lolz0r/Williams-WPC-Power-Driver-Board-A-12697-3/variants/jlcpcb/docs/PCBWAY_REPLY_DRAFT.md

# Draft reply — not sent

Use this for the revision and BOM actually supplied to PCBWay; JLC-2 is a separate electronics-sourcing revision.

> Understood. Once the PCB and all components arrive, please trial-fit the heatsinks, rectifiers, mounting screws and nearby components before completing assembly. Please check screw passage and engagement, component-to-heatsink clearance, and clearance beneath the board. If anything does not fit freely, please send photos and measurements and hold the affected assembly for review before modifying parts or substituting hardware. We can provide the STEP model and assembly drawings to support the check; final fit still needs to be verified on the actual parts.
