lolz0r/Williams-WPC-Power-Driver-Board-A-12697-3/variants/jlcpcb/docs/RELEASE_STATUS.md

# JLC-2 status

Use the [JLC-2 README](../README.md), [verification report](VERIFICATION.md) and [machine-readable readiness](../output/release-candidate/READINESS.json).

The JLC-2 CAD and manufacturing consistency checks pass, and the flasher-clamp correction is implemented. **Hold an assembled prototype order:** the expanded analog review has unresolved regulator voltage/backfeed findings and lamp-matrix convergence. The [latest addendum](CONTINUED_ANALOG_REVIEW.md) establishes convergence of the selected coil replay, with a separate energy-balance check, and records the unbuilt input-isolation candidate. The [previous report](PRESPIN_VERIFICATION.md) retains earlier results and failures. This is an engineering review candidate; software verification is not an unconditional pass.

Physical cabinet/harness clearance, loaded thermal/fault tests, procurement and fabricator/assembly DFM remain open. Fabrication-file consistency does not establish electrical readiness.

Documents under `baseline/` describe the parent revision and are not current release evidence.
