lolz0r/Williams-WPC-Power-Driver-Board-A-12697-3/.scratch/thermal/crop_br3.png

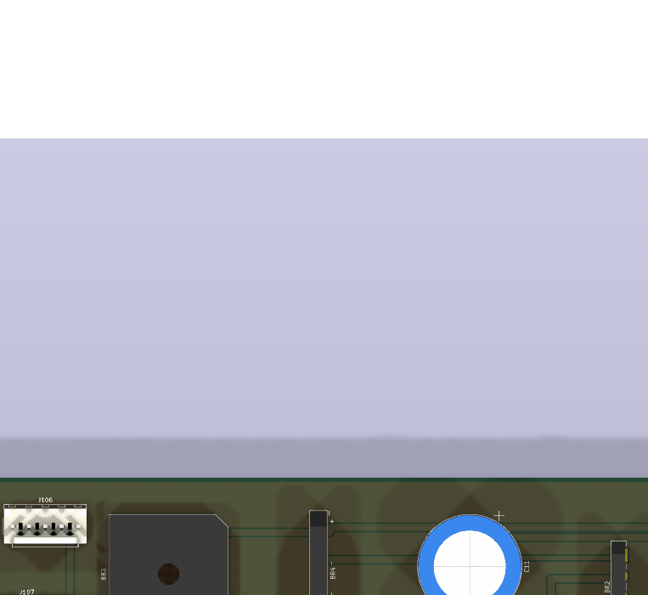
.scratch/thermal/crop_br3.png
