lolz0r/Williams-WPC-Power-Driver-Board-A-12697-3/.scratch/thermal/crop_q18.png

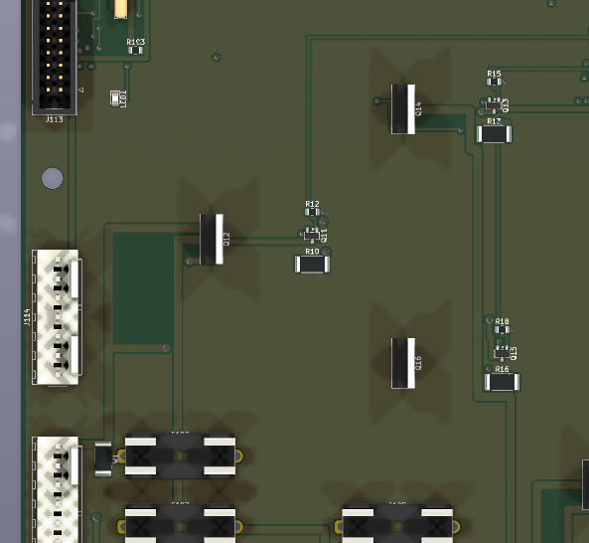
.scratch/thermal/crop_q18.png
