lolz0r/Williams-WPC-Power-Driver-Board-A-12697-3/.scratch/thermal/d_5840.png

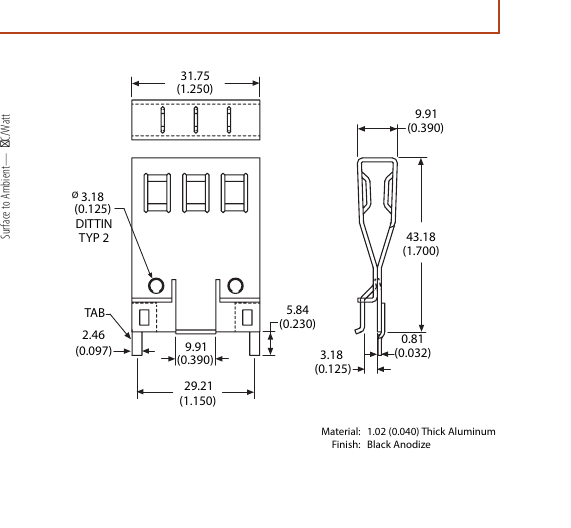
.scratch/thermal/d_5840.png
