lolz0r/Williams-WPC-Power-Driver-Board-A-12697-3/.scratch/thermal/hi_p29-029.png

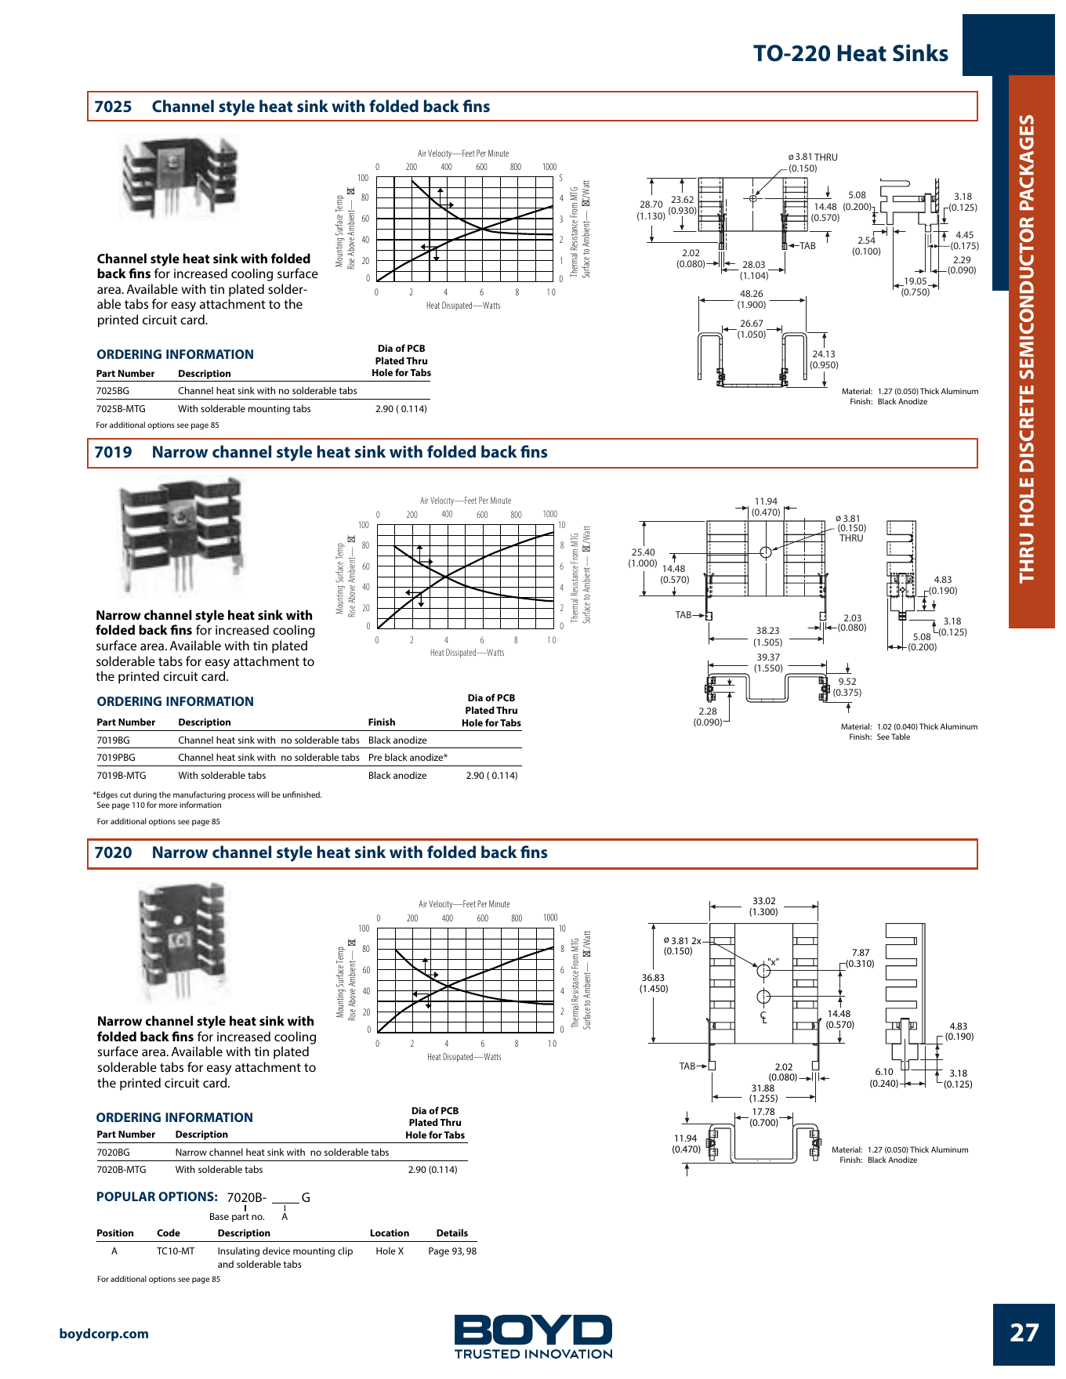
.scratch/thermal/hi_p29-029.png
