lolz0r/Williams-WPC-Power-Driver-Board-A-12697-3/.scratch/thermal/m100s_rth-04.png

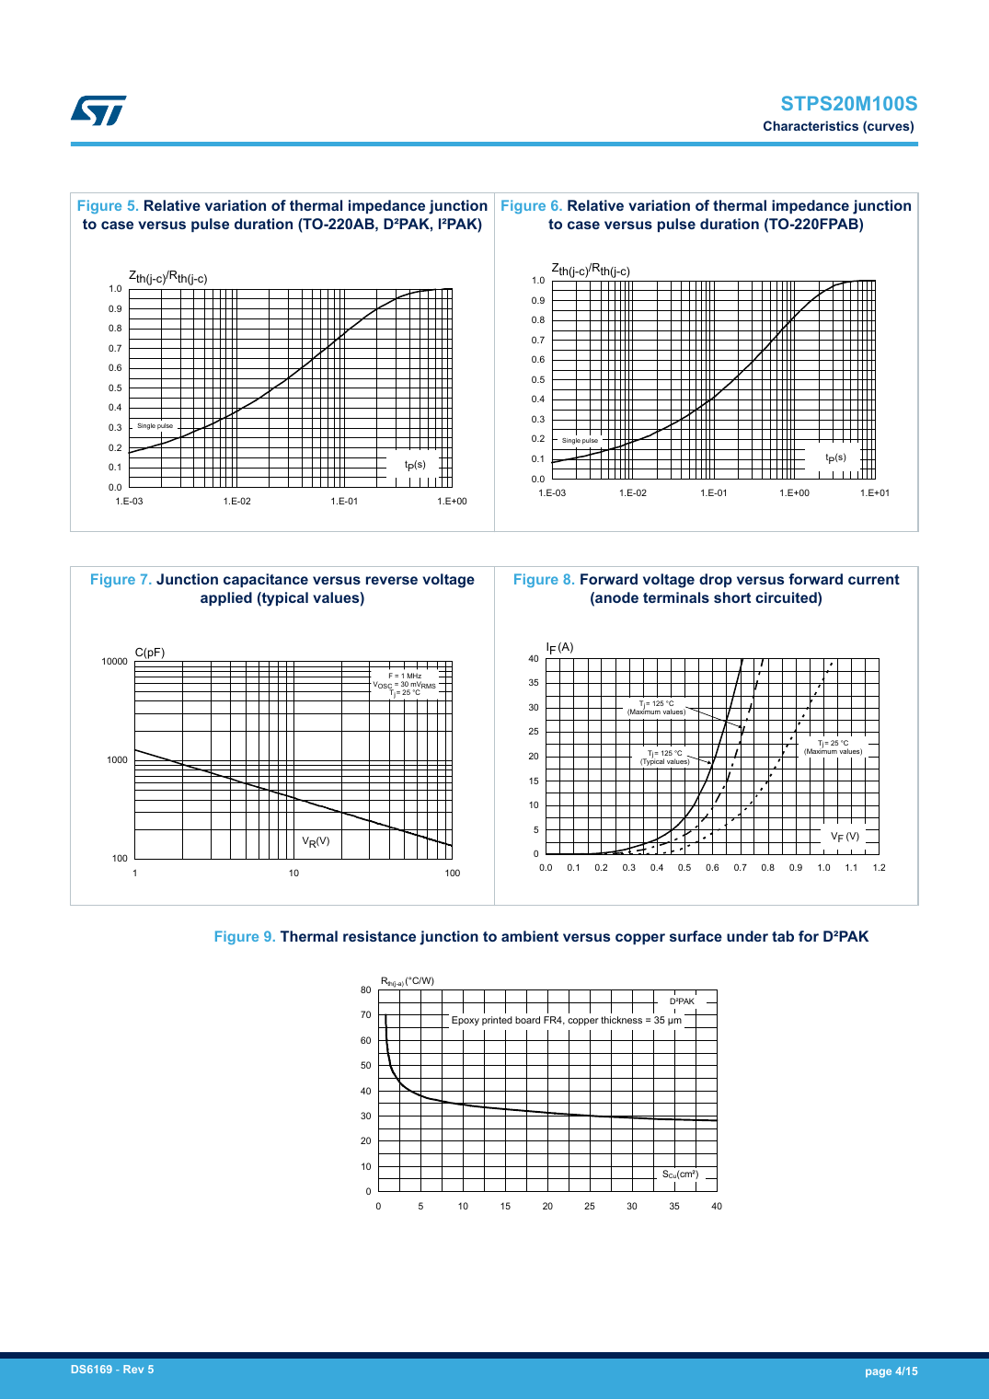
.scratch/thermal/m100s_rth-04.png
