lolz0r/Williams-WPC-Power-Driver-Board-A-12697-3/.scratch/thermal/pg_6222BG-079.png

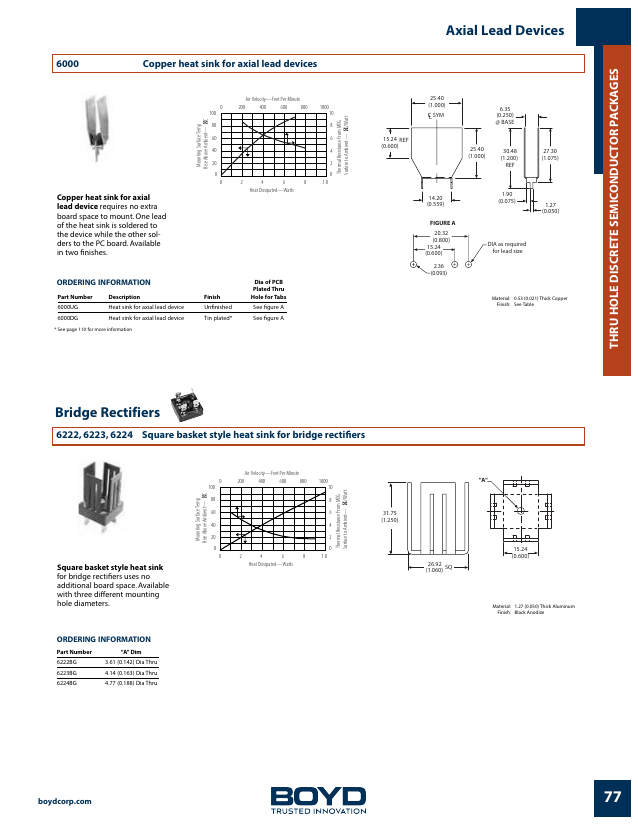
.scratch/thermal/pg_6222BG-079.png
