lolz0r/Williams-WPC-Power-Driver-Board-A-12697-3/.scratch/thermal/st_fig9-05.png

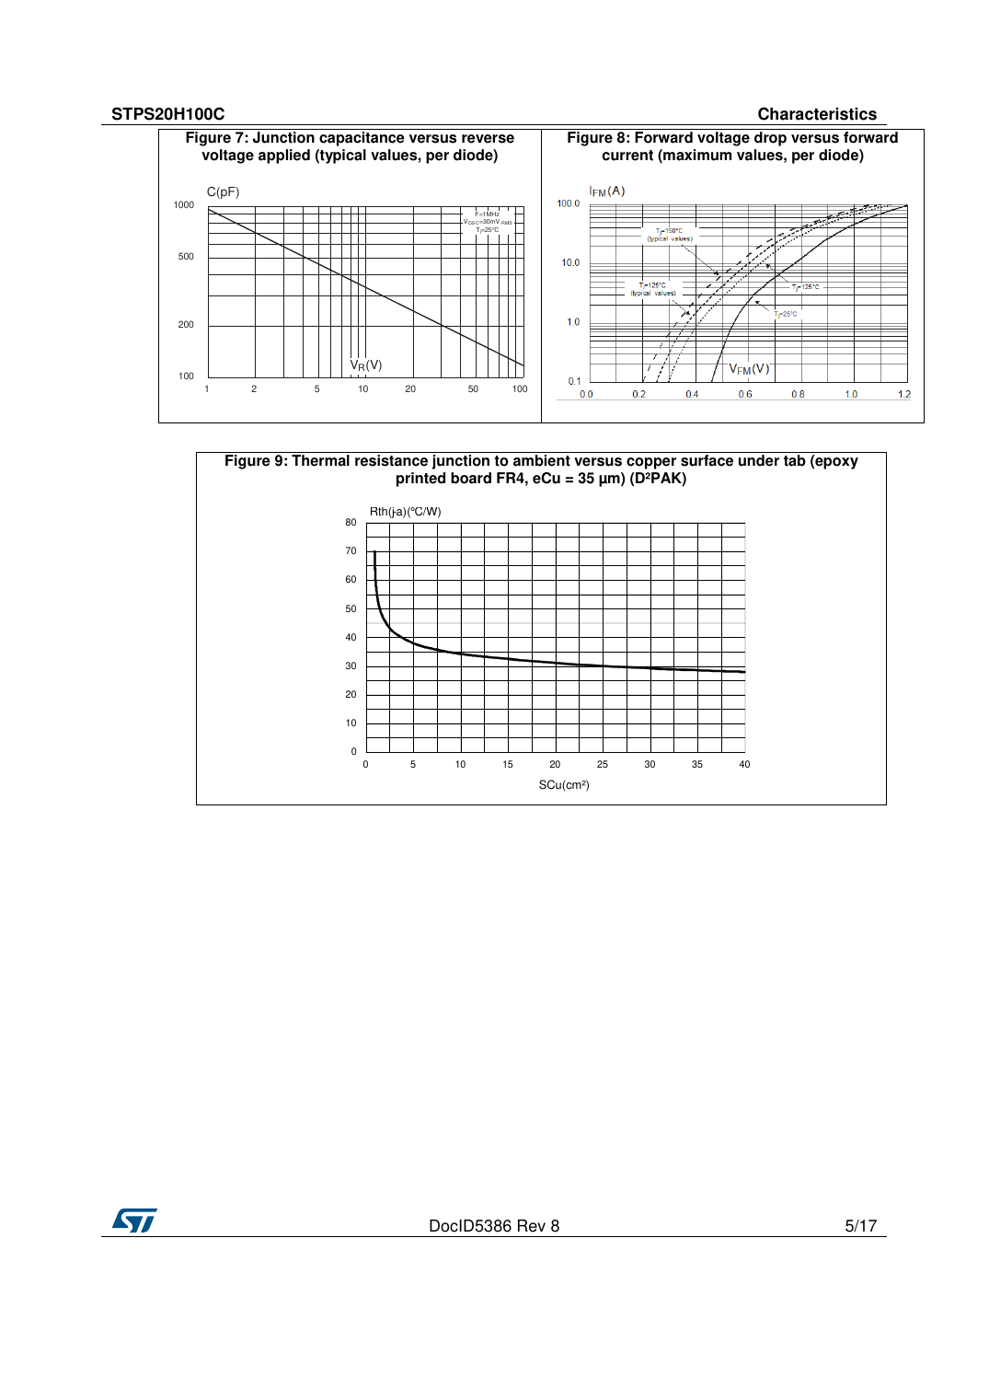
.scratch/thermal/st_fig9-05.png
