lolz0r/Williams-WPC-Power-Driver-Board-A-12697-3/variants/jlcpcb-100/output/release-candidate/3d/bottom.png

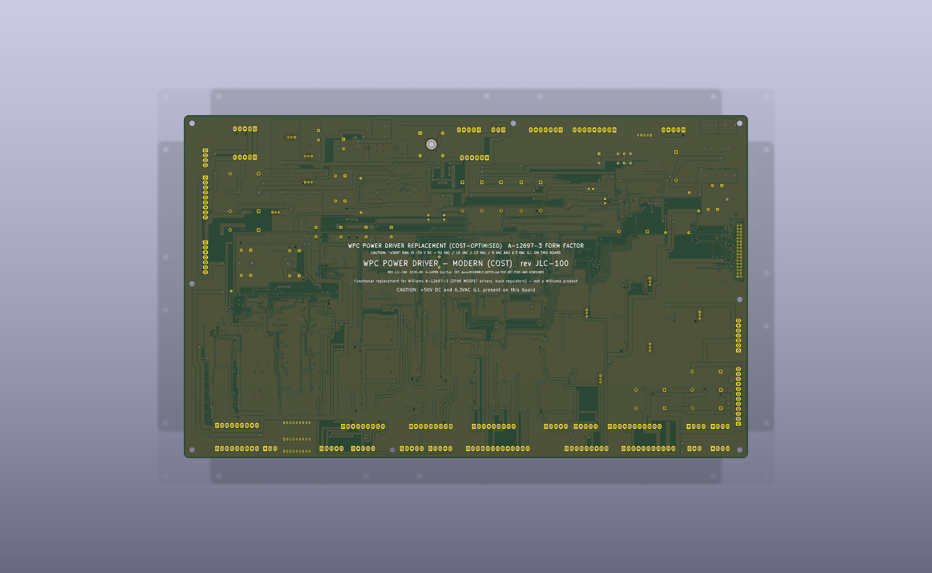
variants/jlcpcb-100/output/release-candidate/3d/bottom.png
