lolz0r/Williams-WPC-Power-Driver-Board-A-12697-3/variants/jlcpcb/research/Boyd-8.png

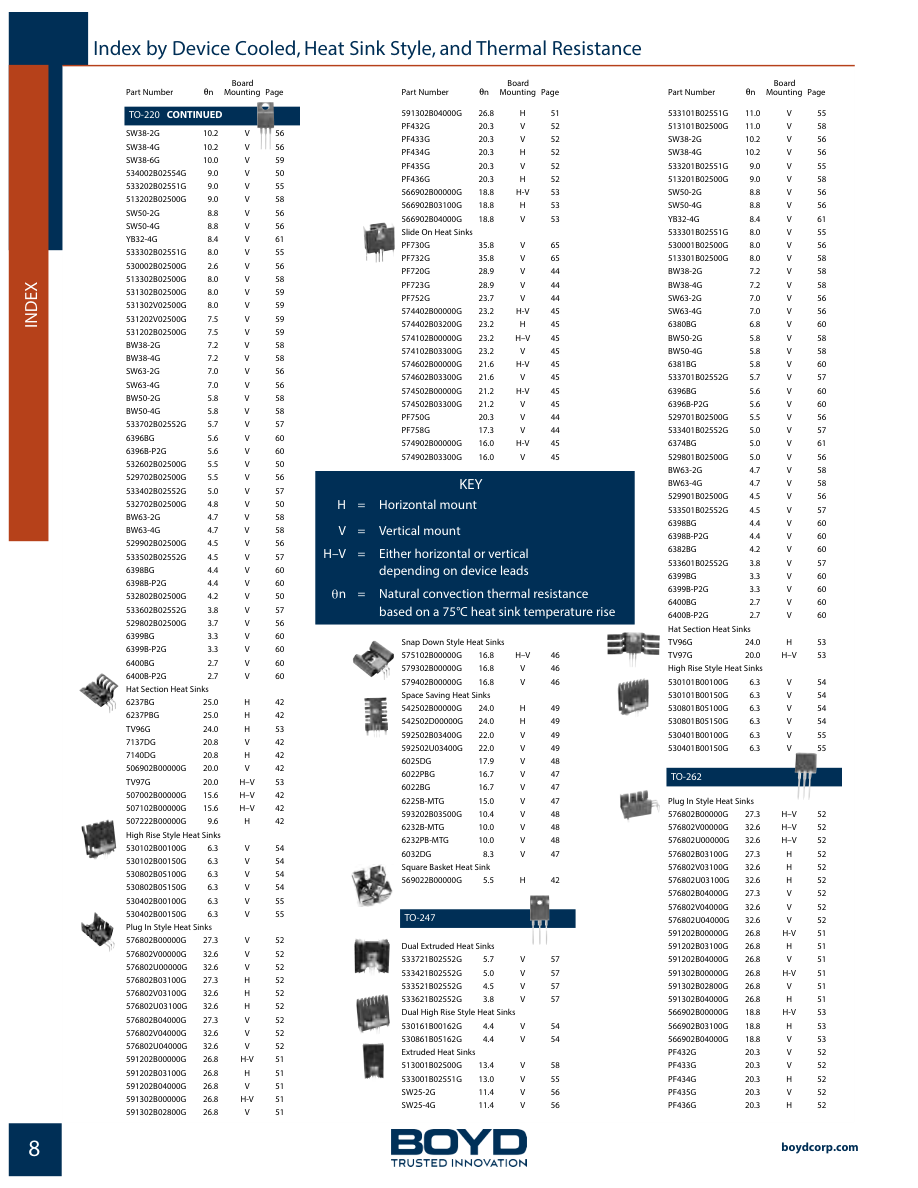
variants/jlcpcb/research/Boyd-8.png
