lolz0r/Williams-WPC-Power-Driver-Board-A-12697-3/variants/jlcpcb/research/C4697.png

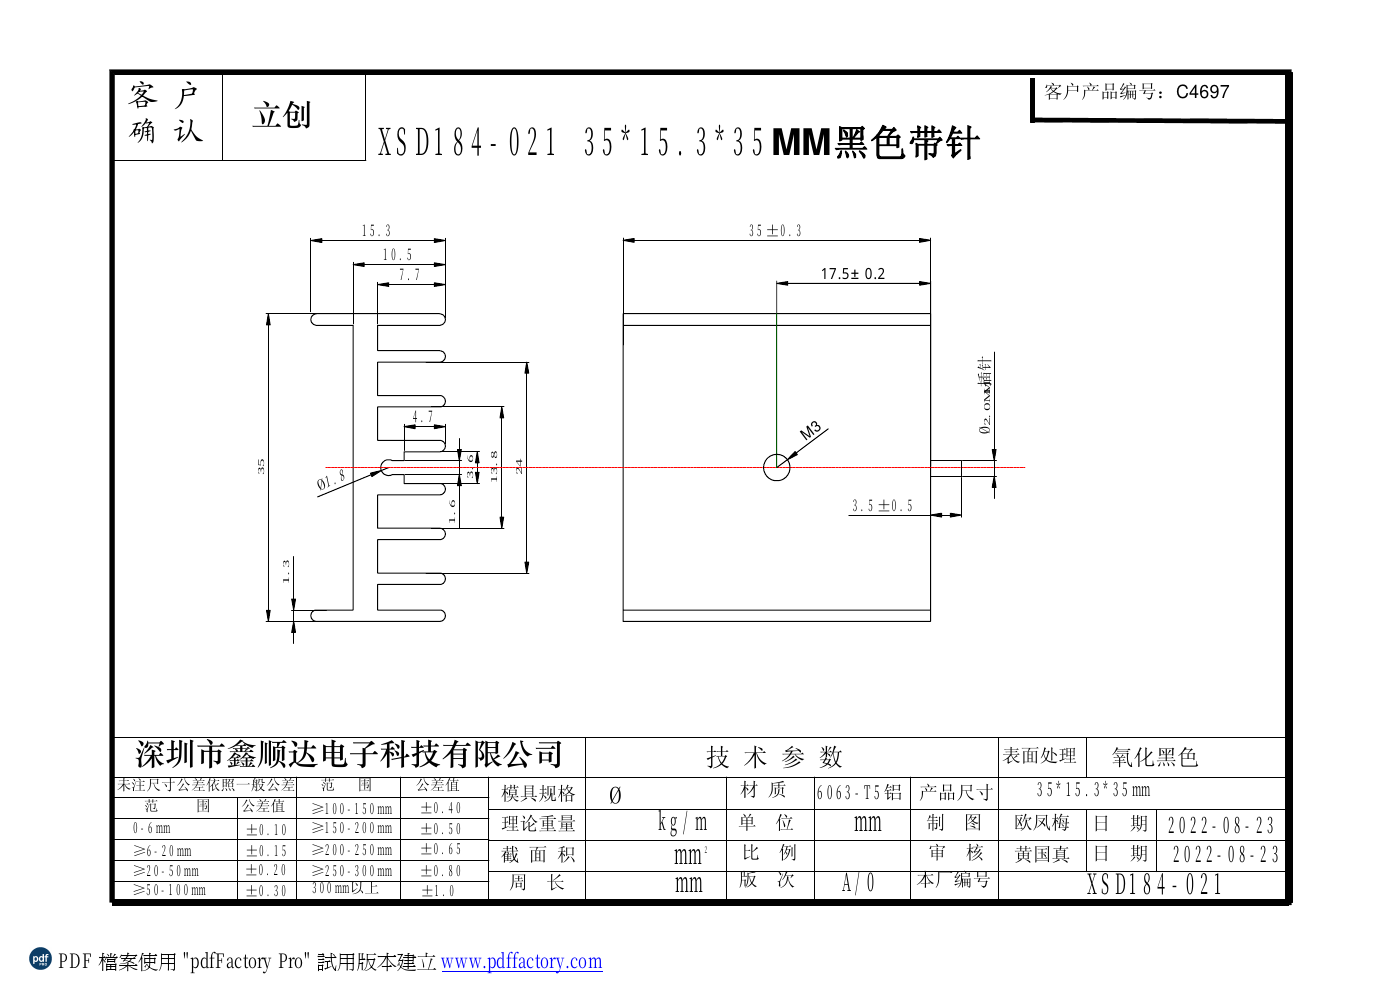
variants/jlcpcb/research/C4697.png
