lolz0r/Williams-WPC-Power-Driver-Board-A-12697-3/output/3d/wpc_power_driver_cost-perspective-4k.png

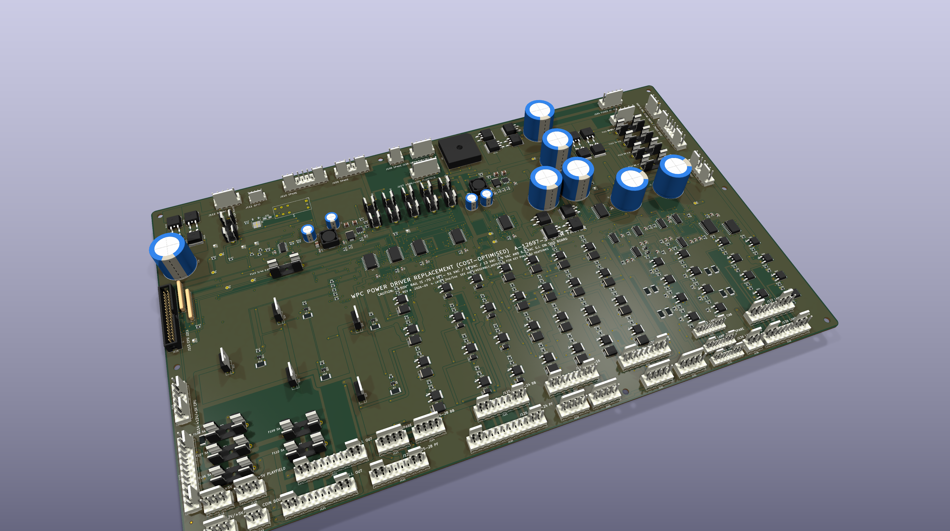
output/3d/wpc_power_driver_cost-perspective-4k.png
