lolz0r/Williams-WPC-Power-Driver-Board-A-12697-3/variants/jlcpcb/output/release-candidate/cad/models/Bourns_SRP1265A_envelope.step

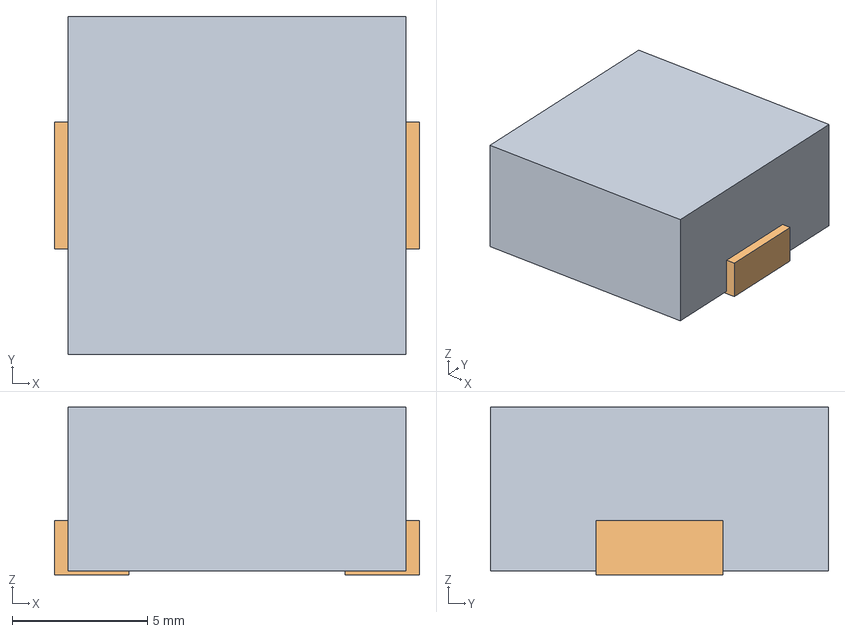
[picture p56: CAD file, 2026-09-09]
variants/jlcpcb/output/release-candidate/cad/models/Bourns_SRP1265A_envelope.step
13.5 x 12.5 x 6.20 mm
