lolz0r/Williams-WPC-Power-Driver-Board-A-12697-3/variants/jlcpcb-100/models/inventory/TE_J133.step

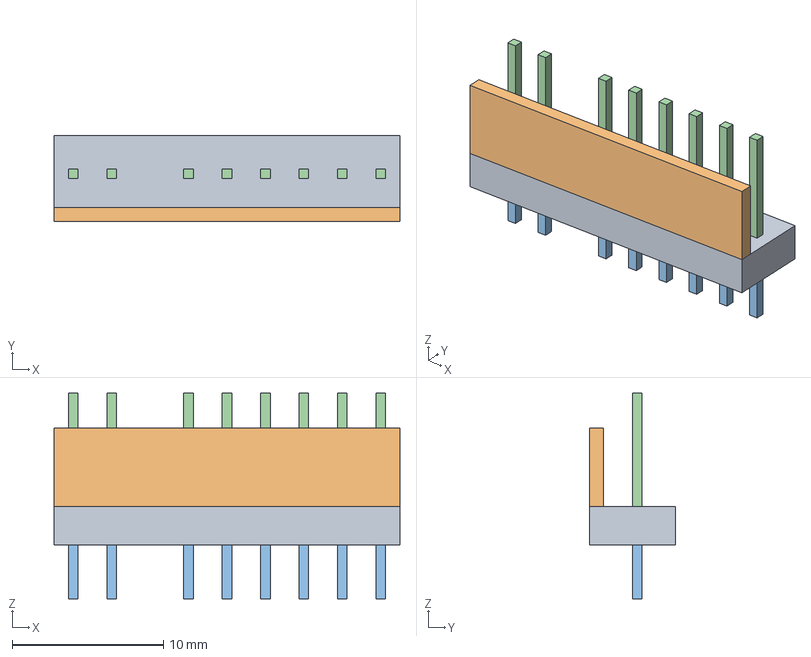
[picture p57: CAD file, 2026-09-14]
variants/jlcpcb-100/models/inventory/TE_J133.step
22.9 x 5.71 x 13.6 mm
