lolz0r/Williams-WPC-Power-Driver-Board-A-12697-3/variants/jlcpcb-100/output/release-candidate/cad/models/inventory/TE_J120.step

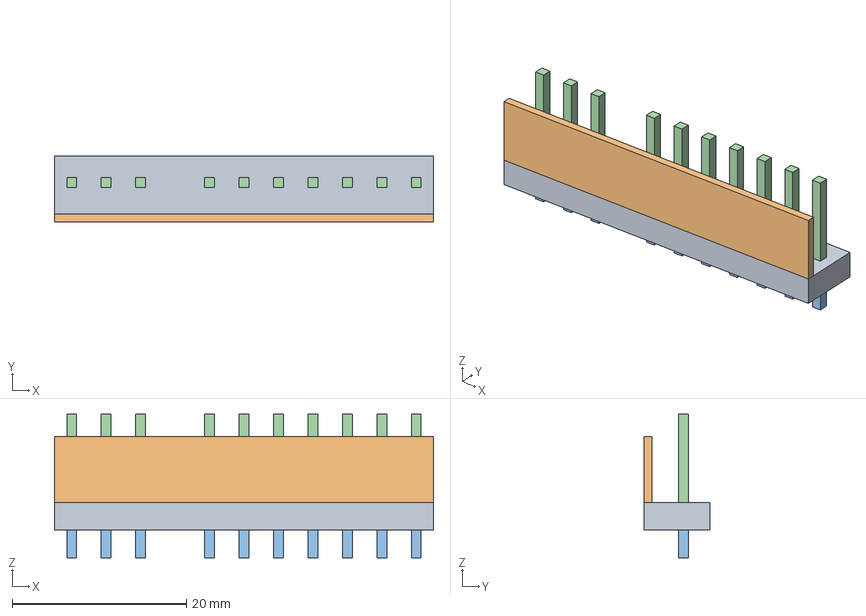
[picture p58: CAD file, 2026-09-14]
variants/jlcpcb-100/output/release-candidate/cad/models/inventory/TE_J120.step
43.6 x 7.62 x 16.5 mm
