lolz0r/Williams-WPC-Power-Driver-Board-A-12697-3/variants/jlcpcb-100/output/release-candidate/cad/models/Molex_KK396_04_envelope_key01.step

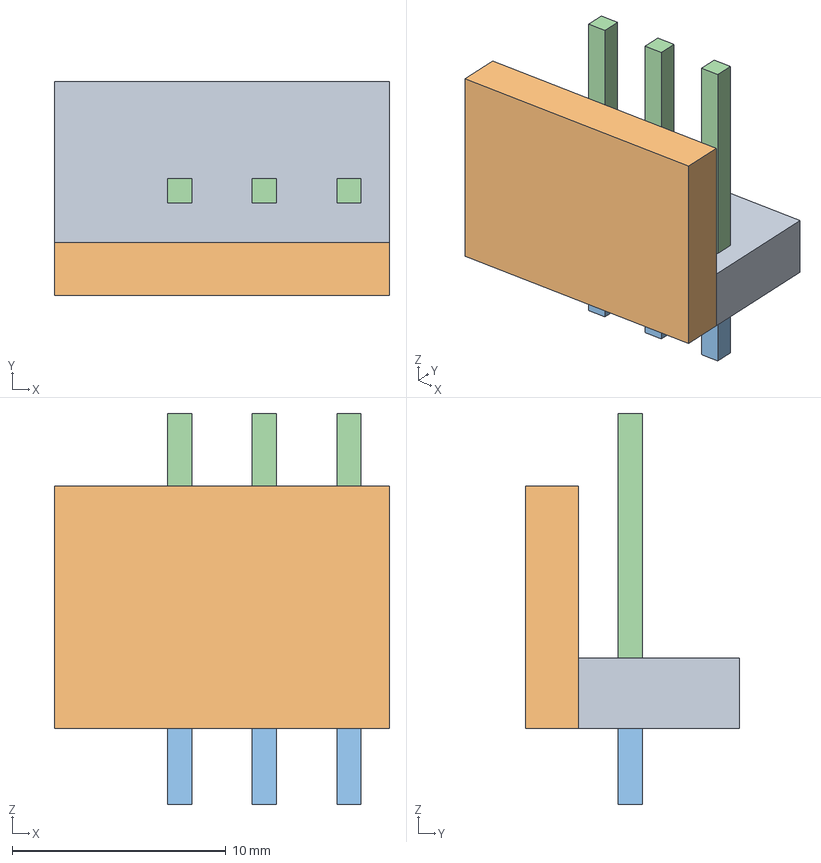
[picture p59: CAD file, 2026-09-14]
variants/jlcpcb-100/output/release-candidate/cad/models/Molex_KK396_04_envelope_key01.step
15.7 x 10.0 x 18.3 mm
