lolz0r/Williams-WPC-Power-Driver-Board-A-12697-3/variants/jlcpcb/output/release-candidate/cad/models/Molex_KK396_07_envelope_key06.step

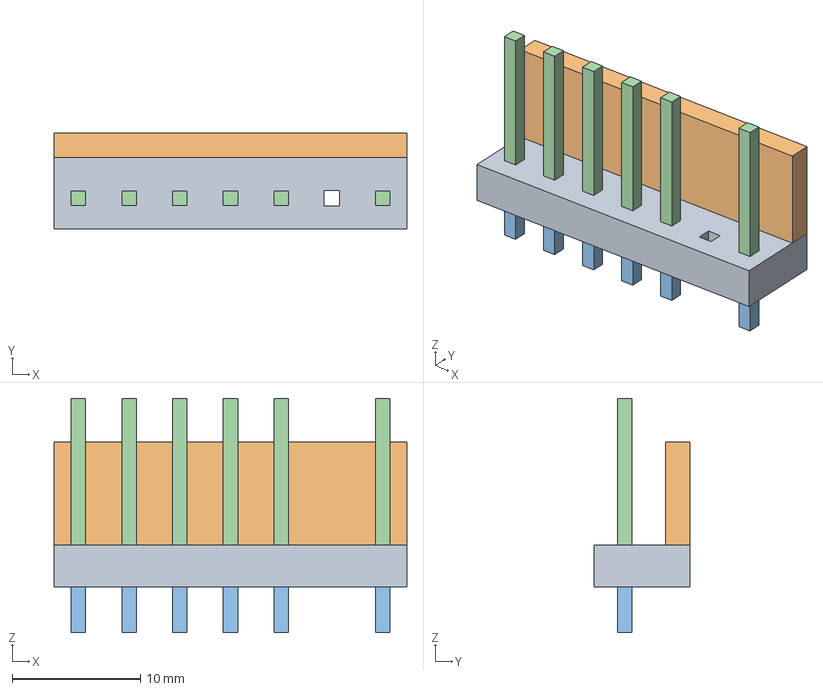
[picture p60: CAD file, 2026-09-09]
variants/jlcpcb/output/release-candidate/cad/models/Molex_KK396_07_envelope_key06.step
27.6 x 7.52 x 18.3 mm
