lolz0r/Williams-WPC-Power-Driver-Board-A-12697-3/variants/jlcpcb-100/models/inventory/Boyd_6223_on_GBPC2506W.step

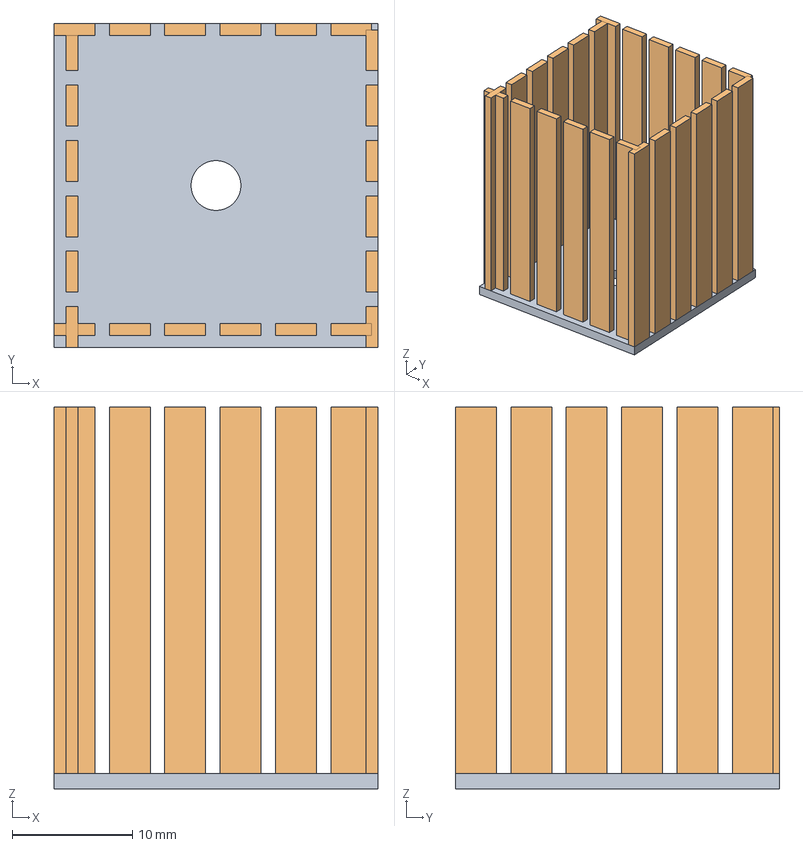
[picture p61: CAD file, 2026-09-14]
variants/jlcpcb-100/models/inventory/Boyd_6223_on_GBPC2506W.step
26.9 x 26.9 x 31.8 mm
