lolz0r/Williams-WPC-Power-Driver-Board-A-12697-3/variants/jlcpcb-100/models/Molex_KK396_03_envelope_key01.step

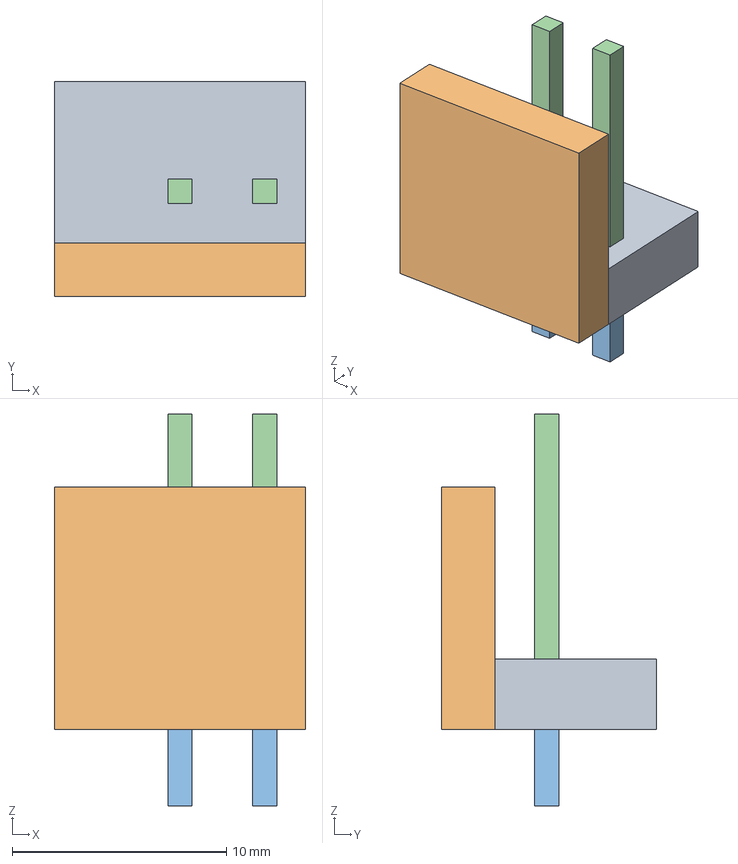
[picture p62: CAD file, 2026-09-14]
variants/jlcpcb-100/models/Molex_KK396_03_envelope_key01.step
11.7 x 10.0 x 18.3 mm
