lolz0r/Williams-WPC-Power-Driver-Board-A-12697-3/variants/jlcpcb-100/output/release-candidate/cad/research/jlc-placement-libraries/C7948-supplier.obj

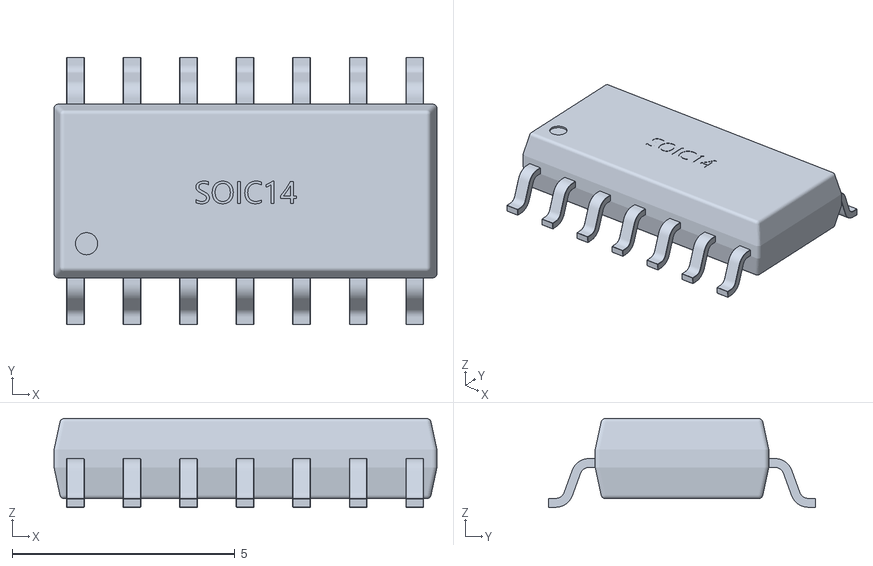
[picture p63: CAD file, 2026-09-14]
variants/jlcpcb-100/output/release-candidate/cad/research/jlc-placement-libraries/C7948-supplier.obj
8.60 x 6.01 x 2.00
