lolz0r/Williams-WPC-Power-Driver-Board-A-12697-3/variants/jlcpcb/output/release-candidate/cad/models/Boyd_5772_simplified.step

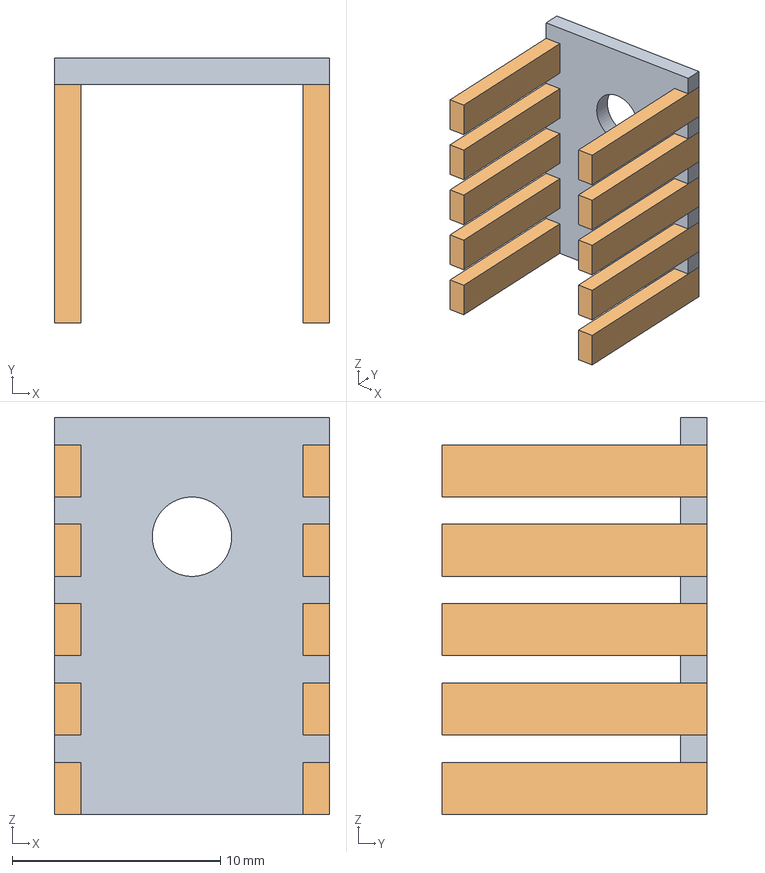
[picture p65: CAD file, 2026-09-09]
variants/jlcpcb/output/release-candidate/cad/models/Boyd_5772_simplified.step
13.2 x 12.7 x 19.1 mm
