lolz0r/Williams-WPC-Power-Driver-Board-A-12697-3/variants/jlcpcb-100/research/jlc-placement-libraries/C6772-supplier.obj

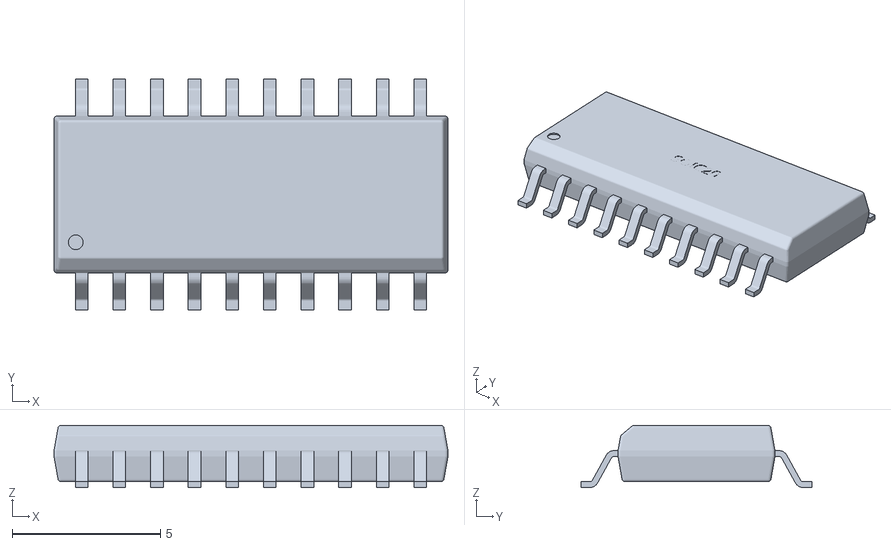
[picture p66: CAD file, 2026-09-14]
variants/jlcpcb-100/research/jlc-placement-libraries/C6772-supplier.obj
13.3 x 7.80 x 2.10
