lolz0r/Williams-WPC-Power-Driver-Board-A-12697-3/variants/jlcpcb-100/research/jlc-placement-libraries/C2624-supplier.obj

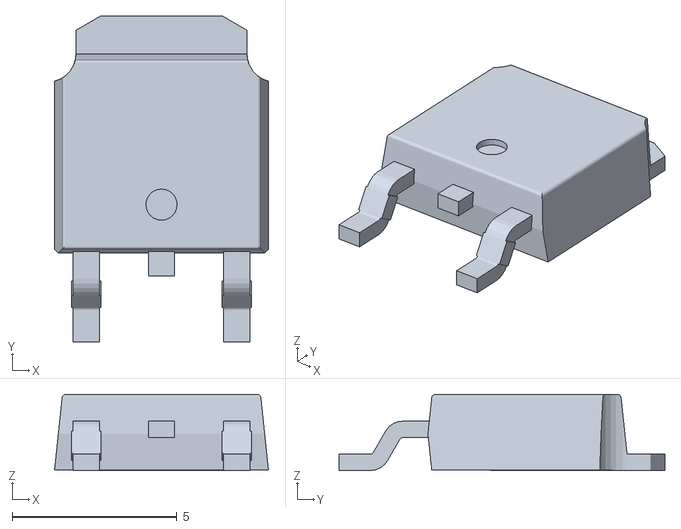
[picture p67: CAD file, 2026-09-14]
variants/jlcpcb-100/research/jlc-placement-libraries/C2624-supplier.obj
6.50 x 9.90 x 2.31
