lolz0r/Williams-WPC-Power-Driver-Board-A-12697-3/variants/jlcpcb/output/release-candidate/cad/models/Molex_KK396_04_envelope.step

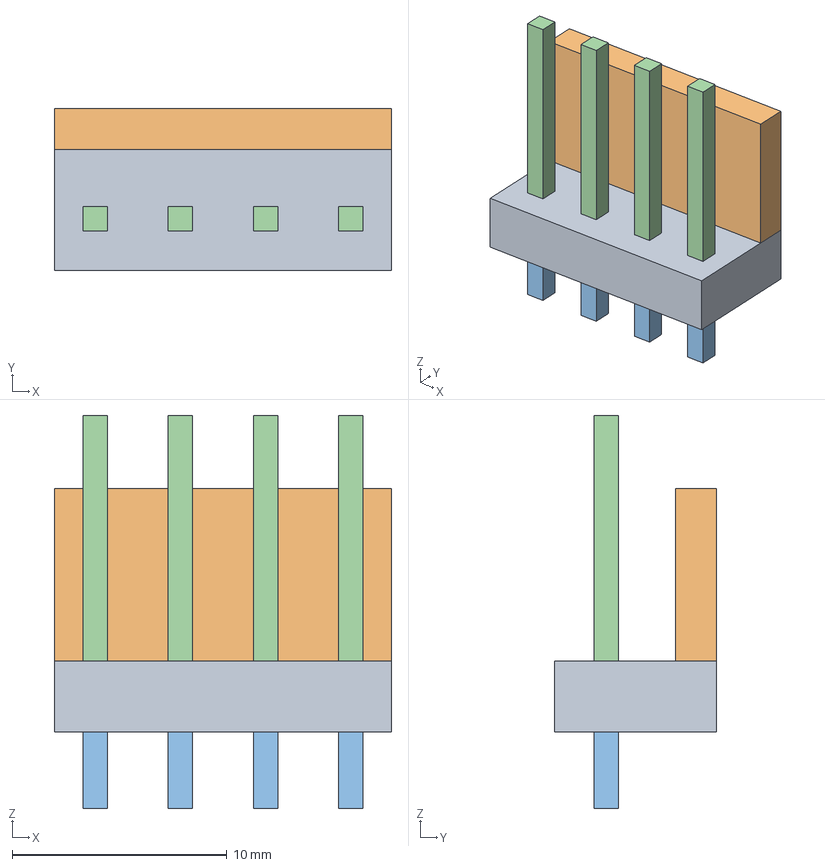
[picture p68: CAD file, 2026-09-09]
variants/jlcpcb/output/release-candidate/cad/models/Molex_KK396_04_envelope.step
15.7 x 7.52 x 18.3 mm
