lolz0r/Williams-WPC-Power-Driver-Board-A-12697-3/variants/jlcpcb-100/models/inventory/ONSEMI_GBPC2506W_formed.step

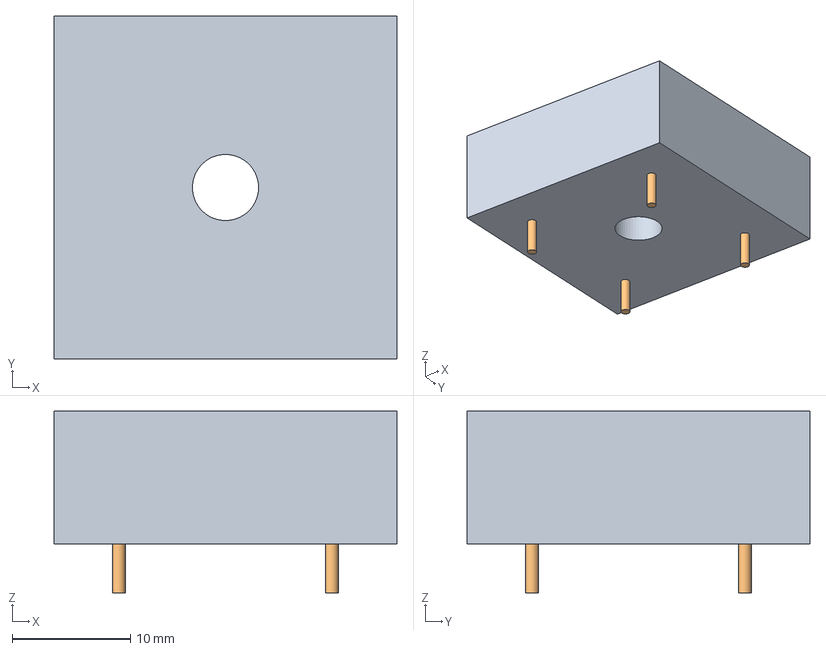
[picture p69: CAD file, 2026-09-14]
variants/jlcpcb-100/models/inventory/ONSEMI_GBPC2506W_formed.step
29.0 x 29.0 x 15.3 mm
