lolz0r/Williams-WPC-Power-Driver-Board-A-12697-3/variants/jlcpcb-100/output/release-candidate/cad/models/inventory/TE_J126.step

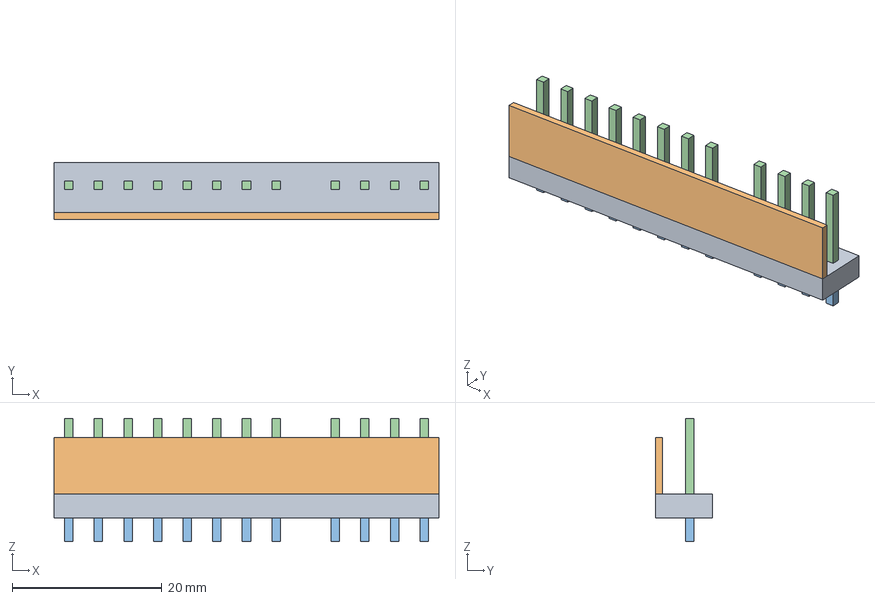
[picture p70: CAD file, 2026-09-14]
variants/jlcpcb-100/output/release-candidate/cad/models/inventory/TE_J126.step
51.5 x 7.62 x 16.5 mm
