lolz0r/Williams-WPC-Power-Driver-Board-A-12697-3/variants/jlcpcb-100/research/jlc-placement-libraries/C3007-supplier.obj

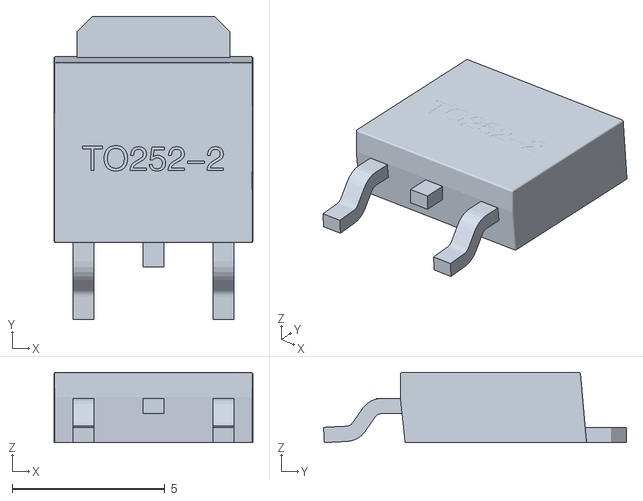
[picture p71: CAD file, 2026-09-14]
variants/jlcpcb-100/research/jlc-placement-libraries/C3007-supplier.obj
6.50 x 9.92 x 2.30
