lolz0r/Williams-WPC-Power-Driver-Board-A-12697-3/variants/jlcpcb/output/release-candidate/cad/models/Rubycon_USC_25x35_envelope.step

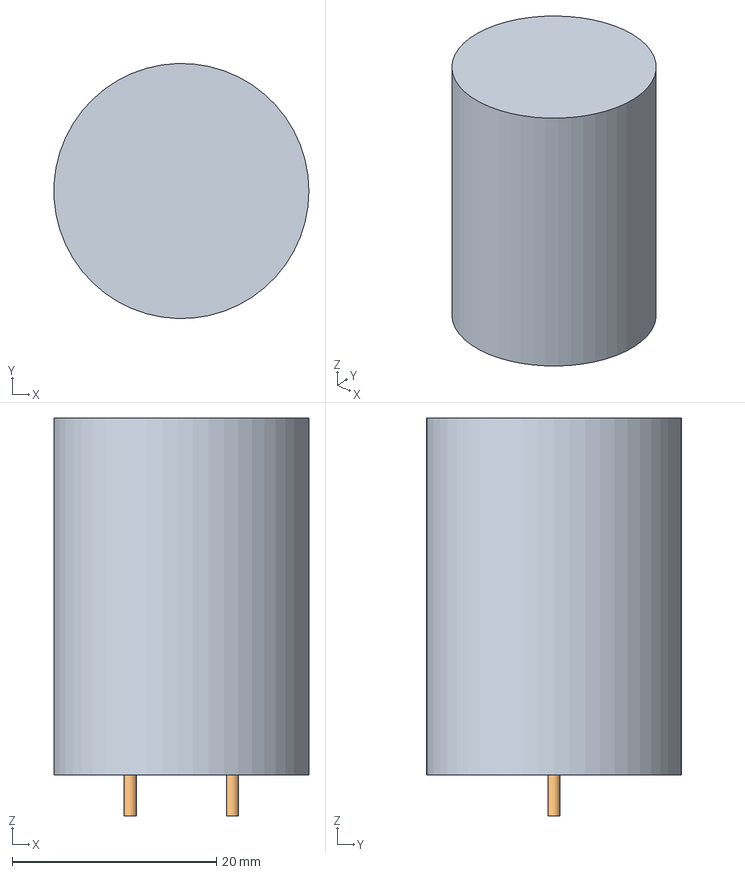
[picture p72: CAD file, 2026-09-09]
variants/jlcpcb/output/release-candidate/cad/models/Rubycon_USC_25x35_envelope.step
25.0 x 25.0 x 39.0 mm
