lolz0r/Williams-WPC-Power-Driver-Board-A-12697-3/variants/jlcpcb/output/release-candidate/cad/models/Molex_KK396_11_envelope.step

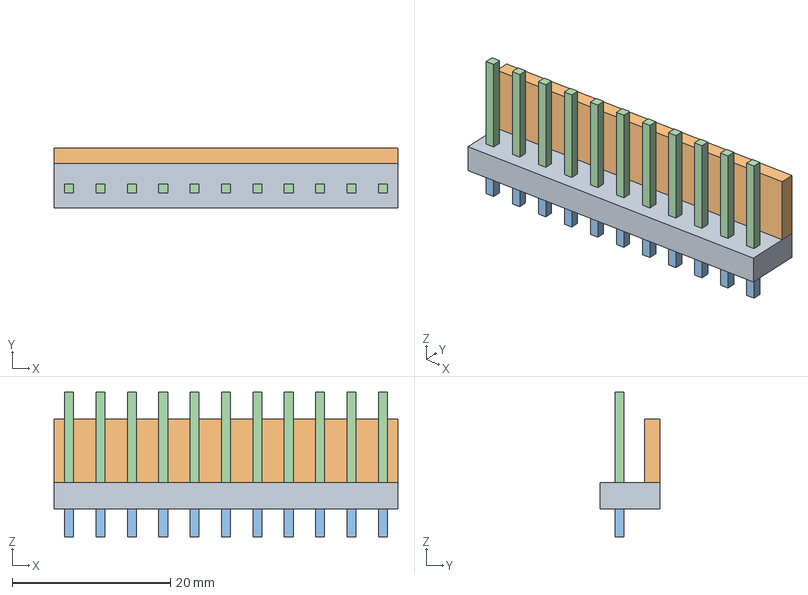
[picture p73: CAD file, 2026-09-09]
variants/jlcpcb/output/release-candidate/cad/models/Molex_KK396_11_envelope.step
43.4 x 7.52 x 18.3 mm
