lolz0r/Williams-WPC-Power-Driver-Board-A-12697-3/variants/jlcpcb-100/models/inventory/XFCN_EH254V_12_34P_envelope.step

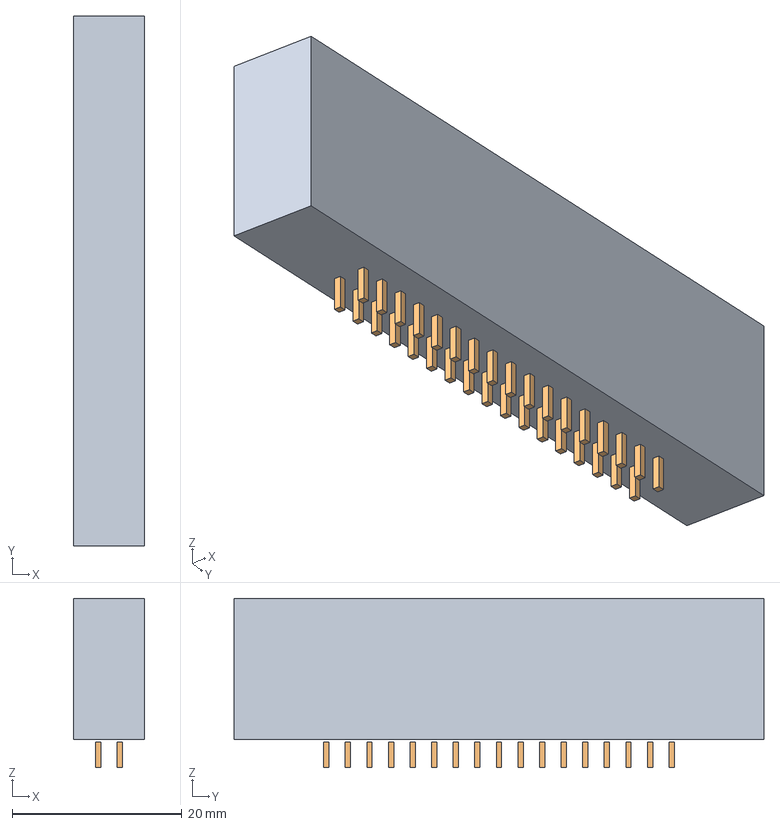
[picture p74: CAD file, 2026-09-14]
variants/jlcpcb-100/models/inventory/XFCN_EH254V_12_34P_envelope.step
8.30 x 62.4 x 19.9 mm
