lolz0r/Williams-WPC-Power-Driver-Board-A-12697-3/variants/jlcpcb/output/release-candidate/cad/models/TDK_B41252_25p4x45_envelope.step

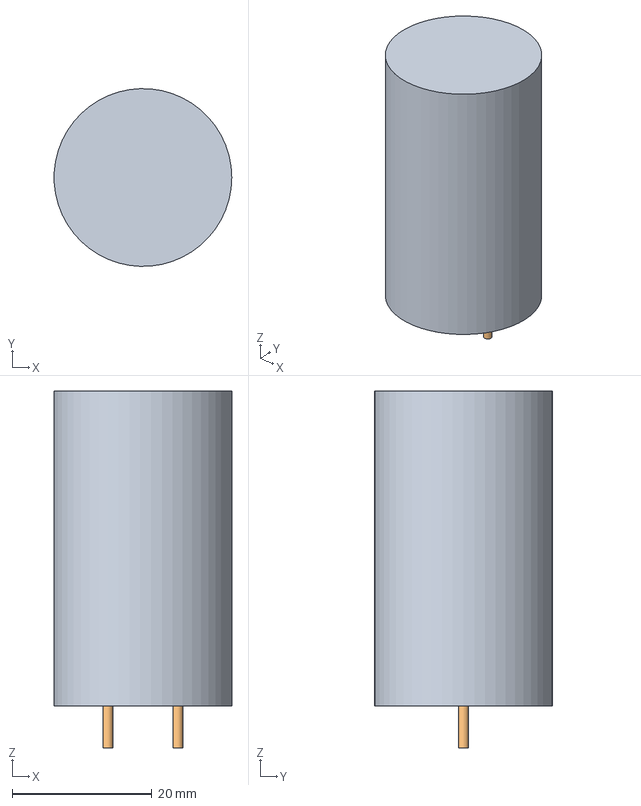
[picture p75: CAD file, 2026-09-09]
variants/jlcpcb/output/release-candidate/cad/models/TDK_B41252_25p4x45_envelope.step
25.4 x 25.4 x 51.0 mm
