lolz0r/Williams-WPC-Power-Driver-Board-A-12697-3/variants/jlcpcb-100/models/Boyd_7019_simplified.step

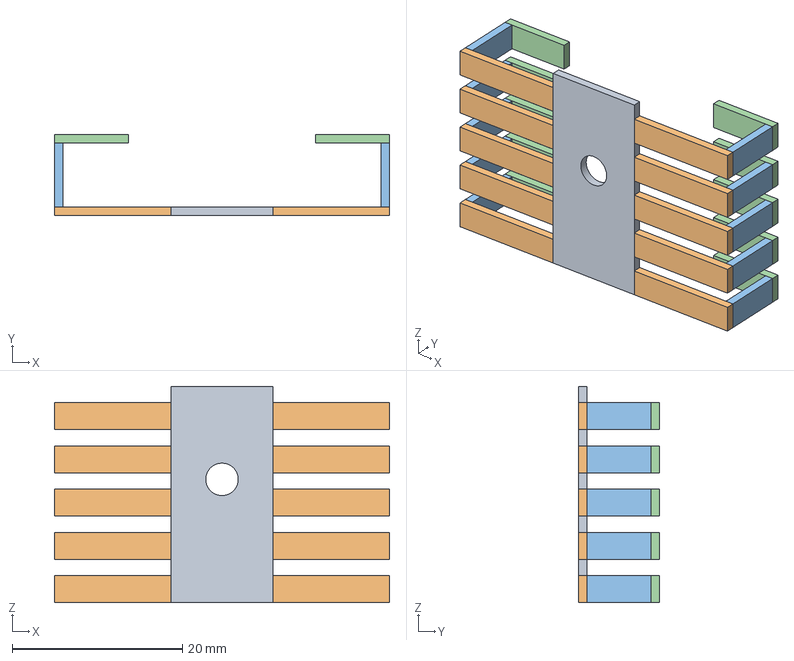
[picture p76: CAD file, 2026-09-09]
variants/jlcpcb-100/models/Boyd_7019_simplified.step
39.4 x 9.52 x 25.4 mm
