lolz0r/Williams-WPC-Power-Driver-Board-A-12697-3/variants/jlcpcb-100/output/release-candidate/cad/models/inventory/HONGJU_FH1_200CK_G.step

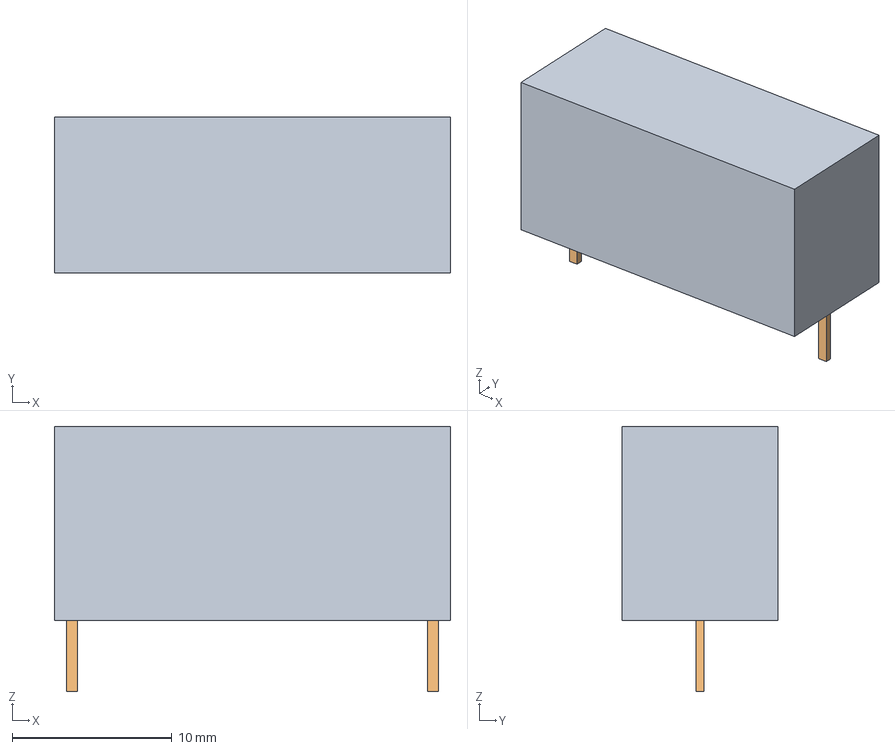
[picture p77: CAD file, 2026-09-14]
variants/jlcpcb-100/output/release-candidate/cad/models/inventory/HONGJU_FH1_200CK_G.step
24.8 x 9.80 x 16.6 mm
