lolz0r/Williams-WPC-Power-Driver-Board-A-12697-3/variants/jlcpcb-100/output/release-candidate/cad/models/Molex_KK396_09_envelope_key08.step

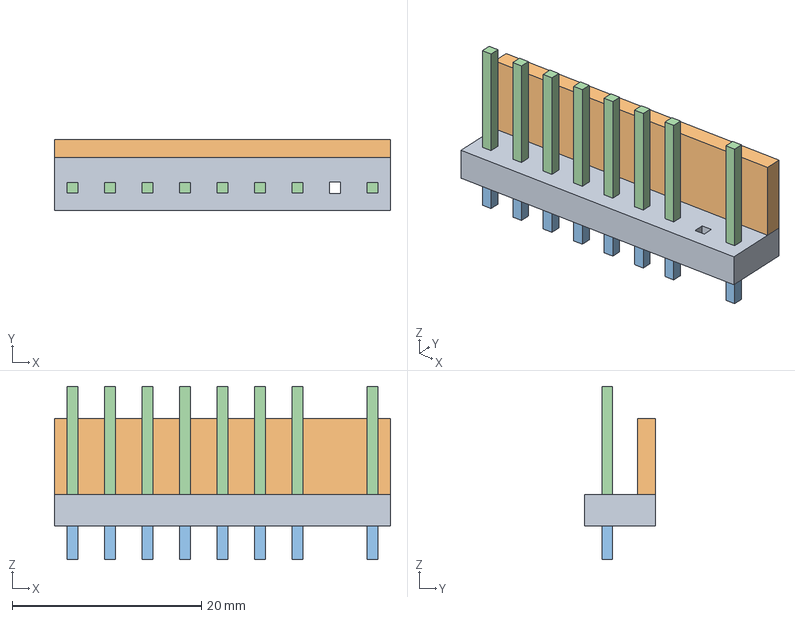
[picture p78: CAD file, 2026-09-09]
variants/jlcpcb-100/output/release-candidate/cad/models/Molex_KK396_09_envelope_key08.step
35.5 x 7.52 x 18.3 mm
