lolz0r/Williams-WPC-Power-Driver-Board-A-12697-3/variants/jlcpcb-100/research/jlc-placement-libraries/C9102-supplier.obj

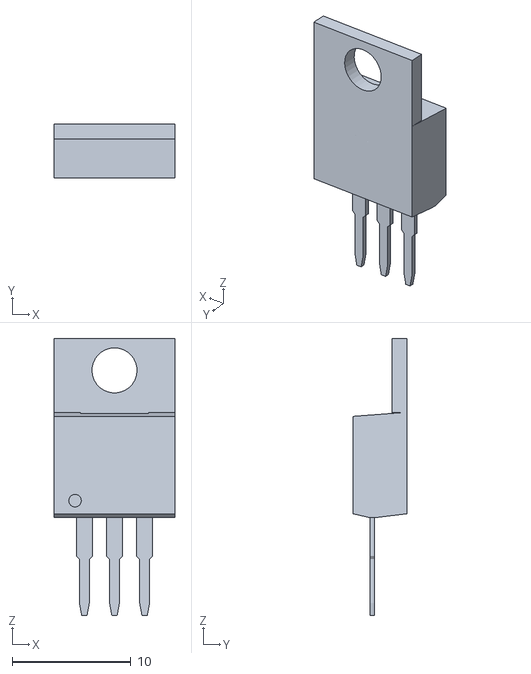
[picture p79: CAD file, 2026-09-14]
variants/jlcpcb-100/research/jlc-placement-libraries/C9102-supplier.obj
10.2 x 4.54 x 23.4
