lolz0r/Williams-WPC-Power-Driver-Board-A-12697-3/variants/jlcpcb/output/release-candidate/cad/models/Boyd_5771_simplified.step

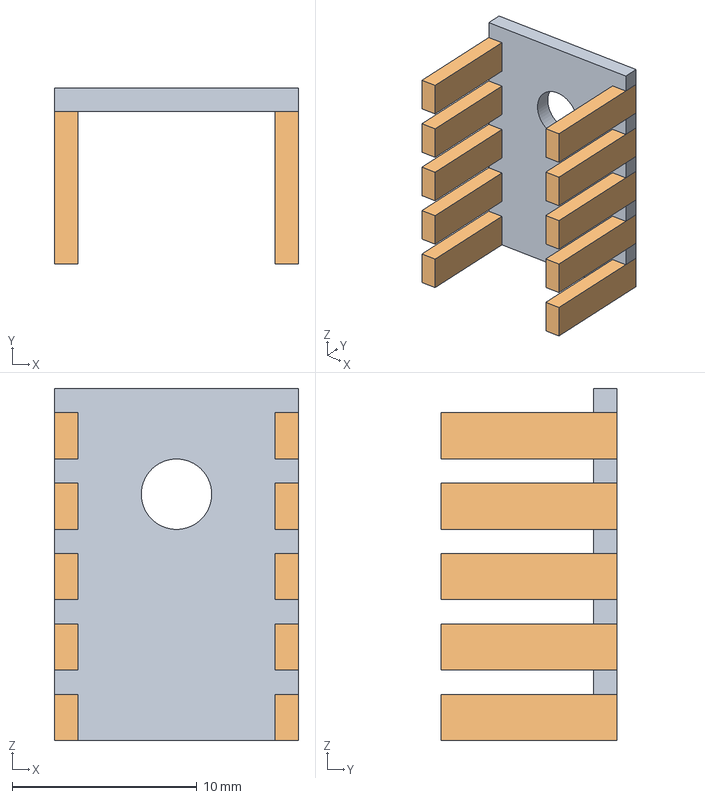
[picture p80: CAD file, 2026-09-09]
variants/jlcpcb/output/release-candidate/cad/models/Boyd_5771_simplified.step
13.2 x 9.52 x 19.1 mm
