lolz0r/Williams-WPC-Power-Driver-Board-A-12697-3/variants/jlcpcb/output/release-candidate/cad/models/Molex_KK396_03_envelope_key02.step

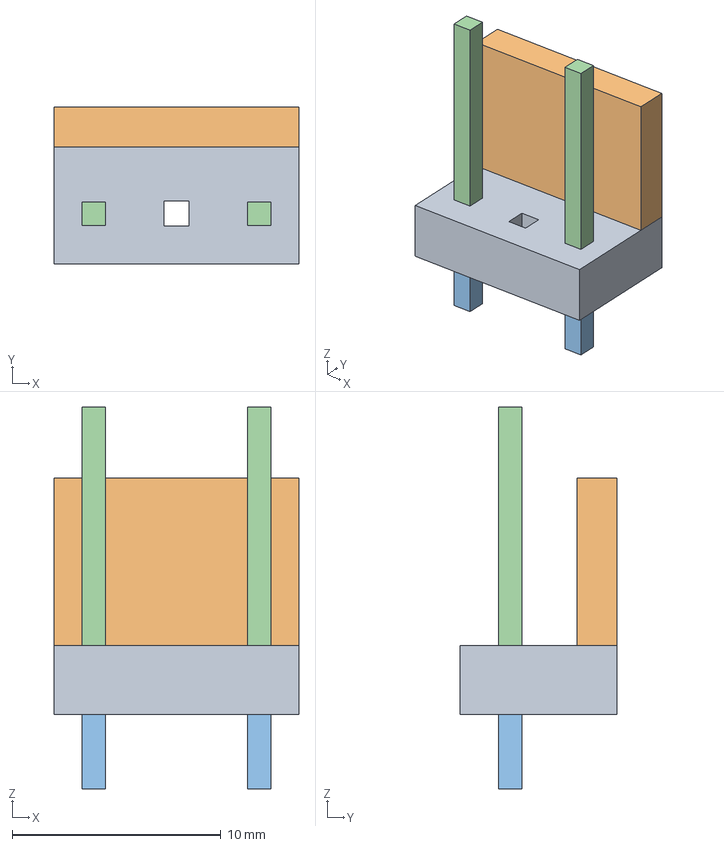
[picture p82: CAD file, 2026-09-09]
variants/jlcpcb/output/release-candidate/cad/models/Molex_KK396_03_envelope_key02.step
11.7 x 7.52 x 18.3 mm
