lolz0r/Williams-WPC-Power-Driver-Board-A-12697-3/variants/jlcpcb-100/models/inventory/TE_J107.step

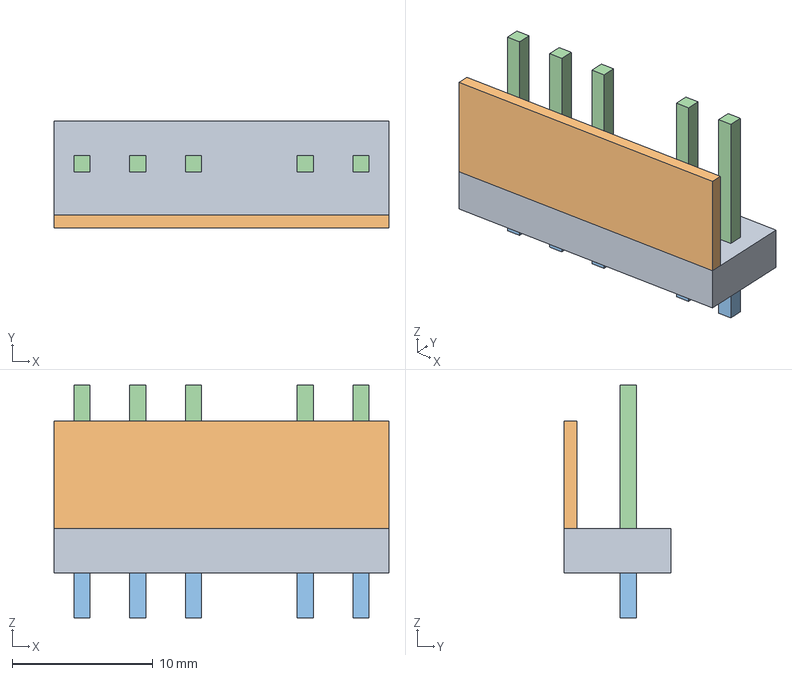
[picture p83: CAD file, 2026-09-14]
variants/jlcpcb-100/models/inventory/TE_J107.step
23.8 x 7.62 x 16.5 mm
