lolz0r/Williams-WPC-Power-Driver-Board-A-12697-3/variants/jlcpcb-100/models/Boyd_6224_simplified.step

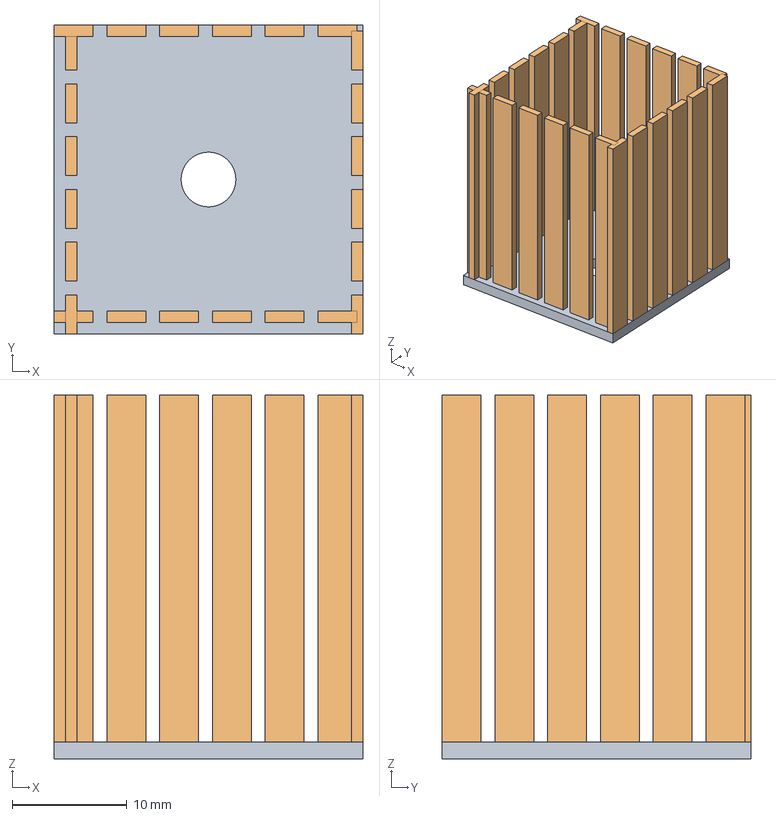
[picture p84: CAD file, 2026-09-09]
variants/jlcpcb-100/models/Boyd_6224_simplified.step
26.9 x 26.9 x 31.8 mm
