lolz0r/Williams-WPC-Power-Driver-Board-A-12697-3/variants/jlcpcb-100/output/release-candidate/cad/models/Molex_KK396_13_envelope_key09.step

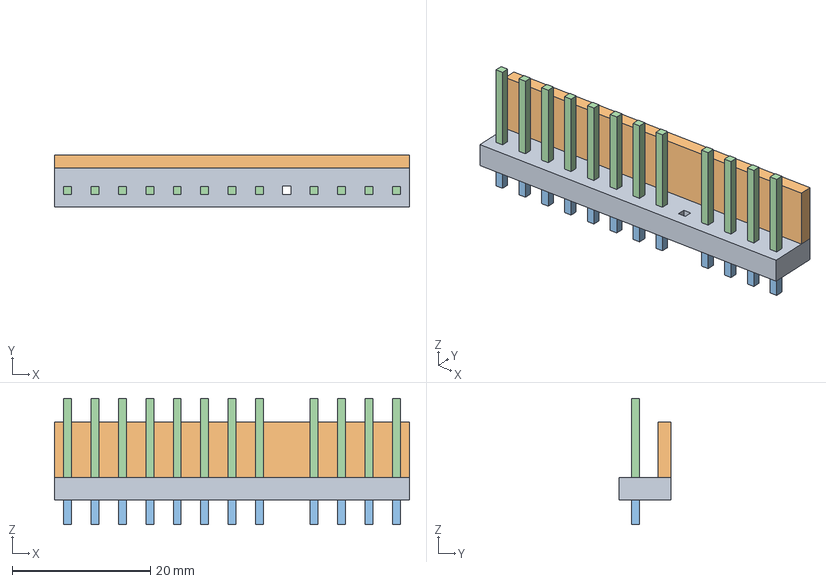
[picture p85: CAD file, 2026-09-09]
variants/jlcpcb-100/output/release-candidate/cad/models/Molex_KK396_13_envelope_key09.step
51.3 x 7.52 x 18.3 mm
