lolz0r/Williams-WPC-Power-Driver-Board-A-12697-3/variants/jlcpcb/output/release-candidate/cad/models/Molex_KK-254_AE-6410-05A_1x05_P2.54mm_Vertical_key04.step

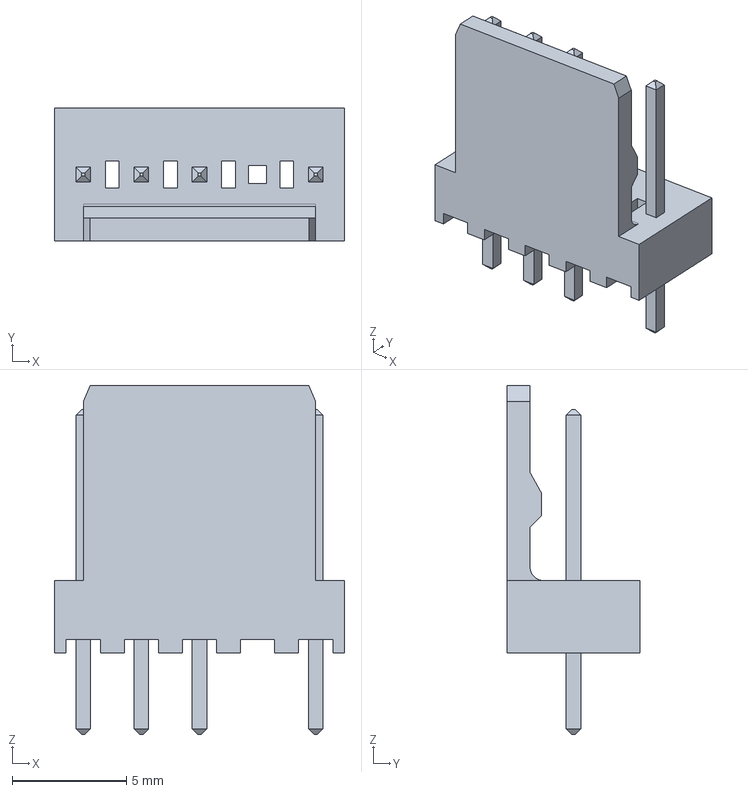
[picture p86: CAD file, 2026-09-09]
variants/jlcpcb/output/release-candidate/cad/models/Molex_KK-254_AE-6410-05A_1x05_P2.54mm_Vertical_key04.step
12.7 x 5.80 x 15.3 mm
