lolz0r/Williams-WPC-Power-Driver-Board-A-12697-3/variants/jlcpcb-100/models/Molex_KK396_06_envelope_key04.step

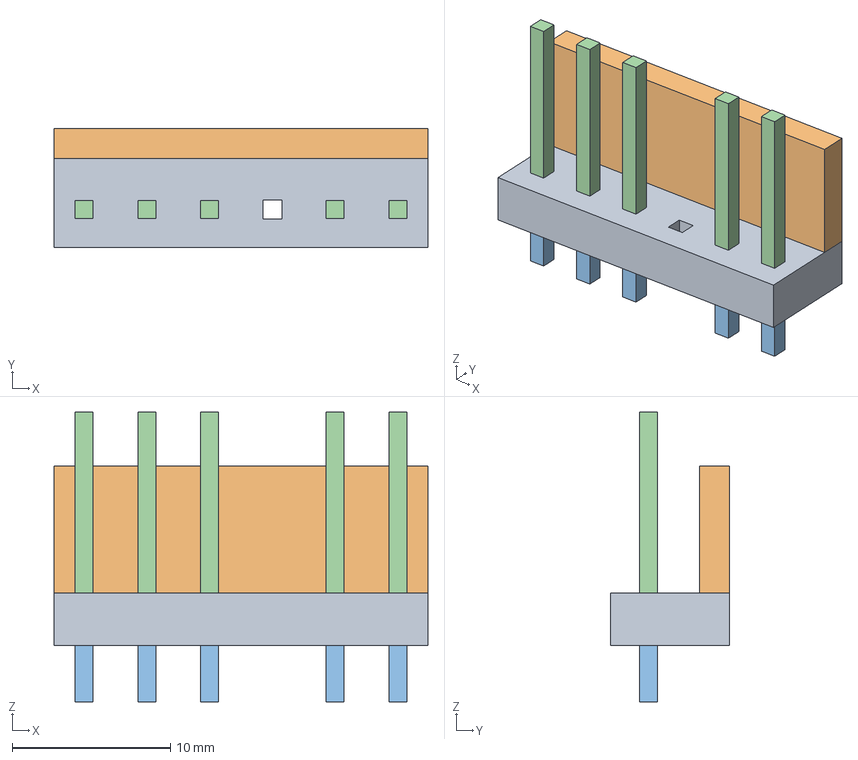
[picture p87: CAD file, 2026-09-09]
variants/jlcpcb-100/models/Molex_KK396_06_envelope_key04.step
23.6 x 7.52 x 18.3 mm
