lolz0r/Williams-WPC-Power-Driver-Board-A-12697-3/variants/jlcpcb-100/output/release-candidate/cad/models/Nichicon_LLS_25x40_envelope.step

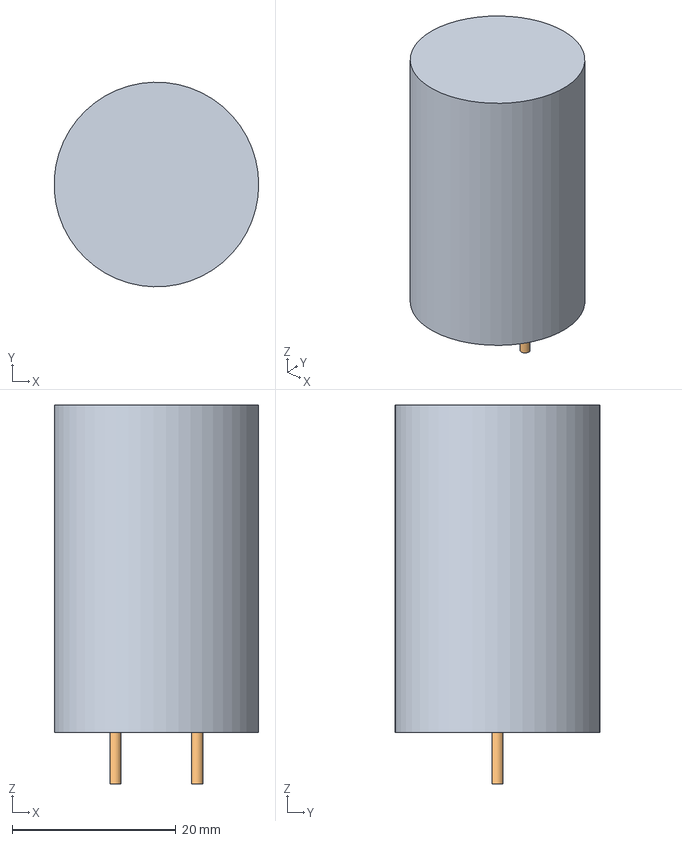
[picture p88: CAD file, 2026-09-09]
variants/jlcpcb-100/output/release-candidate/cad/models/Nichicon_LLS_25x40_envelope.step
25.0 x 25.0 x 46.3 mm
