lolz0r/Williams-WPC-Power-Driver-Board-A-12697-3/variants/jlcpcb-100/output/release-candidate/cad/models/inventory/KNSCHA_2200u_100V.step

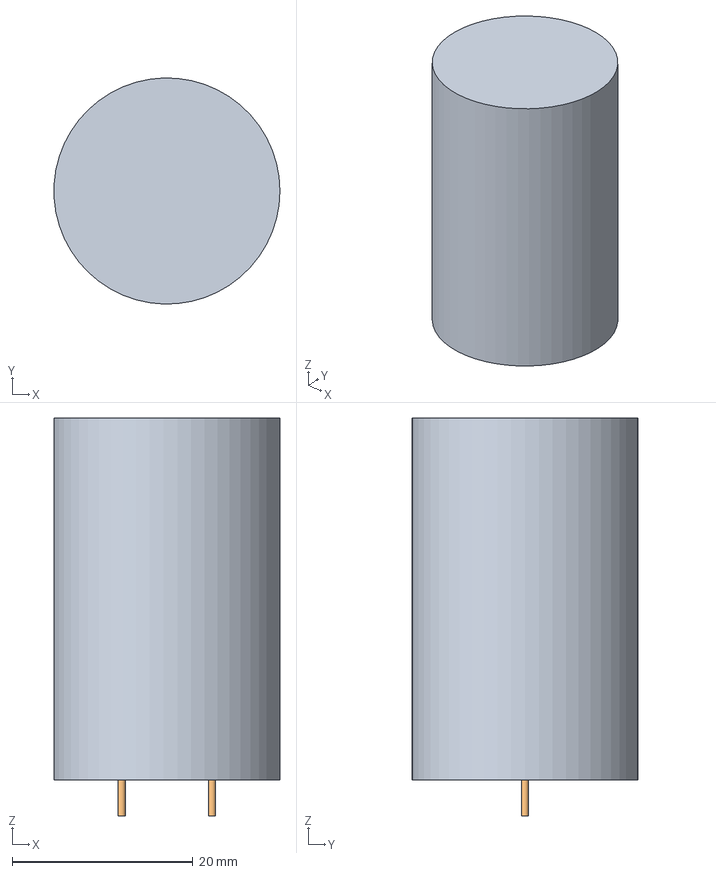
[picture p89: CAD file, 2026-09-14]
variants/jlcpcb-100/output/release-candidate/cad/models/inventory/KNSCHA_2200u_100V.step
25.0 x 25.0 x 44.0 mm
