lolz0r/Williams-WPC-Power-Driver-Board-A-12697-3/variants/jlcpcb-100/output/release-candidate/cad/models/Molex_KK-254_AE-6410-09A_1x09_P2.54mm_Vertical_key03.step

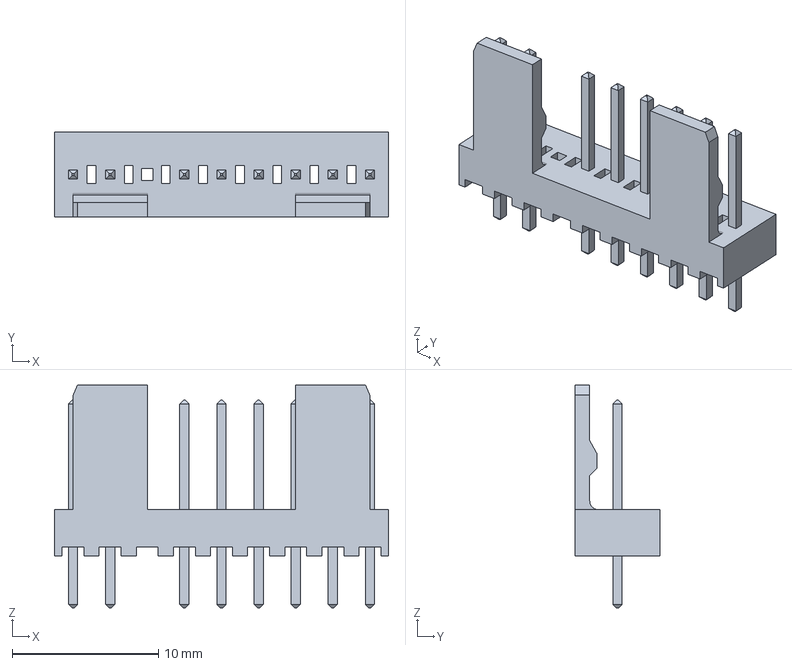
[picture p91: CAD file, 2026-09-09]
variants/jlcpcb-100/output/release-candidate/cad/models/Molex_KK-254_AE-6410-09A_1x09_P2.54mm_Vertical_key03.step
22.9 x 5.80 x 15.3 mm
