lolz0r/Williams-WPC-Power-Driver-Board-A-12697-3/variants/jlcpcb-100/models/inventory/NHA_1000u_100V.step

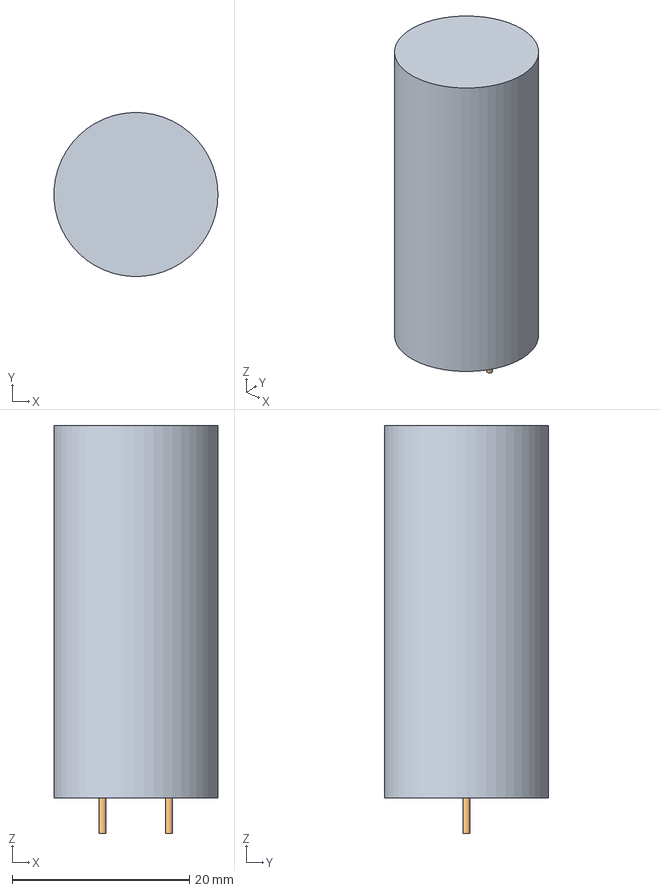
[picture p92: CAD file, 2026-09-14]
variants/jlcpcb-100/models/inventory/NHA_1000u_100V.step
18.5 x 18.5 x 46.0 mm
