lolz0r/Williams-WPC-Power-Driver-Board-A-12697-3/variants/jlcpcb/output/release-candidate/cad/models/Molex_KK396_05_envelope_key03.step

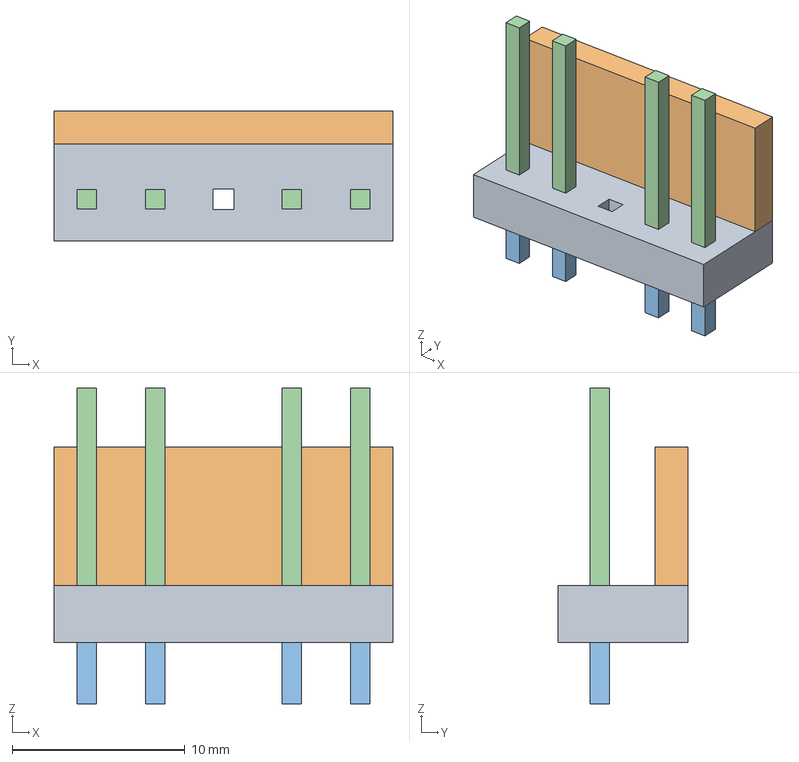
[picture p93: CAD file, 2026-09-09]
variants/jlcpcb/output/release-candidate/cad/models/Molex_KK396_05_envelope_key03.step
19.7 x 7.52 x 18.3 mm
