lolz0r/Williams-WPC-Power-Driver-Board-A-12697-3/variants/jlcpcb-100/models/Molex_KK396_12_envelope.step

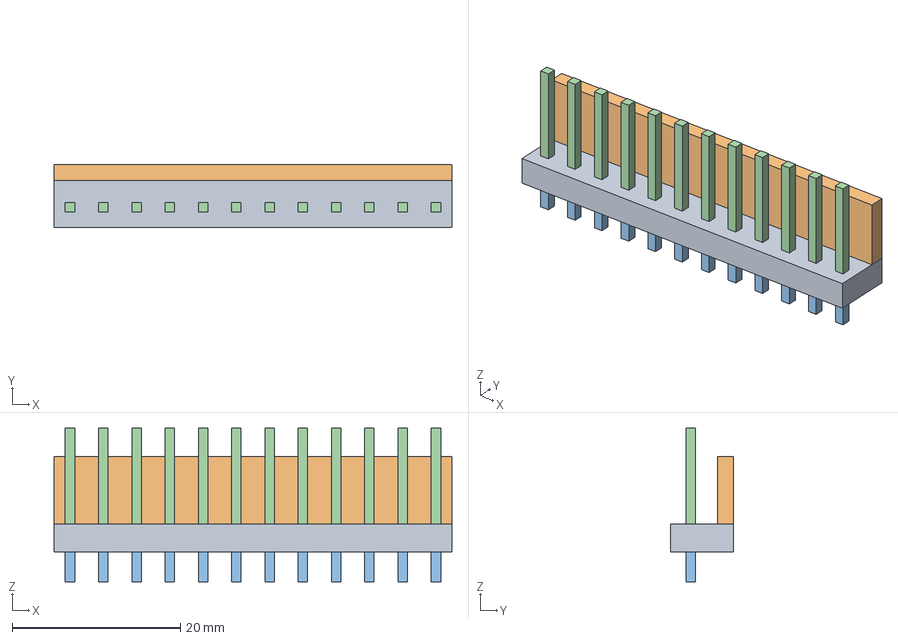
[picture p94: CAD file, 2026-09-09]
variants/jlcpcb-100/models/Molex_KK396_12_envelope.step
47.4 x 7.52 x 18.3 mm
