lolz0r/Williams-WPC-Power-Driver-Board-A-12697-3/variants/jlcpcb-100/models/inventory/GPD_4700u_35V.step

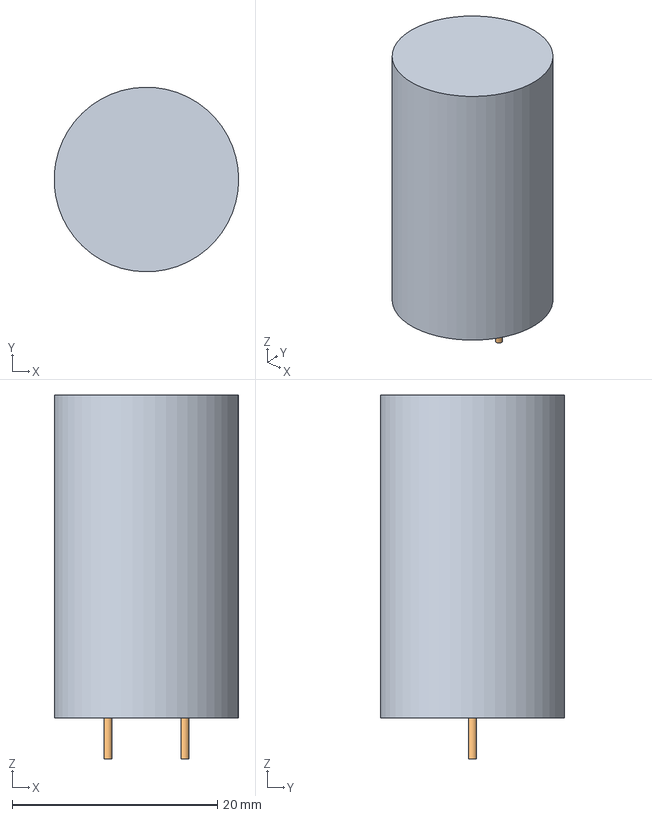
[picture p95: CAD file, 2026-09-14]
variants/jlcpcb-100/models/inventory/GPD_4700u_35V.step
18.0 x 18.0 x 35.5 mm
