lolz0r/Williams-WPC-Power-Driver-Board-A-12697-3/variants/jlcpcb-100/models/inventory/TI_NS20.step

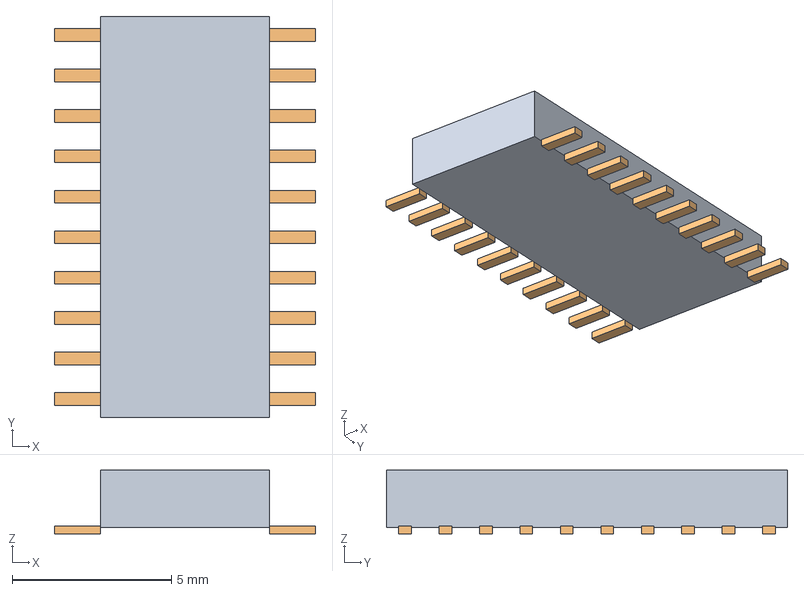
[picture p99: CAD file, 2026-09-14]
variants/jlcpcb-100/models/inventory/TI_NS20.step
8.20 x 12.6 x 2.00 mm
