lolz0r/Williams-WPC-Power-Driver-Board-A-12697-3/variants/jlcpcb/output/release-candidate/cad/models/3M_N2534_6002_RB_envelope.step

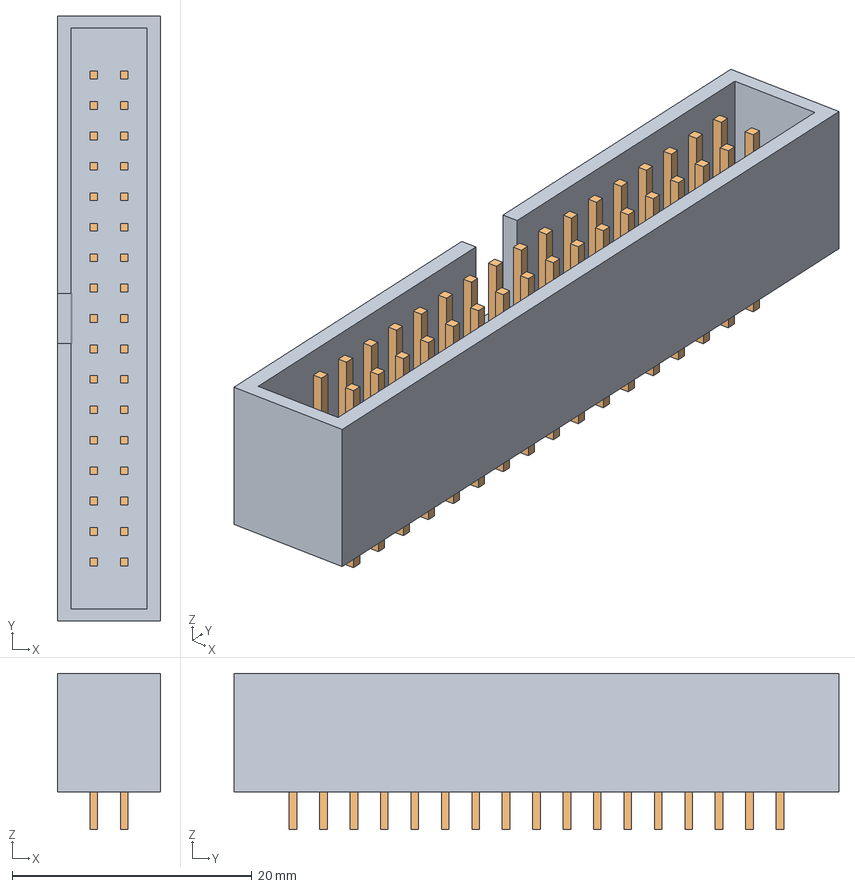
[picture p100: CAD file, 2026-09-09]
variants/jlcpcb/output/release-candidate/cad/models/3M_N2534_6002_RB_envelope.step
8.59 x 50.5 x 13.1 mm
