lolz0r/Williams-WPC-Power-Driver-Board-A-12697-3/variants/jlcpcb-100/output/release-candidate/jlcpcb-assembly/connector-orientation-guide.pdf

0

# JLC-100 assembly orientation guide — native holes and inward locking walls

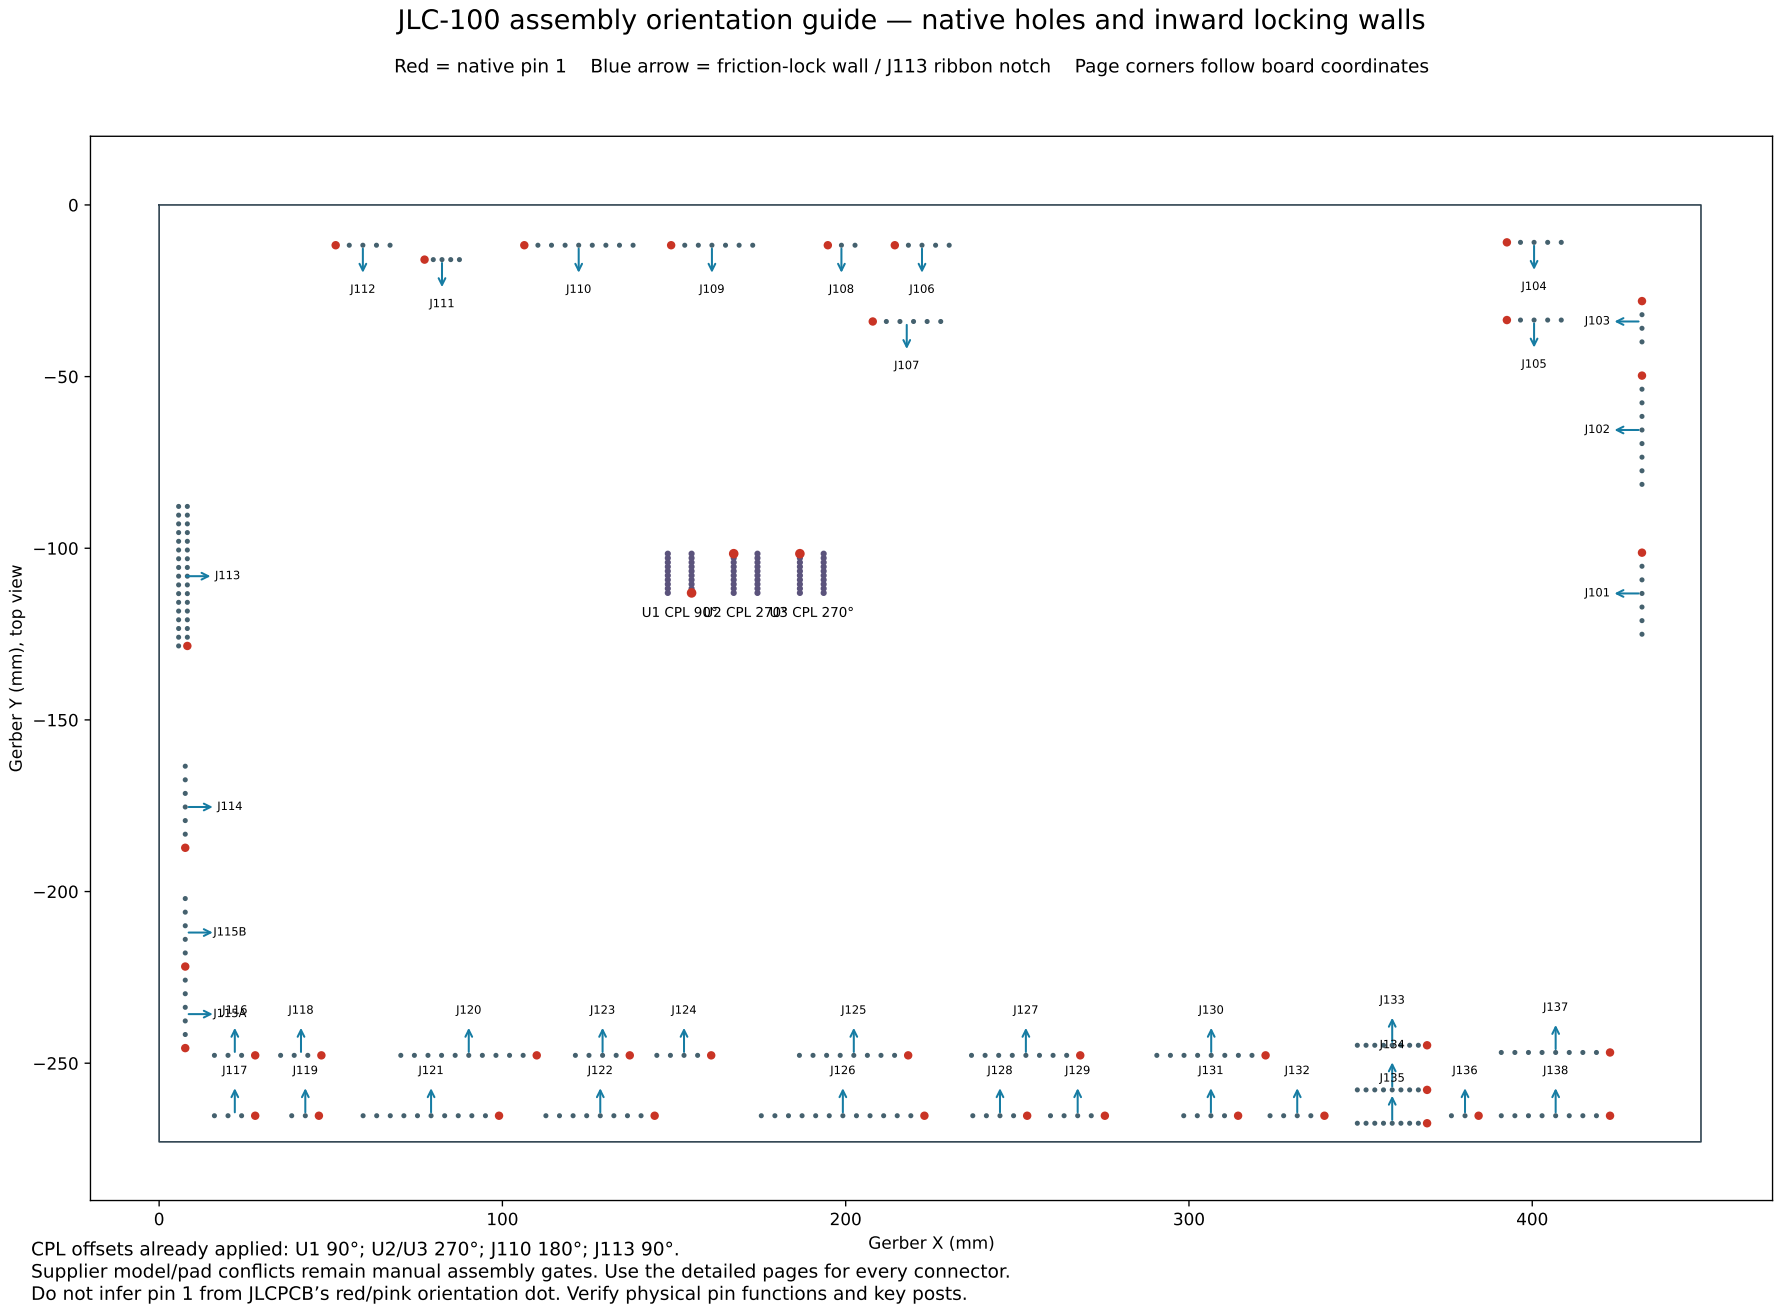
[picture p101: page 1]

Gerber Y (mm), top view

CPL offsets already applied: U1 90°; U2/U3 270°; J110 180°; J113 90°.
Supplier model/pad conflicts remain manual assembly gates. Use the detailed pages for every connector.
Do not infer pin 1 from JLCPCB’s red/pink orientation dot. Verify physical pin functions and key posts.

## J101 C305801 CPL 90°

## J102 C305802 CPL 90°

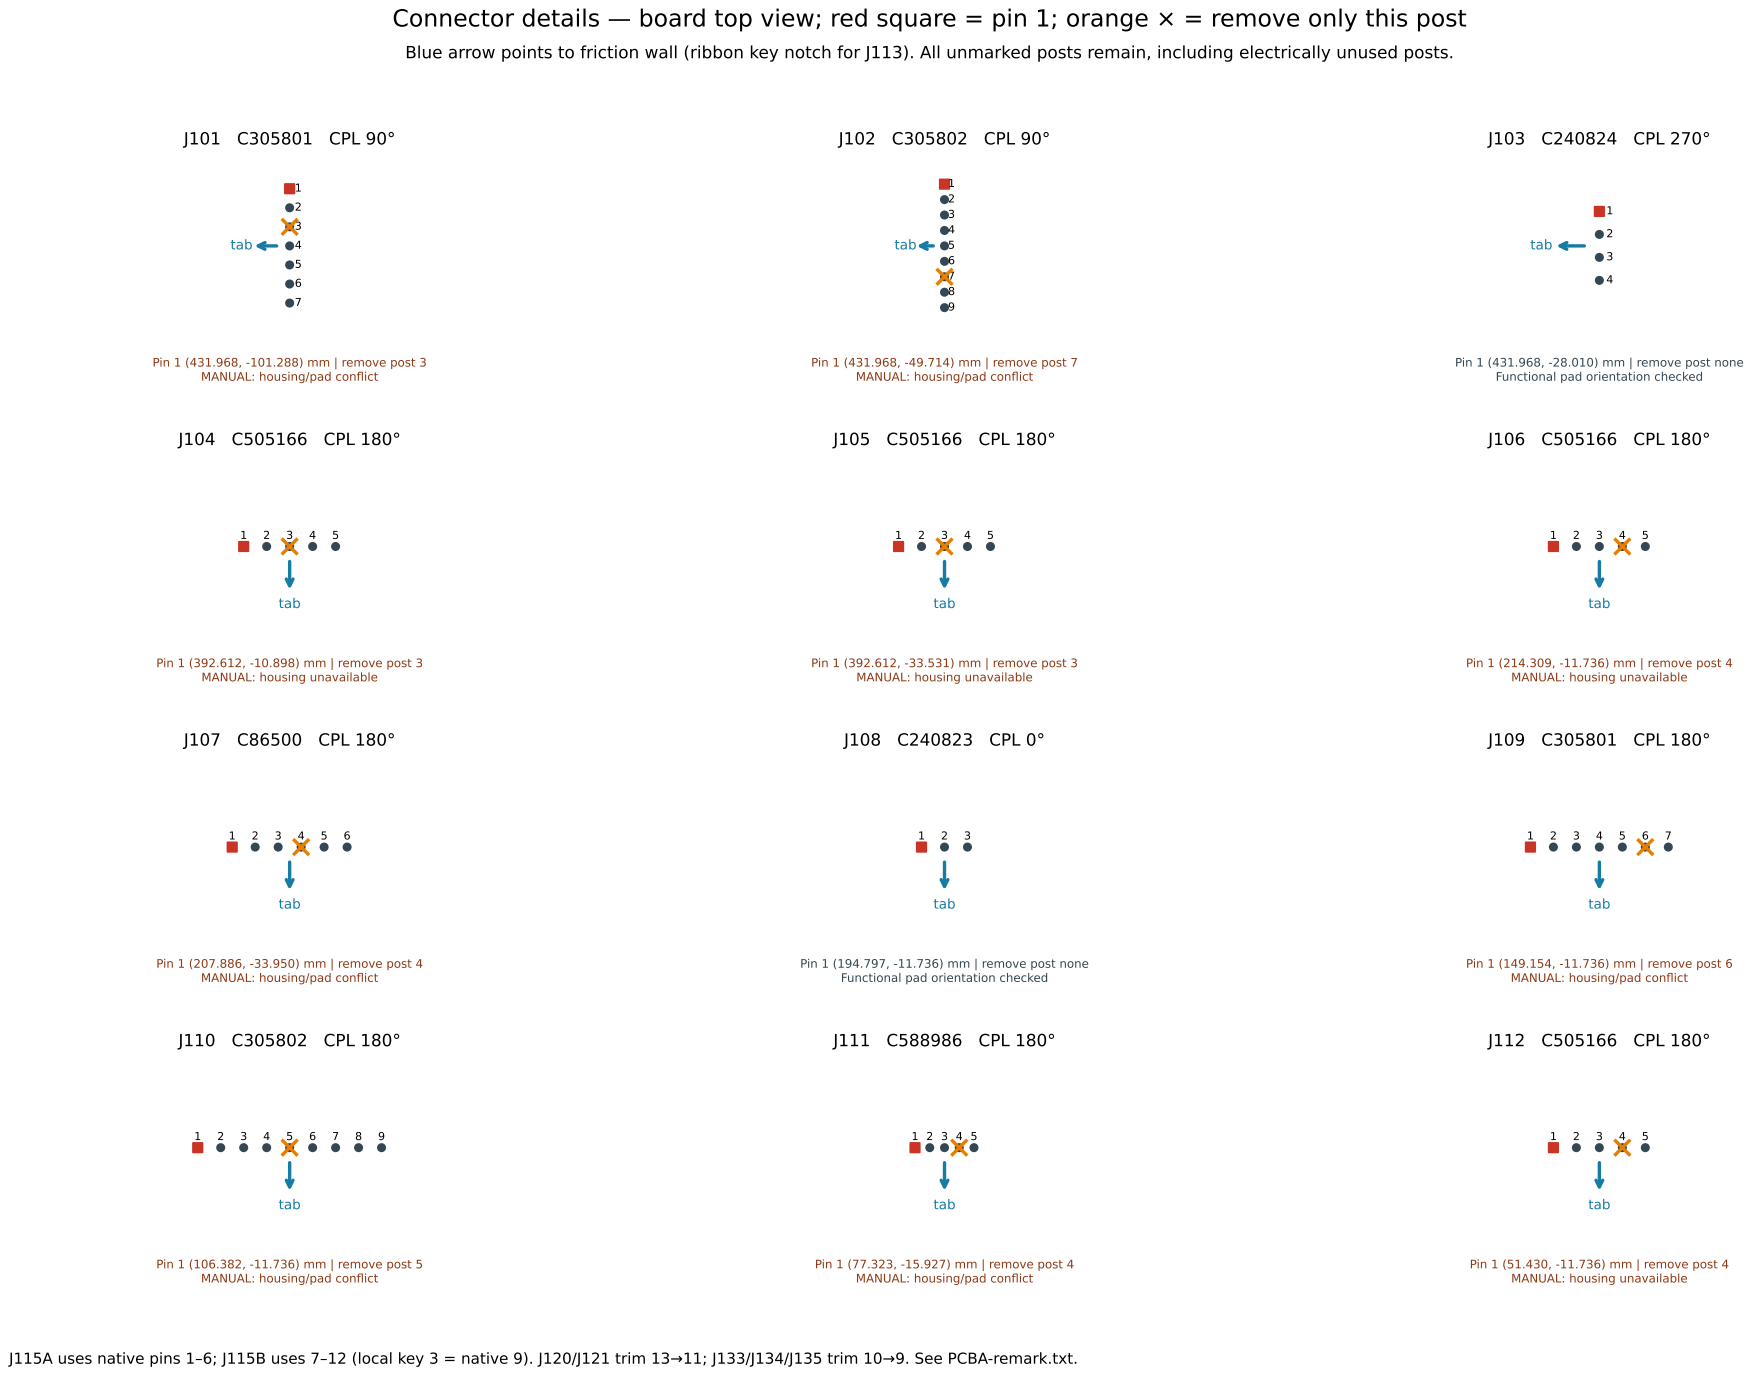
[picture p102: page 2]

Connector details — board top view; red square = pin 1; orange × = remove only this post

Blue arrow points to friction wall (ribbon key notch for J113). All unmarked posts remain, including electrically unused posts.

Pin 1 (431.968, -101.288) mm | remove post 3

Pin 1 (431.968, -49.714) mm | remove post 7

Pin 1 (431.968, -28.010) mm | remove post none

MANUAL: housing/pad conflict

Functional pad orientation checked

Pin 1 (392.612, -10.898) mm | remove post 3

Pin 1 (392.612, -33.531) mm | remove post 3

Pin 1 (214.309, -11.736) mm | remove post 4

Pin 1 (207.886, -33.950) mm | remove post 4

Pin 1 (194.797, -11.736) mm | remove post none

Pin 1 (149.154, -11.736) mm | remove post 6

Pin 1 (106.382, -11.736) mm | remove post 5

Pin 1 (77.323, -15.927) mm | remove post 4

Pin 1 (51.430, -11.736) mm | remove post 4

J115A uses native pins 1–6; J115B uses 7–12 (local key 3 = native 9). J120/J121 trim 13→11; J133/J134/J135 trim 10→9. See PCBA-remark.txt.

## J113 C5200275 CPL 90°

## J114 C305801 CPL 270°

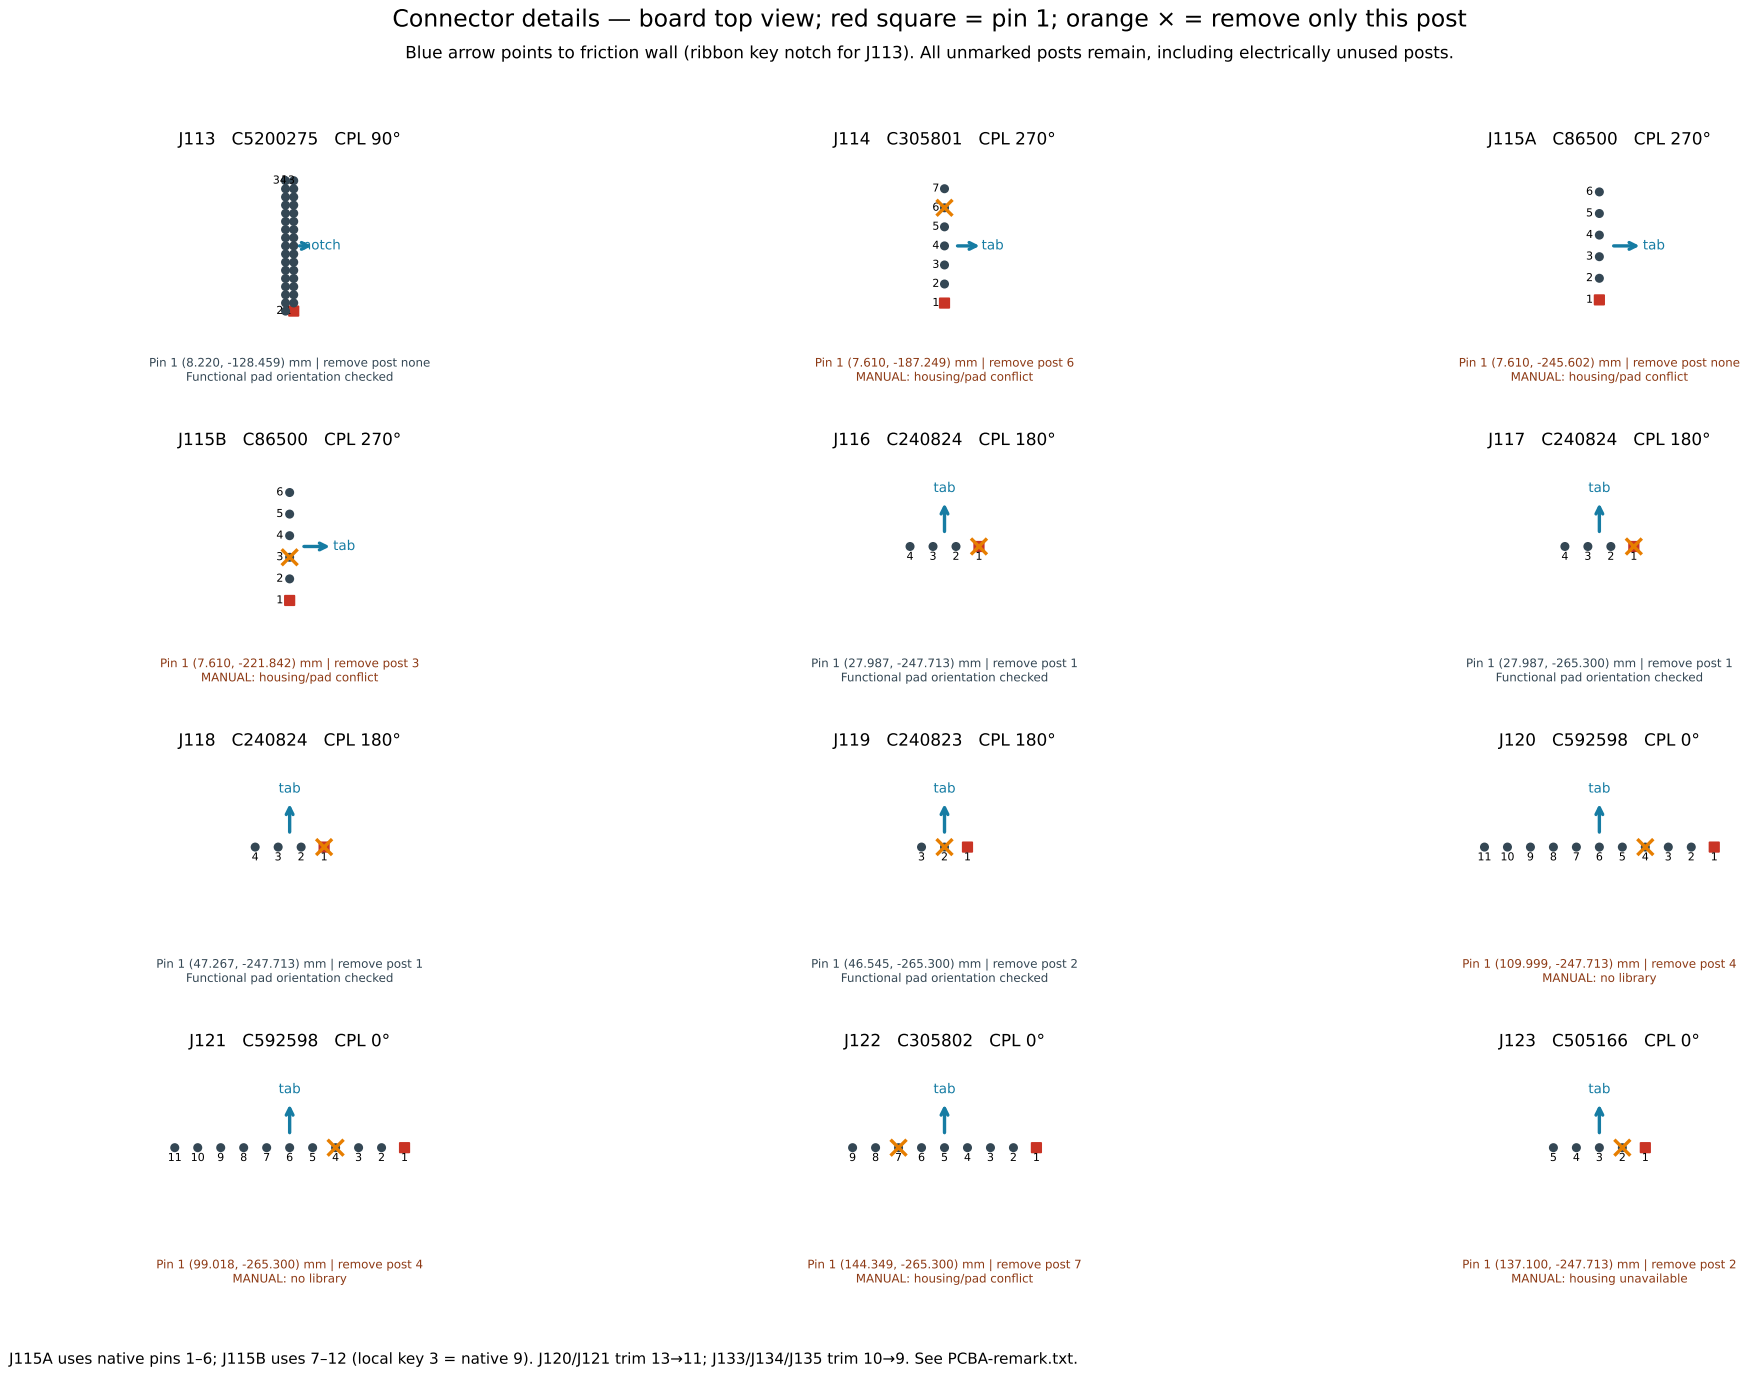
[picture p103: page 3]

Pin 1 (8.220, -128.459) mm | remove post none

Pin 1 (7.610, -187.249) mm | remove post 6

Pin 1 (7.610, -245.602) mm | remove post none

Functional pad orientation checked

MANUAL: housing/pad conflict

Pin 1 (7.610, -221.842) mm | remove post 3

Pin 1 (27.987, -247.713) mm | remove post 1

Pin 1 (27.987, -265.300) mm | remove post 1

Pin 1 (47.267, -247.713) mm | remove post 1

Pin 1 (46.545, -265.300) mm | remove post 2

Pin 1 (109.999, -247.713) mm | remove post 4

Pin 1 (99.018, -265.300) mm | remove post 4

Pin 1 (144.349, -265.300) mm | remove post 7

Pin 1 (137.100, -247.713) mm | remove post 2

## J124 C505166 CPL 0°

## J125 C305802 CPL 0°

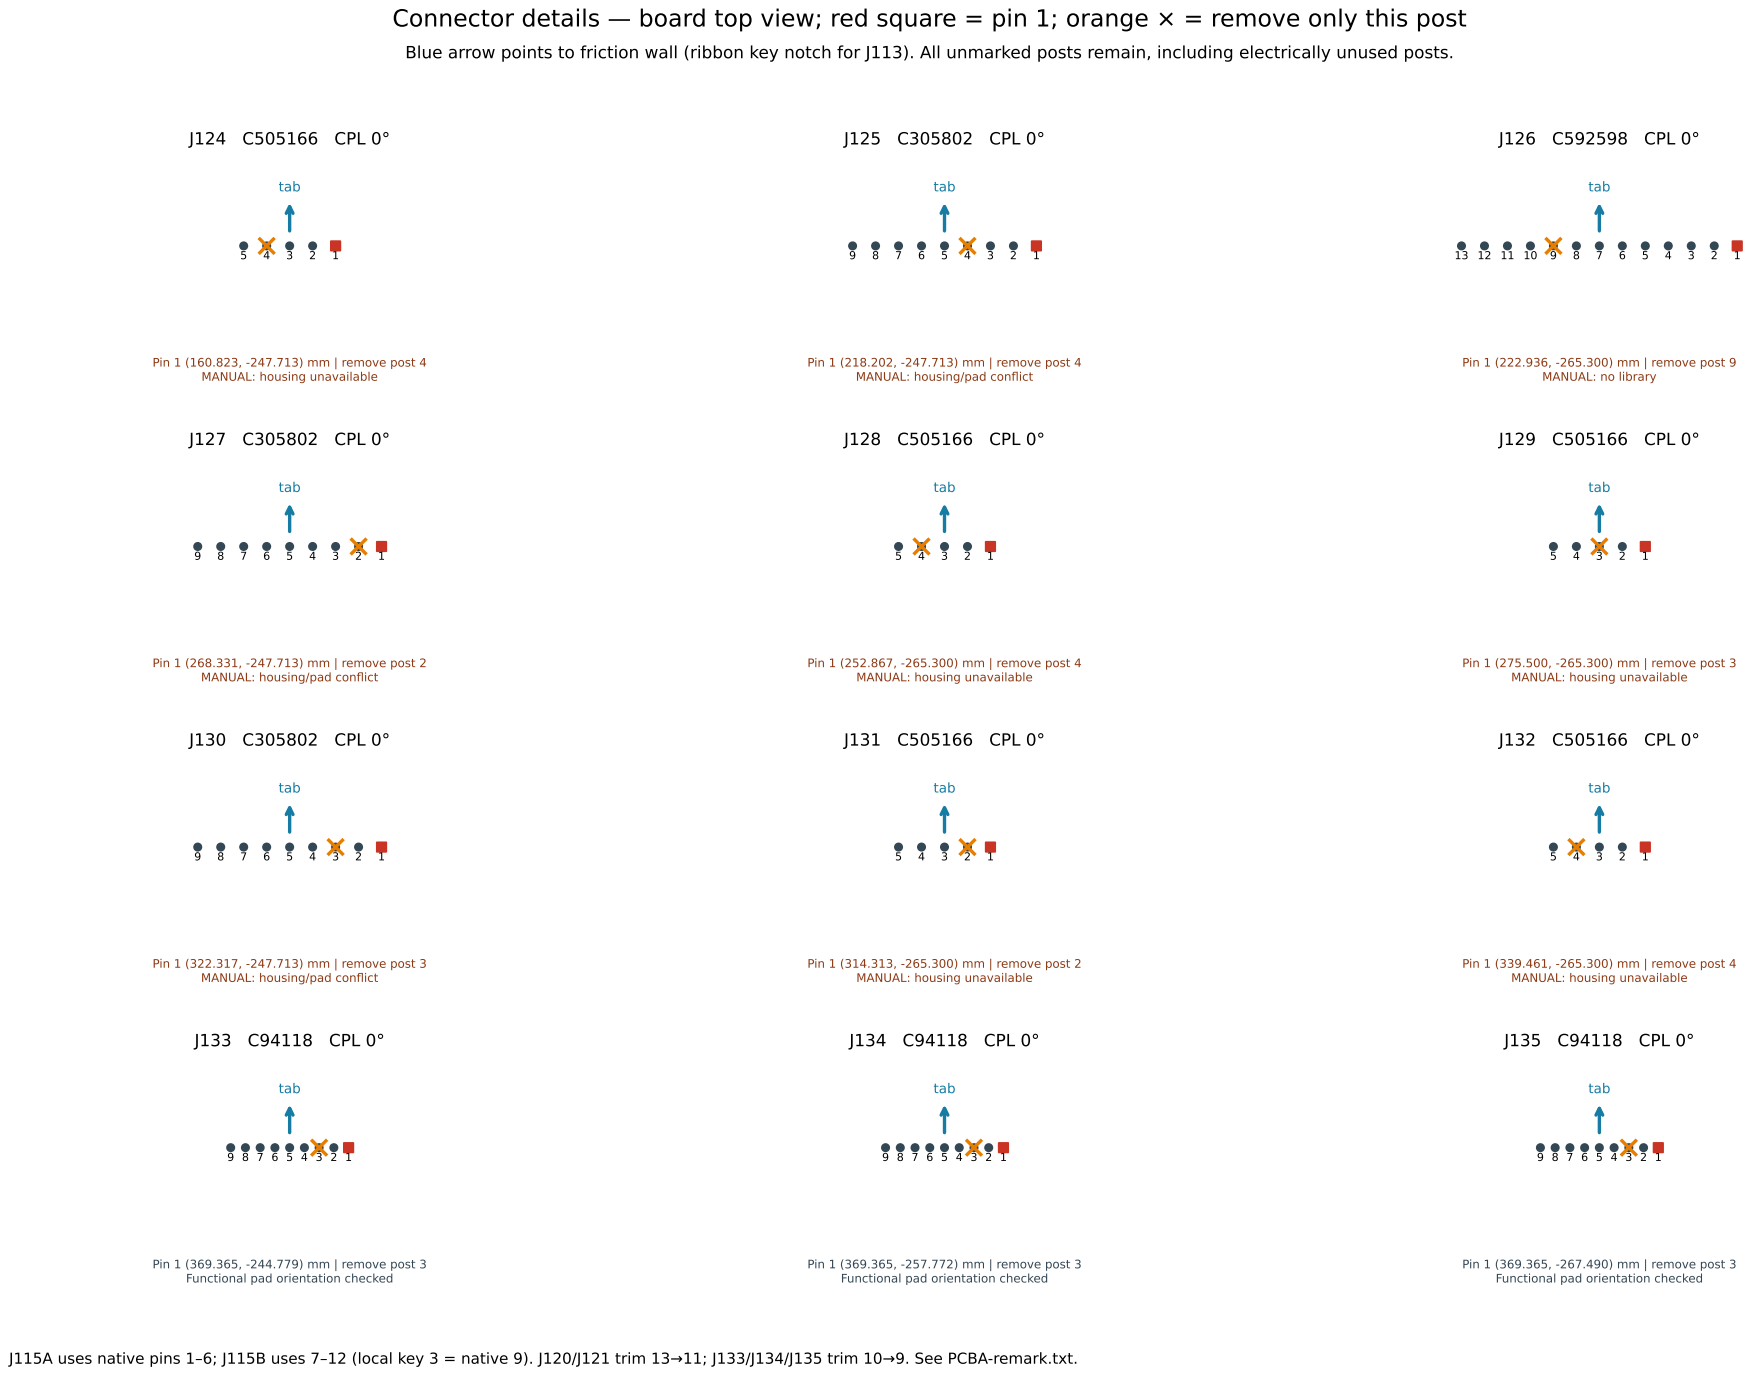
[picture p104: page 4]

Pin 1 (160.823, -247.713) mm | remove post 4

Pin 1 (218.202, -247.713) mm | remove post 4

Pin 1 (222.936, -265.300) mm | remove post 9

MANUAL: housing/pad conflict

Pin 1 (268.331, -247.713) mm | remove post 2

Pin 1 (252.867, -265.300) mm | remove post 4

Pin 1 (275.500, -265.300) mm | remove post 3

Pin 1 (322.317, -247.713) mm | remove post 3

Pin 1 (314.313, -265.300) mm | remove post 2

Pin 1 (339.461, -265.300) mm | remove post 4

Pin 1 (369.365, -244.779) mm | remove post 3

Pin 1 (369.365, -257.772) mm | remove post 3

Pin 1 (369.365, -267.490) mm | remove post 3

Functional pad orientation checked

3 | 2 | 1

tab

Pin 1 (384.373, -265.300) mm | remove post 1
Functional pad orientation checked

## J136 C240823 CPL 180°

9 | 8 | 7 | 6 | 5 | 4 | 3 | 2 | 1

tab

Pin 1 (422.659, -246.875) mm | remove post 8
MANUAL: housing/pad conflict

## J137 C305802 CPL 0°

9 | 8 | 7 | 6 | 5 | 4 | 3 | 2 | 1

tab

Pin 1 (422.659, -265.300) mm | remove post 8
MANUAL: housing/pad conflict

## J138 C305802 CPL 0°
