lolz0r/Williams-WPC-Power-Driver-Board-A-12697-3/output/verification/revision/DRC_WARNING_REVIEW.md

# Item-specific DRC warning review

65 warnings; 65 accepted under the stated geometry checks. Rules remain enabled.

## 1. track_dangling

Retained routed copper. Native pad connectivity and independent filled-copper topology both pass. Free-ended copper/one-layer vias do not create an open circuit; deleting whole reported segments previously broke necessary intermediate junctions. Physical signal integrity is a first-article check.

* `9639c287-f834-4c3b-a24b-99f2fca397b0` — Track [+5V] on F.Cu, length 0.2000 mm; {'x': 170.0, 'y': 168.6}

## 2. track_dangling

Retained routed copper. Native pad connectivity and independent filled-copper topology both pass. Free-ended copper/one-layer vias do not create an open circuit; deleting whole reported segments previously broke necessary intermediate junctions. Physical signal integrity is a first-article check.

* `abbbac8a-856f-42fe-be0d-39f5a037b7e2` — Track [+5V] on F.Cu, length 0.2000 mm; {'x': 309.8, 'y': 82.0}

## 3. track_dangling

Retained routed copper. Native pad connectivity and independent filled-copper topology both pass. Free-ended copper/one-layer vias do not create an open circuit; deleting whole reported segments previously broke necessary intermediate junctions. Physical signal integrity is a first-article check.

* `93abeda5-4922-4e5a-a6e6-52e60480a164` — Track [+12VU] on F.Cu, length 0.2000 mm; {'x': 211.4, 'y': 185.8}

## 4. track_dangling

Retained routed copper. Native pad connectivity and independent filled-copper topology both pass. Free-ended copper/one-layer vias do not create an open circuit; deleting whole reported segments previously broke necessary intermediate junctions. Physical signal integrity is a first-article check.

* `e925f8c8-409f-4d17-b29c-2952f4e9ae23` — Track [+12VU] on F.Cu, length 10.8000 mm; {'x': 231.0, 'y': 63.8}

## 5. via_dangling

Retained routed copper. Native pad connectivity and independent filled-copper topology both pass. Free-ended copper/one-layer vias do not create an open circuit; deleting whole reported segments previously broke necessary intermediate junctions. Physical signal integrity is a first-article check.

* `27425720-9613-4cdd-a888-828a3092219f` — Via [D5] on F.Cu - B.Cu; {'x': 252.6, 'y': 119.2}

## 6. track_dangling

Retained routed copper. Native pad connectivity and independent filled-copper topology both pass. Free-ended copper/one-layer vias do not create an open circuit; deleting whole reported segments previously broke necessary intermediate junctions. Physical signal integrity is a first-article check.

* `1ce2fb63-605d-482d-9b04-e93b6087ed6f` — Track [D5] on B.Cu, length 2.6000 mm; {'x': 182.2, 'y': 110.2}

## 7. track_dangling

Retained routed copper. Native pad connectivity and independent filled-copper topology both pass. Free-ended copper/one-layer vias do not create an open circuit; deleting whole reported segments previously broke necessary intermediate junctions. Physical signal integrity is a first-article check.

* `63b6a001-e71e-4e54-afe0-b2c05d8c0118` — Track [D5] on B.Cu, length 14.0000 mm; {'x': 140.8, 'y': 113.2}

## 8. track_dangling

Retained routed copper. Native pad connectivity and independent filled-copper topology both pass. Free-ended copper/one-layer vias do not create an open circuit; deleting whole reported segments previously broke necessary intermediate junctions. Physical signal integrity is a first-article check.

* `b025ebfd-7fcc-41c7-bb70-01b583afc0f8` — Track [D5] on B.Cu, length 1.2000 mm; {'x': 159.4, 'y': 94.8}

## 9. track_dangling

Retained routed copper. Native pad connectivity and independent filled-copper topology both pass. Free-ended copper/one-layer vias do not create an open circuit; deleting whole reported segments previously broke necessary intermediate junctions. Physical signal integrity is a first-article check.

* `dcf97102-f999-4a53-9715-ada0e540d5cd` — Track [D5] on B.Cu, length 0.8000 mm; {'x': 311.6, 'y': 122.2}

## 10. track_dangling

Retained routed copper. Native pad connectivity and independent filled-copper topology both pass. Free-ended copper/one-layer vias do not create an open circuit; deleting whole reported segments previously broke necessary intermediate junctions. Physical signal integrity is a first-article check.

* `26b83b54-63b3-426c-826a-3f85892bcd3f` — Track [D5] on In2.Cu, length 0.2000 mm; {'x': 182.4, 'y': 109.4}

## 11. track_dangling

Retained routed copper. Native pad connectivity and independent filled-copper topology both pass. Free-ended copper/one-layer vias do not create an open circuit; deleting whole reported segments previously broke necessary intermediate junctions. Physical signal integrity is a first-article check.

* `03d73a92-8a7f-4dce-b2a8-967cb5aac4ce` — Track [D7] on F.Cu, length 1.6000 mm; {'x': 187.6, 'y': 98.4}

## 12. track_dangling

Retained routed copper. Native pad connectivity and independent filled-copper topology both pass. Free-ended copper/one-layer vias do not create an open circuit; deleting whole reported segments previously broke necessary intermediate junctions. Physical signal integrity is a first-article check.

* `08c75cc0-cd0f-4a7d-95aa-bfdd46ef10a3` — Track [D7] on F.Cu, length 1.6000 mm; {'x': 319.4, 'y': 128.2}

## 13. track_dangling

Retained routed copper. Native pad connectivity and independent filled-copper topology both pass. Free-ended copper/one-layer vias do not create an open circuit; deleting whole reported segments previously broke necessary intermediate junctions. Physical signal integrity is a first-article check.

* `2439a70c-702d-4c61-be1e-9d269f674ace` — Track [D7] on F.Cu, length 7.8000 mm; {'x': 160.2, 'y': 118.6}

## 14. track_dangling

Retained routed copper. Native pad connectivity and independent filled-copper topology both pass. Free-ended copper/one-layer vias do not create an open circuit; deleting whole reported segments previously broke necessary intermediate junctions. Physical signal integrity is a first-article check.

* `76f4ee02-e28a-4a4f-9f1c-d44961351dea` — Track [D7] on F.Cu, length 4.4000 mm; {'x': 326.2, 'y': 147.4}

## 15. track_dangling

Retained routed copper. Native pad connectivity and independent filled-copper topology both pass. Free-ended copper/one-layer vias do not create an open circuit; deleting whole reported segments previously broke necessary intermediate junctions. Physical signal integrity is a first-article check.

* `9b2b60e0-9832-436e-b8bf-ea2534fba0eb` — Track [D7] on F.Cu, length 1.0000 mm; {'x': 331.8, 'y': 129.0}

## 16. track_dangling

Retained routed copper. Native pad connectivity and independent filled-copper topology both pass. Free-ended copper/one-layer vias do not create an open circuit; deleting whole reported segments previously broke necessary intermediate junctions. Physical signal integrity is a first-article check.

* `b40234fe-857d-4e16-ab5e-3077e0547a66` — Track [D7] on F.Cu, length 1.2000 mm; {'x': 216.8, 'y': 165.0}

## 17. track_dangling

Retained routed copper. Native pad connectivity and independent filled-copper topology both pass. Free-ended copper/one-layer vias do not create an open circuit; deleting whole reported segments previously broke necessary intermediate junctions. Physical signal integrity is a first-article check.

* `bee55847-f9ed-4bdf-8f0f-14470bbc904e` — Track [D7] on F.Cu, length 6.4000 mm; {'x': 326.2, 'y': 140.6}

## 18. track_dangling

Retained routed copper. Native pad connectivity and independent filled-copper topology both pass. Free-ended copper/one-layer vias do not create an open circuit; deleting whole reported segments previously broke necessary intermediate junctions. Physical signal integrity is a first-article check.

* `d41a8b9e-13c8-4b7b-8781-74d364f8005d` — Track [D7] on F.Cu, length 0.8000 mm; {'x': 216.0, 'y': 159.8}

## 19. track_dangling

Retained routed copper. Native pad connectivity and independent filled-copper topology both pass. Free-ended copper/one-layer vias do not create an open circuit; deleting whole reported segments previously broke necessary intermediate junctions. Physical signal integrity is a first-article check.

* `fc92767b-8439-408c-a240-c080e3cf083d` — Track [D7] on F.Cu, length 0.4000 mm; {'x': 329.6, 'y': 119.2}

## 20. via_dangling

Retained routed copper. Native pad connectivity and independent filled-copper topology both pass. Free-ended copper/one-layer vias do not create an open circuit; deleting whole reported segments previously broke necessary intermediate junctions. Physical signal integrity is a first-article check.

* `b4a8dd0a-e45c-4fde-ac7d-0097f16919b2` — Via [D7] on F.Cu - B.Cu; {'x': 352.4, 'y': 144.6}

## 21. track_dangling

Retained routed copper. Native pad connectivity and independent filled-copper topology both pass. Free-ended copper/one-layer vias do not create an open circuit; deleting whole reported segments previously broke necessary intermediate junctions. Physical signal integrity is a first-article check.

* `37215763-4e55-4466-8d7e-514676b7246a` — Track [D7] on B.Cu, length 0.8000 mm; {'x': 222.2, 'y': 112.6}

## 22. track_dangling

Retained routed copper. Native pad connectivity and independent filled-copper topology both pass. Free-ended copper/one-layer vias do not create an open circuit; deleting whole reported segments previously broke necessary intermediate junctions. Physical signal integrity is a first-article check.

* `088d21fc-24ff-4500-b6e5-9b957b4481ac` — Track [D7] on In2.Cu, length 3.8000 mm; {'x': 156.6, 'y': 123.6}

## 23. track_dangling

Retained routed copper. Native pad connectivity and independent filled-copper topology both pass. Free-ended copper/one-layer vias do not create an open circuit; deleting whole reported segments previously broke necessary intermediate junctions. Physical signal integrity is a first-article check.

* `45f65ba9-b42f-4141-a6d7-c38ca27e1337` — Track [D7] on In2.Cu, length 22.0000 mm; {'x': 258.2, 'y': 117.0}

## 24. track_dangling

Retained routed copper. Native pad connectivity and independent filled-copper topology both pass. Free-ended copper/one-layer vias do not create an open circuit; deleting whole reported segments previously broke necessary intermediate junctions. Physical signal integrity is a first-article check.

* `dd84b3ad-cedb-44c1-bbdf-4d92c6ba9e4d` — Track [D7] on In2.Cu, length 1.2000 mm; {'x': 224.6, 'y': 109.2}

## 25. track_dangling

Retained routed copper. Native pad connectivity and independent filled-copper topology both pass. Free-ended copper/one-layer vias do not create an open circuit; deleting whole reported segments previously broke necessary intermediate junctions. Physical signal integrity is a first-article check.

* `dfd9066f-0ac6-4bd7-a81c-2ad53e9886f8` — Track [D7] on In2.Cu, length 0.4000 mm; {'x': 319.4, 'y': 117.0}

## 26. via_dangling

Retained routed copper. Native pad connectivity and independent filled-copper topology both pass. Free-ended copper/one-layer vias do not create an open circuit; deleting whole reported segments previously broke necessary intermediate junctions. Physical signal integrity is a first-article check.

* `c75a05b0-4ff1-45cd-9813-41952600c621` — Via [COLB4] on F.Cu - B.Cu; {'x': 431.6, 'y': 195.2}

## 27. via_dangling

Retained routed copper. Native pad connectivity and independent filled-copper topology both pass. Free-ended copper/one-layer vias do not create an open circuit; deleting whole reported segments previously broke necessary intermediate junctions. Physical signal integrity is a first-article check.

* `a110c927-d6dd-409e-8c09-d436b202432d` — Via [CLK_LAMP_COL] on F.Cu - B.Cu; {'x': 239.0, 'y': 151.2}

## 28. track_dangling

Retained routed copper. Native pad connectivity and independent filled-copper topology both pass. Free-ended copper/one-layer vias do not create an open circuit; deleting whole reported segments previously broke necessary intermediate junctions. Physical signal integrity is a first-article check.

* `870184d0-caef-467f-a033-0c759b690e96` — Track [ROWCLR1] on F.Cu, length 0.2000 mm; {'x': 388.8, 'y': 154.4}

## 29. track_dangling

Retained routed copper. Native pad connectivity and independent filled-copper topology both pass. Free-ended copper/one-layer vias do not create an open circuit; deleting whole reported segments previously broke necessary intermediate junctions. Physical signal integrity is a first-article check.

* `d8d06390-a596-46b2-acf1-17677e3e6174` — Track [ROWCLR1] on F.Cu, length 2.4000 mm; {'x': 394.0, 'y': 140.6}

## 30. track_dangling

Retained routed copper. Native pad connectivity and independent filled-copper topology both pass. Free-ended copper/one-layer vias do not create an open circuit; deleting whole reported segments previously broke necessary intermediate junctions. Physical signal integrity is a first-article check.

* `fee19731-bb21-4abb-80f8-bcb4a1701bc9` — Track [ROWCLR1] on F.Cu, length 0.2000 mm; {'x': 398.6, 'y': 152.6}

## 31. via_dangling

Retained routed copper. Native pad connectivity and independent filled-copper topology both pass. Free-ended copper/one-layer vias do not create an open circuit; deleting whole reported segments previously broke necessary intermediate junctions. Physical signal integrity is a first-article check.

* `c8481b5b-faac-4bdd-ac69-f45fe3f920a2` — Via [ROWCLR1] on F.Cu - B.Cu; {'x': 399.0, 'y': 152.0}

## 32. track_dangling

Retained routed copper. Native pad connectivity and independent filled-copper topology both pass. Free-ended copper/one-layer vias do not create an open circuit; deleting whole reported segments previously broke necessary intermediate junctions. Physical signal integrity is a first-article check.

* `cc960d20-4ed1-4595-a007-3bd12668b12b` — Track [AC13_B] on F.Cu, length 1.1992 mm; {'x': 361.2, 'y': 52.2}

## 33. via_dangling

Retained routed copper. Native pad connectivity and independent filled-copper topology both pass. Free-ended copper/one-layer vias do not create an open circuit; deleting whole reported segments previously broke necessary intermediate junctions. Physical signal integrity is a first-article check.

* `e18529be-e12b-4c47-b9b3-a7f46634abaa` — Via [AC13_B] on F.Cu - B.Cu; {'x': 368.0, 'y': 70.0}

## 34. via_dangling

Retained routed copper. Native pad connectivity and independent filled-copper topology both pass. Free-ended copper/one-layer vias do not create an open circuit; deleting whole reported segments previously broke necessary intermediate junctions. Physical signal integrity is a first-article check.

* `313a91a8-c224-49bc-bc02-22d7baae8354` — Via [SOL12_L] on F.Cu - B.Cu; {'x': 247.4, 'y': 106.6}

## 35. track_dangling

Retained routed copper. Native pad connectivity and independent filled-copper topology both pass. Free-ended copper/one-layer vias do not create an open circuit; deleting whole reported segments previously broke necessary intermediate junctions. Physical signal integrity is a first-article check.

* `4ef624e2-5412-4743-9429-d32a3844cb5d` — Track [/CPU_Interface/ZC_SAMPLE] on B.Cu, length 0.2000 mm; {'x': 86.8, 'y': 73.6}

## 36. track_dangling

Retained routed copper. Native pad connectivity and independent filled-copper topology both pass. Free-ended copper/one-layer vias do not create an open circuit; deleting whole reported segments previously broke necessary intermediate junctions. Physical signal integrity is a first-article check.

* `f1c93e23-3765-4888-be5d-1eb1e792406e` — Track [FLIP_RLY_L] on F.Cu, length 1.2000 mm; {'x': 138.4, 'y': 118.6}

## 37. via_dangling

Retained routed copper. Native pad connectivity and independent filled-copper topology both pass. Free-ended copper/one-layer vias do not create an open circuit; deleting whole reported segments previously broke necessary intermediate junctions. Physical signal integrity is a first-article check.

* `346c3a11-f0ff-403c-8085-9b6a1cb6e7cc` — Via [FLIP_RLY_L] on F.Cu - B.Cu; {'x': 103.8, 'y': 54.0}

## 38. via_dangling

Retained routed copper. Native pad connectivity and independent filled-copper topology both pass. Free-ended copper/one-layer vias do not create an open circuit; deleting whole reported segments previously broke necessary intermediate junctions. Physical signal integrity is a first-article check.

* `e0e8e002-4229-4f7a-a90d-1c6759c48c18` — Via [FLIP_RLY_L] on F.Cu - B.Cu; {'x': 137.2, 'y': 115.6}

## 39. via_dangling

Retained routed copper. Native pad connectivity and independent filled-copper topology both pass. Free-ended copper/one-layer vias do not create an open circuit; deleting whole reported segments previously broke necessary intermediate junctions. Physical signal integrity is a first-article check.

* `b506e93b-53de-43ca-926d-7d8917bf2ac8` — Via [SOL06] on F.Cu - B.Cu; {'x': 277.8, 'y': 181.4}

## 40. track_dangling

Retained routed copper. Native pad connectivity and independent filled-copper topology both pass. Free-ended copper/one-layer vias do not create an open circuit; deleting whole reported segments previously broke necessary intermediate junctions. Physical signal integrity is a first-article check.

* `478b1a9a-5769-42c5-b7b6-01384c163d5a` — Track [AC16_A] on F.Cu, length 3.6000 mm; {'x': 374.6, 'y': 61.4}

## 41. track_dangling

Retained routed copper. Native pad connectivity and independent filled-copper topology both pass. Free-ended copper/one-layer vias do not create an open circuit; deleting whole reported segments previously broke necessary intermediate junctions. Physical signal integrity is a first-article check.

* `cc83e031-7b3c-4b53-9eed-05952293b926` — Track [D6_N] on F.Cu, length 0.6000 mm; {'x': 8.6, 'y': 107.6}

## 42. track_dangling

Retained routed copper. Native pad connectivity and independent filled-copper topology both pass. Free-ended copper/one-layer vias do not create an open circuit; deleting whole reported segments previously broke necessary intermediate junctions. Physical signal integrity is a first-article check.

* `ed9434b5-c4e3-48b0-8b1b-adc140e9f48f` — Track [D6_N] on F.Cu, length 0.8246 mm; {'x': 9.6, 'y': 103.0}

## 43. via_dangling

Retained routed copper. Native pad connectivity and independent filled-copper topology both pass. Free-ended copper/one-layer vias do not create an open circuit; deleting whole reported segments previously broke necessary intermediate junctions. Physical signal integrity is a first-article check.

* `0b33145a-4d11-4a51-a696-56ac345c38e1` — Via [D6_N] on F.Cu - B.Cu; {'x': 12.8, 'y': 88.0}

## 44. track_dangling

Retained routed copper. Native pad connectivity and independent filled-copper topology both pass. Free-ended copper/one-layer vias do not create an open circuit; deleting whole reported segments previously broke necessary intermediate junctions. Physical signal integrity is a first-article check.

* `5c37887d-eb69-464b-9ac7-9e89caf83a31` — Track [D6_N] on B.Cu, length 0.2000 mm; {'x': 13.6, 'y': 97.2}

## 45. track_dangling

Retained routed copper. Native pad connectivity and independent filled-copper topology both pass. Free-ended copper/one-layer vias do not create an open circuit; deleting whole reported segments previously broke necessary intermediate junctions. Physical signal integrity is a first-article check.

* `ab22f8fb-2af5-4ba5-9146-67d450a85107` — Track [D6_N] on B.Cu, length 1.2000 mm; {'x': 14.0, 'y': 95.4}

## 46. track_dangling

Retained routed copper. Native pad connectivity and independent filled-copper topology both pass. Free-ended copper/one-layer vias do not create an open circuit; deleting whole reported segments previously broke necessary intermediate junctions. Physical signal integrity is a first-article check.

* `f980a3c8-ee95-43ca-8f74-a1a809162adc` — Track [D6_N] on B.Cu, length 1.6000 mm; {'x': 10.4, 'y': 98.2}

## 47. track_dangling

Retained routed copper. Native pad connectivity and independent filled-copper topology both pass. Free-ended copper/one-layer vias do not create an open circuit; deleting whole reported segments previously broke necessary intermediate junctions. Physical signal integrity is a first-article check.

* `58b2817b-3eb5-4a27-a0b4-7e92b304c0a7` — Track [D6_N] on In2.Cu, length 13.0000 mm; {'x': 321.8, 'y': 102.8}

## 48. track_dangling

Retained routed copper. Native pad connectivity and independent filled-copper topology both pass. Free-ended copper/one-layer vias do not create an open circuit; deleting whole reported segments previously broke necessary intermediate junctions. Physical signal integrity is a first-article check.

* `6350babf-f6f7-4d45-9209-b685761e66a4` — Track [D5_N] on F.Cu, length 0.2000 mm; {'x': 11.6, 'y': 105.6}

## 49. via_dangling

Retained routed copper. Native pad connectivity and independent filled-copper topology both pass. Free-ended copper/one-layer vias do not create an open circuit; deleting whole reported segments previously broke necessary intermediate junctions. Physical signal integrity is a first-article check.

* `51e055c2-b2a7-483b-b5a4-918724b051a1` — Via [D5_N] on F.Cu - B.Cu; {'x': 11.6, 'y': 116.2}

## 50. track_dangling

Retained routed copper. Native pad connectivity and independent filled-copper topology both pass. Free-ended copper/one-layer vias do not create an open circuit; deleting whole reported segments previously broke necessary intermediate junctions. Physical signal integrity is a first-article check.

* `3ff19862-abde-4bc4-83c2-eb46af91d72a` — Track [D3_N] on F.Cu, length 0.4000 mm; {'x': 234.6, 'y': 119.8}

## 51. track_dangling

Retained routed copper. Native pad connectivity and independent filled-copper topology both pass. Free-ended copper/one-layer vias do not create an open circuit; deleting whole reported segments previously broke necessary intermediate junctions. Physical signal integrity is a first-article check.

* `aa4b540d-bd8e-4b96-b0b3-5468a36e7063` — Track [D3_N] on F.Cu, length 3.4000 mm; {'x': 14.0, 'y': 100.8}

## 52. via_dangling

Retained routed copper. Native pad connectivity and independent filled-copper topology both pass. Free-ended copper/one-layer vias do not create an open circuit; deleting whole reported segments previously broke necessary intermediate junctions. Physical signal integrity is a first-article check.

* `0c6c9bb0-8add-4715-8eae-f00236e658cf` — Via [D3_N] on F.Cu - B.Cu; {'x': 93.8, 'y': 94.8}

## 53. track_dangling

Retained routed copper. Native pad connectivity and independent filled-copper topology both pass. Free-ended copper/one-layer vias do not create an open circuit; deleting whole reported segments previously broke necessary intermediate junctions. Physical signal integrity is a first-article check.

* `3425debb-f540-4b81-9aae-e85d185ede7b` — Track [D3_N] on In2.Cu, length 0.2000 mm; {'x': 222.8, 'y': 116.6}

## 54. track_dangling

Retained routed copper. Native pad connectivity and independent filled-copper topology both pass. Free-ended copper/one-layer vias do not create an open circuit; deleting whole reported segments previously broke necessary intermediate junctions. Physical signal integrity is a first-article check.

* `6b79e6d0-f84e-4450-ae67-ec0313fb57cf` — Track [D3_N] on In2.Cu, length 1.8000 mm; {'x': 17.4, 'y': 107.0}

## 55. track_dangling

Retained routed copper. Native pad connectivity and independent filled-copper topology both pass. Free-ended copper/one-layer vias do not create an open circuit; deleting whole reported segments previously broke necessary intermediate junctions. Physical signal integrity is a first-article check.

* `bfd1ff62-9d4b-4bc2-a51e-56416711ccb1` — Track [D3_N] on In2.Cu, length 1.4000 mm; {'x': 233.4, 'y': 117.2}

## 56. track_dangling

Retained routed copper. Native pad connectivity and independent filled-copper topology both pass. Free-ended copper/one-layer vias do not create an open circuit; deleting whole reported segments previously broke necessary intermediate junctions. Physical signal integrity is a first-article check.

* `4c61b0f3-aa47-40eb-83bc-188fbbeb2dd5` — Track [COLB2] on F.Cu, length 0.8000 mm; {'x': 424.2, 'y': 177.6}

## 57. via_dangling

Retained routed copper. Native pad connectivity and independent filled-copper topology both pass. Free-ended copper/one-layer vias do not create an open circuit; deleting whole reported segments previously broke necessary intermediate junctions. Physical signal integrity is a first-article check.

* `50fc9069-8824-4834-94d1-2a4f0dcf92fe` — Via [COLB2] on F.Cu - B.Cu; {'x': 424.2, 'y': 202.6}

## 58. track_not_centered_on_via

Offset junction retains positive copper overlap with plated annulus, same net; native clearance and independent continuity pass. Centre alignment is a routing style warning.

* `888a35db-ee46-49c3-91dd-95b6a5cd5be5` — Track [D3] on B.Cu, length 22.4009 mm; {'x': 302.6, 'y': 118.4}
* `d2cc7d8a-ec9a-465c-b31d-5ec70fe0e329` — Via [D3] on F.Cu - B.Cu; {'x': 303.0, 'y': 118.6}
* Track/annulus overlap excluding hole: 0.1160 mm².

## 59. track_not_centered_on_via

Offset junction retains positive copper overlap with plated annulus, same net; native clearance and independent continuity pass. Centre alignment is a routing style warning.

* `4111376b-6bbf-4d37-b33e-27787e8c17c1` — Track [D5] on B.Cu, length 20.0010 mm; {'x': 280.6, 'y': 122.0}
* `b2725d89-97a1-4c8f-8860-b6831f17f1cd` — Via [D5] on F.Cu - B.Cu; {'x': 280.2, 'y': 122.2}
* Track/annulus overlap excluding hole: 0.1160 mm².

## 60. track_not_centered_on_via

Offset junction retains positive copper overlap with plated annulus, same net; native clearance and independent continuity pass. Centre alignment is a routing style warning.

* `8b4e9cfd-3223-4e9e-aa26-6cd585c0dfab` — Track [+50V] on F.Cu, length 13.6000 mm; {'x': 254.4, 'y': 41.8}
* `a5e97a77-17b9-42c9-9141-17caa7d4d5f6` — Via [+50V] on F.Cu - B.Cu; {'x': 254.0, 'y': 42.4}
* Track/annulus overlap excluding hole: 1.6503 mm².

## 61. track_not_centered_on_via

Offset junction retains positive copper overlap with plated annulus, same net; native clearance and independent continuity pass. Centre alignment is a routing style warning.

* `b8200722-0399-495c-871e-cc9b9cf643f4` — Track [+50V] on B.Cu, length 14.6000 mm; {'x': 280.8, 'y': 160.6}
* `ac543322-9dae-482f-ae3b-6548d7b25f6d` — Via [+50V] on F.Cu - B.Cu; {'x': 280.4, 'y': 159.8}
* Track/annulus overlap excluding hole: 1.3916 mm².

## 62. track_not_centered_on_via

Offset junction retains positive copper overlap with plated annulus, same net; native clearance and independent continuity pass. Centre alignment is a routing style warning.

* `ba97cc34-a2c4-4c20-82b1-28c35e55fd3f` — Track [+50V] on B.Cu, length 24.6000 mm; {'x': 280.8, 'y': 184.4}
* `ac543322-9dae-482f-ae3b-6548d7b25f6d` — Via [+50V] on F.Cu - B.Cu; {'x': 280.4, 'y': 159.8}
* Track/annulus overlap excluding hole: 1.7591 mm².

## 63. track_not_centered_on_via

Offset junction retains positive copper overlap with plated annulus, same net; native clearance and independent continuity pass. Centre alignment is a routing style warning.

* `219d8516-5bf6-4f64-978c-bd0721282652` — Track [ACSOL_B] on F.Cu, length 15.0013 mm; {'x': 424.2, 'y': 30.8}
* `de5e211e-c551-4102-959f-475a4caa0e3b` — Via [ACSOL_B] on F.Cu - B.Cu; {'x': 424.2, 'y': 46.4}
* Track/annulus overlap excluding hole: 1.7430 mm².

## 64. missing_courtyard

H9 is the separate NPTH passage for the BR3/6223BG mounting bolt; its mechanical envelope is reviewed with BR3, not a separately populated component.

* `e509c767-5375-4a3d-a0b9-e32e8abc3088` — Footprint H9; {'x': 251.99, 'y': 23.3}

## 65. npth_inside_courtyard

Intentional BR3 central mounting bolt passage. The NPTH belongs inside the bridge body courtyard and clears electrical copper; verify fastener engagement during assembly.

* `e19a5c74-d067-40c7-925e-b54f16844312` — NPTH pad of H9; {'x': 251.99, 'y': 23.3}
* `bd71bded-e5f9-4d0d-8b2f-f2475ec054a9` — Footprint BR3; {'x': 254.588, 'y': 14.304}
