lolz0r/Williams-WPC-Power-Driver-Board-A-12697-3/variants/jlcpcb/output/release-candidate/reports/verification/DRC_WARNING_REVIEW.md

# Item-specific DRC warning review

105 warnings; 105 accepted under the stated geometry checks. Rules remain enabled.

## 1. track_dangling

Retained routed copper. Native pad connectivity and independent filled-copper topology both pass. Free-ended copper/one-layer vias do not create an open circuit; deleting whole reported segments previously broke necessary intermediate junctions. Physical signal integrity is a first-article check.

* `9b8e3a2e-9b54-4797-bcdf-78d7c9d25637` — Track [+12V] on F.Cu, length 1.4000 mm; {'x': 129.6, 'y': 83.2}

## 2. track_dangling

Retained routed copper. Native pad connectivity and independent filled-copper topology both pass. Free-ended copper/one-layer vias do not create an open circuit; deleting whole reported segments previously broke necessary intermediate junctions. Physical signal integrity is a first-article check.

* `f6080f49-d415-48f4-8dcf-aa2808ebedc7` — Track [+12V] on F.Cu, length 14.4000 mm; {'x': 116.6, 'y': 60.6}

## 3. track_dangling

Retained routed copper. Native pad connectivity and independent filled-copper topology both pass. Free-ended copper/one-layer vias do not create an open circuit; deleting whole reported segments previously broke necessary intermediate junctions. Physical signal integrity is a first-article check.

* `9639c287-f834-4c3b-a24b-99f2fca397b0` — Track [+5V] on F.Cu, length 0.2000 mm; {'x': 170.0, 'y': 168.6}

## 4. track_dangling

Retained routed copper. Native pad connectivity and independent filled-copper topology both pass. Free-ended copper/one-layer vias do not create an open circuit; deleting whole reported segments previously broke necessary intermediate junctions. Physical signal integrity is a first-article check.

* `a978060b-890f-48fc-8dee-e975d2acddec` — Track [+5V] on F.Cu, length 3.0000 mm; {'x': 88.9, 'y': 88.4}

## 5. track_dangling

Retained routed copper. Native pad connectivity and independent filled-copper topology both pass. Free-ended copper/one-layer vias do not create an open circuit; deleting whole reported segments previously broke necessary intermediate junctions. Physical signal integrity is a first-article check.

* `abbbac8a-856f-42fe-be0d-39f5a037b7e2` — Track [+5V] on F.Cu, length 0.2000 mm; {'x': 309.8, 'y': 82.0}

## 6. track_dangling

Retained routed copper. Native pad connectivity and independent filled-copper topology both pass. Free-ended copper/one-layer vias do not create an open circuit; deleting whole reported segments previously broke necessary intermediate junctions. Physical signal integrity is a first-article check.

* `f3ff1f98-5fdf-4e66-9692-892a0637ee77` — Track [+5V] on F.Cu, length 4.0000 mm; {'x': 251.0, 'y': 51.4}

## 7. track_dangling

Retained routed copper. Native pad connectivity and independent filled-copper topology both pass. Free-ended copper/one-layer vias do not create an open circuit; deleting whole reported segments previously broke necessary intermediate junctions. Physical signal integrity is a first-article check.

* `08adae74-6526-484b-9b44-a387424de4e8` — Track [+5V] on B.Cu, length 1.4000 mm; {'x': 161.0, 'y': 52.0}

## 8. track_dangling

Retained routed copper. Native pad connectivity and independent filled-copper topology both pass. Free-ended copper/one-layer vias do not create an open circuit; deleting whole reported segments previously broke necessary intermediate junctions. Physical signal integrity is a first-article check.

* `4c2ee626-dbb6-40bc-a357-ed60a82cbcde` — Track [+5V] on B.Cu, length 18.8000 mm; {'x': 287.0, 'y': 50.4}

## 9. track_dangling

Retained routed copper. Native pad connectivity and independent filled-copper topology both pass. Free-ended copper/one-layer vias do not create an open circuit; deleting whole reported segments previously broke necessary intermediate junctions. Physical signal integrity is a first-article check.

* `6140ebca-2446-4bce-90fa-f81b3cf2b2b8` — Track [+5V] on B.Cu, length 12.6000 mm; {'x': 118.4, 'y': 52.0}

## 10. via_dangling

Retained routed copper. Native pad connectivity and independent filled-copper topology both pass. Free-ended copper/one-layer vias do not create an open circuit; deleting whole reported segments previously broke necessary intermediate junctions. Physical signal integrity is a first-article check.

* `ff61e448-e35a-457d-bab2-7ae319fdc67b` — Via [/Power_Supply/U20_COMP] on F.Cu - B.Cu; {'x': 273.3, 'y': 58.25}

## 11. track_dangling

Retained routed copper. Native pad connectivity and independent filled-copper topology both pass. Free-ended copper/one-layer vias do not create an open circuit; deleting whole reported segments previously broke necessary intermediate junctions. Physical signal integrity is a first-article check.

* `2dcbc53a-4263-446f-a9eb-4f85ca8c93ef` — Track [/Power_Supply/+5V_RAW] on F.Cu, length 20.6000 mm; {'x': 287.0, 'y': 50.8}

## 12. track_dangling

Retained routed copper. Native pad connectivity and independent filled-copper topology both pass. Free-ended copper/one-layer vias do not create an open circuit; deleting whole reported segments previously broke necessary intermediate junctions. Physical signal integrity is a first-article check.

* `93abeda5-4922-4e5a-a6e6-52e60480a164` — Track [+12VU] on F.Cu, length 0.2000 mm; {'x': 211.4, 'y': 185.8}

## 13. track_dangling

Retained routed copper. Native pad connectivity and independent filled-copper topology both pass. Free-ended copper/one-layer vias do not create an open circuit; deleting whole reported segments previously broke necessary intermediate junctions. Physical signal integrity is a first-article check.

* `e925f8c8-409f-4d17-b29c-2952f4e9ae23` — Track [+12VU] on F.Cu, length 10.8000 mm; {'x': 231.0, 'y': 63.8}

## 14. via_dangling

Retained routed copper. Native pad connectivity and independent filled-copper topology both pass. Free-ended copper/one-layer vias do not create an open circuit; deleting whole reported segments previously broke necessary intermediate junctions. Physical signal integrity is a first-article check.

* `1be441c7-936a-412e-affa-c73d860c417b` — Via [BLANKING] on F.Cu - B.Cu; {'x': 20.65, 'y': 92.123}

## 15. track_dangling

Retained routed copper. Native pad connectivity and independent filled-copper topology both pass. Free-ended copper/one-layer vias do not create an open circuit; deleting whole reported segments previously broke necessary intermediate junctions. Physical signal integrity is a first-article check.

* `5aeddb53-b17a-4f81-97d6-62b8f8e24a20` — Track [D5] on F.Cu, length 0.2000 mm; {'x': 133.4, 'y': 93.0}

## 16. track_dangling

Retained routed copper. Native pad connectivity and independent filled-copper topology both pass. Free-ended copper/one-layer vias do not create an open circuit; deleting whole reported segments previously broke necessary intermediate junctions. Physical signal integrity is a first-article check.

* `cb67b306-1b9b-4368-ac8e-c760399f6bf9` — Track [D5] on F.Cu, length 38.4000 mm; {'x': 92.6, 'y': 90.6}

## 17. via_dangling

Retained routed copper. Native pad connectivity and independent filled-copper topology both pass. Free-ended copper/one-layer vias do not create an open circuit; deleting whole reported segments previously broke necessary intermediate junctions. Physical signal integrity is a first-article check.

* `27425720-9613-4cdd-a888-828a3092219f` — Via [D5] on F.Cu - B.Cu; {'x': 252.6, 'y': 119.2}

## 18. track_dangling

Retained routed copper. Native pad connectivity and independent filled-copper topology both pass. Free-ended copper/one-layer vias do not create an open circuit; deleting whole reported segments previously broke necessary intermediate junctions. Physical signal integrity is a first-article check.

* `63b6a001-e71e-4e54-afe0-b2c05d8c0118` — Track [D5] on B.Cu, length 14.0000 mm; {'x': 140.8, 'y': 113.2}

## 19. track_dangling

Retained routed copper. Native pad connectivity and independent filled-copper topology both pass. Free-ended copper/one-layer vias do not create an open circuit; deleting whole reported segments previously broke necessary intermediate junctions. Physical signal integrity is a first-article check.

* `b025ebfd-7fcc-41c7-bb70-01b583afc0f8` — Track [D5] on B.Cu, length 1.2000 mm; {'x': 159.4, 'y': 94.8}

## 20. track_dangling

Retained routed copper. Native pad connectivity and independent filled-copper topology both pass. Free-ended copper/one-layer vias do not create an open circuit; deleting whole reported segments previously broke necessary intermediate junctions. Physical signal integrity is a first-article check.

* `dcf97102-f999-4a53-9715-ada0e540d5cd` — Track [D5] on B.Cu, length 0.8000 mm; {'x': 311.6, 'y': 122.2}

## 21. track_dangling

Retained routed copper. Native pad connectivity and independent filled-copper topology both pass. Free-ended copper/one-layer vias do not create an open circuit; deleting whole reported segments previously broke necessary intermediate junctions. Physical signal integrity is a first-article check.

* `03d73a92-8a7f-4dce-b2a8-967cb5aac4ce` — Track [D7] on F.Cu, length 1.6000 mm; {'x': 187.6, 'y': 98.4}

## 22. track_dangling

Retained routed copper. Native pad connectivity and independent filled-copper topology both pass. Free-ended copper/one-layer vias do not create an open circuit; deleting whole reported segments previously broke necessary intermediate junctions. Physical signal integrity is a first-article check.

* `08c75cc0-cd0f-4a7d-95aa-bfdd46ef10a3` — Track [D7] on F.Cu, length 1.6000 mm; {'x': 319.4, 'y': 128.2}

## 23. track_dangling

Retained routed copper. Native pad connectivity and independent filled-copper topology both pass. Free-ended copper/one-layer vias do not create an open circuit; deleting whole reported segments previously broke necessary intermediate junctions. Physical signal integrity is a first-article check.

* `2439a70c-702d-4c61-be1e-9d269f674ace` — Track [D7] on F.Cu, length 7.8000 mm; {'x': 160.2, 'y': 118.6}

## 24. track_dangling

Retained routed copper. Native pad connectivity and independent filled-copper topology both pass. Free-ended copper/one-layer vias do not create an open circuit; deleting whole reported segments previously broke necessary intermediate junctions. Physical signal integrity is a first-article check.

* `76f4ee02-e28a-4a4f-9f1c-d44961351dea` — Track [D7] on F.Cu, length 4.4000 mm; {'x': 326.2, 'y': 147.4}

## 25. track_dangling

Retained routed copper. Native pad connectivity and independent filled-copper topology both pass. Free-ended copper/one-layer vias do not create an open circuit; deleting whole reported segments previously broke necessary intermediate junctions. Physical signal integrity is a first-article check.

* `9b2b60e0-9832-436e-b8bf-ea2534fba0eb` — Track [D7] on F.Cu, length 1.0000 mm; {'x': 331.8, 'y': 129.0}

## 26. track_dangling

Retained routed copper. Native pad connectivity and independent filled-copper topology both pass. Free-ended copper/one-layer vias do not create an open circuit; deleting whole reported segments previously broke necessary intermediate junctions. Physical signal integrity is a first-article check.

* `b40234fe-857d-4e16-ab5e-3077e0547a66` — Track [D7] on F.Cu, length 1.2000 mm; {'x': 216.8, 'y': 165.0}

## 27. track_dangling

Retained routed copper. Native pad connectivity and independent filled-copper topology both pass. Free-ended copper/one-layer vias do not create an open circuit; deleting whole reported segments previously broke necessary intermediate junctions. Physical signal integrity is a first-article check.

* `bee55847-f9ed-4bdf-8f0f-14470bbc904e` — Track [D7] on F.Cu, length 6.4000 mm; {'x': 326.2, 'y': 140.6}

## 28. track_dangling

Retained routed copper. Native pad connectivity and independent filled-copper topology both pass. Free-ended copper/one-layer vias do not create an open circuit; deleting whole reported segments previously broke necessary intermediate junctions. Physical signal integrity is a first-article check.

* `d41a8b9e-13c8-4b7b-8781-74d364f8005d` — Track [D7] on F.Cu, length 0.8000 mm; {'x': 216.0, 'y': 159.8}

## 29. track_dangling

Retained routed copper. Native pad connectivity and independent filled-copper topology both pass. Free-ended copper/one-layer vias do not create an open circuit; deleting whole reported segments previously broke necessary intermediate junctions. Physical signal integrity is a first-article check.

* `fc92767b-8439-408c-a240-c080e3cf083d` — Track [D7] on F.Cu, length 0.4000 mm; {'x': 329.6, 'y': 119.2}

## 30. via_dangling

Retained routed copper. Native pad connectivity and independent filled-copper topology both pass. Free-ended copper/one-layer vias do not create an open circuit; deleting whole reported segments previously broke necessary intermediate junctions. Physical signal integrity is a first-article check.

* `b4a8dd0a-e45c-4fde-ac7d-0097f16919b2` — Via [D7] on F.Cu - B.Cu; {'x': 352.4, 'y': 144.6}

## 31. track_dangling

Retained routed copper. Native pad connectivity and independent filled-copper topology both pass. Free-ended copper/one-layer vias do not create an open circuit; deleting whole reported segments previously broke necessary intermediate junctions. Physical signal integrity is a first-article check.

* `37215763-4e55-4466-8d7e-514676b7246a` — Track [D7] on B.Cu, length 0.8000 mm; {'x': 222.2, 'y': 112.6}

## 32. track_dangling

Retained routed copper. Native pad connectivity and independent filled-copper topology both pass. Free-ended copper/one-layer vias do not create an open circuit; deleting whole reported segments previously broke necessary intermediate junctions. Physical signal integrity is a first-article check.

* `088d21fc-24ff-4500-b6e5-9b957b4481ac` — Track [D7] on In2.Cu, length 3.8000 mm; {'x': 156.6, 'y': 123.6}

## 33. track_dangling

Retained routed copper. Native pad connectivity and independent filled-copper topology both pass. Free-ended copper/one-layer vias do not create an open circuit; deleting whole reported segments previously broke necessary intermediate junctions. Physical signal integrity is a first-article check.

* `45f65ba9-b42f-4141-a6d7-c38ca27e1337` — Track [D7] on In2.Cu, length 22.0000 mm; {'x': 258.2, 'y': 117.0}

## 34. track_dangling

Retained routed copper. Native pad connectivity and independent filled-copper topology both pass. Free-ended copper/one-layer vias do not create an open circuit; deleting whole reported segments previously broke necessary intermediate junctions. Physical signal integrity is a first-article check.

* `dd84b3ad-cedb-44c1-bbdf-4d92c6ba9e4d` — Track [D7] on In2.Cu, length 1.2000 mm; {'x': 224.6, 'y': 109.2}

## 35. track_dangling

Retained routed copper. Native pad connectivity and independent filled-copper topology both pass. Free-ended copper/one-layer vias do not create an open circuit; deleting whole reported segments previously broke necessary intermediate junctions. Physical signal integrity is a first-article check.

* `dfd9066f-0ac6-4bd7-a81c-2ad53e9886f8` — Track [D7] on In2.Cu, length 0.4000 mm; {'x': 319.4, 'y': 117.0}

## 36. track_dangling

Retained routed copper. Native pad connectivity and independent filled-copper topology both pass. Free-ended copper/one-layer vias do not create an open circuit; deleting whole reported segments previously broke necessary intermediate junctions. Physical signal integrity is a first-article check.

* `93989efc-af2c-4d47-a986-18f637406cbc` — Track [REF_1V4] on B.Cu, length 2.0500 mm; {'x': 160.85, 'y': 68.85}

## 37. via_dangling

Retained routed copper. Native pad connectivity and independent filled-copper topology both pass. Free-ended copper/one-layer vias do not create an open circuit; deleting whole reported segments previously broke necessary intermediate junctions. Physical signal integrity is a first-article check.

* `db2a7870-e3bd-4bbb-b62e-02e851178189` — Via [/Power_Supply/U21_COMP] on F.Cu - B.Cu; {'x': 147.3, 'y': 68.25}

## 38. track_dangling

Retained routed copper. Native pad connectivity and independent filled-copper topology both pass. Free-ended copper/one-layer vias do not create an open circuit; deleting whole reported segments previously broke necessary intermediate junctions. Physical signal integrity is a first-article check.

* `6350babf-f6f7-4d45-9209-b685761e66a4` — Track [D5_N] on F.Cu, length 0.2000 mm; {'x': 11.6, 'y': 105.6}

## 39. via_dangling

Retained routed copper. Native pad connectivity and independent filled-copper topology both pass. Free-ended copper/one-layer vias do not create an open circuit; deleting whole reported segments previously broke necessary intermediate junctions. Physical signal integrity is a first-article check.

* `51e055c2-b2a7-483b-b5a4-918724b051a1` — Via [D5_N] on F.Cu - B.Cu; {'x': 11.6, 'y': 116.2}

## 40. track_dangling

Retained routed copper. Native pad connectivity and independent filled-copper topology both pass. Free-ended copper/one-layer vias do not create an open circuit; deleting whole reported segments previously broke necessary intermediate junctions. Physical signal integrity is a first-article check.

* `d94c3fb0-5615-4b06-b8ab-07cb7c148519` — Track [D5_N] on B.Cu, length 1.4000 mm; {'x': 129.6, 'y': 90.6}

## 41. track_dangling

Retained routed copper. Native pad connectivity and independent filled-copper topology both pass. Free-ended copper/one-layer vias do not create an open circuit; deleting whole reported segments previously broke necessary intermediate junctions. Physical signal integrity is a first-article check.

* `a9091f64-0ba5-41ad-bfc0-7e49603c6092` — Track [+18V] on B.Cu, length 0.6000 mm; {'x': 154.6, 'y': 48.4}

## 42. via_dangling

Retained routed copper. Native pad connectivity and independent filled-copper topology both pass. Free-ended copper/one-layer vias do not create an open circuit; deleting whole reported segments previously broke necessary intermediate junctions. Physical signal integrity is a first-article check.

* `c75a05b0-4ff1-45cd-9813-41952600c621` — Via [COLB4] on F.Cu - B.Cu; {'x': 431.6, 'y': 195.2}

## 43. via_dangling

Retained routed copper. Native pad connectivity and independent filled-copper topology both pass. Free-ended copper/one-layer vias do not create an open circuit; deleting whole reported segments previously broke necessary intermediate junctions. Physical signal integrity is a first-article check.

* `1b21c6f0-1471-4b49-8e01-75636a6acbdf` — Via [/Power_Supply/U21_VCC] on F.Cu - B.Cu; {'x': 146.6, 'y': 65.4}

## 44. track_dangling

Retained routed copper. Native pad connectivity and independent filled-copper topology both pass. Free-ended copper/one-layer vias do not create an open circuit; deleting whole reported segments previously broke necessary intermediate junctions. Physical signal integrity is a first-article check.

* `7653e93c-0193-4cd4-a97d-be877366064b` — Track [+50V] on B.Cu, length 2.5080 mm; {'x': 269.4, 'y': 56.9}

## 45. track_dangling

Retained routed copper. Native pad connectivity and independent filled-copper topology both pass. Free-ended copper/one-layer vias do not create an open circuit; deleting whole reported segments previously broke necessary intermediate junctions. Physical signal integrity is a first-article check.

* `f729025d-db18-4c96-8d0b-8e219623f782` — Track [+50V] on B.Cu, length 1.0000 mm; {'x': 255.0, 'y': 61.4}

## 46. via_dangling

Retained routed copper. Native pad connectivity and independent filled-copper topology both pass. Free-ended copper/one-layer vias do not create an open circuit; deleting whole reported segments previously broke necessary intermediate junctions. Physical signal integrity is a first-article check.

* `a1f8e62e-59c8-43cd-901f-5a05226b0a04` — Via [/Power_Supply/U20_VCC] on F.Cu - B.Cu; {'x': 272.6, 'y': 55.4}

## 47. via_dangling

Retained routed copper. Native pad connectivity and independent filled-copper topology both pass. Free-ended copper/one-layer vias do not create an open circuit; deleting whole reported segments previously broke necessary intermediate junctions. Physical signal integrity is a first-article check.

* `48558390-b774-4cb3-b2ee-3cf8f43bf6e5` — Via [/Power_Supply/U20_BOOT2] on F.Cu - B.Cu; {'x': 273.3, 'y': 62.3}

## 48. via_dangling

Retained routed copper. Native pad connectivity and independent filled-copper topology both pass. Free-ended copper/one-layer vias do not create an open circuit; deleting whole reported segments previously broke necessary intermediate junctions. Physical signal integrity is a first-article check.

* `a110c927-d6dd-409e-8c09-d436b202432d` — Via [CLK_LAMP_COL] on F.Cu - B.Cu; {'x': 239.0, 'y': 151.2}

## 49. track_dangling

Retained routed copper. Native pad connectivity and independent filled-copper topology both pass. Free-ended copper/one-layer vias do not create an open circuit; deleting whole reported segments previously broke necessary intermediate junctions. Physical signal integrity is a first-article check.

* `73bb0f27-0258-420d-b372-94d3d2c9dadd` — Track [SOL26_L] on F.Cu, length 10.8000 mm; {'x': 161.0, 'y': 88.6}

## 50. track_dangling

Retained routed copper. Native pad connectivity and independent filled-copper topology both pass. Free-ended copper/one-layer vias do not create an open circuit; deleting whole reported segments previously broke necessary intermediate junctions. Physical signal integrity is a first-article check.

* `30c23dfc-697a-4116-a9dd-156b9d2fd5dc` — Track [SOL26_L] on In2.Cu, length 26.0000 mm; {'x': 105.0, 'y': 91.4}

## 51. track_dangling

Retained routed copper. Native pad connectivity and independent filled-copper topology both pass. Free-ended copper/one-layer vias do not create an open circuit; deleting whole reported segments previously broke necessary intermediate junctions. Physical signal integrity is a first-article check.

* `870184d0-caef-467f-a033-0c759b690e96` — Track [ROWCLR1] on F.Cu, length 0.2000 mm; {'x': 388.8, 'y': 154.4}

## 52. track_dangling

Retained routed copper. Native pad connectivity and independent filled-copper topology both pass. Free-ended copper/one-layer vias do not create an open circuit; deleting whole reported segments previously broke necessary intermediate junctions. Physical signal integrity is a first-article check.

* `d8d06390-a596-46b2-acf1-17677e3e6174` — Track [ROWCLR1] on F.Cu, length 2.4000 mm; {'x': 394.0, 'y': 140.6}

## 53. track_dangling

Retained routed copper. Native pad connectivity and independent filled-copper topology both pass. Free-ended copper/one-layer vias do not create an open circuit; deleting whole reported segments previously broke necessary intermediate junctions. Physical signal integrity is a first-article check.

* `fee19731-bb21-4abb-80f8-bcb4a1701bc9` — Track [ROWCLR1] on F.Cu, length 0.2000 mm; {'x': 398.6, 'y': 152.6}

## 54. via_dangling

Retained routed copper. Native pad connectivity and independent filled-copper topology both pass. Free-ended copper/one-layer vias do not create an open circuit; deleting whole reported segments previously broke necessary intermediate junctions. Physical signal integrity is a first-article check.

* `c8481b5b-faac-4bdd-ac69-f45fe3f920a2` — Via [ROWCLR1] on F.Cu - B.Cu; {'x': 399.0, 'y': 152.0}

## 55. track_dangling

Retained routed copper. Native pad connectivity and independent filled-copper topology both pass. Free-ended copper/one-layer vias do not create an open circuit; deleting whole reported segments previously broke necessary intermediate junctions. Physical signal integrity is a first-article check.

* `d6d436de-97c4-4888-bc00-edfc77d64ebb` — Track [D1_N] on F.Cu, length 1.1314 mm; {'x': 88.4, 'y': 86.5}

## 56. track_dangling

Retained routed copper. Native pad connectivity and independent filled-copper topology both pass. Free-ended copper/one-layer vias do not create an open circuit; deleting whole reported segments previously broke necessary intermediate junctions. Physical signal integrity is a first-article check.

* `d362e227-6e40-4f91-8e3e-f90202f22c37` — Track [AC9_B] on B.Cu, length 0.2000 mm; {'x': 161.2, 'y': 66.2}

## 57. track_dangling

Retained routed copper. Native pad connectivity and independent filled-copper topology both pass. Free-ended copper/one-layer vias do not create an open circuit; deleting whole reported segments previously broke necessary intermediate junctions. Physical signal integrity is a first-article check.

* `cc960d20-4ed1-4595-a007-3bd12668b12b` — Track [AC13_B] on F.Cu, length 1.1992 mm; {'x': 361.2, 'y': 52.2}

## 58. via_dangling

Retained routed copper. Native pad connectivity and independent filled-copper topology both pass. Free-ended copper/one-layer vias do not create an open circuit; deleting whole reported segments previously broke necessary intermediate junctions. Physical signal integrity is a first-article check.

* `e18529be-e12b-4c47-b9b3-a7f46634abaa` — Via [AC13_B] on F.Cu - B.Cu; {'x': 368.0, 'y': 70.0}

## 59. via_dangling

Retained routed copper. Native pad connectivity and independent filled-copper topology both pass. Free-ended copper/one-layer vias do not create an open circuit; deleting whole reported segments previously broke necessary intermediate junctions. Physical signal integrity is a first-article check.

* `313a91a8-c224-49bc-bc02-22d7baae8354` — Via [SOL12_L] on F.Cu - B.Cu; {'x': 247.4, 'y': 106.6}

## 60. track_dangling

Retained routed copper. Native pad connectivity and independent filled-copper topology both pass. Free-ended copper/one-layer vias do not create an open circuit; deleting whole reported segments previously broke necessary intermediate junctions. Physical signal integrity is a first-article check.

* `28109c98-a1f2-4287-b56b-464eb1ff9504` — Track [/CPU_Interface/ZC_SAMPLE] on B.Cu, length 0.6576 mm; {'x': 140.45, 'y': 71.55}

## 61. track_dangling

Retained routed copper. Native pad connectivity and independent filled-copper topology both pass. Free-ended copper/one-layer vias do not create an open circuit; deleting whole reported segments previously broke necessary intermediate junctions. Physical signal integrity is a first-article check.

* `4ef624e2-5412-4743-9429-d32a3844cb5d` — Track [/CPU_Interface/ZC_SAMPLE] on B.Cu, length 0.2000 mm; {'x': 86.8, 'y': 73.6}

## 62. track_dangling

Retained routed copper. Native pad connectivity and independent filled-copper topology both pass. Free-ended copper/one-layer vias do not create an open circuit; deleting whole reported segments previously broke necessary intermediate junctions. Physical signal integrity is a first-article check.

* `f1c93e23-3765-4888-be5d-1eb1e792406e` — Track [FLIP_RLY_L] on F.Cu, length 1.2000 mm; {'x': 138.4, 'y': 118.6}

## 63. via_dangling

Retained routed copper. Native pad connectivity and independent filled-copper topology both pass. Free-ended copper/one-layer vias do not create an open circuit; deleting whole reported segments previously broke necessary intermediate junctions. Physical signal integrity is a first-article check.

* `346c3a11-f0ff-403c-8085-9b6a1cb6e7cc` — Via [FLIP_RLY_L] on F.Cu - B.Cu; {'x': 103.8, 'y': 54.0}

## 64. track_dangling

Retained routed copper. Native pad connectivity and independent filled-copper topology both pass. Free-ended copper/one-layer vias do not create an open circuit; deleting whole reported segments previously broke necessary intermediate junctions. Physical signal integrity is a first-article check.

* `25291b1f-6800-4ef8-b322-99cf8d6bd02b` — Track [FLIP_RLY_L] on In2.Cu, length 16.0000 mm; {'x': 115.0, 'y': 74.0}

## 65. track_dangling

Retained routed copper. Native pad connectivity and independent filled-copper topology both pass. Free-ended copper/one-layer vias do not create an open circuit; deleting whole reported segments previously broke necessary intermediate junctions. Physical signal integrity is a first-article check.

* `2c12181d-7202-4065-af89-a4cc37c96db6` — Track [FLIP_RLY_L] on In2.Cu, length 6.6000 mm; {'x': 152.0, 'y': 93.0}

## 66. track_dangling

Retained routed copper. Native pad connectivity and independent filled-copper topology both pass. Free-ended copper/one-layer vias do not create an open circuit; deleting whole reported segments previously broke necessary intermediate junctions. Physical signal integrity is a first-article check.

* `791c816e-67ca-44f0-b056-2fe54e5ecebe` — Track [AC9_AF] on F.Cu, length 2.4000 mm; {'x': 255.0, 'y': 49.0}

## 67. via_dangling

Retained routed copper. Native pad connectivity and independent filled-copper topology both pass. Free-ended copper/one-layer vias do not create an open circuit; deleting whole reported segments previously broke necessary intermediate junctions. Physical signal integrity is a first-article check.

* `6079b46f-1f26-4e5f-889c-7645bb891e6a` — Via [CLK_SOL_HIGH] on F.Cu - B.Cu; {'x': 20.65, 'y': 102.283}

## 68. via_dangling

Retained routed copper. Native pad connectivity and independent filled-copper topology both pass. Free-ended copper/one-layer vias do not create an open circuit; deleting whole reported segments previously broke necessary intermediate junctions. Physical signal integrity is a first-article check.

* `b506e93b-53de-43ca-926d-7d8917bf2ac8` — Via [SOL06] on F.Cu - B.Cu; {'x': 277.8, 'y': 181.4}

## 69. track_dangling

Retained routed copper. Native pad connectivity and independent filled-copper topology both pass. Free-ended copper/one-layer vias do not create an open circuit; deleting whole reported segments previously broke necessary intermediate junctions. Physical signal integrity is a first-article check.

* `3ff19862-abde-4bc4-83c2-eb46af91d72a` — Track [D3_N] on F.Cu, length 0.4000 mm; {'x': 234.6, 'y': 119.8}

## 70. track_dangling

Retained routed copper. Native pad connectivity and independent filled-copper topology both pass. Free-ended copper/one-layer vias do not create an open circuit; deleting whole reported segments previously broke necessary intermediate junctions. Physical signal integrity is a first-article check.

* `aa4b540d-bd8e-4b96-b0b3-5468a36e7063` — Track [D3_N] on F.Cu, length 3.4000 mm; {'x': 14.0, 'y': 100.8}

## 71. via_dangling

Retained routed copper. Native pad connectivity and independent filled-copper topology both pass. Free-ended copper/one-layer vias do not create an open circuit; deleting whole reported segments previously broke necessary intermediate junctions. Physical signal integrity is a first-article check.

* `0c6c9bb0-8add-4715-8eae-f00236e658cf` — Via [D3_N] on F.Cu - B.Cu; {'x': 93.8, 'y': 94.8}

## 72. track_dangling

Retained routed copper. Native pad connectivity and independent filled-copper topology both pass. Free-ended copper/one-layer vias do not create an open circuit; deleting whole reported segments previously broke necessary intermediate junctions. Physical signal integrity is a first-article check.

* `3425debb-f540-4b81-9aae-e85d185ede7b` — Track [D3_N] on In2.Cu, length 0.2000 mm; {'x': 222.8, 'y': 116.6}

## 73. track_dangling

Retained routed copper. Native pad connectivity and independent filled-copper topology both pass. Free-ended copper/one-layer vias do not create an open circuit; deleting whole reported segments previously broke necessary intermediate junctions. Physical signal integrity is a first-article check.

* `6b79e6d0-f84e-4450-ae67-ec0313fb57cf` — Track [D3_N] on In2.Cu, length 1.8000 mm; {'x': 17.4, 'y': 107.0}

## 74. track_dangling

Retained routed copper. Native pad connectivity and independent filled-copper topology both pass. Free-ended copper/one-layer vias do not create an open circuit; deleting whole reported segments previously broke necessary intermediate junctions. Physical signal integrity is a first-article check.

* `bfd1ff62-9d4b-4bc2-a51e-56416711ccb1` — Track [D3_N] on In2.Cu, length 1.4000 mm; {'x': 233.4, 'y': 117.2}

## 75. track_dangling

Retained routed copper. Native pad connectivity and independent filled-copper topology both pass. Free-ended copper/one-layer vias do not create an open circuit; deleting whole reported segments previously broke necessary intermediate junctions. Physical signal integrity is a first-article check.

* `478b1a9a-5769-42c5-b7b6-01384c163d5a` — Track [AC16_A] on F.Cu, length 3.6000 mm; {'x': 374.6, 'y': 61.4}

## 76. track_dangling

Retained routed copper. Native pad connectivity and independent filled-copper topology both pass. Free-ended copper/one-layer vias do not create an open circuit; deleting whole reported segments previously broke necessary intermediate junctions. Physical signal integrity is a first-article check.

* `cc83e031-7b3c-4b53-9eed-05952293b926` — Track [D6_N] on F.Cu, length 0.6000 mm; {'x': 8.6, 'y': 107.6}

## 77. track_dangling

Retained routed copper. Native pad connectivity and independent filled-copper topology both pass. Free-ended copper/one-layer vias do not create an open circuit; deleting whole reported segments previously broke necessary intermediate junctions. Physical signal integrity is a first-article check.

* `ed9434b5-c4e3-48b0-8b1b-adc140e9f48f` — Track [D6_N] on F.Cu, length 0.8246 mm; {'x': 9.6, 'y': 103.0}

## 78. via_dangling

Retained routed copper. Native pad connectivity and independent filled-copper topology both pass. Free-ended copper/one-layer vias do not create an open circuit; deleting whole reported segments previously broke necessary intermediate junctions. Physical signal integrity is a first-article check.

* `0b33145a-4d11-4a51-a696-56ac345c38e1` — Via [D6_N] on F.Cu - B.Cu; {'x': 12.8, 'y': 88.0}

## 79. track_dangling

Retained routed copper. Native pad connectivity and independent filled-copper topology both pass. Free-ended copper/one-layer vias do not create an open circuit; deleting whole reported segments previously broke necessary intermediate junctions. Physical signal integrity is a first-article check.

* `5c37887d-eb69-464b-9ac7-9e89caf83a31` — Track [D6_N] on B.Cu, length 0.2000 mm; {'x': 13.6, 'y': 97.2}

## 80. track_dangling

Retained routed copper. Native pad connectivity and independent filled-copper topology both pass. Free-ended copper/one-layer vias do not create an open circuit; deleting whole reported segments previously broke necessary intermediate junctions. Physical signal integrity is a first-article check.

* `ab22f8fb-2af5-4ba5-9146-67d450a85107` — Track [D6_N] on B.Cu, length 1.2000 mm; {'x': 14.0, 'y': 95.4}

## 81. track_dangling

Retained routed copper. Native pad connectivity and independent filled-copper topology both pass. Free-ended copper/one-layer vias do not create an open circuit; deleting whole reported segments previously broke necessary intermediate junctions. Physical signal integrity is a first-article check.

* `f980a3c8-ee95-43ca-8f74-a1a809162adc` — Track [D6_N] on B.Cu, length 1.6000 mm; {'x': 10.4, 'y': 98.2}

## 82. track_dangling

Retained routed copper. Native pad connectivity and independent filled-copper topology both pass. Free-ended copper/one-layer vias do not create an open circuit; deleting whole reported segments previously broke necessary intermediate junctions. Physical signal integrity is a first-article check.

* `58b2817b-3eb5-4a27-a0b4-7e92b304c0a7` — Track [D6_N] on In2.Cu, length 13.0000 mm; {'x': 321.8, 'y': 102.8}

## 83. via_dangling

Retained routed copper. Native pad connectivity and independent filled-copper topology both pass. Free-ended copper/one-layer vias do not create an open circuit; deleting whole reported segments previously broke necessary intermediate junctions. Physical signal integrity is a first-article check.

* `3f46cd25-1573-4300-aa6a-a9ebfc364f77` — Via [D0_N] on F.Cu - B.Cu; {'x': 15.48, 'y': 100.263}

## 84. track_dangling

Retained routed copper. Native pad connectivity and independent filled-copper topology both pass. Free-ended copper/one-layer vias do not create an open circuit; deleting whole reported segments previously broke necessary intermediate junctions. Physical signal integrity is a first-article check.

* `4c61b0f3-aa47-40eb-83bc-188fbbeb2dd5` — Track [COLB2] on F.Cu, length 0.8000 mm; {'x': 424.2, 'y': 177.6}

## 85. via_dangling

Retained routed copper. Native pad connectivity and independent filled-copper topology both pass. Free-ended copper/one-layer vias do not create an open circuit; deleting whole reported segments previously broke necessary intermediate junctions. Physical signal integrity is a first-article check.

* `50fc9069-8824-4834-94d1-2a4f0dcf92fe` — Via [COLB2] on F.Cu - B.Cu; {'x': 424.2, 'y': 202.6}

## 86. track_not_centered_on_via

Offset junction retains positive copper overlap with plated annulus, same net; native clearance and independent continuity pass. Centre alignment is a routing style warning.

* `0e333a20-7854-4073-ba61-a02d680080bf` — Track [+20V] on F.Cu, length 1.3000 mm; {'x': 288.4, 'y': 17.0}
* `a6d64888-6283-4476-9884-b3d2e83e4eed` — Via [+20V] on F.Cu - B.Cu; {'x': 289.0, 'y': 17.0}
* Track/annulus overlap excluding hole: 0.0584 mm².

## 87. track_not_centered_on_via

Offset junction retains positive copper overlap with plated annulus, same net; native clearance and independent continuity pass. Centre alignment is a routing style warning.

* `a3f64980-c39a-496b-9301-6bf7de4c485f` — Track [+20V] on F.Cu, length 0.2000 mm; {'x': 288.7, 'y': 9.5}
* `75f356bc-3c01-427c-846d-315abb866a93` — Via [+20V] on F.Cu - B.Cu; {'x': 289.0, 'y': 9.0}
* Track/annulus overlap excluding hole: 0.0657 mm².

## 88. track_not_centered_on_via

Offset junction retains positive copper overlap with plated annulus, same net; native clearance and independent continuity pass. Centre alignment is a routing style warning.

* `4fed27d3-3164-4c89-a1db-92576100a648` — Track [+20V] on In2.Cu, length 11.2446 mm; {'x': 164.4, 'y': 234.4}
* `720ce0cd-78bd-44c3-ac45-19da835c702f` — Via [+20V] on F.Cu - B.Cu; {'x': 176.0, 'y': 236.2}
* Track/annulus overlap excluding hole: 0.0691 mm².

## 89. track_not_centered_on_via

Offset junction retains positive copper overlap with plated annulus, same net; native clearance and independent continuity pass. Centre alignment is a routing style warning.

* `67f557c0-9d78-43cf-951e-a3482b303db6` — Track [+20V] on In2.Cu, length 11.4000 mm; {'x': 204.2, 'y': 183.8}
* `d825953a-83c7-471f-bd63-8f64f075caa6` — Via [+20V] on F.Cu - B.Cu; {'x': 216.4, 'y': 184.2}
* Track/annulus overlap excluding hole: 0.0624 mm².

## 90. track_not_centered_on_via

Offset junction retains positive copper overlap with plated annulus, same net; native clearance and independent continuity pass. Centre alignment is a routing style warning.

* `01547335-f3d4-4e72-aa25-708f1860745c` — Track [+5V] on B.Cu, length 1.1662 mm; {'x': 16.7, 'y': 101.8}
* `5101d298-2812-498e-a718-1698caedad32` — Via [+5V] on F.Cu - B.Cu; {'x': 15.48, 'y': 102.803}
* Track/annulus overlap excluding hole: 0.0746 mm².

## 91. track_not_centered_on_via

Offset junction retains positive copper overlap with plated annulus, same net; native clearance and independent continuity pass. Centre alignment is a routing style warning.

* `4fff633c-23fd-46e9-8dd0-45941e02dc41` — Track [+5V] on B.Cu, length 1.1662 mm; {'x': 16.7, 'y': 101.8}
* `5101d298-2812-498e-a718-1698caedad32` — Via [+5V] on F.Cu - B.Cu; {'x': 15.48, 'y': 102.803}
* Track/annulus overlap excluding hole: 0.0746 mm².

## 92. track_not_centered_on_via

Offset junction retains positive copper overlap with plated annulus, same net; native clearance and independent continuity pass. Centre alignment is a routing style warning.

* `f312f4e8-b0c1-4d37-9c25-1ba853fc083a` — Track [GND] on In2.Cu, length 3.8659 mm; {'x': 265.35, 'y': 57.95}
* `425ad0e0-ec9d-4999-973c-d110e4919019` — Via [GND] on F.Cu - B.Cu; {'x': 264.725, 'y': 54.0}
* Track/annulus overlap excluding hole: 0.0270 mm².

## 93. track_not_centered_on_via

Offset junction retains positive copper overlap with plated annulus, same net; native clearance and independent continuity pass. Centre alignment is a routing style warning.

* `888a35db-ee46-49c3-91dd-95b6a5cd5be5` — Track [D3] on B.Cu, length 22.4009 mm; {'x': 302.6, 'y': 118.4}
* `d2cc7d8a-ec9a-465c-b31d-5ec70fe0e329` — Via [D3] on F.Cu - B.Cu; {'x': 303.0, 'y': 118.6}
* Track/annulus overlap excluding hole: 0.1160 mm².

## 94. track_not_centered_on_via

Offset junction retains positive copper overlap with plated annulus, same net; native clearance and independent continuity pass. Centre alignment is a routing style warning.

* `8f8dd6ab-ea15-4c3b-9071-b00f1990e5d7` — Track [D5] on F.Cu, length 1.6000 mm; {'x': 182.0, 'y': 109.4}
* `e18c2ed4-6811-45d5-8f82-df064a0a7b67` — Via [D5] on F.Cu - B.Cu; {'x': 182.1, 'y': 109.6}
* Track/annulus overlap excluding hole: 0.1425 mm².

## 95. track_not_centered_on_via

Offset junction retains positive copper overlap with plated annulus, same net; native clearance and independent continuity pass. Centre alignment is a routing style warning.

* `96f50a08-2fae-46b7-8696-8e5510a10508` — Track [D5] on F.Cu, length 1.6000 mm; {'x': 182.0, 'y': 107.8}
* `e18c2ed4-6811-45d5-8f82-df064a0a7b67` — Via [D5] on F.Cu - B.Cu; {'x': 182.1, 'y': 109.6}
* Track/annulus overlap excluding hole: 0.0842 mm².

## 96. track_not_centered_on_via

Offset junction retains positive copper overlap with plated annulus, same net; native clearance and independent continuity pass. Centre alignment is a routing style warning.

* `4111376b-6bbf-4d37-b33e-27787e8c17c1` — Track [D5] on B.Cu, length 20.0010 mm; {'x': 280.6, 'y': 122.0}
* `b2725d89-97a1-4c8f-8860-b6831f17f1cd` — Via [D5] on F.Cu - B.Cu; {'x': 280.2, 'y': 122.2}
* Track/annulus overlap excluding hole: 0.1160 mm².

## 97. track_not_centered_on_via

Offset junction retains positive copper overlap with plated annulus, same net; native clearance and independent continuity pass. Centre alignment is a routing style warning.

* `8d9d3dc9-cea0-44f2-916e-8e313dae8d84` — Track [D5] on In2.Cu, length 9.2000 mm; {'x': 173.0, 'y': 109.8}
* `e18c2ed4-6811-45d5-8f82-df064a0a7b67` — Via [D5] on F.Cu - B.Cu; {'x': 182.1, 'y': 109.6}
* Track/annulus overlap excluding hole: 0.1425 mm².

## 98. track_not_centered_on_via

Offset junction retains positive copper overlap with plated annulus, same net; native clearance and independent continuity pass. Centre alignment is a routing style warning.

* `dedf13f7-574f-4921-88fe-58141418013b` — Track [D5] on In2.Cu, length 0.6000 mm; {'x': 182.2, 'y': 109.2}
* `e18c2ed4-6811-45d5-8f82-df064a0a7b67` — Via [D5] on F.Cu - B.Cu; {'x': 182.1, 'y': 109.6}
* Track/annulus overlap excluding hole: 0.1837 mm².

## 99. track_not_centered_on_via

Offset junction retains positive copper overlap with plated annulus, same net; native clearance and independent continuity pass. Centre alignment is a routing style warning.

* `379aeea3-d21a-40d8-9ec1-a010d2215ea9` — Track [CLK_SOL_FLASH] on In2.Cu, length 6.4938 mm; {'x': 37.95, 'y': 92.65}
* `29d051bd-f1ee-4a44-a431-c0928f25e5d8` — Via [CLK_SOL_FLASH] on F.Cu - B.Cu; {'x': 44.7, 'y': 94.1}
* Track/annulus overlap excluding hole: 0.0600 mm².

## 100. track_not_centered_on_via

Offset junction retains positive copper overlap with plated annulus, same net; native clearance and independent continuity pass. Centre alignment is a routing style warning.

* `8b4e9cfd-3223-4e9e-aa26-6cd585c0dfab` — Track [+50V] on F.Cu, length 13.6000 mm; {'x': 254.4, 'y': 41.8}
* `a5e97a77-17b9-42c9-9141-17caa7d4d5f6` — Via [+50V] on F.Cu - B.Cu; {'x': 254.0, 'y': 42.4}
* Track/annulus overlap excluding hole: 1.6503 mm².

## 101. track_not_centered_on_via

Offset junction retains positive copper overlap with plated annulus, same net; native clearance and independent continuity pass. Centre alignment is a routing style warning.

* `b8200722-0399-495c-871e-cc9b9cf643f4` — Track [+50V] on B.Cu, length 14.6000 mm; {'x': 280.8, 'y': 160.6}
* `ac543322-9dae-482f-ae3b-6548d7b25f6d` — Via [+50V] on F.Cu - B.Cu; {'x': 280.4, 'y': 159.8}
* Track/annulus overlap excluding hole: 1.3916 mm².

## 102. track_not_centered_on_via

Offset junction retains positive copper overlap with plated annulus, same net; native clearance and independent continuity pass. Centre alignment is a routing style warning.

* `ba97cc34-a2c4-4c20-82b1-28c35e55fd3f` — Track [+50V] on B.Cu, length 24.6000 mm; {'x': 280.8, 'y': 184.4}
* `ac543322-9dae-482f-ae3b-6548d7b25f6d` — Via [+50V] on F.Cu - B.Cu; {'x': 280.4, 'y': 159.8}
* Track/annulus overlap excluding hole: 1.7591 mm².

## 103. track_not_centered_on_via

Offset junction retains positive copper overlap with plated annulus, same net; native clearance and independent continuity pass. Centre alignment is a routing style warning.

* `219d8516-5bf6-4f64-978c-bd0721282652` — Track [ACSOL_B] on F.Cu, length 15.0013 mm; {'x': 424.2, 'y': 30.8}
* `de5e211e-c551-4102-959f-475a4caa0e3b` — Via [ACSOL_B] on F.Cu - B.Cu; {'x': 424.2, 'y': 46.4}
* Track/annulus overlap excluding hole: 1.7430 mm².

## 104. missing_courtyard

H9 is the separate NPTH passage for the BR3/6223BG mounting bolt; its mechanical envelope is reviewed with BR3, not a separately populated component.

* `e509c767-5375-4a3d-a0b9-e32e8abc3088` — Footprint H9; {'x': 251.99, 'y': 23.3}

## 105. npth_inside_courtyard

Intentional BR3 central mounting bolt passage. The NPTH belongs inside the bridge body courtyard and clears electrical copper; verify fastener engagement during assembly.

* `e19a5c74-d067-40c7-925e-b54f16844312` — NPTH pad of H9; {'x': 251.99, 'y': 23.3}
* `bd71bded-e5f9-4d0d-8b2f-f2475ec054a9` — Footprint BR3; {'x': 254.588, 'y': 14.304}
