lolz0r/Williams-WPC-Power-Driver-Board-A-12697-3/variants/jlcpcb-100/tools/verification-requirements.txt

aiofiles==25.1.0
blinker==1.9.0
cadquery==2.3.0
cadquery-ocp==7.9.3.1.1
cadquery-ocp-proxy==7.9.3.1.1
click==8.5.0
contourpy==1.3.3
cycler==0.12.1
Flask==3.1.3
fonttools==4.64.0
gerbonara==1.6.3
h11==0.16.0
h2==4.4.1
hpack==4.2.0
Hypercorn==0.18.0
hyperframe==6.1.0
itsdangerous==2.2.0
Jinja2==3.1.6
kiwisolver==1.5.1
MarkupSafe==3.0.3
matplotlib==3.11.1
numpy==2.5.3
packaging==26.3
pillow==12.3.0
priority==2.0.0
pymupdf==1.28.2
pyparsing==3.3.2
python-dateutil==2.9.0.post0
Quart==0.23.1
rtree==1.4.1
scipy==1.18.1
shapely==2.1.2
six==1.17.0
vtk==9.6.2
Werkzeug==3.1.8
wsproto==1.3.2
