lolz0r/Williams-WPC-Power-Driver-Board-A-12697-3/variants/jlcpcb/output/verification/mame/diagnostics/actions.csv

35 | Begin test/Enter | 1
35.2 | Begin test/Enter | 0
38 | Begin test/Enter | 1
38.2 | Begin test/Enter | 0
41 | Begin test/Enter | 1
41.2 | Begin test/Enter | 0
44 | Begin test/Enter | 1
44.2 | Begin test/Enter | 0
47 | Volume Up/Up | 1
47.2 | Volume Up/Up | 0
50 | Volume Up/Up | 1
50.2 | Volume Up/Up | 0
53 | Begin test/Enter | 1
53.2 | Begin test/Enter | 0
56 | Volume Up/Up | 1
56.2 | Volume Up/Up | 0
59 | Volume Up/Up | 1
59.2 | Volume Up/Up | 0
62 | Volume Up/Up | 1
62.2 | Volume Up/Up | 0
68 | Begin test/Enter | 1
68.2 | Begin test/Enter | 0
74 | Volume Up/Up | 1
74.2 | Volume Up/Up | 0
77 | Volume Up/Up | 1
77.2 | Volume Up/Up | 0
80 | Volume Up/Up | 1
80.2 | Volume Up/Up | 0
83 | Volume Up/Up | 1
83.2 | Volume Up/Up | 0
86 | Volume Up/Up | 1
86.2 | Volume Up/Up | 0
89 | Volume Up/Up | 1
89.2 | Volume Up/Up | 0
92 | Volume Up/Up | 1
92.2 | Volume Up/Up | 0
95 | Volume Up/Up | 1
95.2 | Volume Up/Up | 0
98 | Volume Up/Up | 1
98.2 | Volume Up/Up | 0
101 | Volume Up/Up | 1
101.2 | Volume Up/Up | 0
104 | Volume Up/Up | 1
104.2 | Volume Up/Up | 0
107 | Volume Up/Up | 1
107.2 | Volume Up/Up | 0
110 | Volume Up/Up | 1
110.2 | Volume Up/Up | 0
113 | Volume Up/Up | 1
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
