lolz0r/Williams-WPC-Power-Driver-Board-A-12697-3/output/verification/pinmame/gameplay/solenoids.csv

audio_time | solenoid | state
3.766667 | 29 | 1
3.833333 | 2 | 1
4.166667 | 2 | 0
4.233333 | 1 | 1
4.633333 | 1 | 0
8.066667 | 29 | 1
11.200000 | 29 | 0
11.333333 | 29 | 1
11.400000 | 17 | 1
11.400000 | 18 | 1
11.533333 | 2 | 1
11.933333 | 1 | 1
11.933333 | 2 | 0
12.266667 | 1 | 0
12.383333 | 54 | 1
12.450000 | 54 | 0
13.133333 | 11 | 1
13.200000 | 11 | 0
13.800000 | 6 | 1
13.933333 | 6 | 0
17.033333 | 51 | 1
17.233333 | 51 | 0
17.283333 | 51 | 1
17.350000 | 51 | 0
17.533333 | 51 | 1
17.583333 | 51 | 0
17.766667 | 51 | 1
17.833333 | 51 | 0
18.016667 | 51 | 1
18.066667 | 17 | 0
18.066667 | 51 | 0
18.133333 | 18 | 0
18.250000 | 51 | 1
18.300000 | 51 | 0
18.500000 | 51 | 1
18.550000 | 51 | 0
18.733333 | 51 | 1
18.766667 | 51 | 0
19.266667 | 11 | 1
19.400000 | 11 | 0
19.933333 | 6 | 1
20.066667 | 6 | 0
23.150000 | 52 | 1
23.383333 | 52 | 0
23.566667 | 52 | 1
23.616667 | 52 | 0
23.800000 | 52 | 1
23.866667 | 52 | 0
24.050000 | 52 | 1
24.100000 | 52 | 0
24.283333 | 52 | 1
24.350000 | 52 | 0
24.533333 | 52 | 1
24.583333 | 52 | 0
24.766667 | 52 | 1
24.833333 | 52 | 0
25.666667 | 11 | 1
25.733333 | 11 | 0
26.333333 | 6 | 1
26.466667 | 6 | 0
40.066667 | 29 | 0
40.600000 | 31 | 1
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
