lolz0r/Williams-WPC-Power-Driver-Board-A-12697-3/output/verification/revision/loop/bode.png

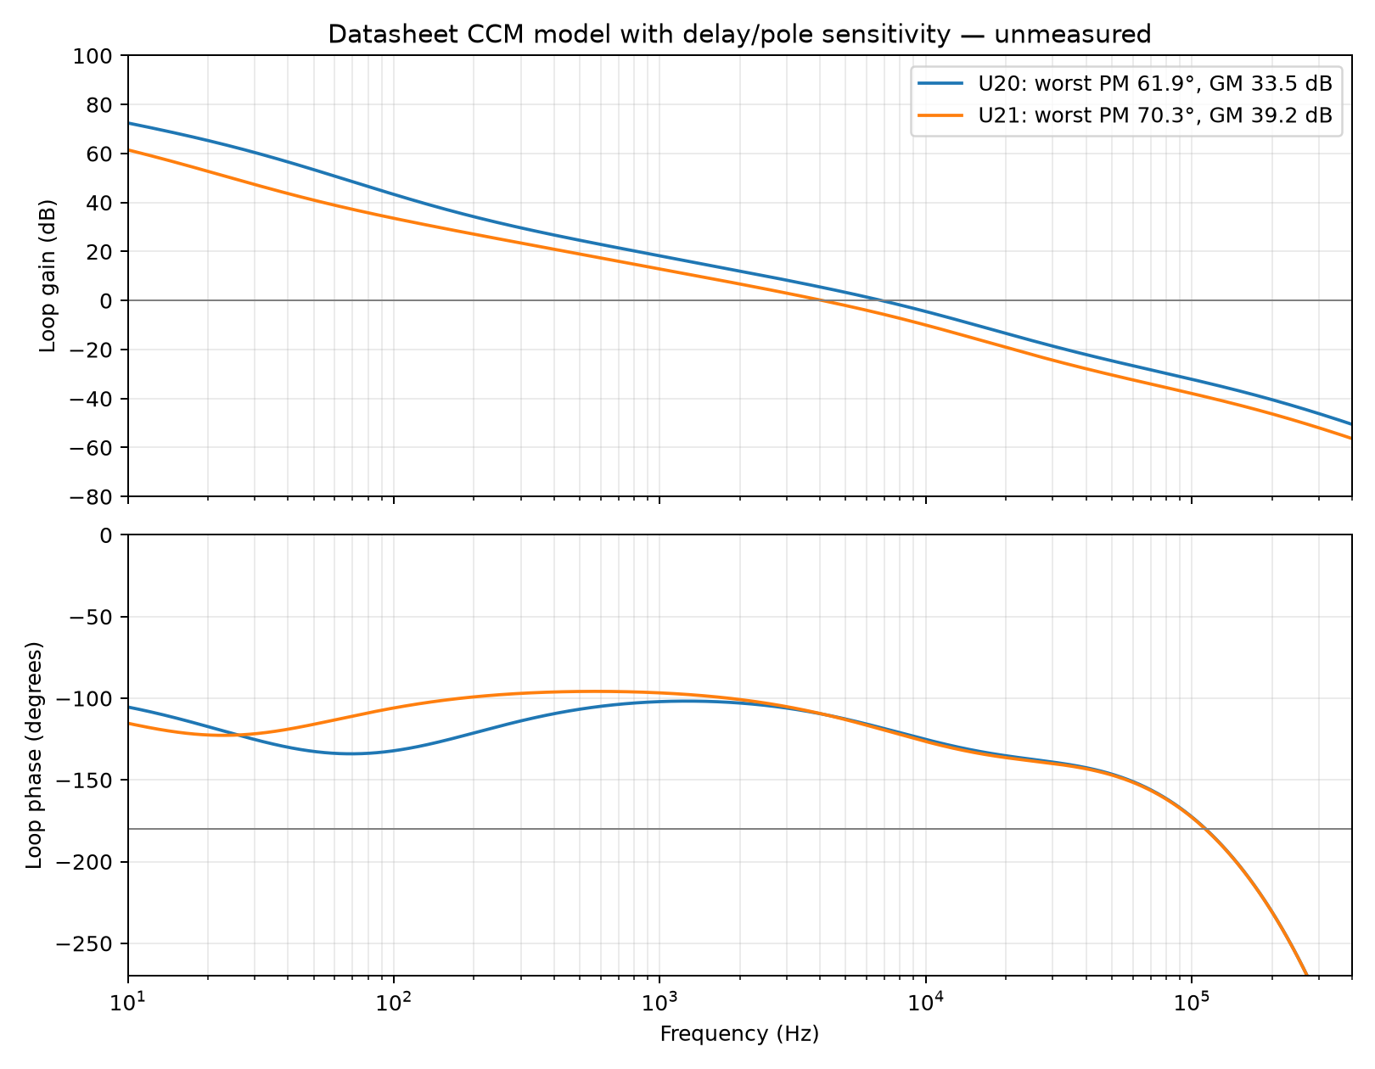
output/verification/revision/loop/bode.png
