lolz0r/Williams-WPC-Power-Driver-Board-A-12697-3/variants/jlcpcb/output/release-candidate/schematic/schematic.pdf

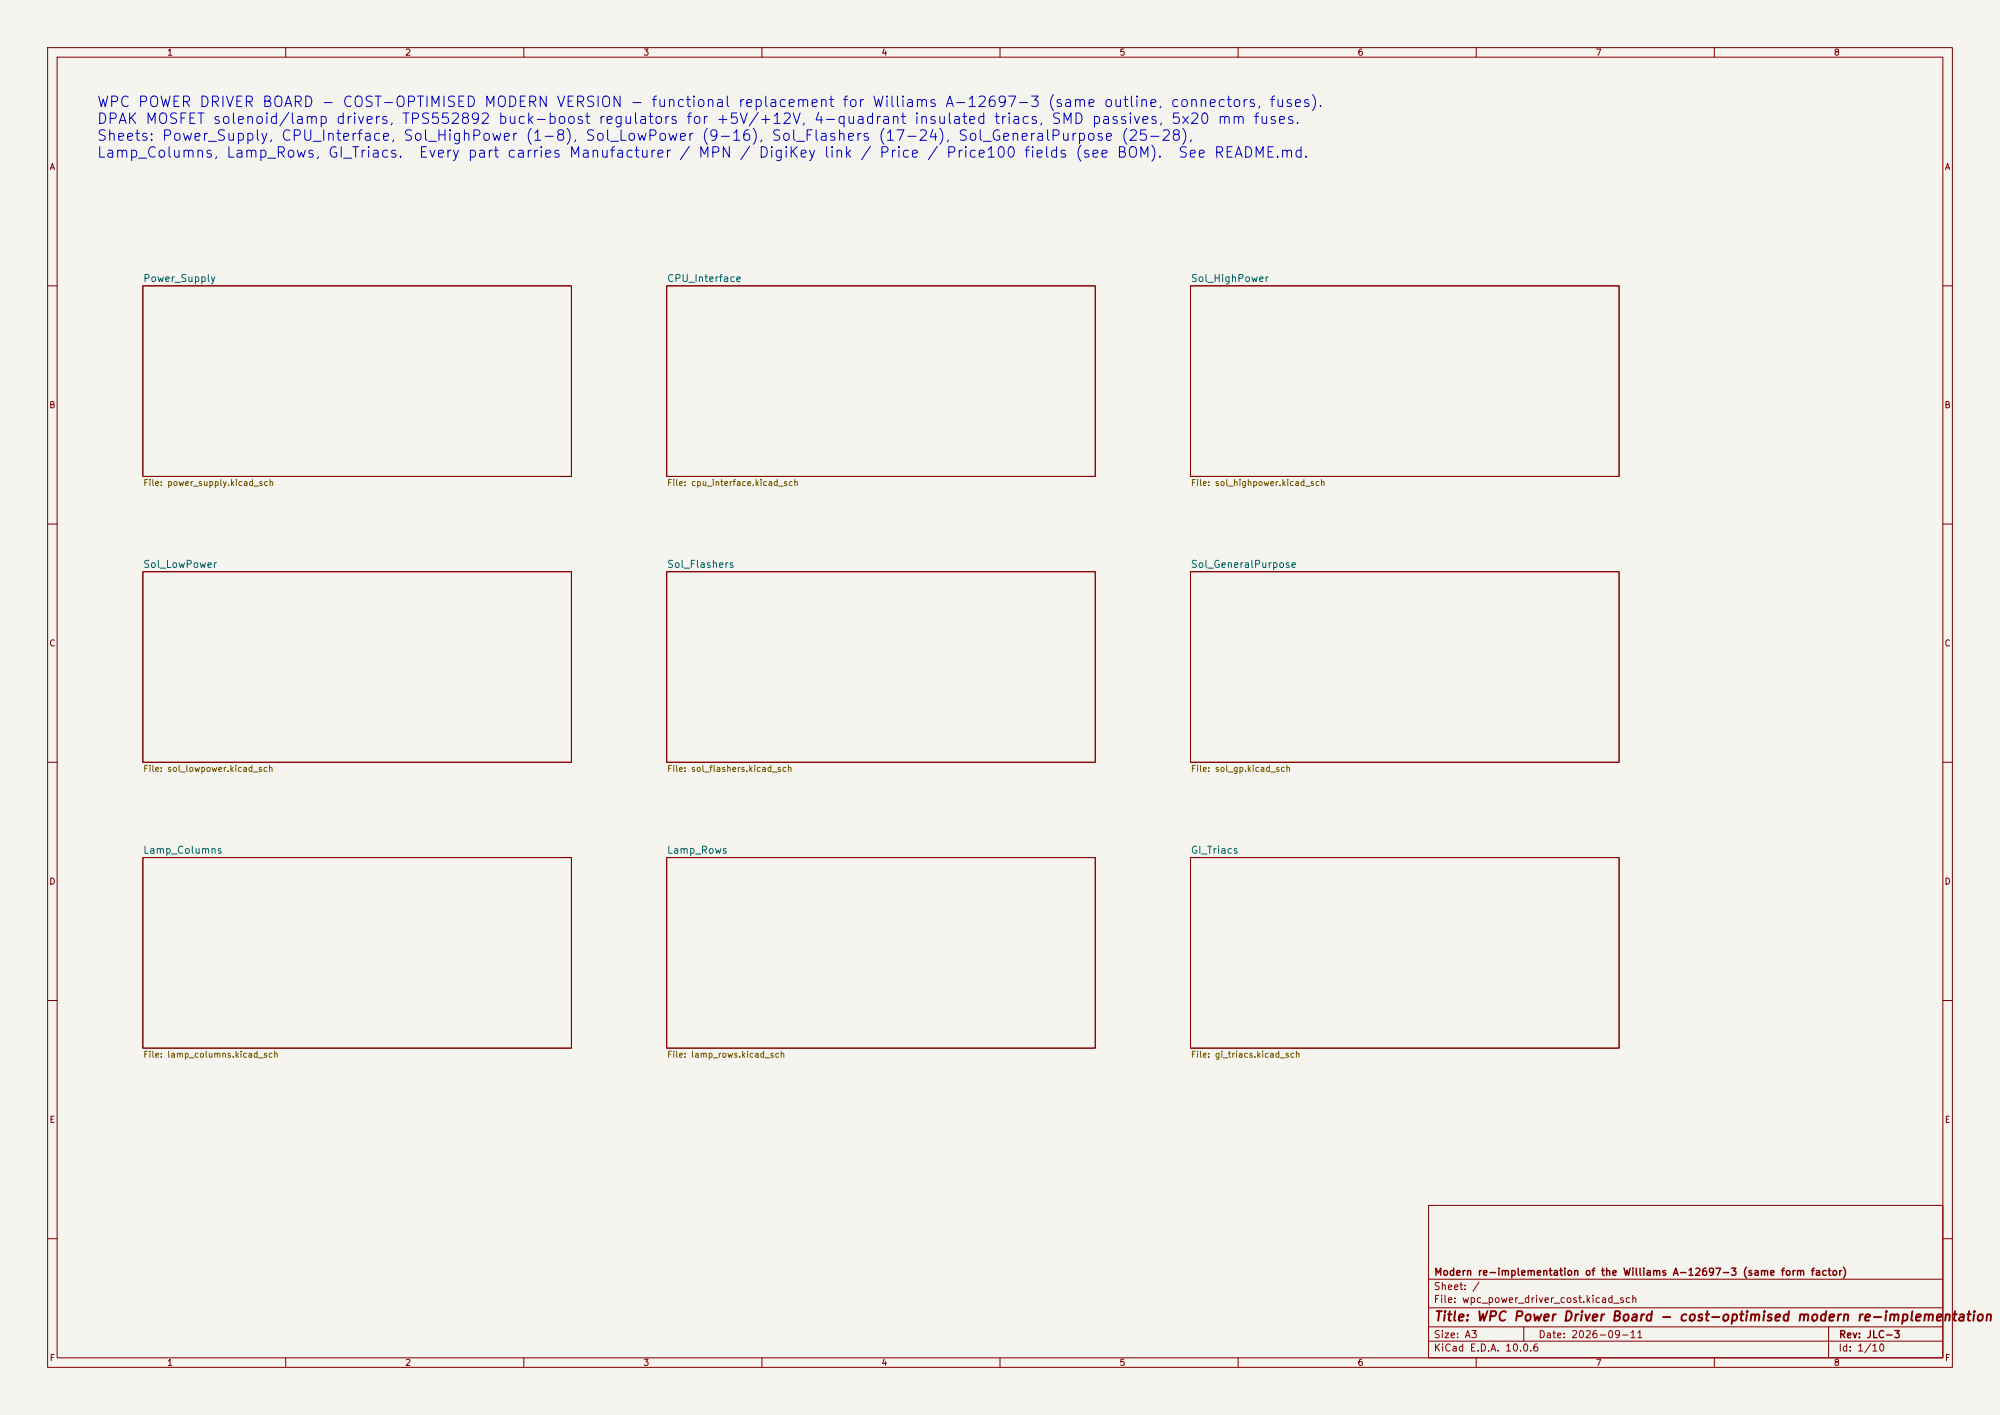
[picture p131: page 1]

WPC POWER DRIVER BOARD - COST-OPTIMISED MODERN VERSION - functional replacement for Williams A-12697-3 (same outline, connectors, fuses).
DPAK MOSFET solenoid/lamp drivers, TPS552892 buck-boost regulators for +5V/+12V, 4-quadrant insulated triacs, SMD passives, 5x20 mm fuses.
Sheets: Power_Supply, CPU_Interface, Sol_HighPower (1-8), Sol_LowPower (9-16), Sol_Flashers (17-24), Sol_GeneralPurpose (25-28),
Lamp_Columns, Lamp_Rows, GI_Triacs. Every part carries Manufacturer / MPN / DigiKey link / Price / Price100 fields (see BOM). See README.md.

Modern re-implementation of the Williams A-12697-3 (same form factor)
Sheet: /
File: wpc_power_driver_cost.kicad_sch
Title: WPC Power Driver Board - cost-optimised modern re-implementation

Size: A3 | Rev: JLC-3 | F Date: 2026-09-11
KiCad E.D.A. 10.0.6 | Id: 1/10

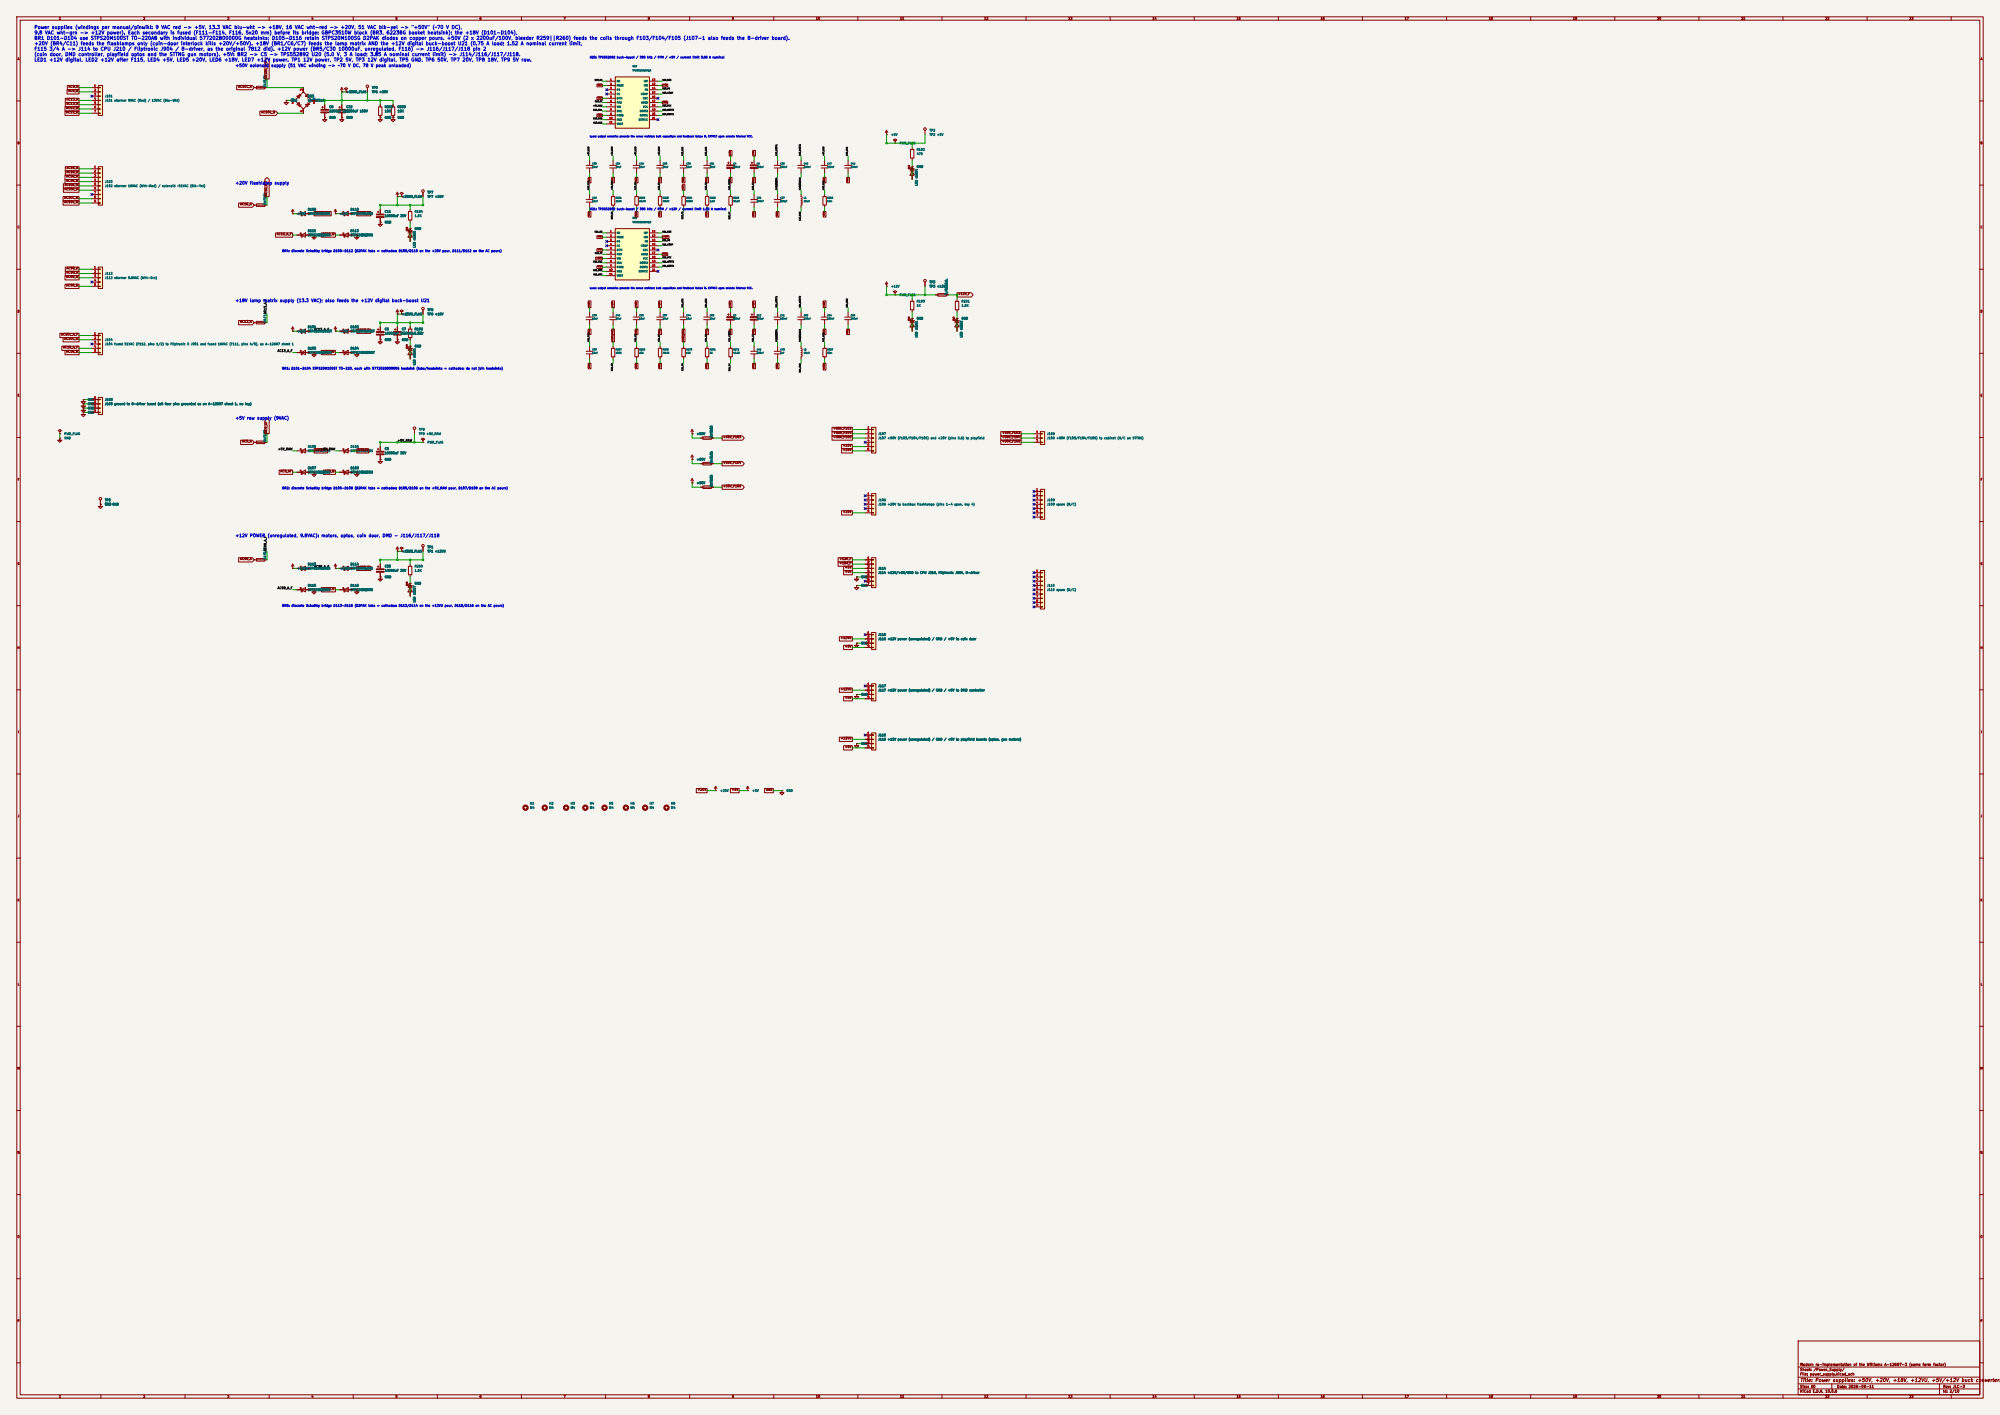
[picture p132: page 2]

9.8 VAC wht-grn -> +12V power). Each secondary is fused (F111-F114, F116, 5x20 mm) before its bridge: GBPC3510W block (BR3, 6223BG basket heatsink); the +18V (D101-D104),
BR1 D101-D104 use STPS20M100ST TO-220AB with individual 577202B00000G heatsinks; D105-D116 retain STPS20M100SG D2PAK diodes on copper pours. +50V (2 x 2200uF/100V, bleeder R259||R260) feeds the coils through F103/F104/F105 (J107-1 also feeds the 8-driver board).
+20V (BR4/C11) feeds the flashlamps only (coin-door interlock kills +20V/+50V). +18V (BR1/C6/C7) feeds the lamp matrix AND the +12V digital buck-boost U21 (0.75 A load; 1.52 A nominal current limit,
F115 3/4 A -> J114 to CPU J210 / Fliptronic J904 / 8-driver, as the original 7812 did). +12V power (BR5/C30 10000uF, unregulated, F116) -> J116/J117/J118 pin 2
(coin door, DMD controller, playfield optos and the STTNG gun motors). +5V: BR2 -> C5 -> TPS552892 U20 (5.0 V, 3 A load; 3.85 A nominal current limit) -> J114/J116/J117/J118.

Local output ceramics precede the sense resistor; bulk capacitors and feedback follow it. EXTVCC open selects internal VCC. +20V flashlamp supply

+18V lamp matrix supply (13.3 VAC); also feeds the +12V digital buck-boost U21

BR1: D101-D104 STPS20M100ST TO-220, each with 577202B00000G heatsink (tabs/heatsinks = cathodes; do not join heatsinks)

J103 ground to 8-driver board (all four pins grounded as on A-12697 sheet 1, no key) 1
GND
4 GND

J103 ground to 8-driver board (all four pins grounded as on A-12697 sheet 1, no key) GND

+5V raw supply (9VAC) BR2: discrete Schottky bridge D105-D108 (D2PAK tabs = cathodes: D105/D106 on the +5V_RAW pour, D107/D108 on the AC pours) BR5: discrete Schottky bridge D113-D116 (D2PAK tabs = cathodes: D113/D114 on the +12VU pour, D115/D116 on the AC pours)

J107 +50V (F103/F104/F105) and +20V (pins 5,6) to playfield

J108 +50V (F103/F104/F105) to cabinet (N/C on STTNG)

+12V POWER (unregulated, 9.8VAC): motors, optos, coin door, DMD - J116/J117/J118

J118 +12V power (unregulated) / GND / +5V to playfield boards (optos, gun motors) GND

J117 +12V power (unregulated) / GND / +5V to DMD controller

J118 +12V power (unregulated) / GND / +5V to playfield boards (optos, gun motors) 1

Modern re-implementation of the Williams A-12697-3 (same form factor)
Sheet: /Power_Supply/
File: power_supply.kicad_sch
Title: Power supplies: +50V, +20V, +18V, +12VU, +5V/+12V buck converters, distribution

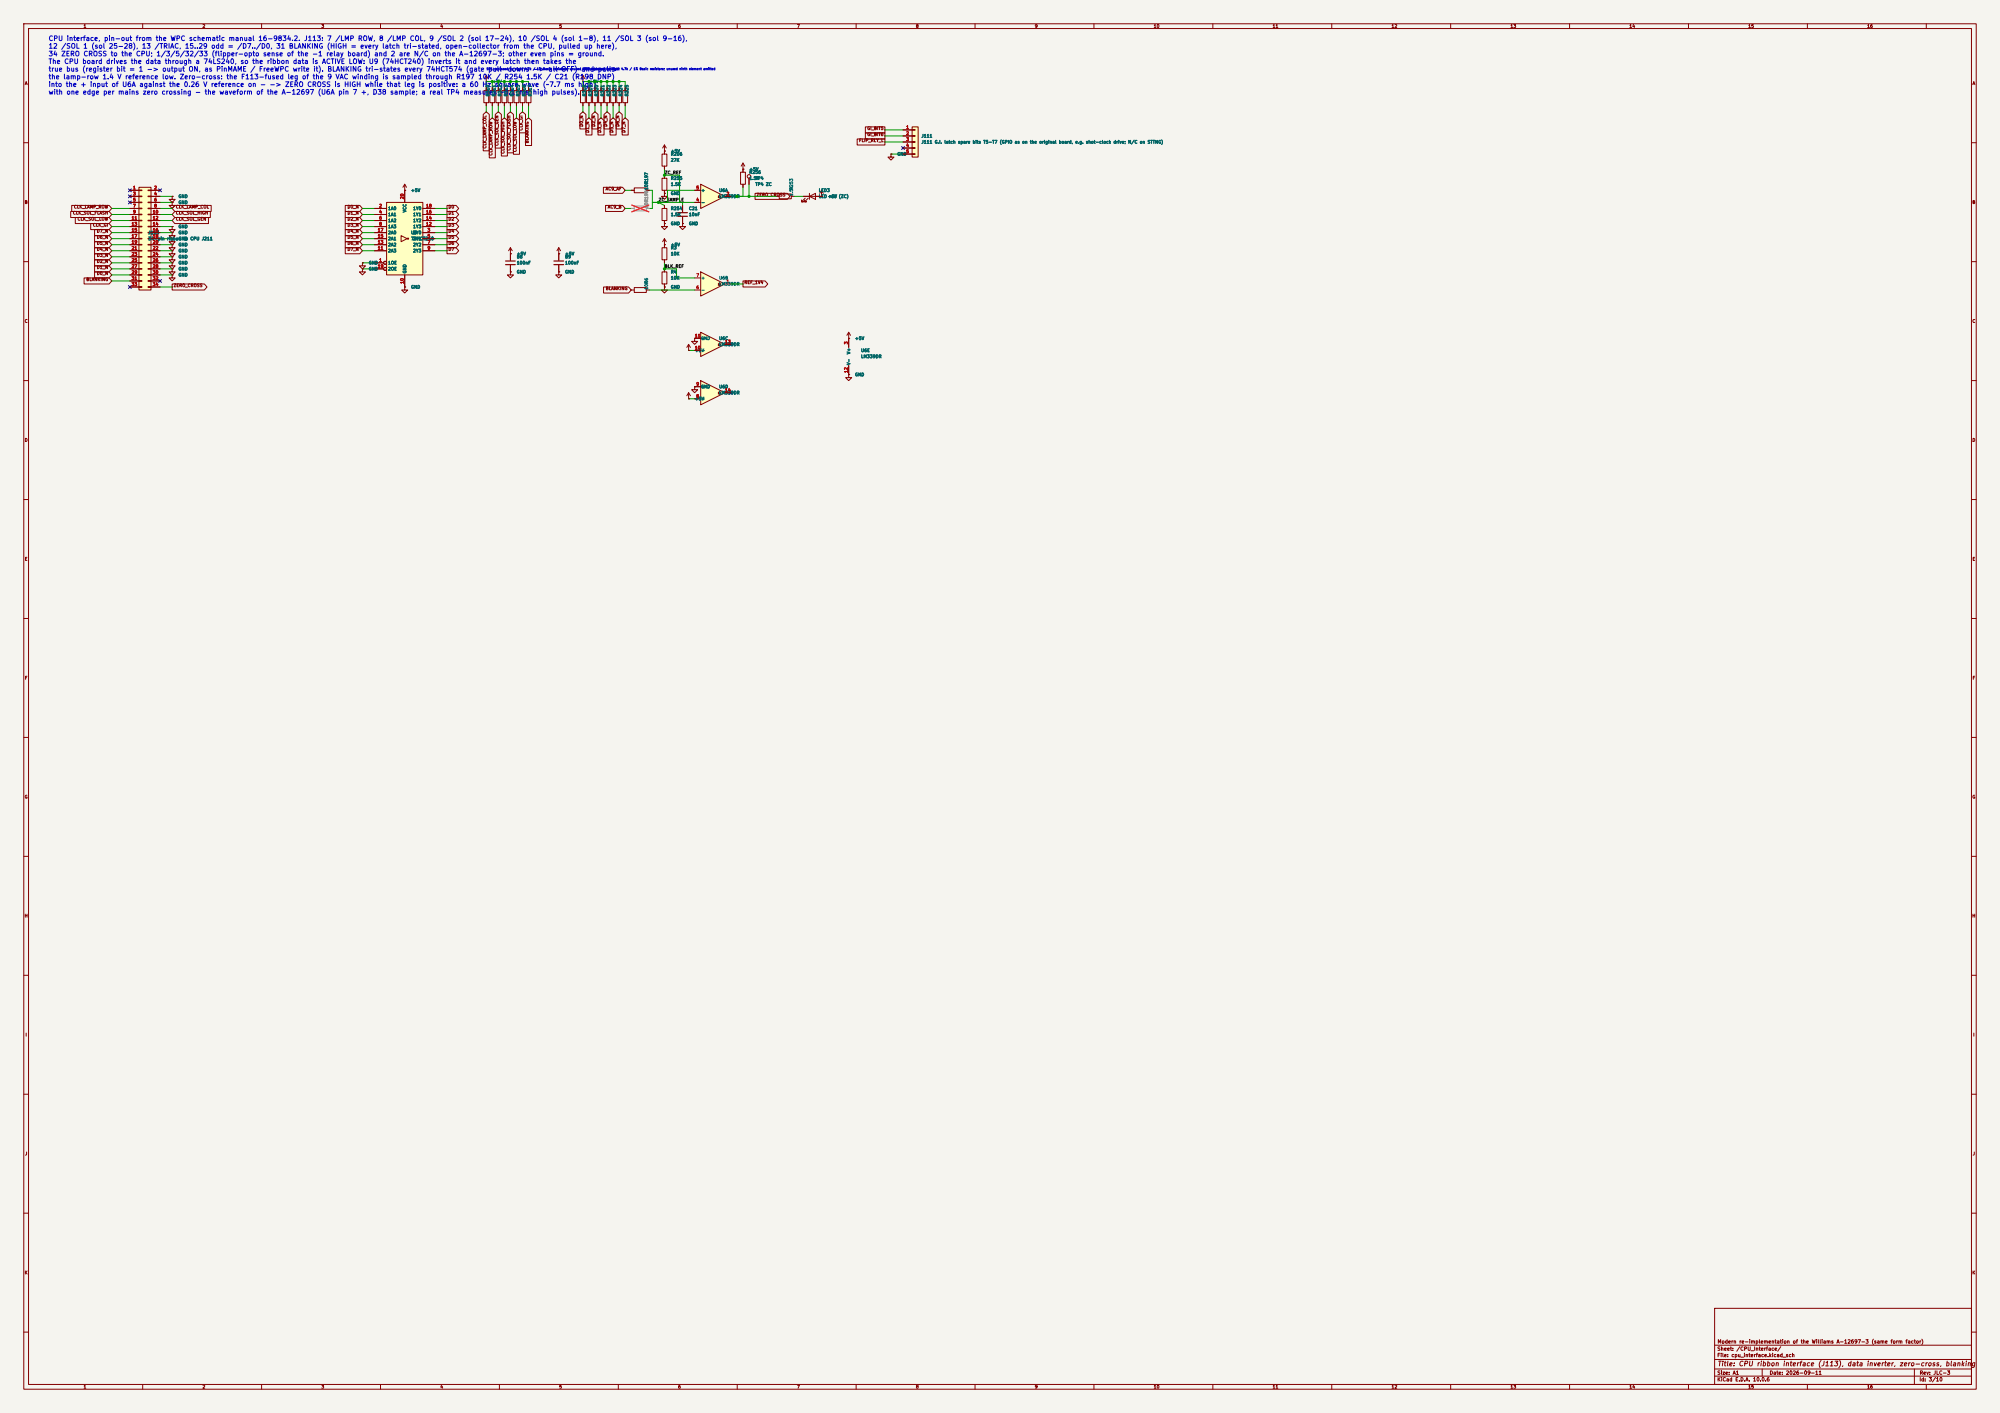
[picture p133: page 3]

SR1 replaced by eight 4.7k / 1% Basic resistors; unused ninth element omitted CPU interface, pin-out from the WPC schematic manual 16-9834.2. J113: 7 /LMP ROW, 8 /LMP COL, 9 /SOL 2 (sol 17-24), 10 /SOL 4 (sol 1-8), 11 /SOL 3 (sol 9-16),
12 /SOL 1 (sol 25-28), 13 /TRIAC, 15..29 odd = /D7../D0, 31 BLANKING (HIGH = every latch tri-stated, open-collector from the CPU, pulled up here),
34 ZERO CROSS to the CPU; 1/3/5/32/33 (flipper-opto sense of the -1 relay board) and 2 are N/C on the A-12697-3; other even pins = ground.
The CPU board drives the data through a 74LS240, so the ribbon data is ACTIVE LOW: U9 (74HCT240) inverts it and every latch then takes the
true bus (register bit = 1 -> output ON, as PinMAME / FreeWPC write it). BLANKING tri-states every 74HCT574 (gate pull-downs -> all OFF) and pulls
the lamp-row 1.4 V reference low. Zero-cross: the F113-fused leg of the 9 VAC winding is sampled through R197 10K / R254 1.5K / C21 (R198 DNP)

SR2 replaced by eight 4.7k / 1% Basic resistors; unused ninth element omitted U9

J111 G.I. latch spare bits T5-T7 (GPIO as on the original board, e.g. shot-clock drive; N/C on STTNG) 1

J111 G.I. latch spare bits T5-T7 (GPIO as on the original board, e.g. shot-clock drive; N/C on STTNG) +5VGND -

34-pin ribbon to CPU J211 GND

34-pin ribbon to CPU J211

Sheet: /CPU_Interface/
File: cpu_interface.kicad_sch
Title: CPU ribbon interface (J113), data inverter, zero-cross, blanking

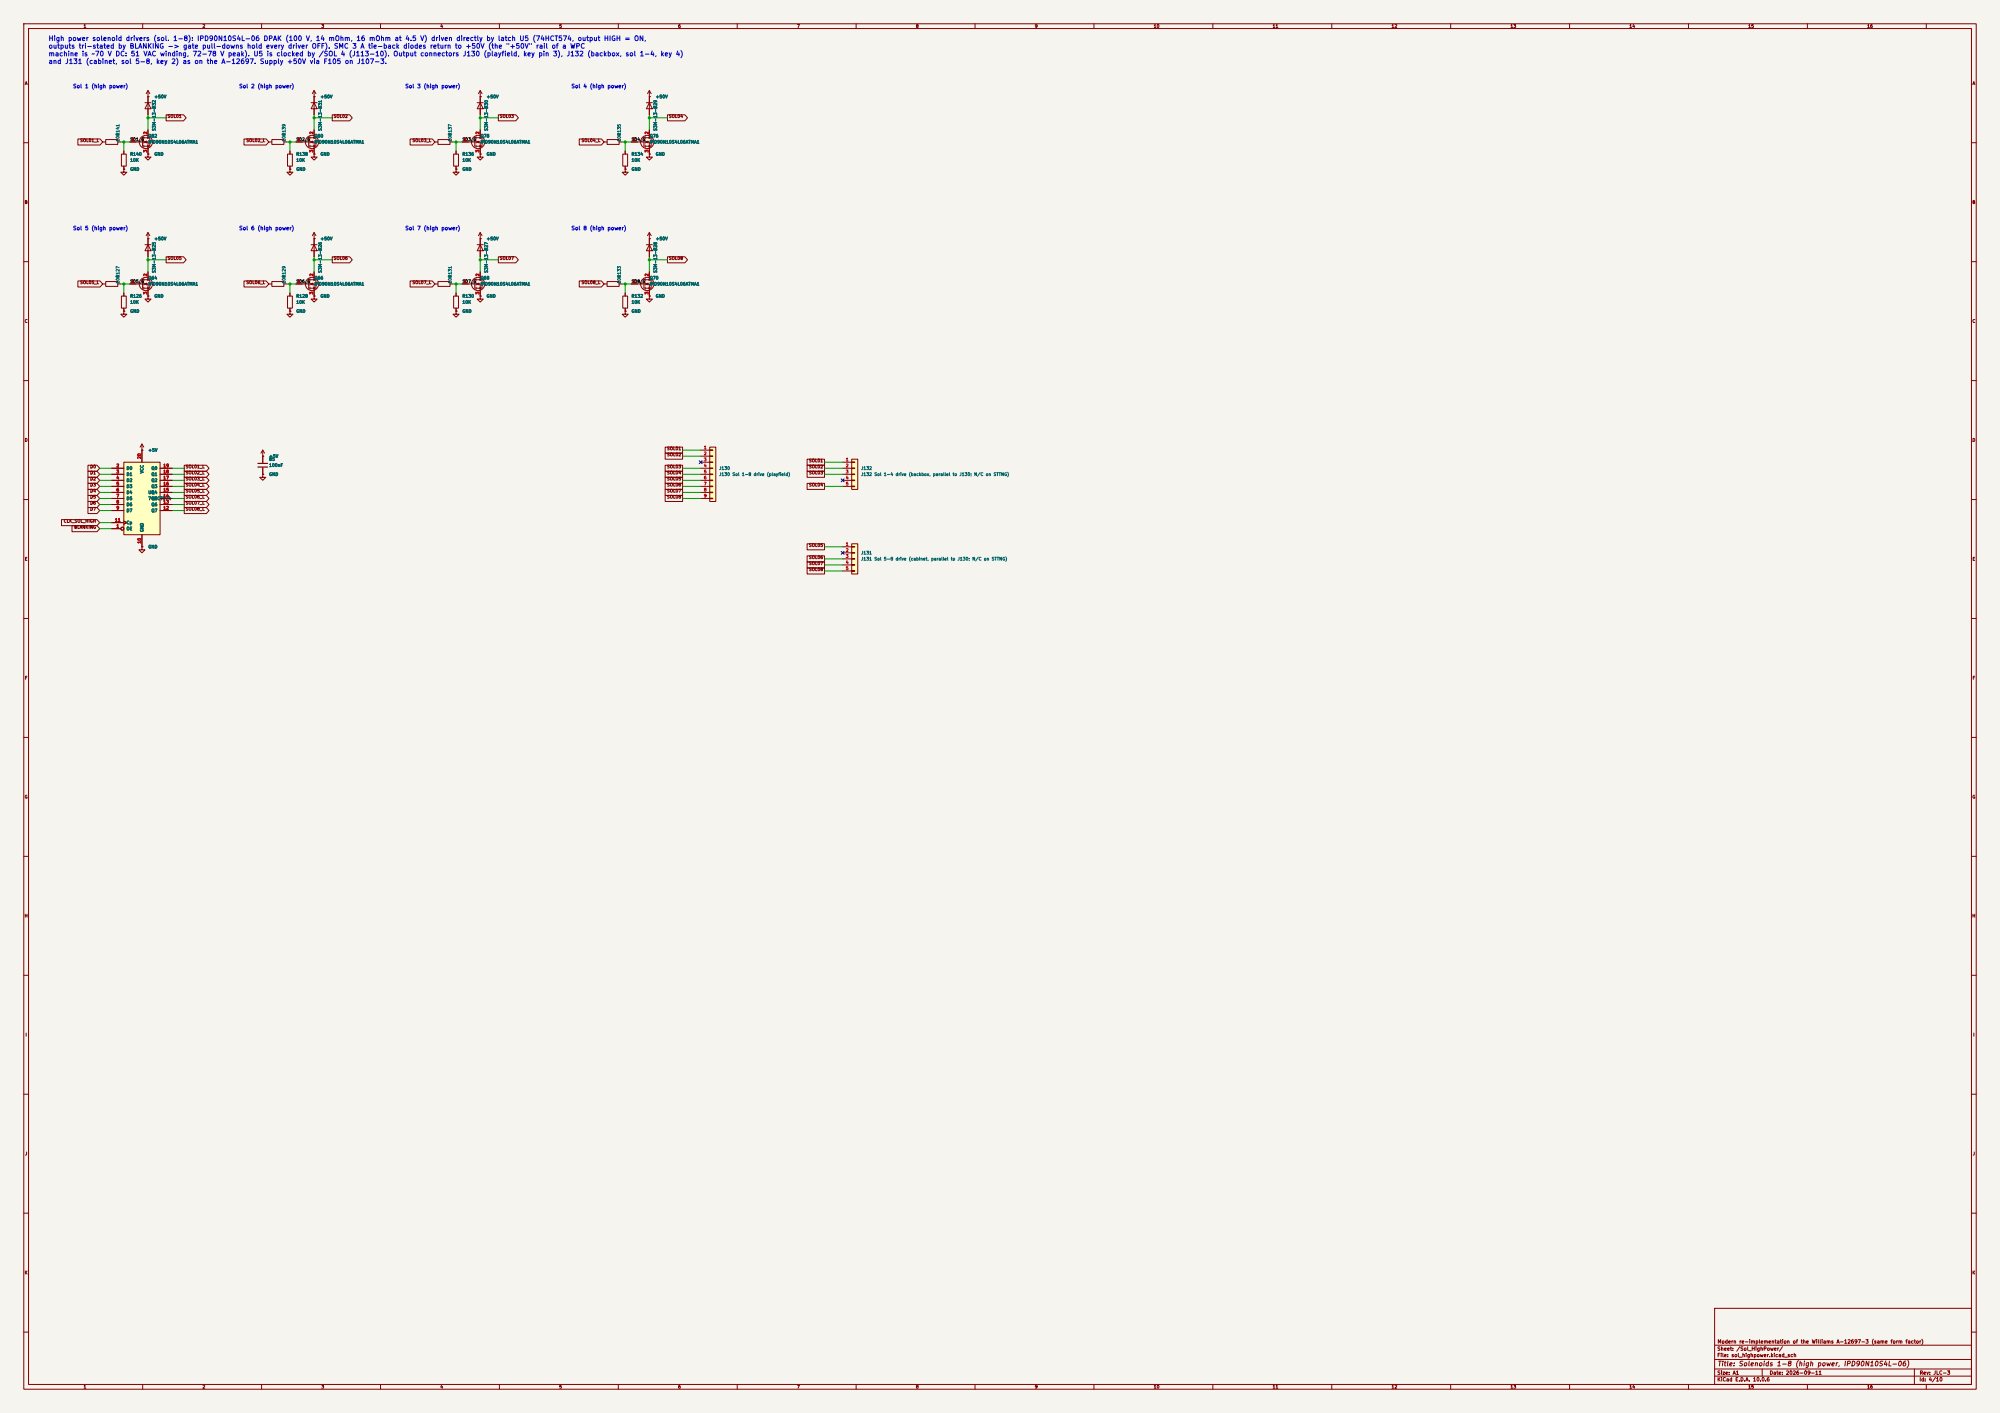
[picture p134: page 4]

High power solenoid drivers (sol. 1-8): IPD90N10S4L-06 DPAK (100 V, 14 mOhm, 16 mOhm at 4.5 V) driven directly by latch U5 (74HCT574, output HIGH = ON,
outputs tri-stated by BLANKING -> gate pull-downs hold every driver OFF). SMC 3 A tie-back diodes return to +50V (the "+50V" rail of a WPC
machine is ~70 V DC: 51 VAC winding, 72-78 V peak). U5 is clocked by /SOL 4 (J113-10). Output connectors J130 (playfield, key pin 3), J132 (backbox, sol 1-4, key 4)
and J131 (cabinet, sol 5-8, key 2) as on the A-12697. Supply +50V via F105 on J107-3.

J132 Sol 1-4 drive (backbox, parallel to J130; N/C on STTNG) R132

Sheet: /Sol_HighPower/
File: sol_highpower.kicad_sch
Title: Solenoids 1-8 (high power, IPD90N10S4L-06)

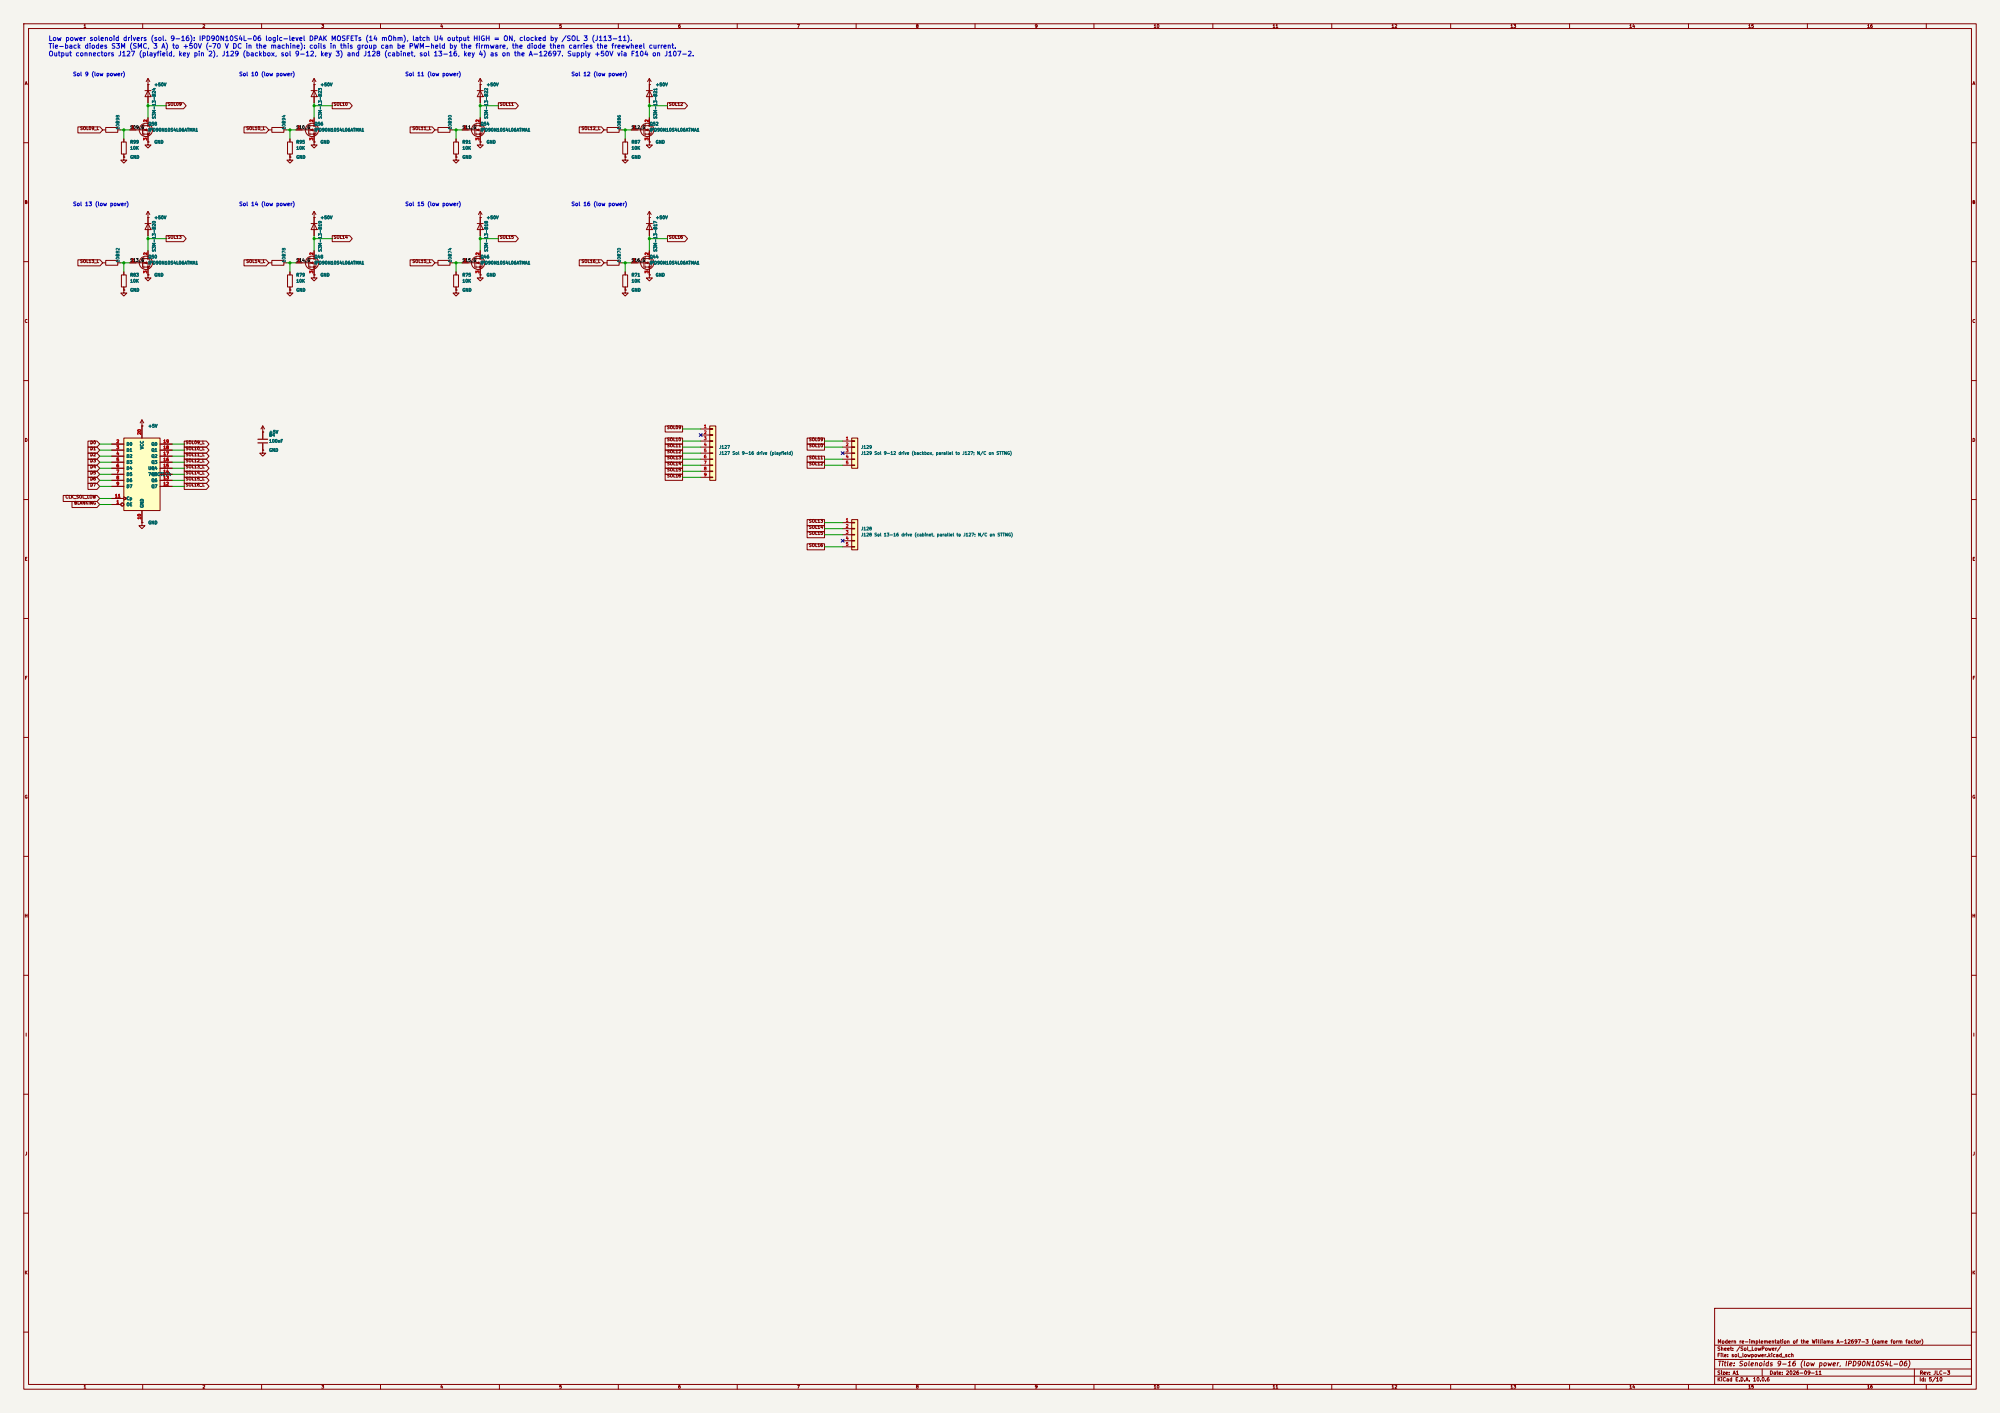
[picture p135: page 5]

Low power solenoid drivers (sol. 9-16): IPD90N10S4L-06 logic-level DPAK MOSFETs (14 mOhm), latch U4 output HIGH = ON, clocked by /SOL 3 (J113-11).
Tie-back diodes S3M (SMC, 3 A) to +50V (~70 V DC in the machine): coils in this group can be PWM-held by the firmware, the diode then carries the freewheel current.
Output connectors J127 (playfield, key pin 2), J129 (backbox, sol 9-12, key 3) and J128 (cabinet, sol 13-16, key 4) as on the A-12697. Supply +50V via F104 on J107-2.

Sheet: /Sol_LowPower/
File: sol_lowpower.kicad_sch
Title: Solenoids 9-16 (low power, IPD90N10S4L-06)

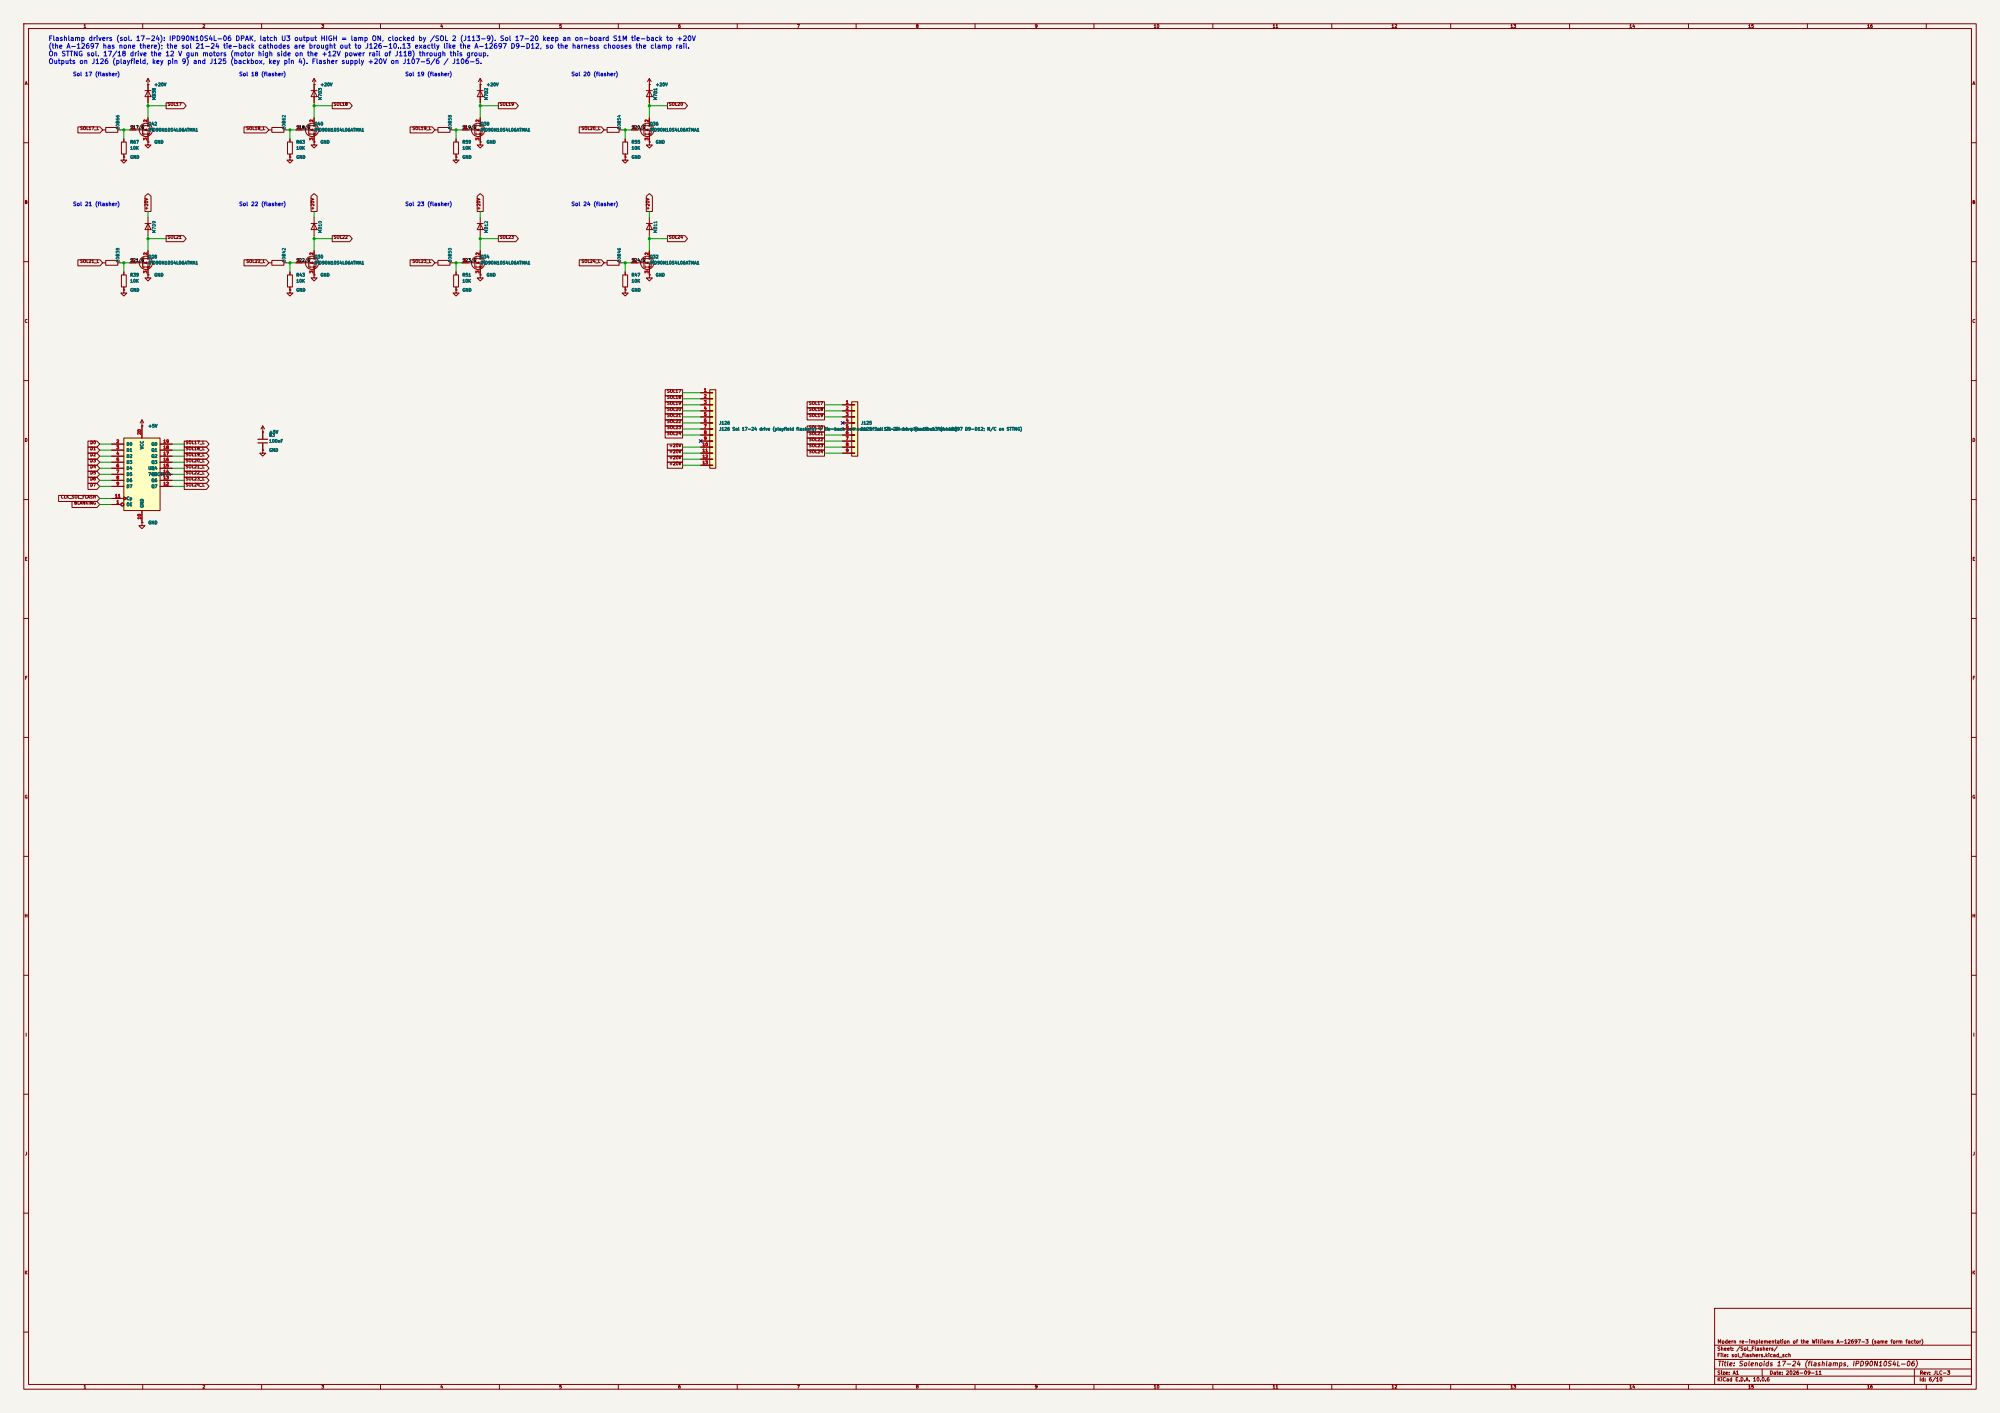
[picture p136: page 6]

Flashlamp drivers (sol. 17-24): IPD90N10S4L-06 DPAK, latch U3 output HIGH = lamp ON, clocked by /SOL 2 (J113-9). Sol 17-20 keep an on-board S1M tie-back to +20V
(the A-12697 has none there); the sol 21-24 tie-back cathodes are brought out to J126-10..13 exactly like the A-12697 D9-D12, so the harness chooses the clamp rail.
On STTNG sol. 17/18 drive the 12 V gun motors (motor high side on the +12V power rail of J118) through this group.
Outputs on J126 (playfield, key pin 9) and J125 (backbox, key pin 4). Flasher supply +20V on J107-5/6 / J106-5.

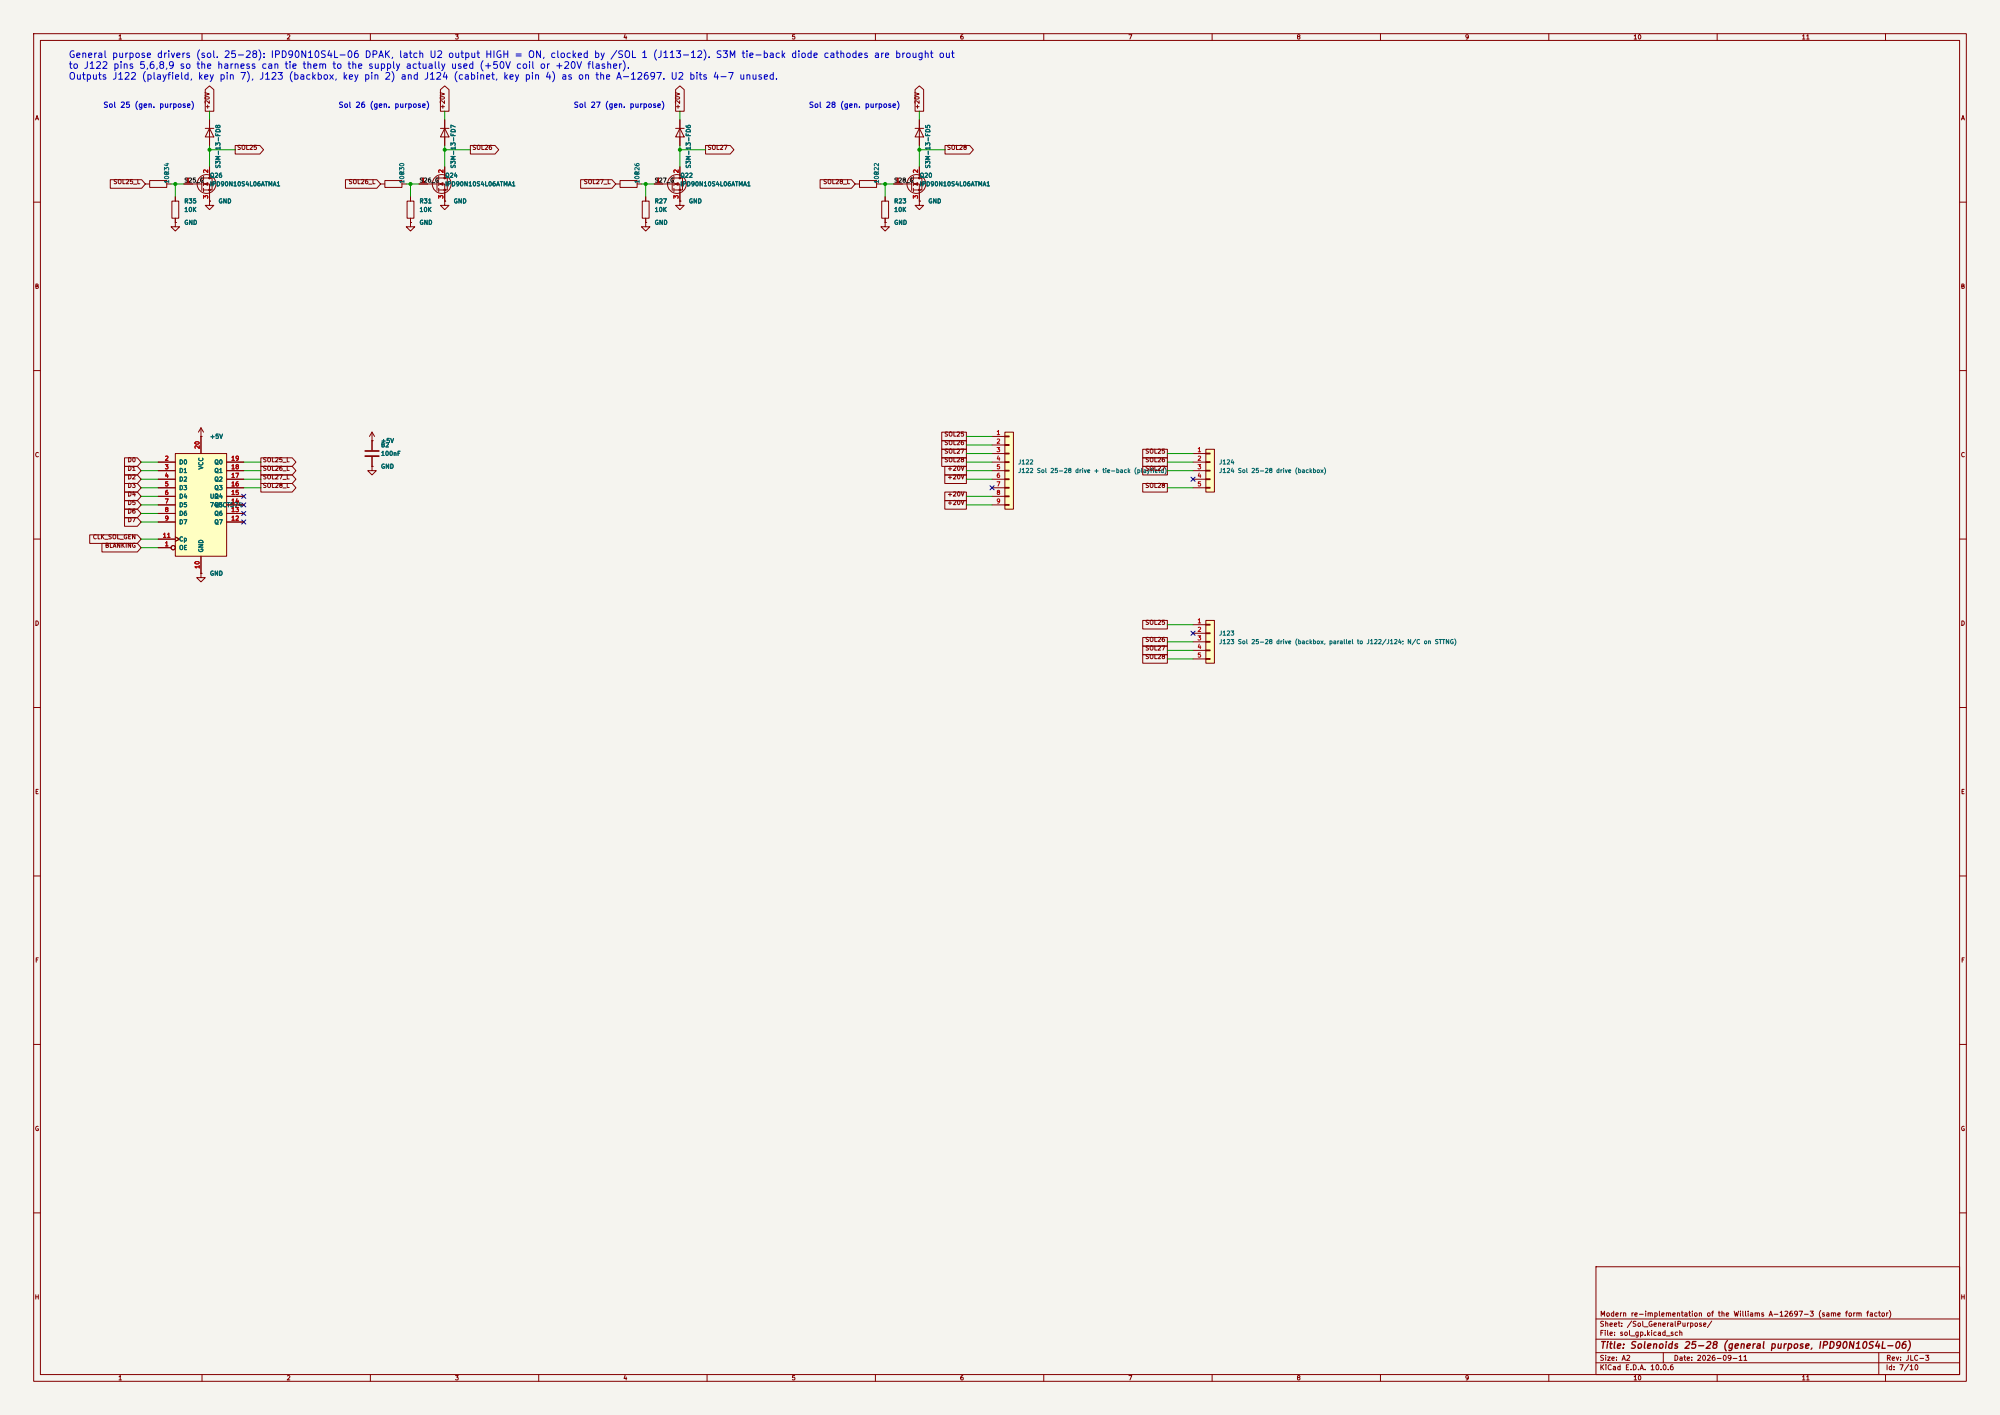
[picture p137: page 7]

General purpose drivers (sol. 25-28): IPD90N10S4L-06 DPAK, latch U2 output HIGH = ON, clocked by /SOL 1 (J113-12). S3M tie-back diode cathodes are brought out
to J122 pins 5,6,8,9 so the harness can tie them to the supply actually used (+50V coil or +20V flasher).

J122 Sol 25-28 drive + tie-back (playfield) D8 S3M-13-F 1

J123 Sol 25-28 drive (backbox, parallel to J122/J124; N/C on STTNG)

Sheet: /Sol_GeneralPurpose/
File: sol_gp.kicad_sch
Title: Solenoids 25-28 (general purpose, IPD90N10S4L-06)

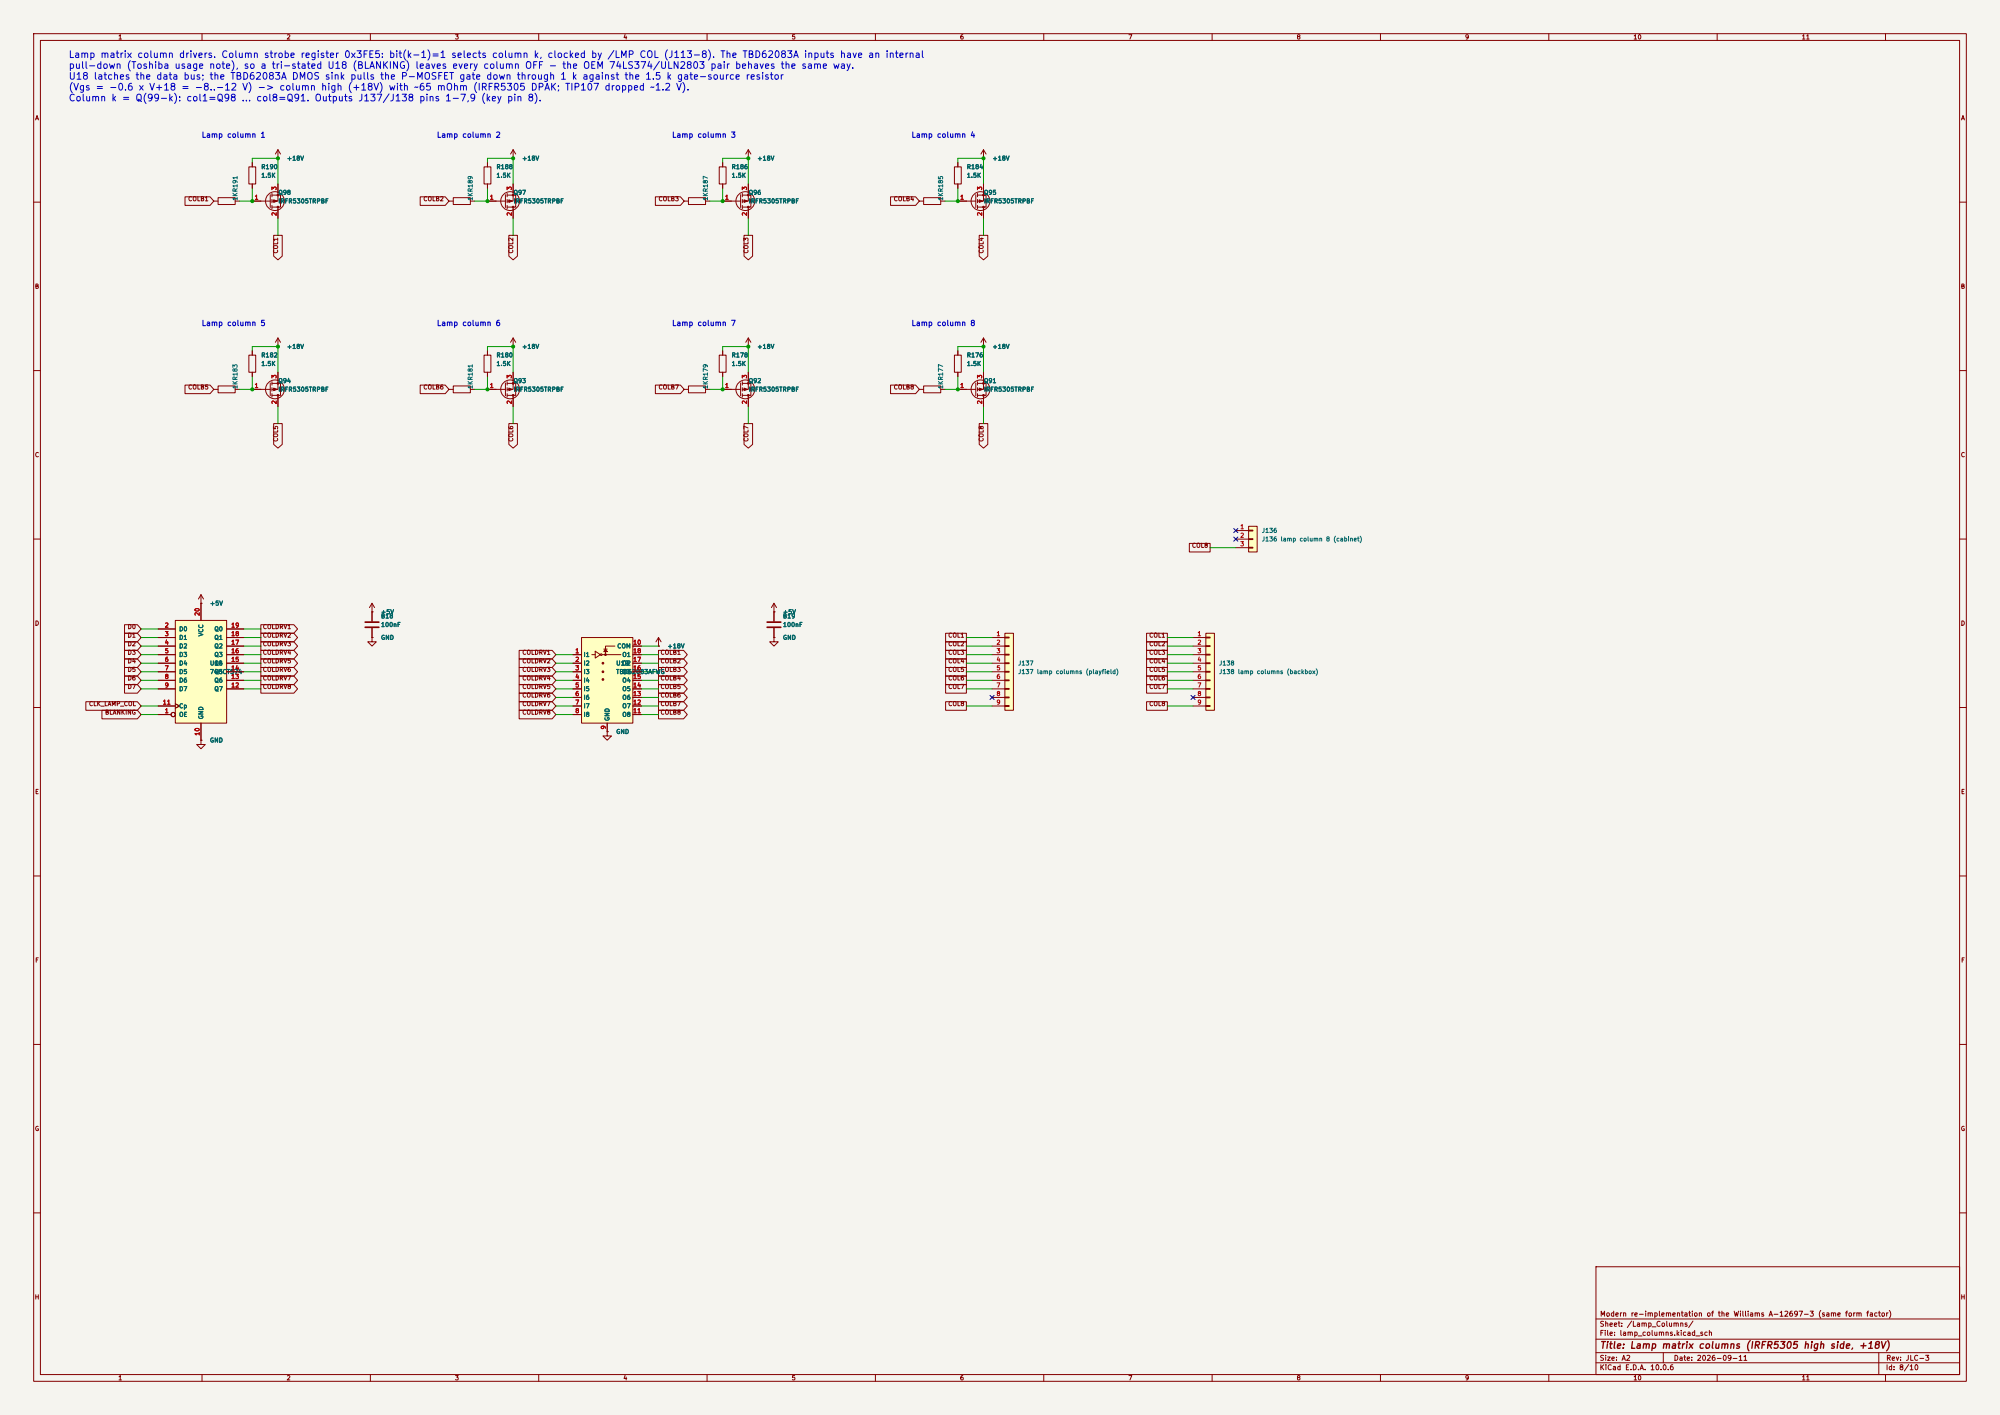
[picture p138: page 8]

Lamp matrix column drivers. Column strobe register 0x3FE5: bit(k-1)=1 selects column k, clocked by /LMP COL (J113-8). The TBD62083A inputs have an internal
pull-down (Toshiba usage note), so a tri-stated U18 (BLANKING) leaves every column OFF - the OEM 74LS374/ULN2803 pair behaves the same way.
U18 latches the data bus; the TBD62083A DMOS sink pulls the P-MOSFET gate down through 1 k against the 1.5 k gate-source resistor
(Vgs = -0.6 x V+18 = -8..-12 V) -> column high (+18V) with ~65 mOhm (IRFR5305 DPAK; TIP107 dropped ~1.2 V).
Column k = Q(99-k): col1=Q98 ... col8=Q91. Outputs J137/J138 pins 1-7,9 (key pin 8).

Sheet: /Lamp_Columns/
File: lamp_columns.kicad_sch
Title: Lamp matrix columns (IRFR5305 high side, +18V)

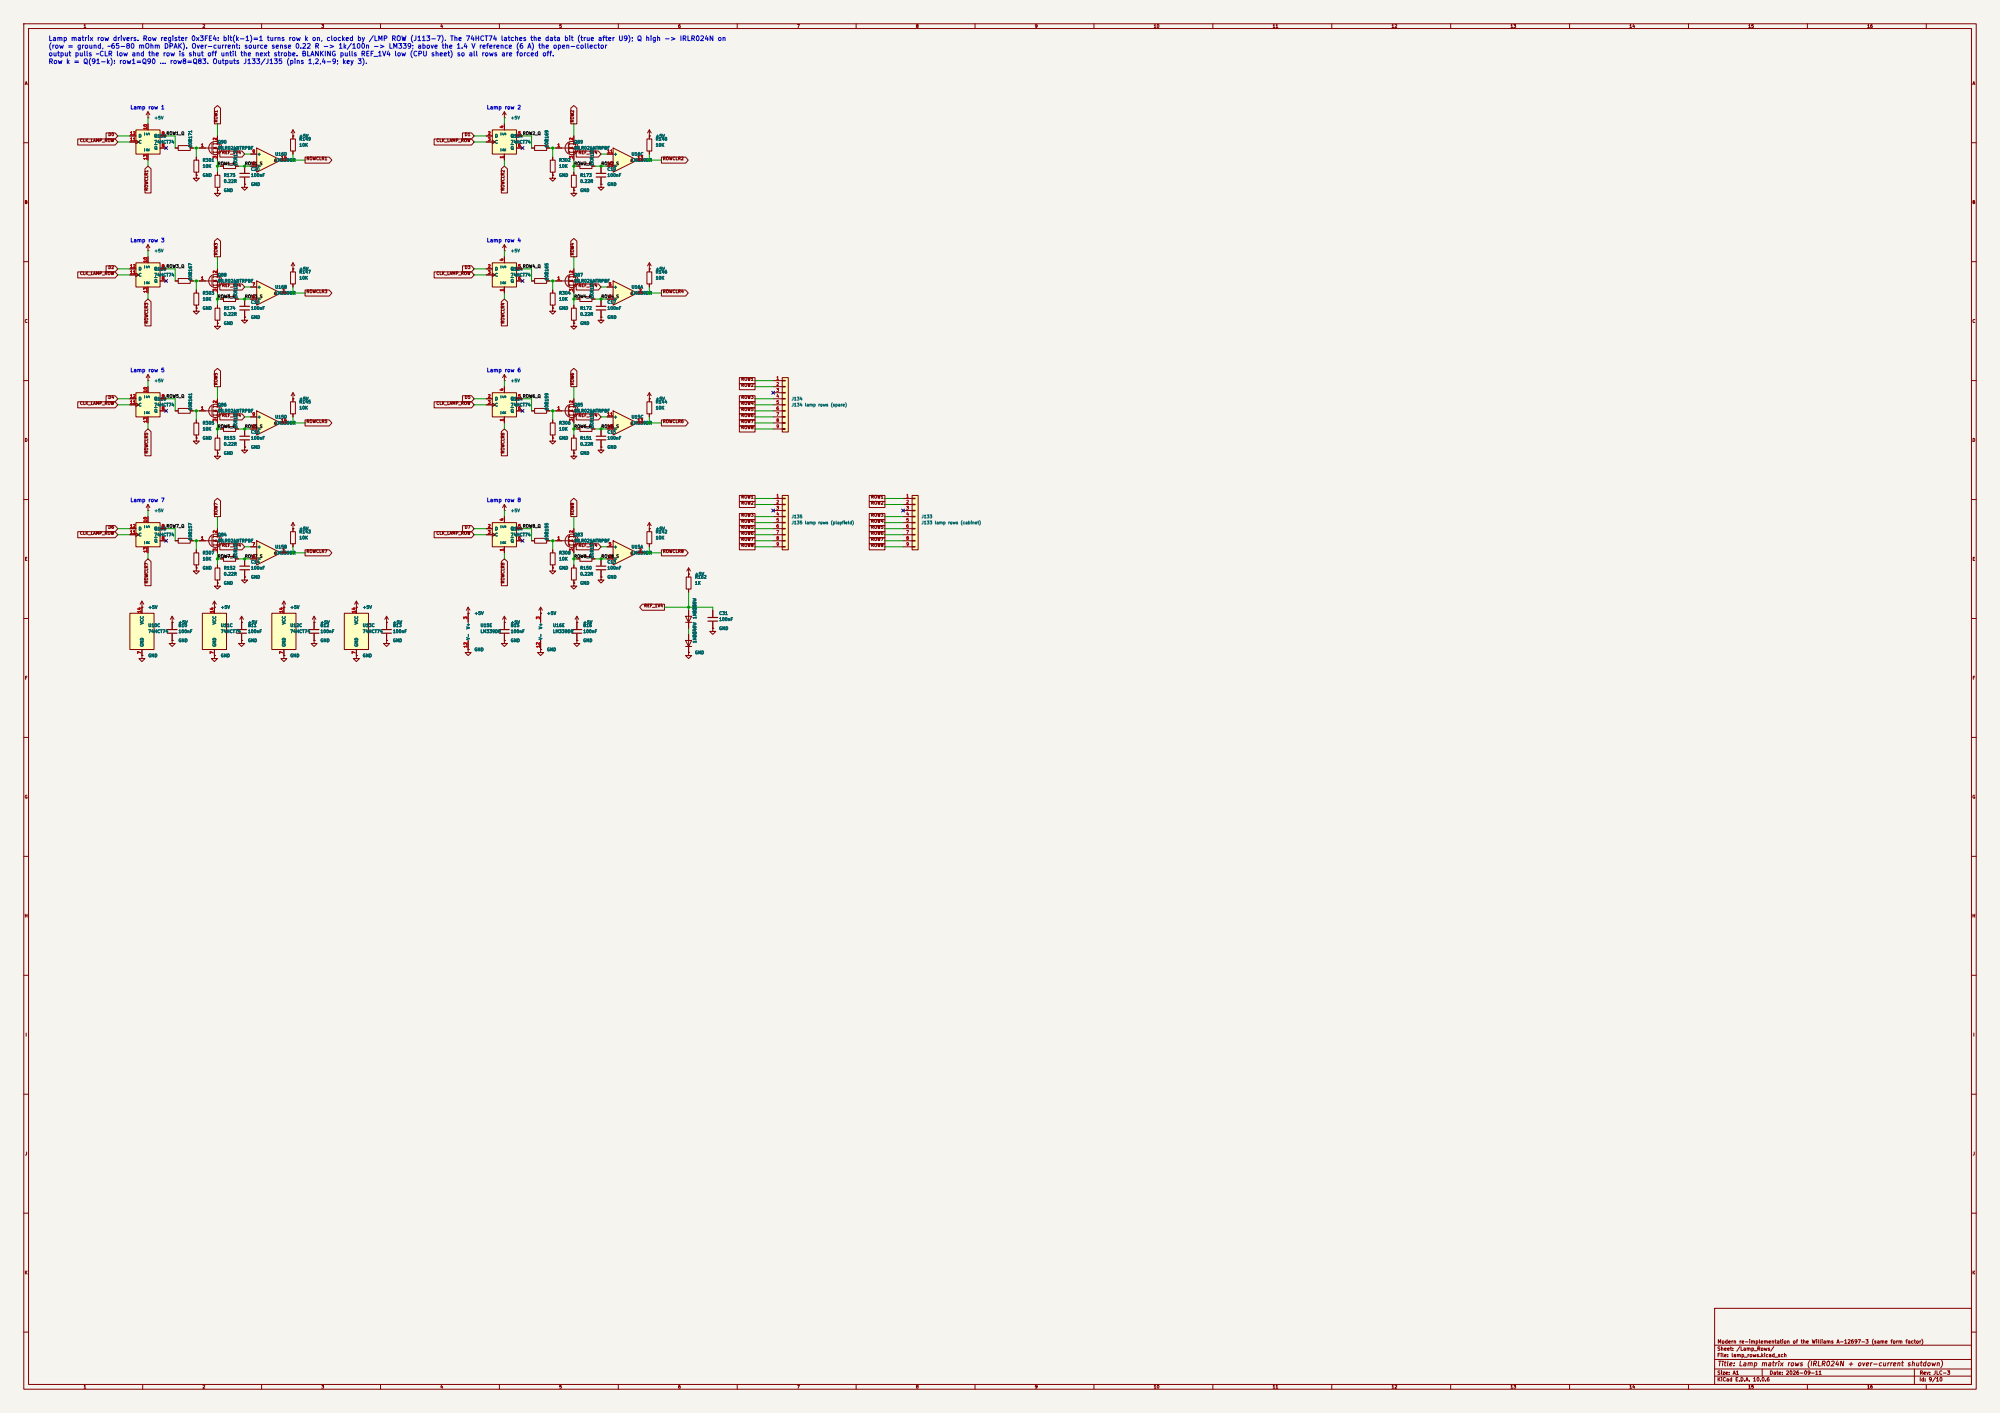
[picture p139: page 9]

Lamp matrix row drivers. Row register 0x3FE4: bit(k-1)=1 turns row k on, clocked by /LMP ROW (J113-7). The 74HCT74 latches the data bit (true after U9); Q high -> IRLR024N on
(row = ground, ~65-80 mOhm DPAK). Over-current: source sense 0.22 R -> 1k/100n -> LM339; above the 1.4 V reference (6 A) the open-collector
output pulls ~CLR low and the row is shut off until the next strobe. BLANKING pulls REF_1V4 low (CPU sheet) so all rows are forced off.
Row k = Q(91-k): row1=Q90 ... row8=Q83. Outputs J133/J135 (pins 1,2,4-9; key 3).
ROW1_E ROW1_Q
74HCT74 Q

Sheet: /Lamp_Rows/
File: lamp_rows.kicad_sch
Title: Lamp matrix rows (IRLR024N + over-current shutdown)

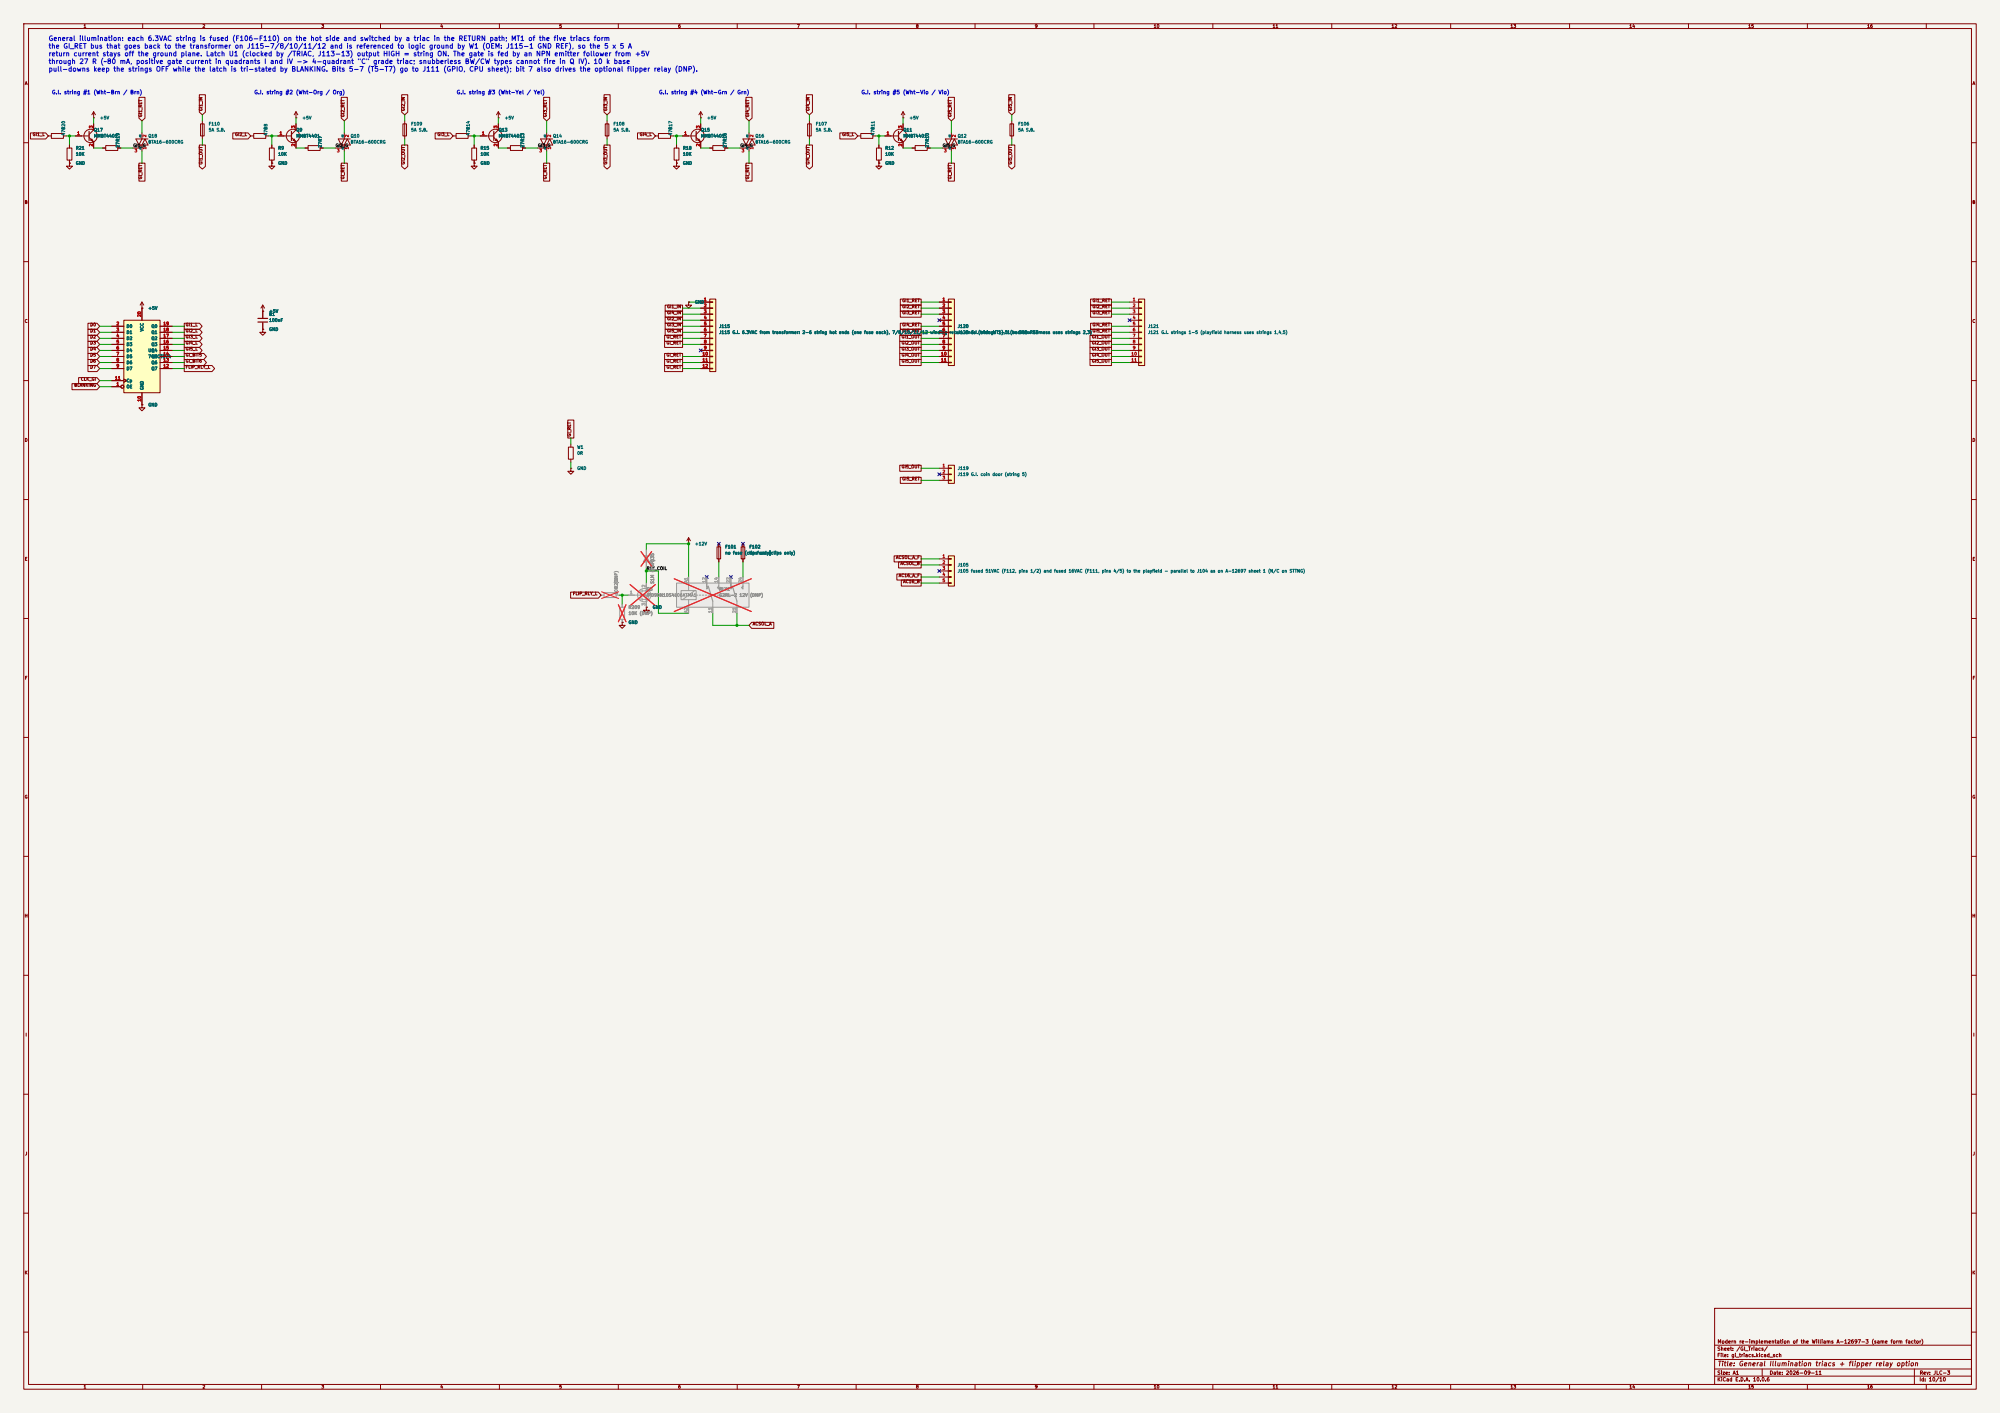
[picture p140: page 10]

General illumination: each 6.3VAC string is fused (F106-F110) on the hot side and switched by a triac in the RETURN path; MT1 of the five triacs form
the GI_RET bus that goes back to the transformer on J115-7/8/10/11/12 and is referenced to logic ground by W1 (OEM: J115-1 GND REF), so the 5 x 5 A
return current stays off the ground plane. Latch U1 (clocked by /TRIAC, J113-13) output HIGH = string ON. The gate is fed by an NPN emitter follower from +5V
through 27 R (~80 mA, positive gate current in quadrants I and IV -> 4-quadrant "C" grade triac; snubberless BW/CW types cannot fire in Q IV). 10 k base
pull-downs keep the strings OFF while the latch is tri-stated by BLANKING. Bits 5-7 (T5-T7) go to J111 (GPIO, CPU sheet); bit 7 also drives the optional flipper relay (DNP).

J105 fused 51VAC (F112, pins 1/2) and fused 16VAC (F111, pins 4/5) to the playfield - parallel to J104 as on A-12697 sheet 1 (N/C on STTNG) GND

no fuse (clips only)

Sheet: /GI_Triacs/
File: gi_triacs.kicad_sch
Title: General Illumination triacs + flipper relay option
