lolz0r/Williams-WPC-Power-Driver-Board-A-12697-3/variants/jlcpcb/output/verification/continuation/reservoir-tradeoff.pdf

12.6

## Input minimum at 90% line, 60 Hz

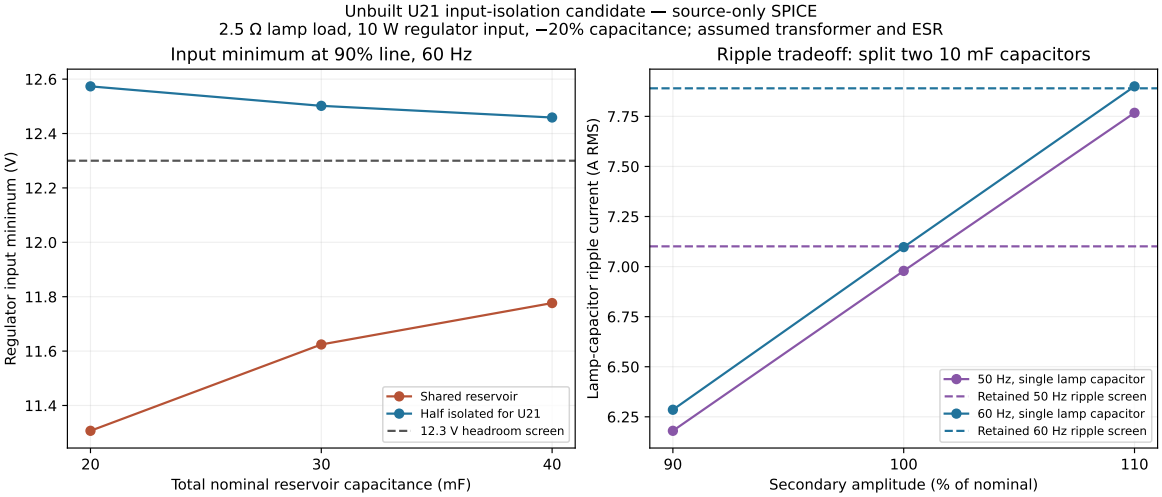
[picture p141: page 1]
Unbuilt U21 input-isolation candidate; source-only SPICE; lamp load, 10 W regulator input,; 20% capacitance; assumed transformer and ESR

Ripple tradeoff: split two 10 mF capacitors

Lamp-capacitor ripple current (A RMS)

Regulator input minimum (V)

50 Hz, single lamp capacitor Retained 50 Hz ripple screen 60 Hz, single lamp capacitor

Shared reservoir
Half isolated for U21 12.3 V headroom screen

Retained 60 Hz ripple screen

Total nominal reservoir capacitance (mF)

Secondary amplitude (% of nominal)
