lolz0r/Williams-WPC-Power-Driver-Board-A-12697-3/.scratch/sch.pdf

WPC POWER DRIVER BOARD - COST-OPTIMISED MODERN VERSION - functional replacement for Williams A-12697-3 (same outline, connectors, fuses).
DPAK MOSFET solenoid/lamp drivers, TPS54360B buck regulators for +5V/+12V, 4-quadrant insulated triacs, SMD passives, 5x20 mm fuses.
Sheets: Power_Supply, CPU_Interface, Sol_HighPower (1-8), Sol_LowPower (9-16), Sol_Flashers (17-24), Sol_GeneralPurpose (25-28),
Lamp_Columns, Lamp_Rows, GI_Triacs. Every part carries Manufacturer / MPN / DigiKey link / Price / Price100 fields (see BOM). See README.md.

Modern re-implementation of the Williams A-12697-3 (same form factor)
Sheet: /
File: wpc_power_driver_cost.kicad_sch
Title: WPC Power Driver Board - cost-optimised modern re-implementation

Size: A3 | Rev: A | F Date: 2026-09-04
KiCad E.D.A. 10.0.6 | Id: 1/10

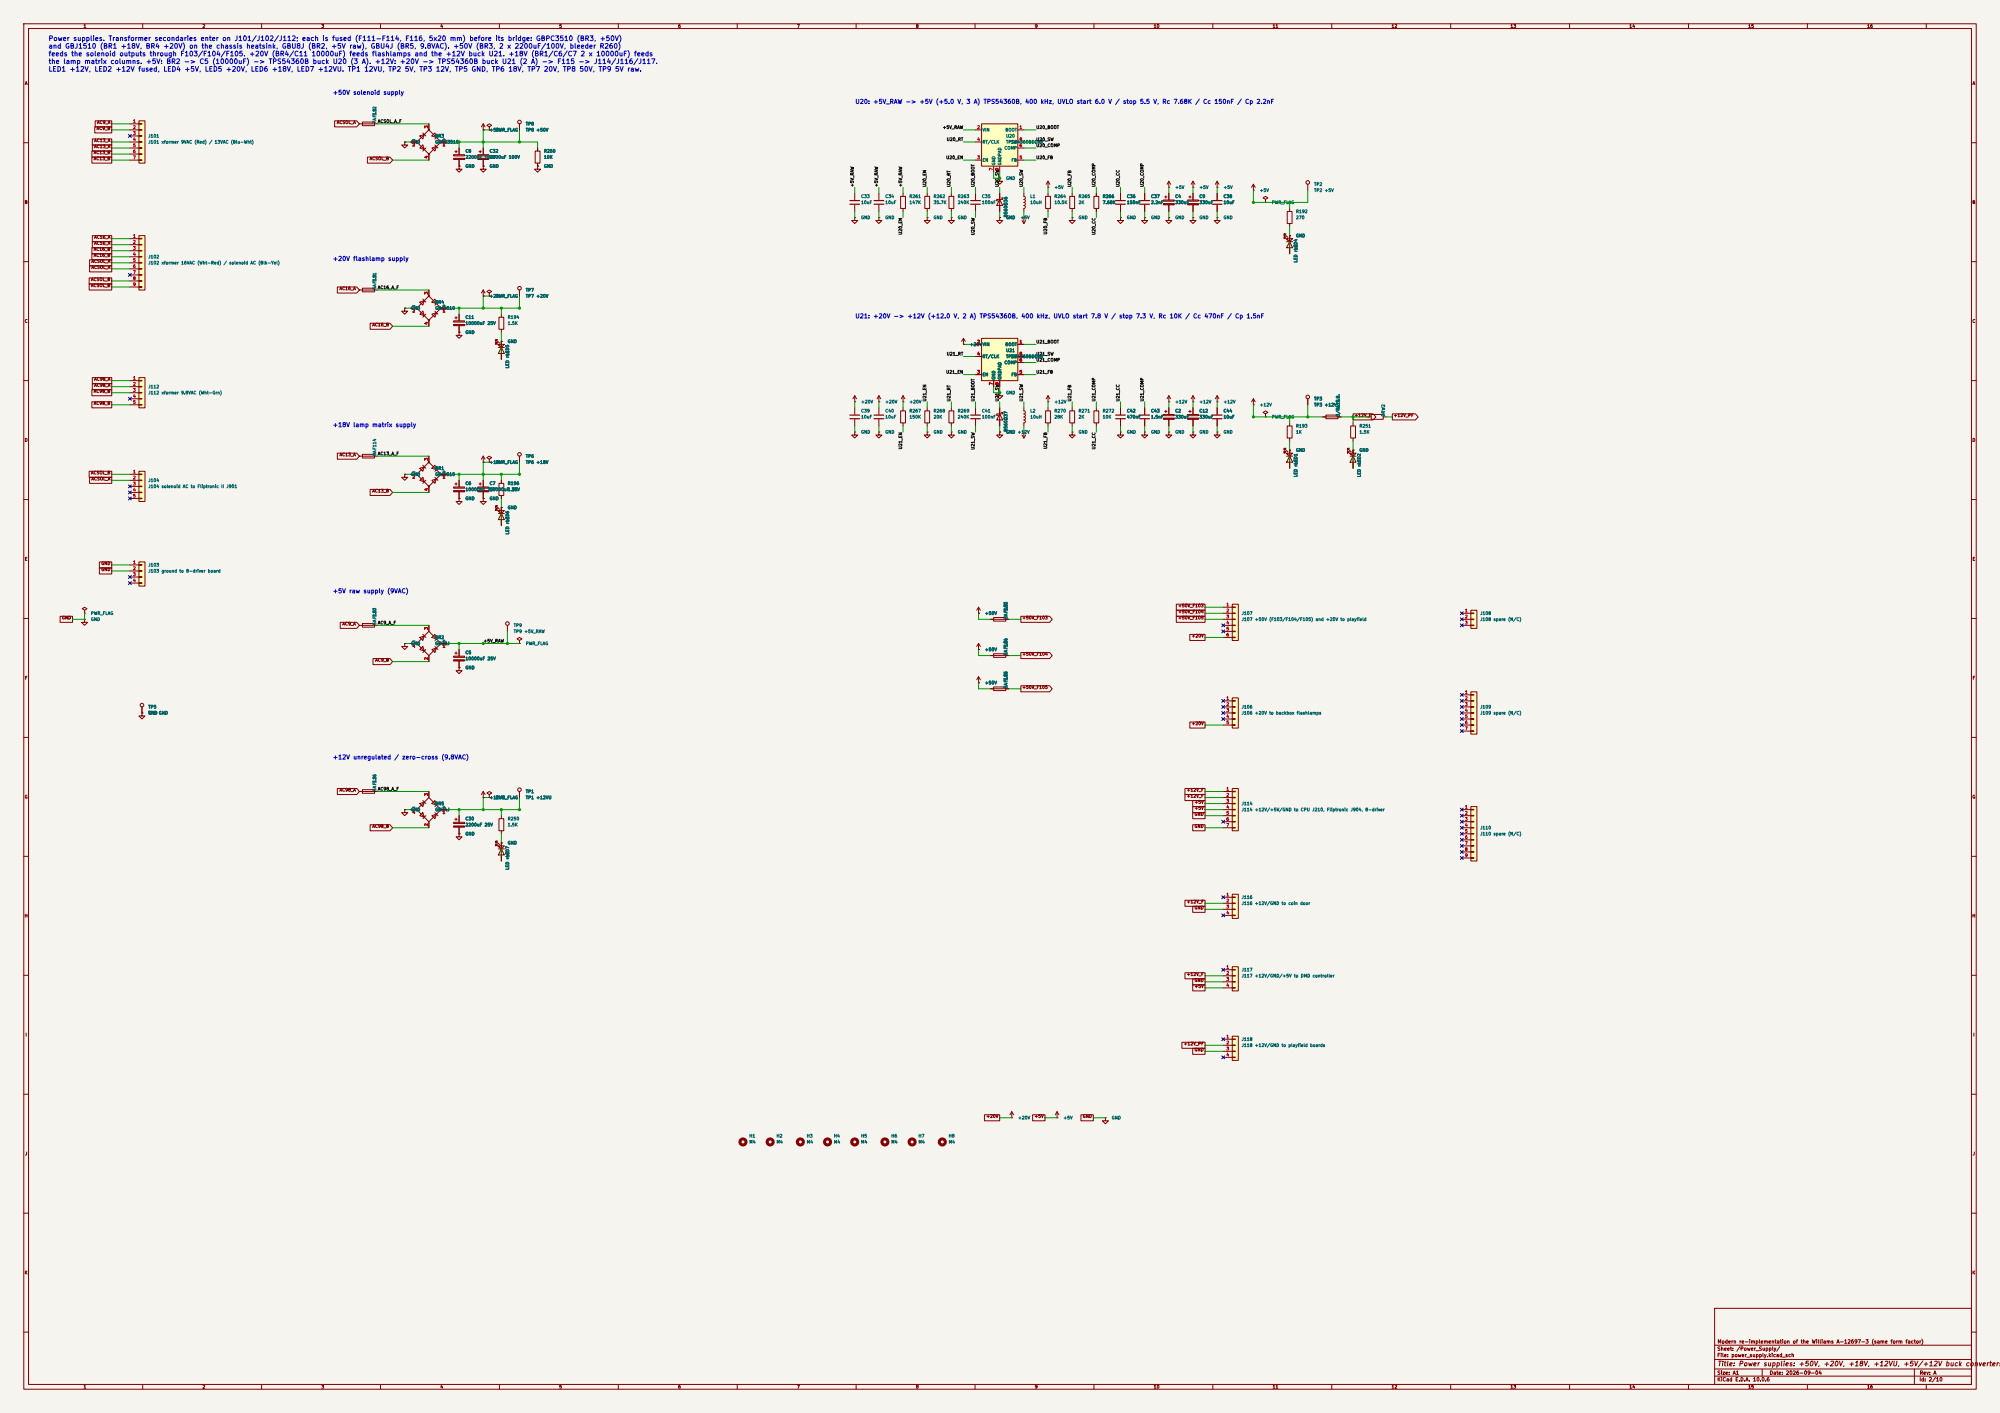
[picture p142: page 2]

Power supplies. Transformer secondaries enter on J101/J102/J112; each is fused (F111-F114, F116, 5x20 mm) before its bridge: GBPC3510 (BR3, +50V)
and GBJ1510 (BR1 +18V, BR4 +20V) on the chassis heatsink, GBU8J (BR2, +5V raw), GBU4J (BR5, 9.8VAC). +50V (BR3, 2 x 2200uF/100V, bleeder R260)
feeds the solenoid outputs through F103/F104/F105. +20V (BR4/C11 10000uF) feeds flashlamps and the +12V buck U21. +18V (BR1/C6/C7 2 x 10000uF) feeds
the lamp matrix columns. +5V: BR2 -> C5 (10000uF) -> TPS54360B buck U20 (3 A). +12V: +20V -> TPS54360B buck U21 (2 A) -> F115 -> J114/J116/J117.

U20: +5V_RAW -> +5V (+5.0 V, 3 A) TPS54360B, 400 kHz, UVLO start 6.0 V / stop 5.5 V, Rc 7.68K / Cc 150nF / Cp 2.2nF

J118 +12V/GND to playfield boards LED4 LED red R192

U21: +20V -> +12V (+12.0 V, 2 A) TPS54360B, 400 kHz, UVLO start 7.8 V / stop 7.3 V, Rc 10K / Cc 470nF / Cp 1.5nF

Modern re-implementation of the Williams A-12697-3 (same form factor) F115 3/4A S.B.

J107 +50V (F103/F104/F105) and +20V to playfield LED1 LED red GND

GND LED6 LED red GND

J114 +12V/+5V/GND to CPU J210, Fliptronic J904, 8-driver

J116 +12V/GND to coin door

J117 +12V/GND/+5V to DMD controller GND

Sheet: /Power_Supply/
File: power_supply.kicad_sch
Title: Power supplies: +50V, +20V, +18V, +12VU, +5V/+12V buck converters, distribution

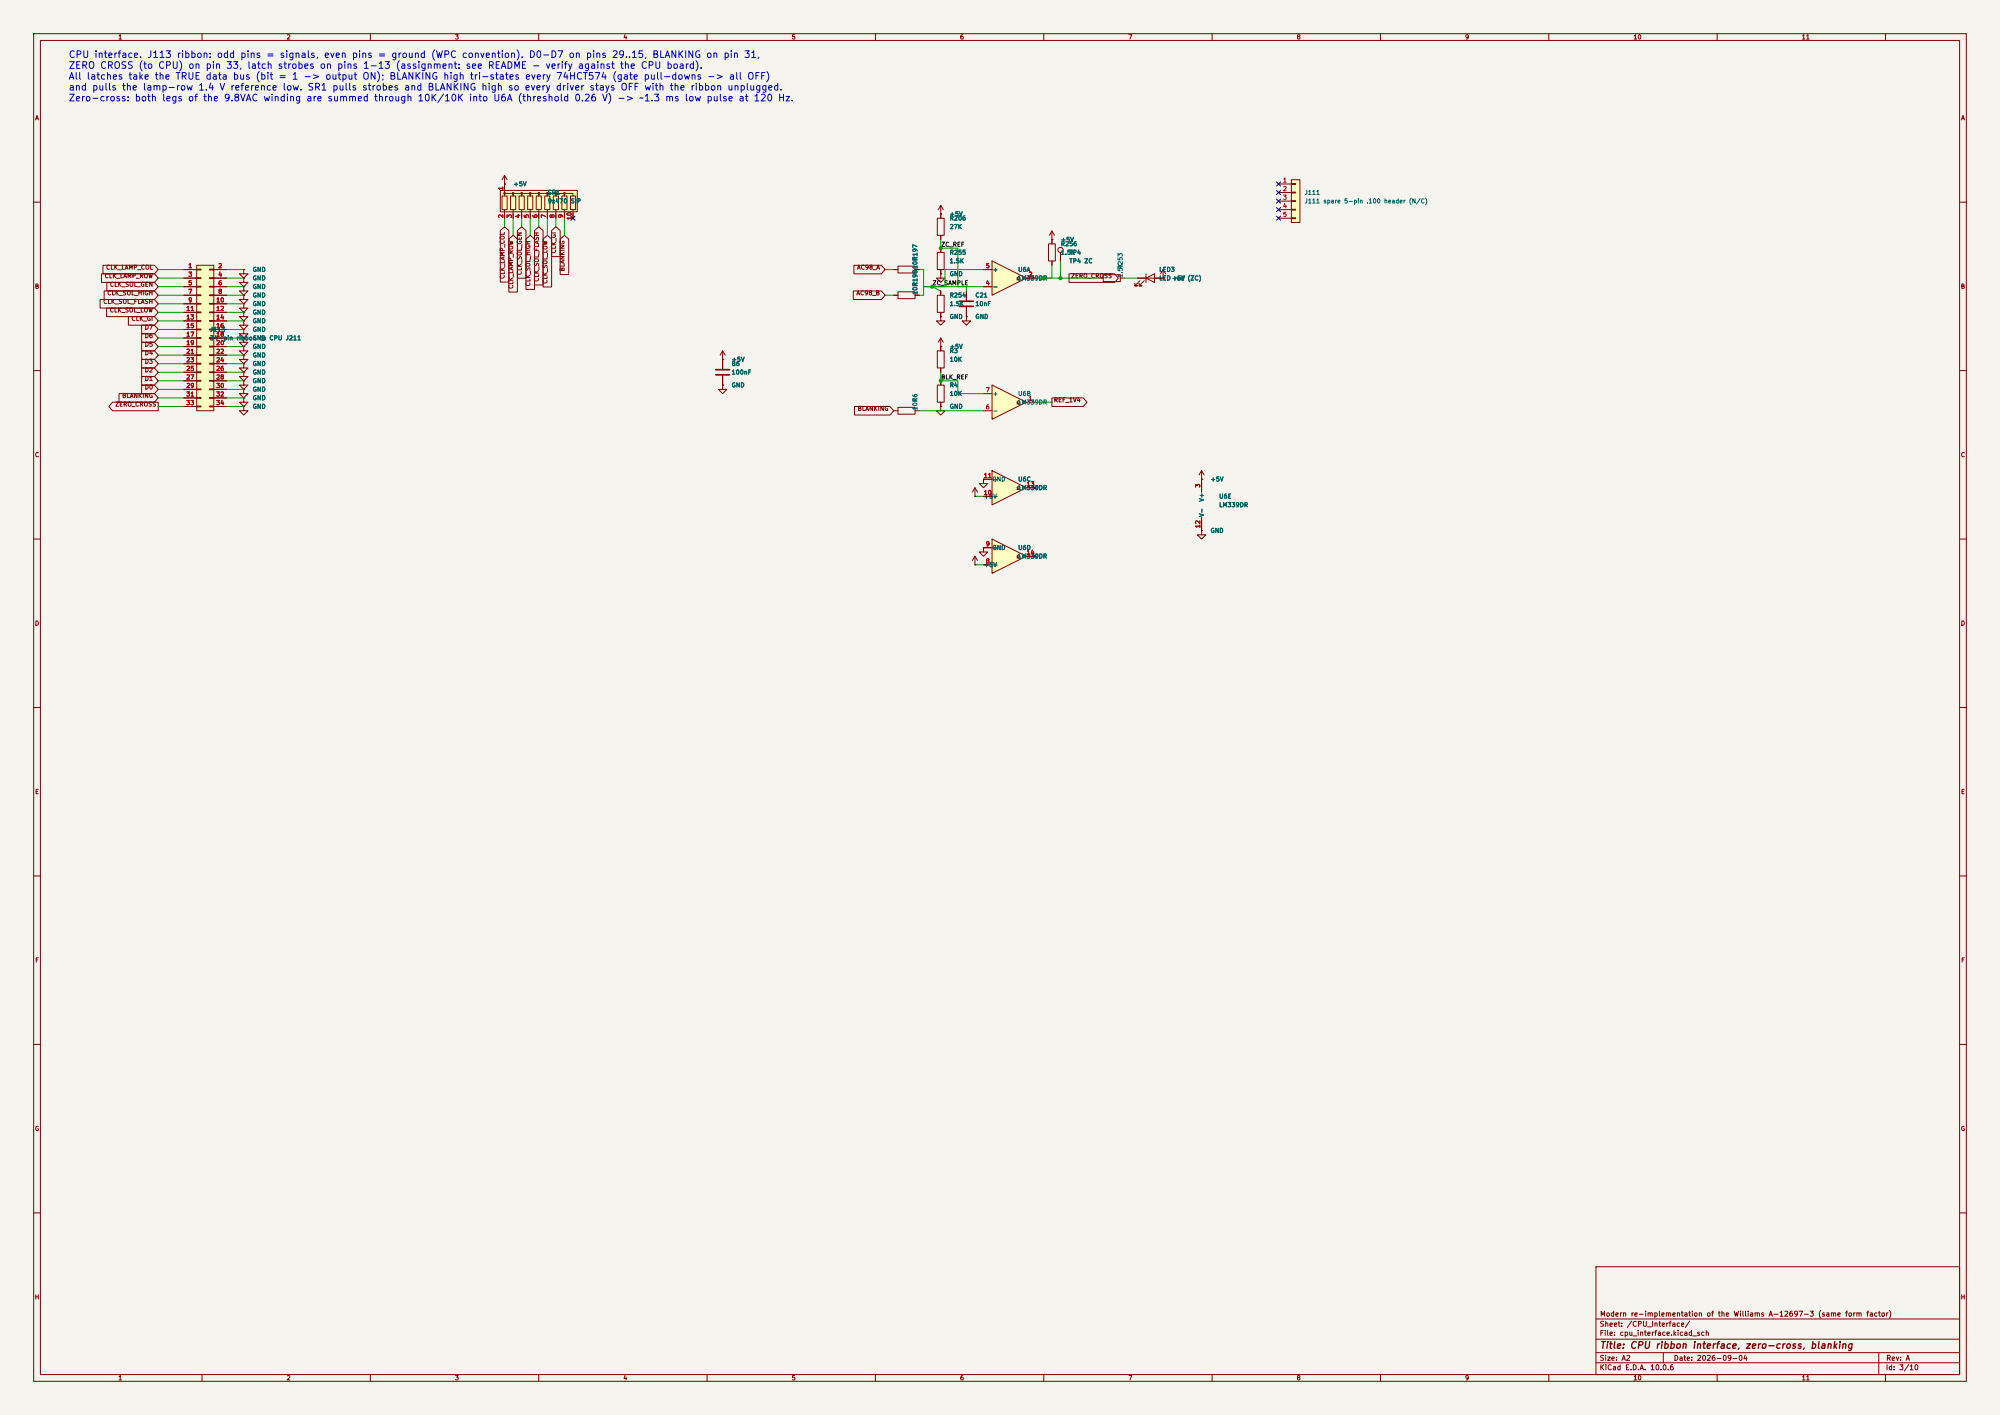
[picture p143: page 3]

BLK_REF ZC_REF ZC_SAMPLE CPU interface. J113 ribbon: odd pins = signals, even pins = ground (WPC convention). D0-D7 on pins 29..15, BLANKING on pin 31,
ZERO CROSS (to CPU) on pin 33, latch strobes on pins 1-13 (assignment: see README - verify against the CPU board).
All latches take the TRUE data bus (bit = 1 -> output ON); BLANKING high tri-states every 74HCT574 (gate pull-downs -> all OFF)
and pulls the lamp-row 1.4 V reference low. SR1 pulls strobes and BLANKING high so every driver stays OFF with the ribbon unplugged.

J111 spare 5-pin .100 header (N/C) GND

34-pin ribbon to CPU J211

Modern re-implementation of the Williams A-12697-3 (same form factor)
Sheet: /CPU_Interface/
File: cpu_interface.kicad_sch
Title: CPU ribbon interface, zero-cross, blanking

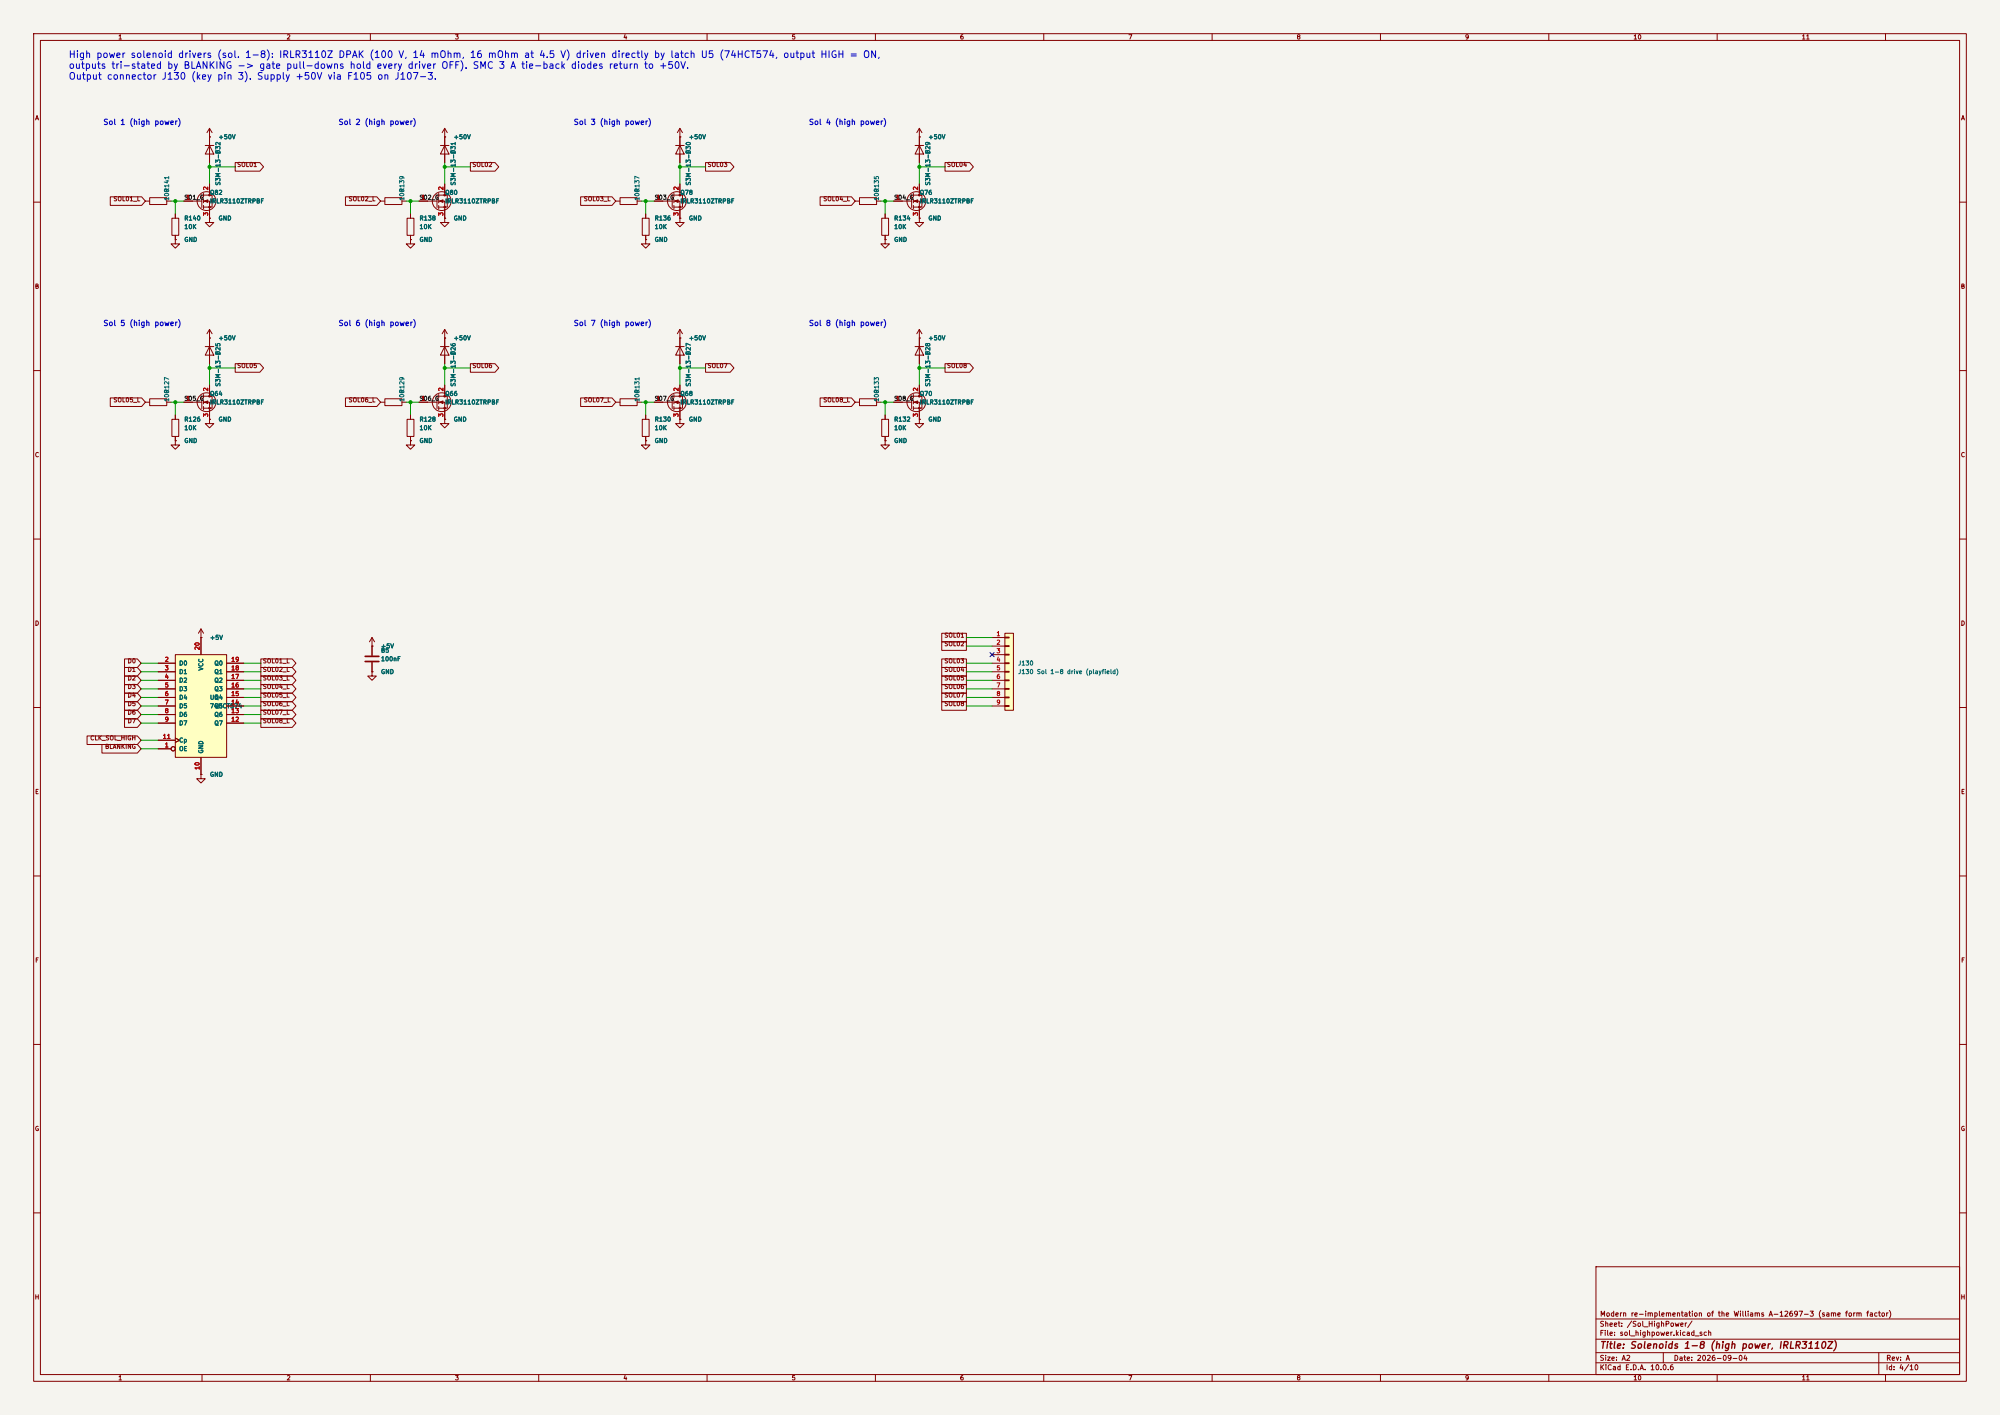
[picture p144: page 4]

High power solenoid drivers (sol. 1-8): IRLR3110Z DPAK (100 V, 14 mOhm, 16 mOhm at 4.5 V) driven directly by latch U5 (74HCT574, output HIGH = ON,
outputs tri-stated by BLANKING -> gate pull-downs hold every driver OFF). SMC 3 A tie-back diodes return to +50V.
Output connector J130 (key pin 3). Supply +50V via F105 on J107-3.

Sheet: /Sol_HighPower/
File: sol_highpower.kicad_sch
Title: Solenoids 1-8 (high power, IRLR3110Z)

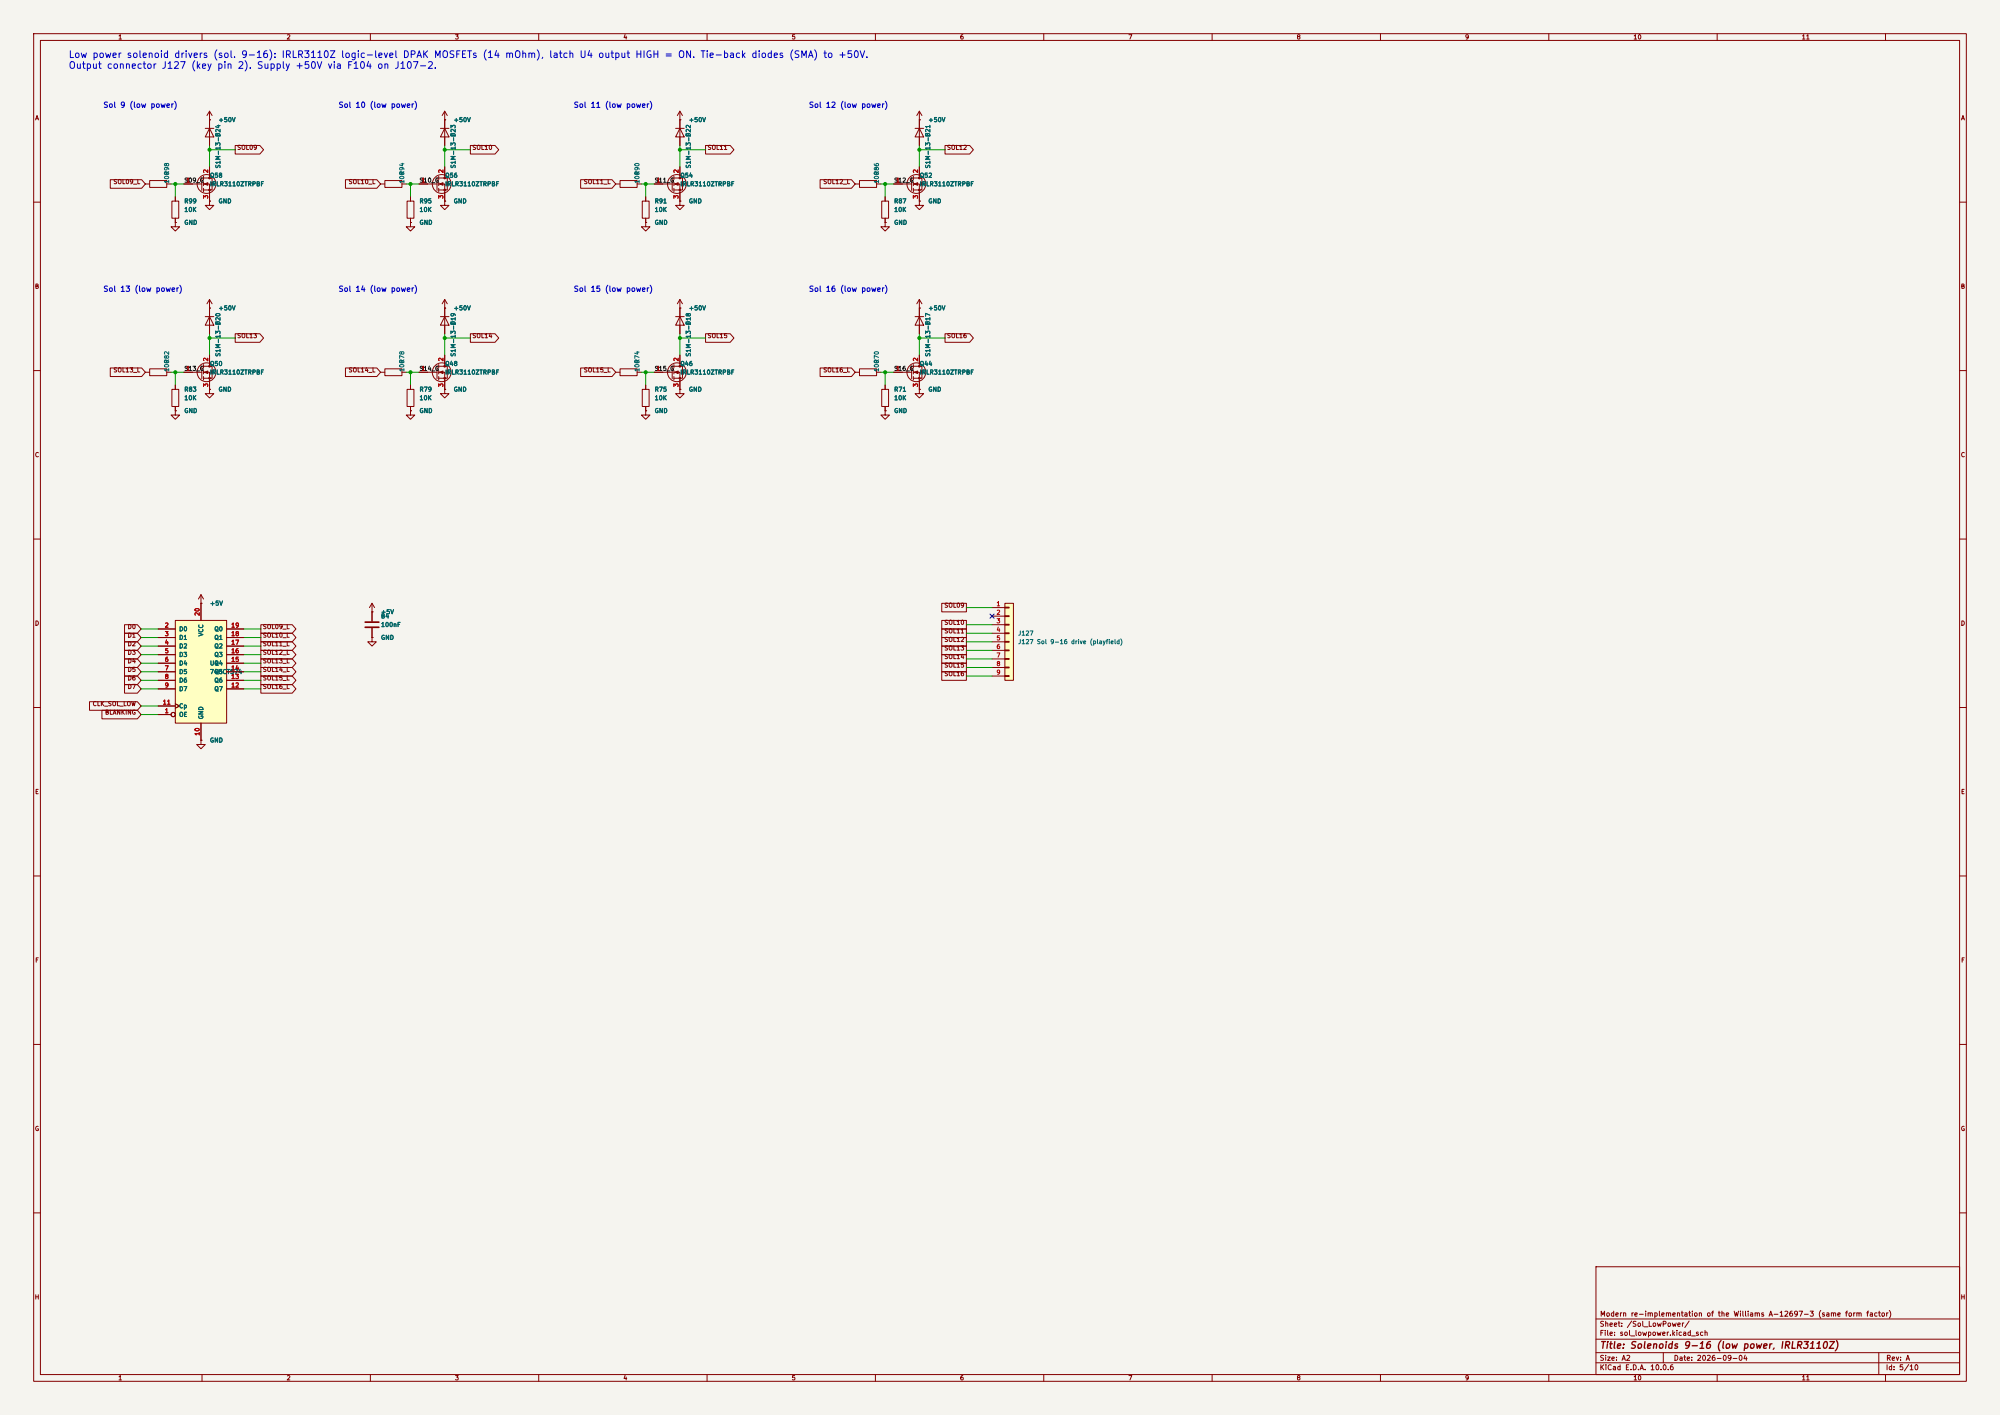
[picture p145: page 5]

Low power solenoid drivers (sol. 9-16): IRLR3110Z logic-level DPAK MOSFETs (14 mOhm), latch U4 output HIGH = ON. Tie-back diodes (SMA) to +50V.
Output connector J127 (key pin 2). Supply +50V via F104 on J107-2.

J127 Sol 9-16 drive (playfield) GND

Sheet: /Sol_LowPower/
File: sol_lowpower.kicad_sch
Title: Solenoids 9-16 (low power, IRLR3110Z)

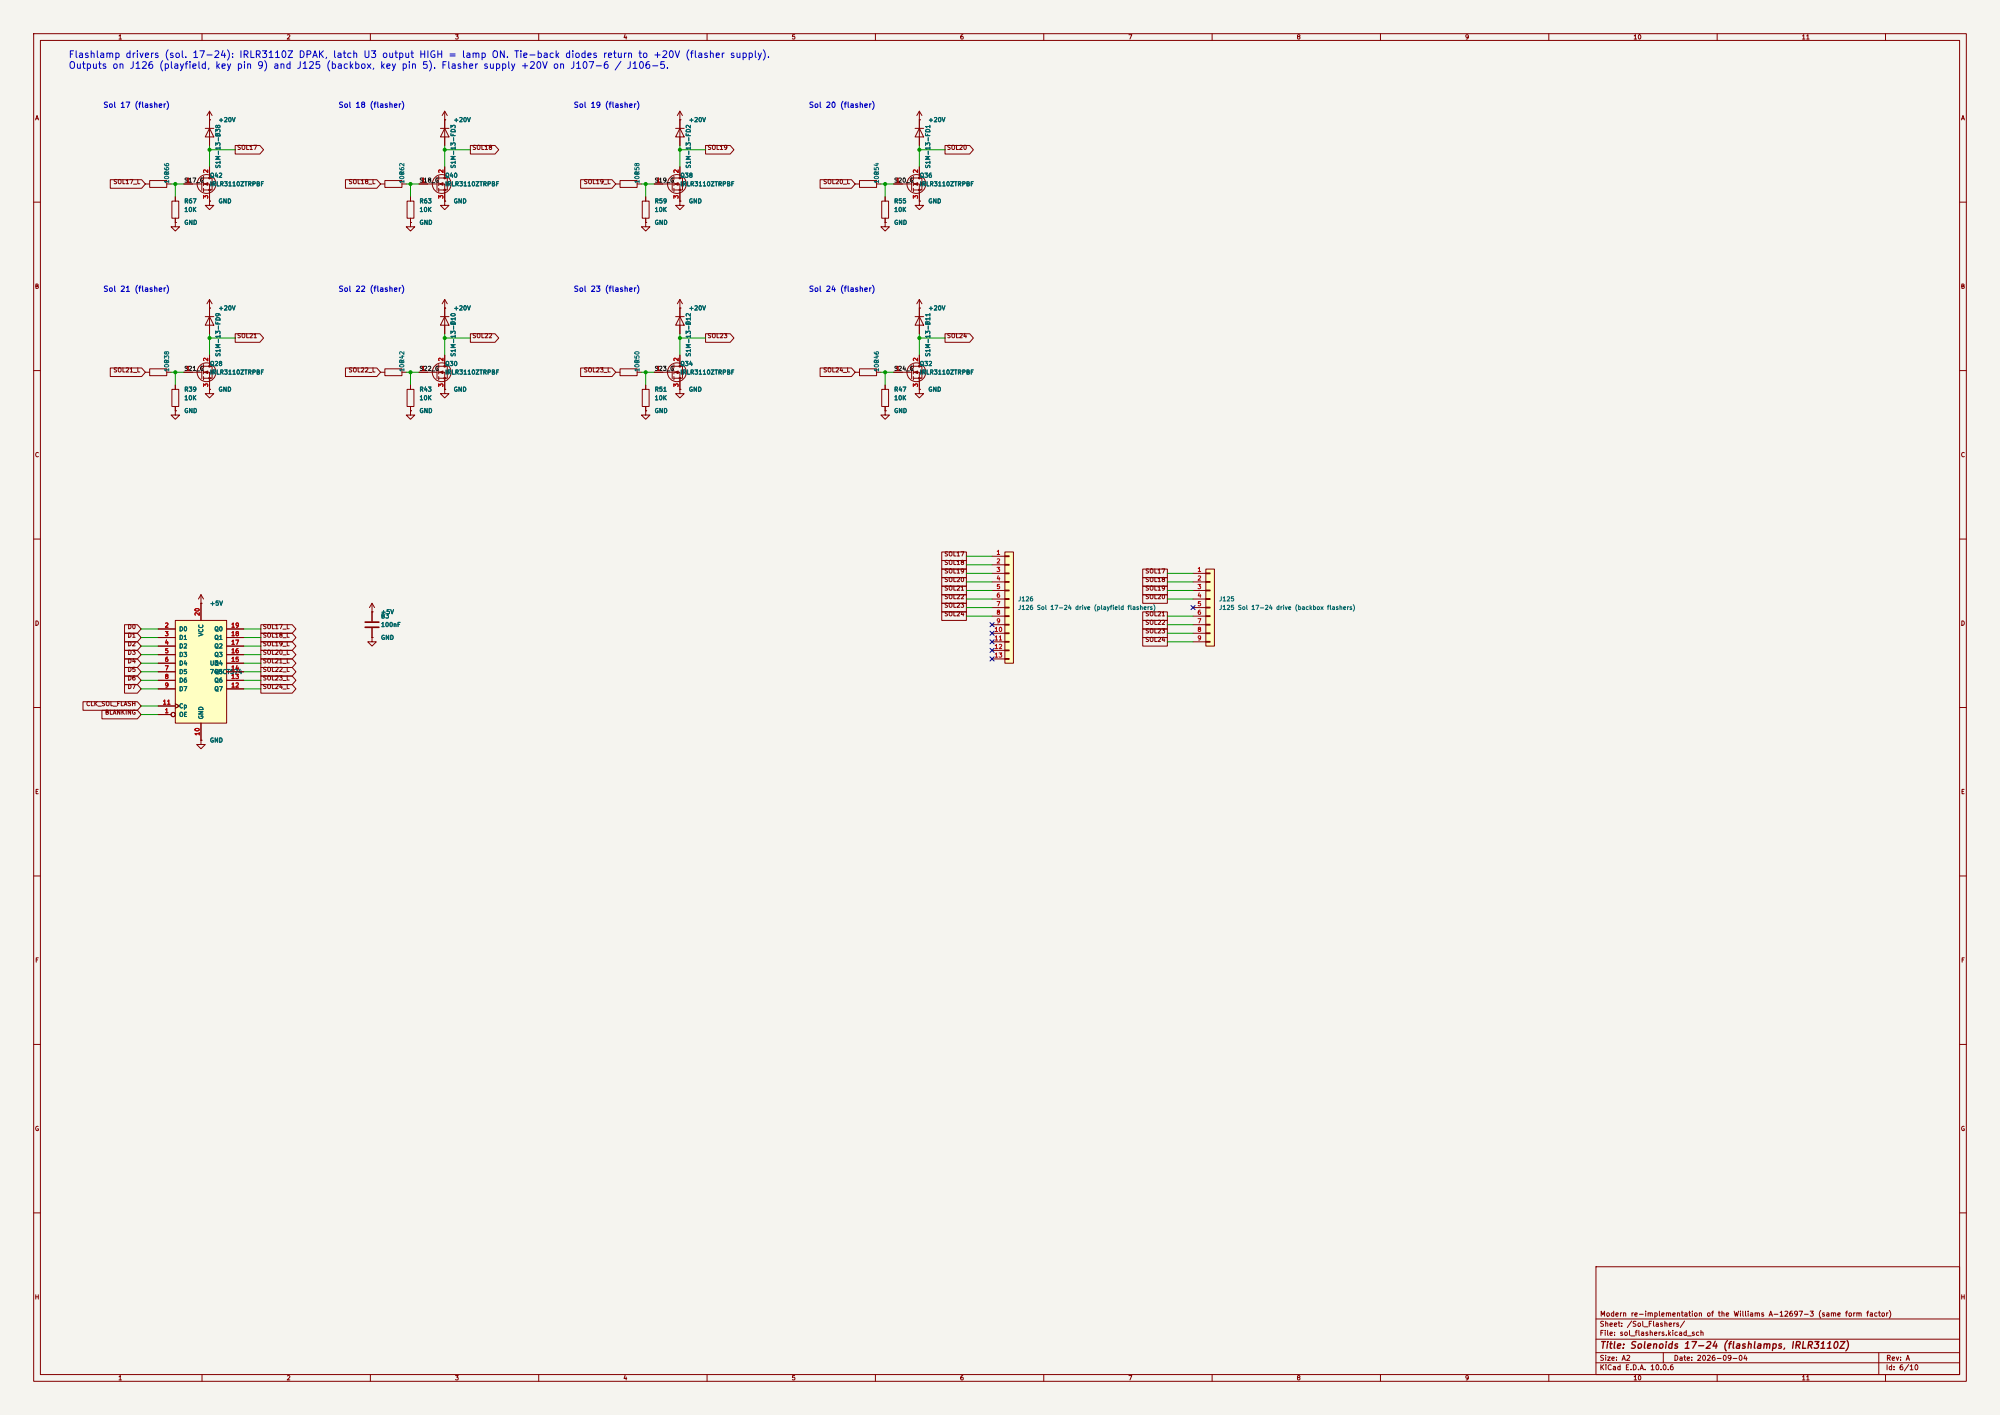
[picture p146: page 6]

Flashlamp drivers (sol. 17-24): IRLR3110Z DPAK, latch U3 output HIGH = lamp ON. Tie-back diodes return to +20V (flasher supply).
Outputs on J126 (playfield, key pin 9) and J125 (backbox, key pin 5). Flasher supply +20V on J107-6 / J106-5.

Modern re-implementation of the Williams A-12697-3 (same form factor) R62 100 B3

J126 Sol 17-24 drive (playfield flashers)

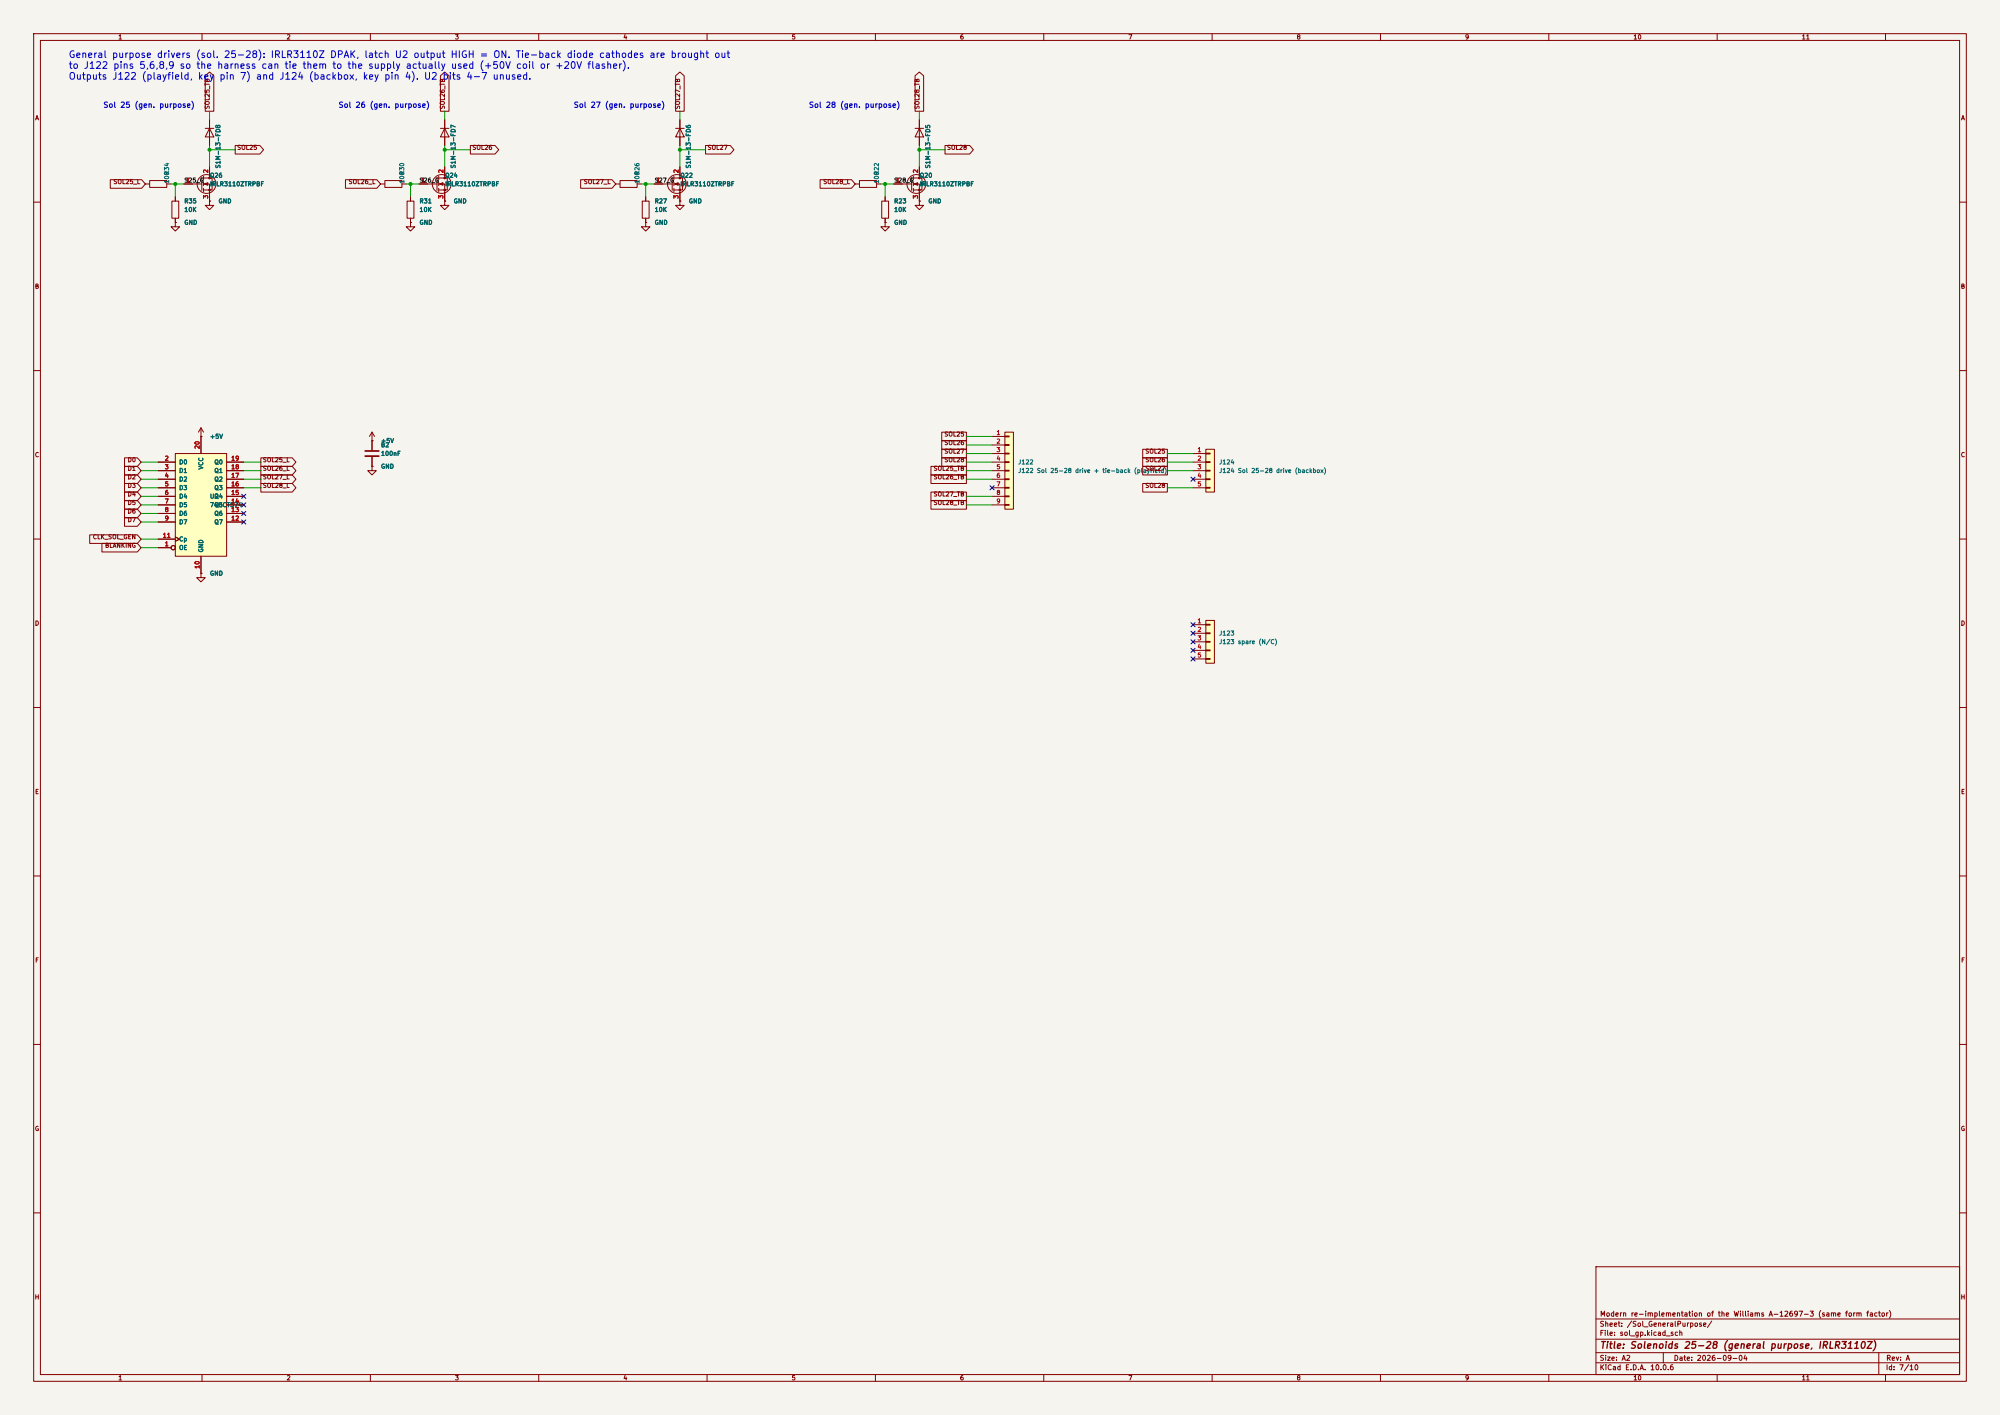
[picture p147: page 7]

to J122 pins 5,6,8,9 so the harness can tie them to the supply actually used (+50V coil or +20V flasher).
Outputs J122 (playfield, key pin 7) and J124 (backbox, key pin 4). U2 bits 4-7 unused.
SOL25 D6D5D4

Sheet: /Sol_GeneralPurpose/
File: sol_gp.kicad_sch
Title: Solenoids 25-28 (general purpose, IRLR3110Z)

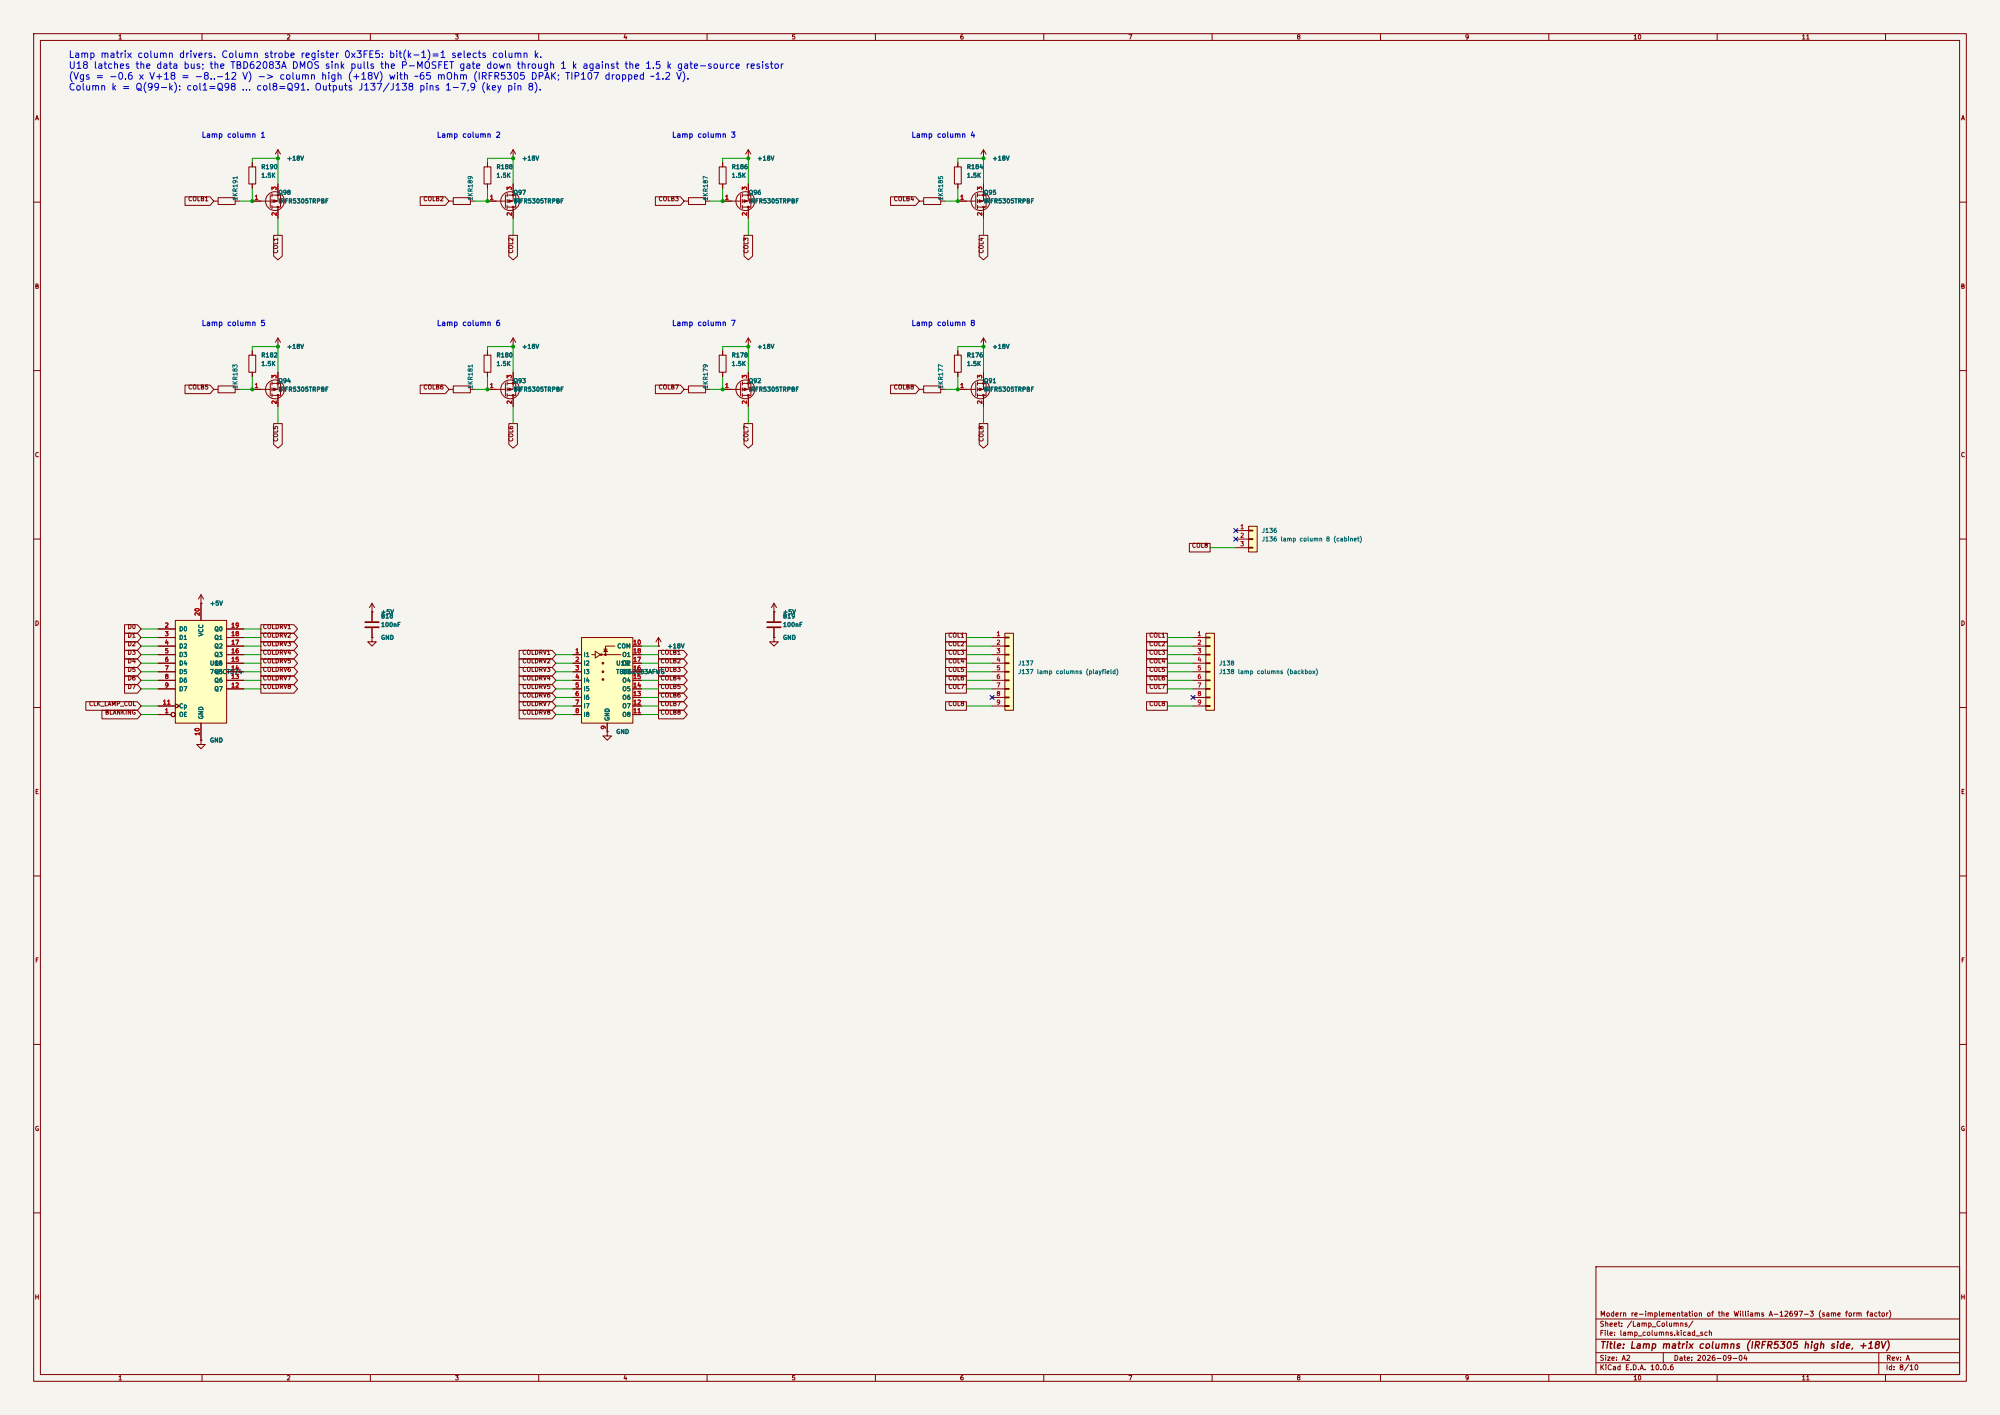
[picture p148: page 8]

Lamp matrix column drivers. Column strobe register 0x3FE5: bit(k-1)=1 selects column k.
U18 latches the data bus; the TBD62083A DMOS sink pulls the P-MOSFET gate down through 1 k against the 1.5 k gate-source resistor
(Vgs = -0.6 x V+18 = -8..-12 V) -> column high (+18V) with ~65 mOhm (IRFR5305 DPAK; TIP107 dropped ~1.2 V).
Column k = Q(99-k): col1=Q98 ... col8=Q91. Outputs J137/J138 pins 1-7,9 (key pin 8).
IRFR5305TRPBF +18V R182

J136 lamp column 8 (cabinet) GND

Sheet: /Lamp_Columns/
File: lamp_columns.kicad_sch
Title: Lamp matrix columns (IRFR5305 high side, +18V)

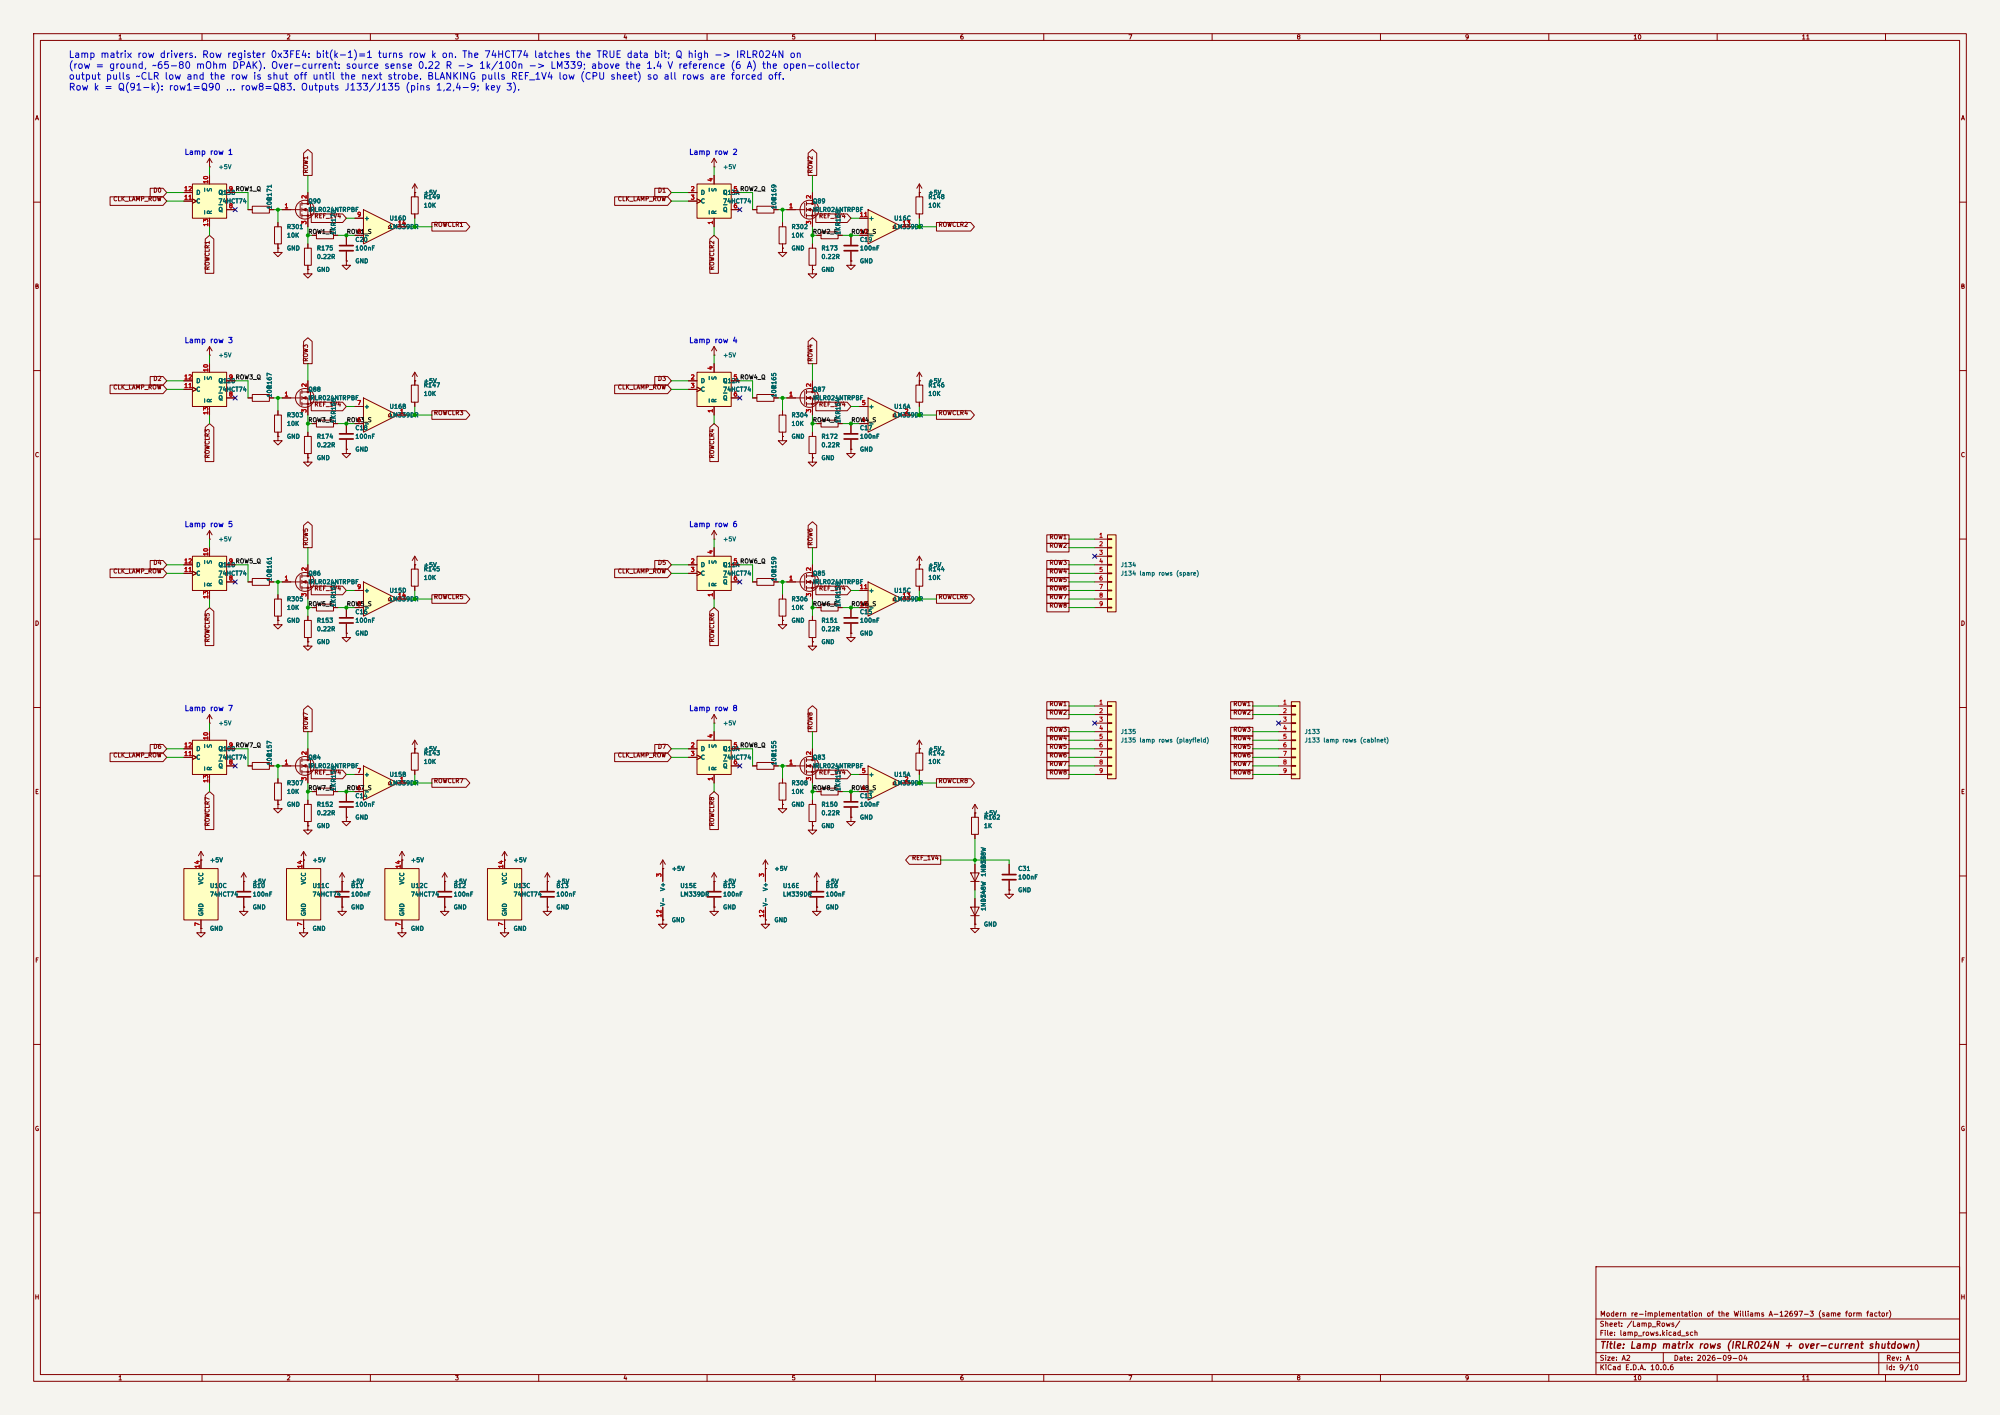
[picture p149: page 9]

ROW2_S Lamp matrix row drivers. Row register 0x3FE4: bit(k-1)=1 turns row k on. The 74HCT74 latches the TRUE data bit; Q high -> IRLR024N on
(row = ground, ~65-80 mOhm DPAK). Over-current: source sense 0.22 R -> 1k/100n -> LM339; above the 1.4 V reference (6 A) the open-collector
output pulls ~CLR low and the row is shut off until the next strobe. BLANKING pulls REF_1V4 low (CPU sheet) so all rows are forced off.
Row k = Q(91-k): row1=Q90 ... row8=Q83. Outputs J133/J135 (pins 1,2,4-9; key 3).
100nF GND R171 100 +5V Q
GND U13B

Sheet: /Lamp_Rows/
File: lamp_rows.kicad_sch
Title: Lamp matrix rows (IRLR024N + over-current shutdown)

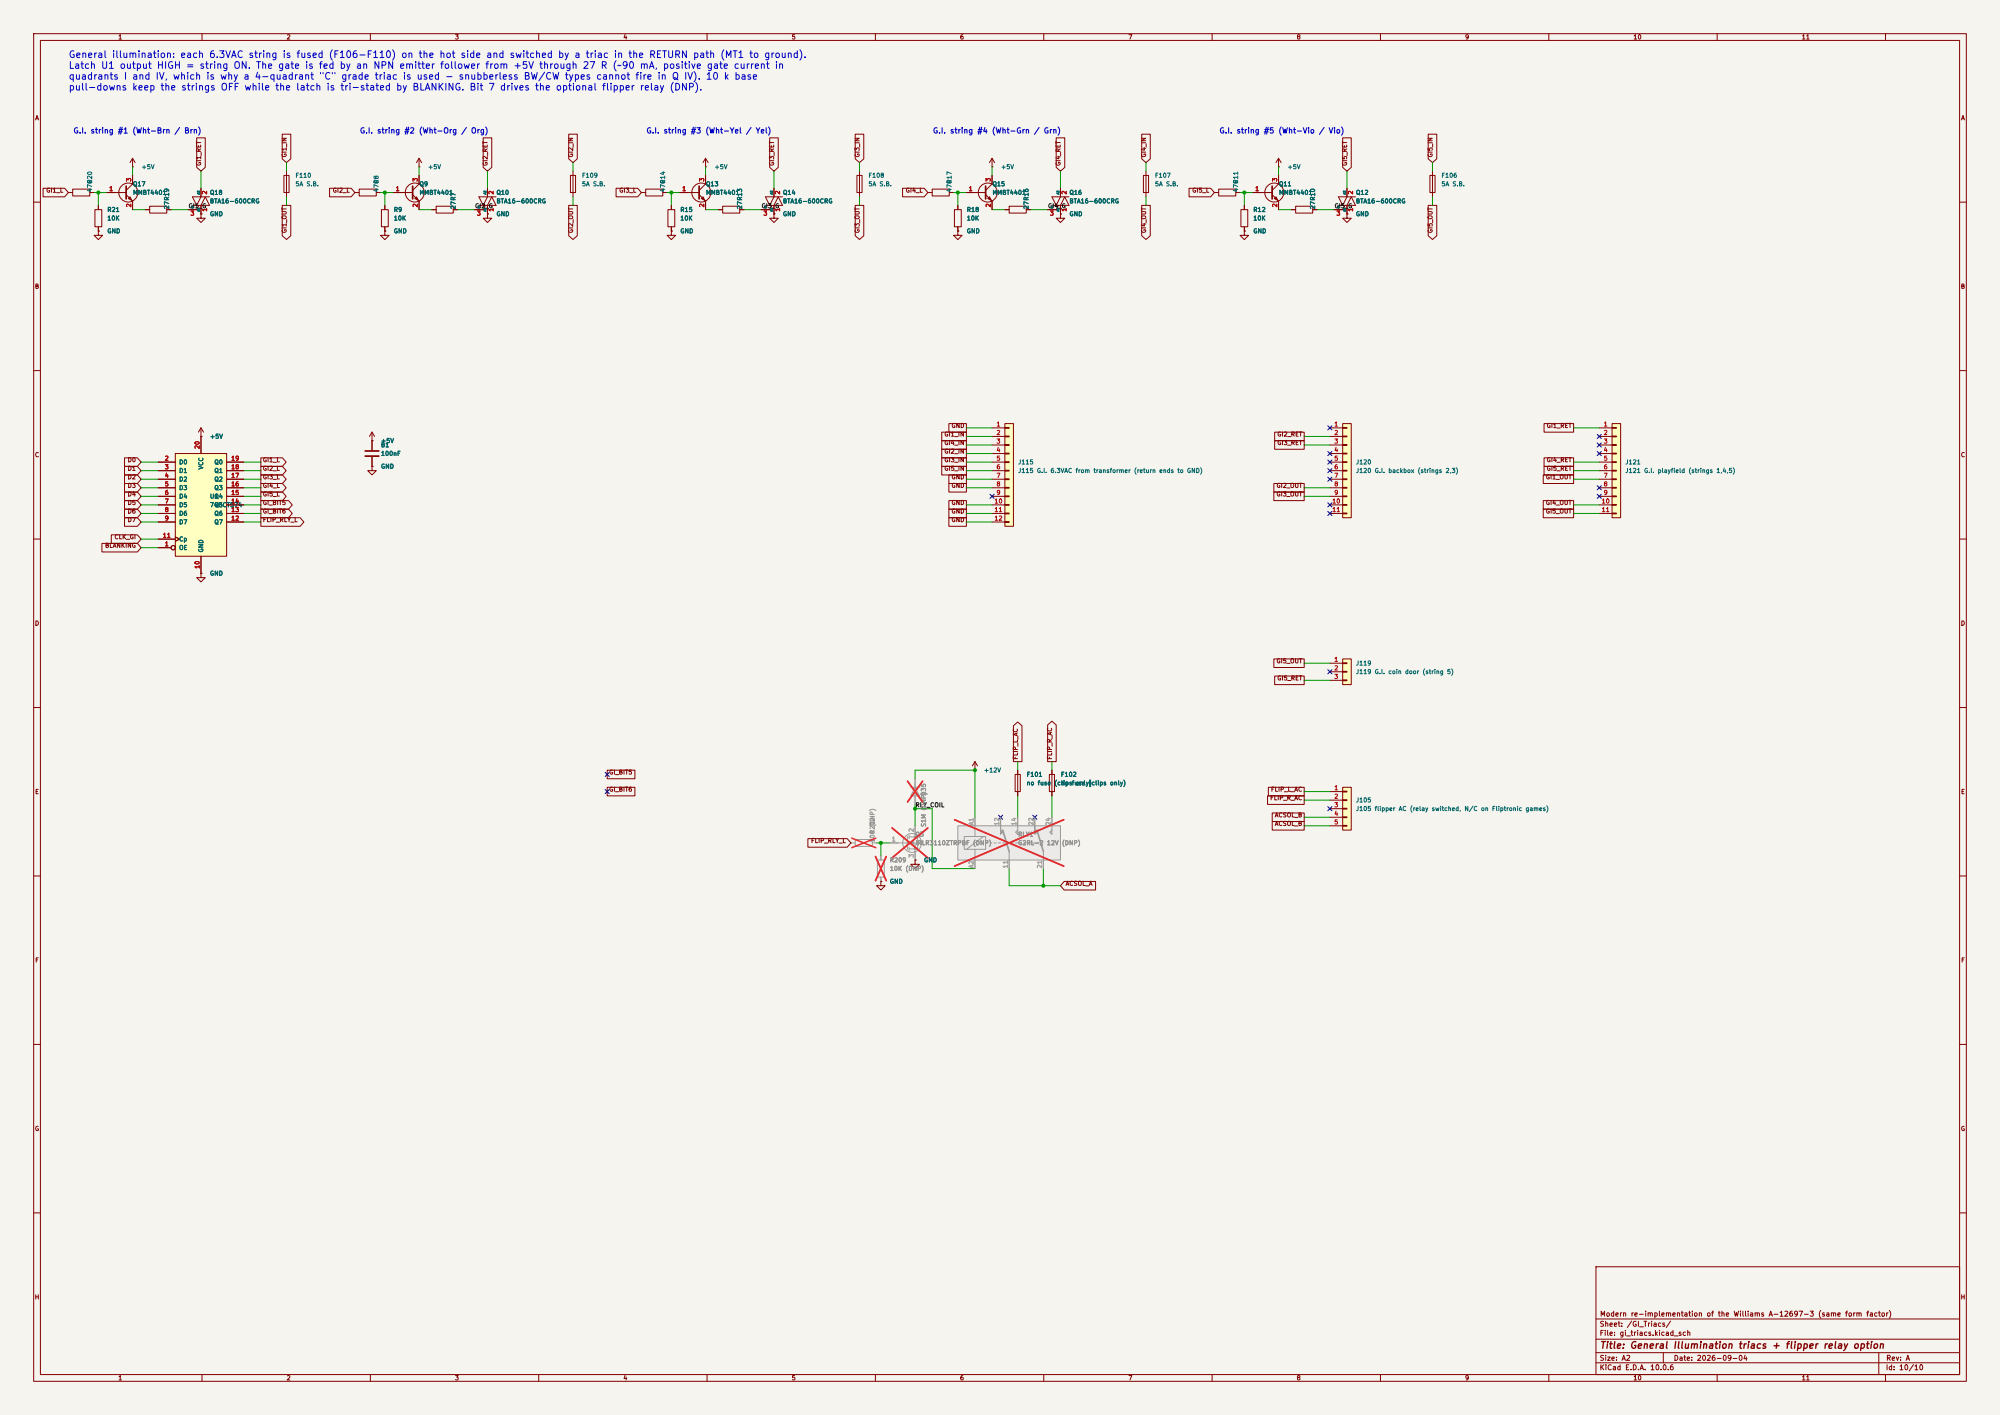
[picture p150: page 10]

General illumination: each 6.3VAC string is fused (F106-F110) on the hot side and switched by a triac in the RETURN path (MT1 to ground).
Latch U1 output HIGH = string ON. The gate is fed by an NPN emitter follower from +5V through 27 R (~90 mA, positive gate current in
quadrants I and IV, which is why a 4-quadrant "C" grade triac is used - snubberless BW/CW types cannot fire in Q IV). 10 k base
pull-downs keep the strings OFF while the latch is tri-stated by BLANKING. Bit 7 drives the optional flipper relay (DNP).

Modern re-implementation of the Williams A-12697-3 (same form factor) R13 27

no fuse (clips only) Q3

Sheet: /GI_Triacs/
File: gi_triacs.kicad_sch
Title: General Illumination triacs + flipper relay option
