lolz0r/Williams-WPC-Power-Driver-Board-A-12697-3/variants/jlcpcb/research/C4697.pdf

客 户
确 认

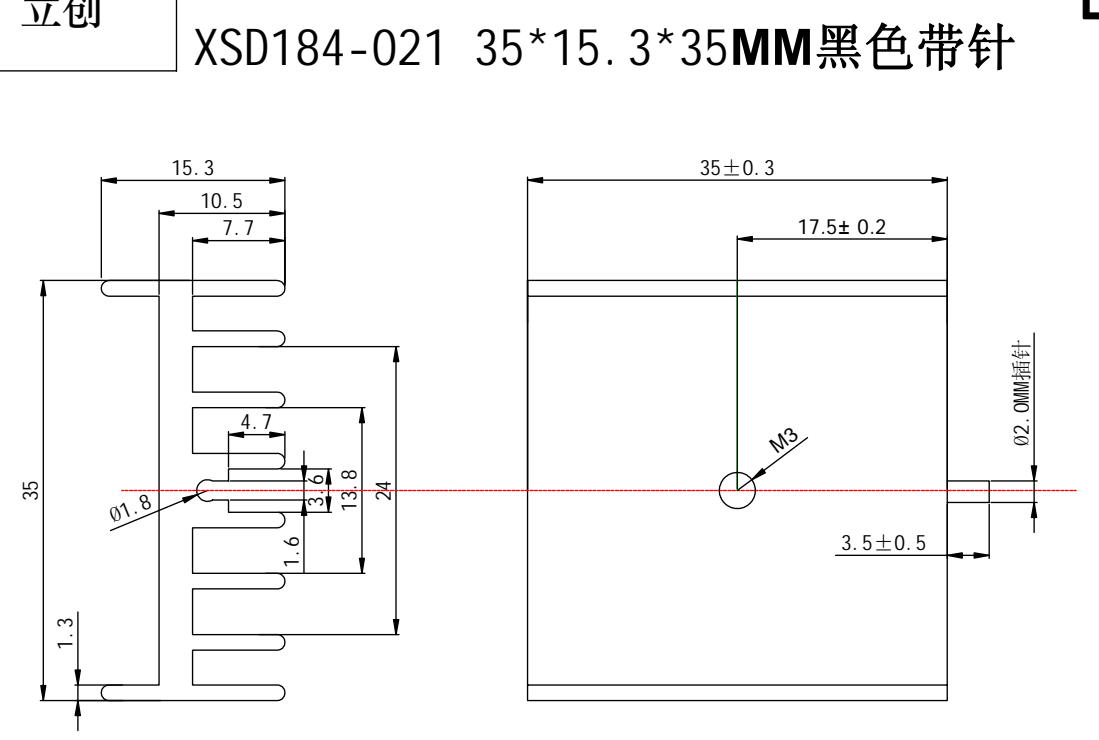
[picture p151: page 1]
黄国真; 客户产品编号：C4697; 欧凤梅; XSD184-021 35*15.3*35MM黑色带针; Ø2.0MM插针

深圳市鑫顺达电子科技有限公司 技 术 参 数 | 表面处理 | 氧化黑色

未注尺寸公差依照一般公差 | 范 围 ≥100-150mm ≥150-200mm ≥200-250mm ≥250-300mm 300mm以上 | 公差值 Ø 模具规格 ±0.40 理论重量 ±0.50 截 面 积 mm ±0.65 2 ±0.80 mm 周 长 ±1.0 | 材 质 单 位 比 例 版 次 | 6063-T5铝 mm A/0 | 产品尺寸 制 图 审 核 本厂编号 | 35*15.3*35mm XSD184-021
范 围 0-6mm ≥6-20mm ≥20-50mm ≥50-100mm | 公差值 ±0.10 ±0.15 ±0.20 ±0.30

PDF 檔案使用 "pdfFactory Pro" 試用版本建立 www.pdffactory.com
