lolz0r/Williams-WPC-Power-Driver-Board-A-12697-3/variants/jlcpcb/output/release-candidate/assembly/inner-ground.pdf

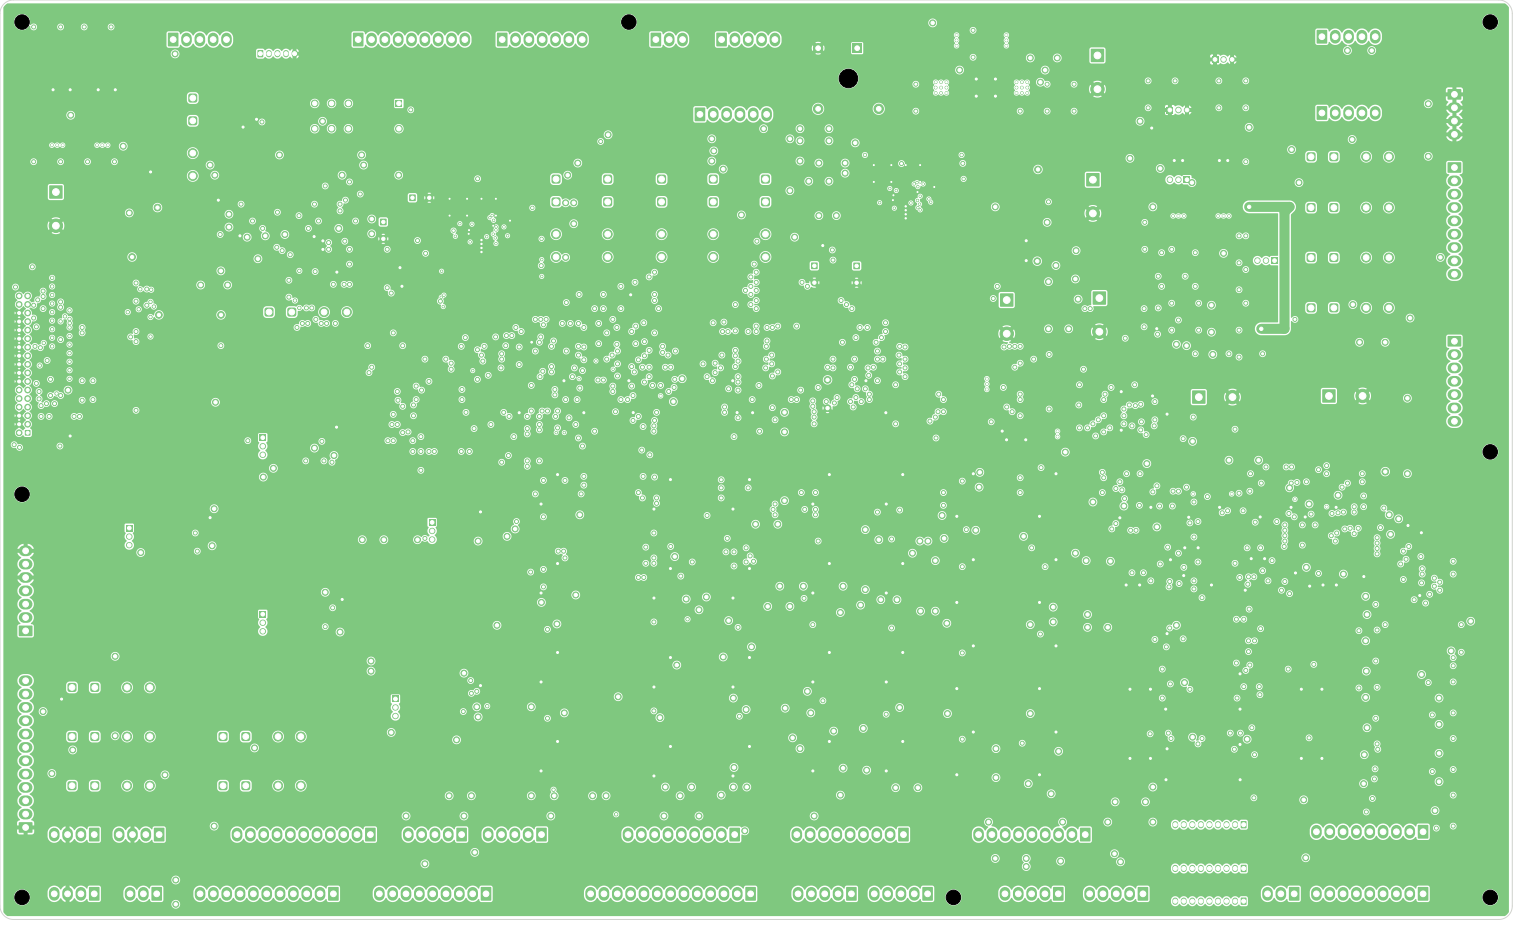
[picture p155: page 1]
