lolz0r/Williams-WPC-Power-Driver-Board-A-12697-3/variants/jlcpcb/output/release-candidate/assembly/inner-signal.pdf

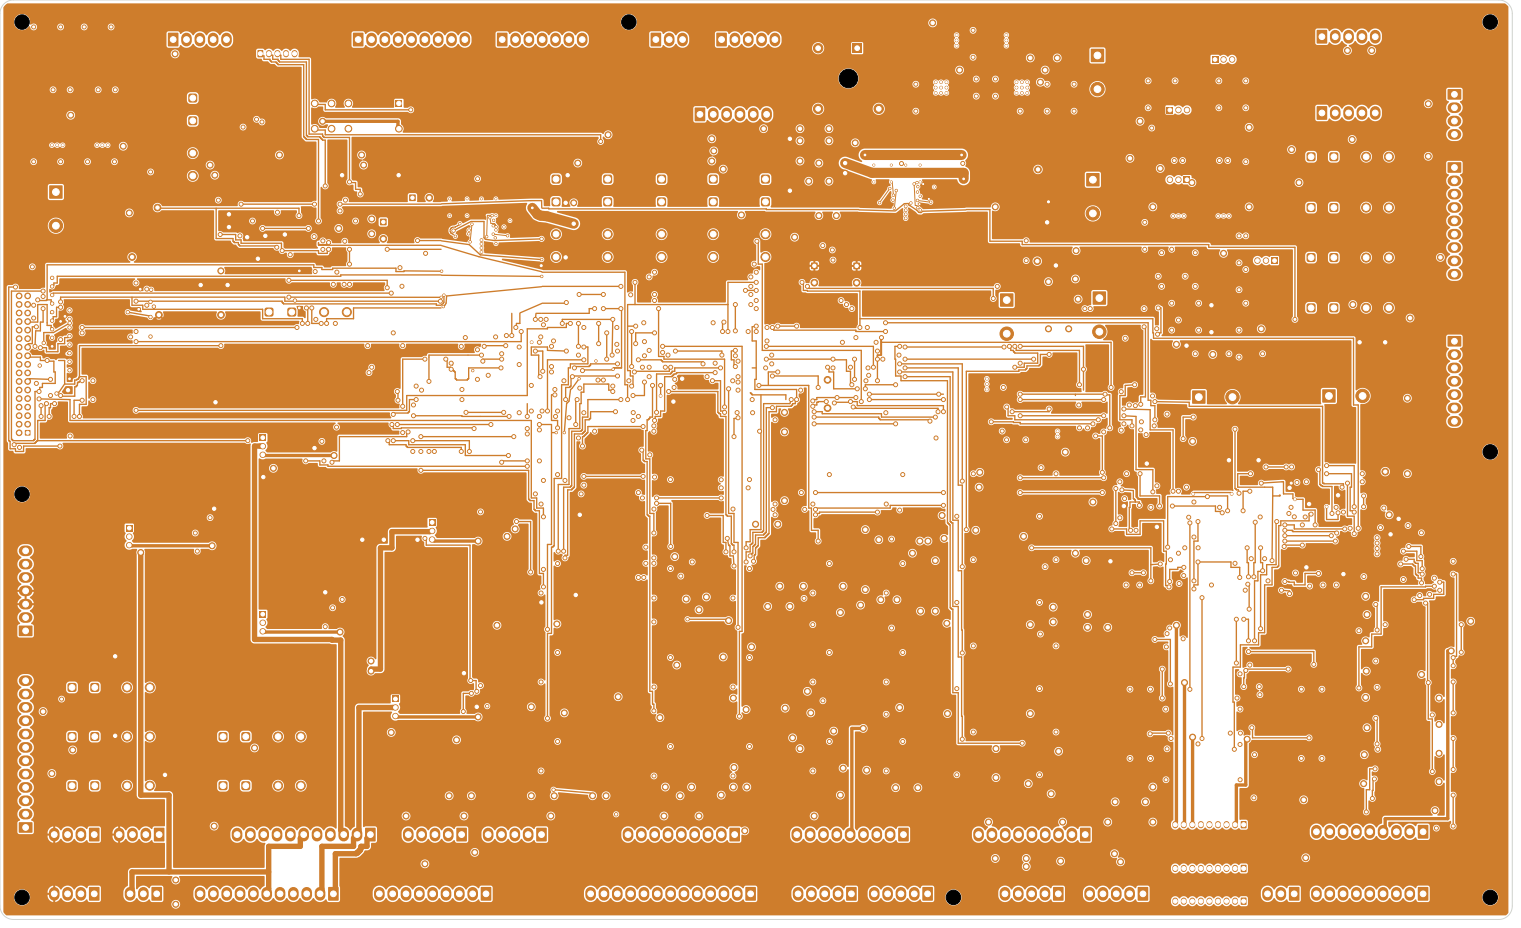
[picture p156: page 1]
