lolz0r/Williams-WPC-Power-Driver-Board-A-12697-3/variants/jlcpcb/output/release-candidate/assembly/top.pdf

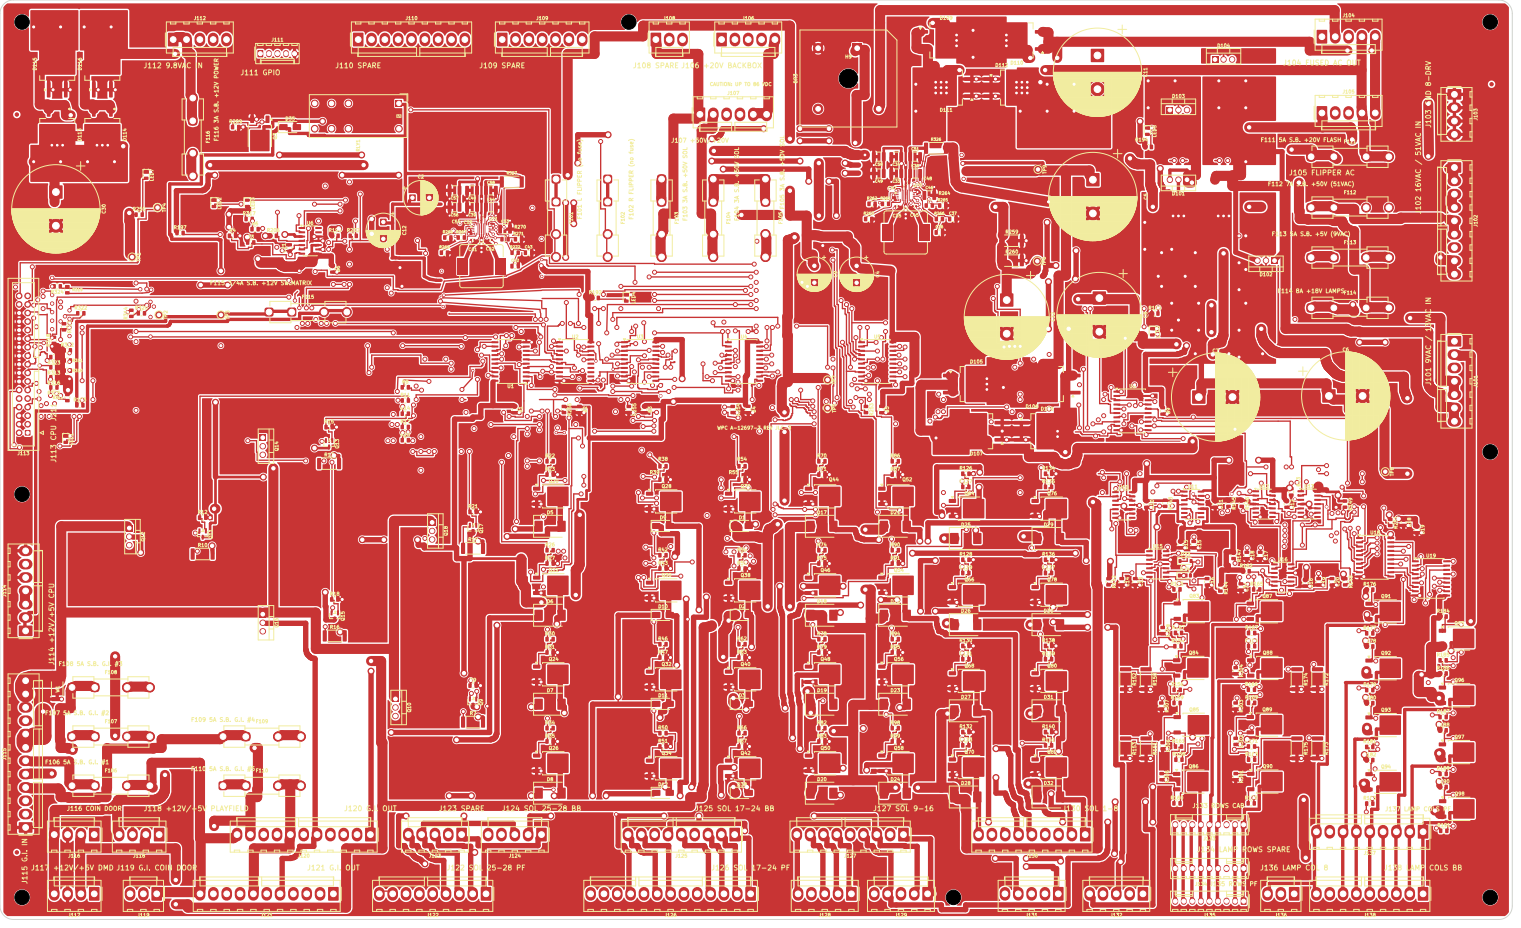
[picture p157: page 1]
