lolz0r/Williams-WPC-Power-Driver-Board-A-12697-3/variants/jlcpcb/research/C32487.pdf

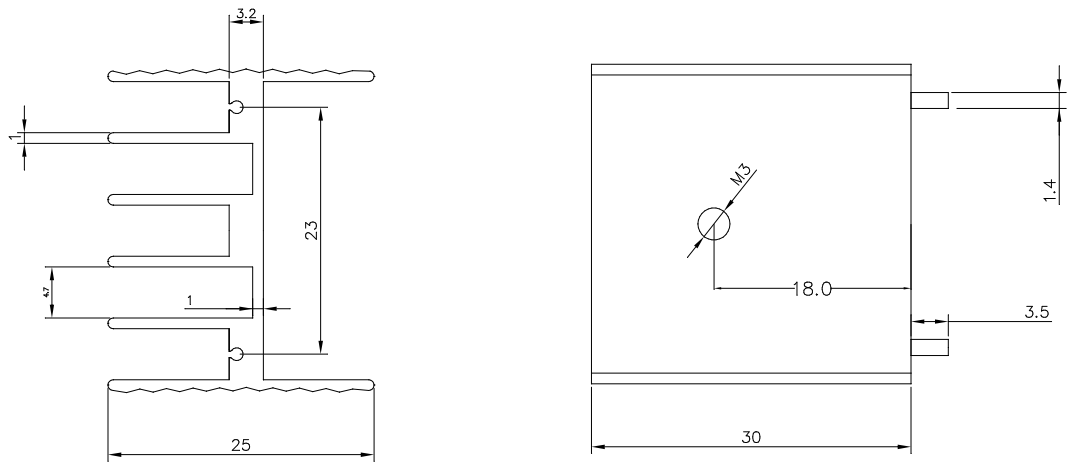
[picture p158: page 1]

PDF 檔案使用 "pdfFactory Pro" 試用版本建立 www.pdffactory.com
