lolz0r/Williams-WPC-Power-Driver-Board-A-12697-3/variants/jlcpcb/research/C4661.pdf

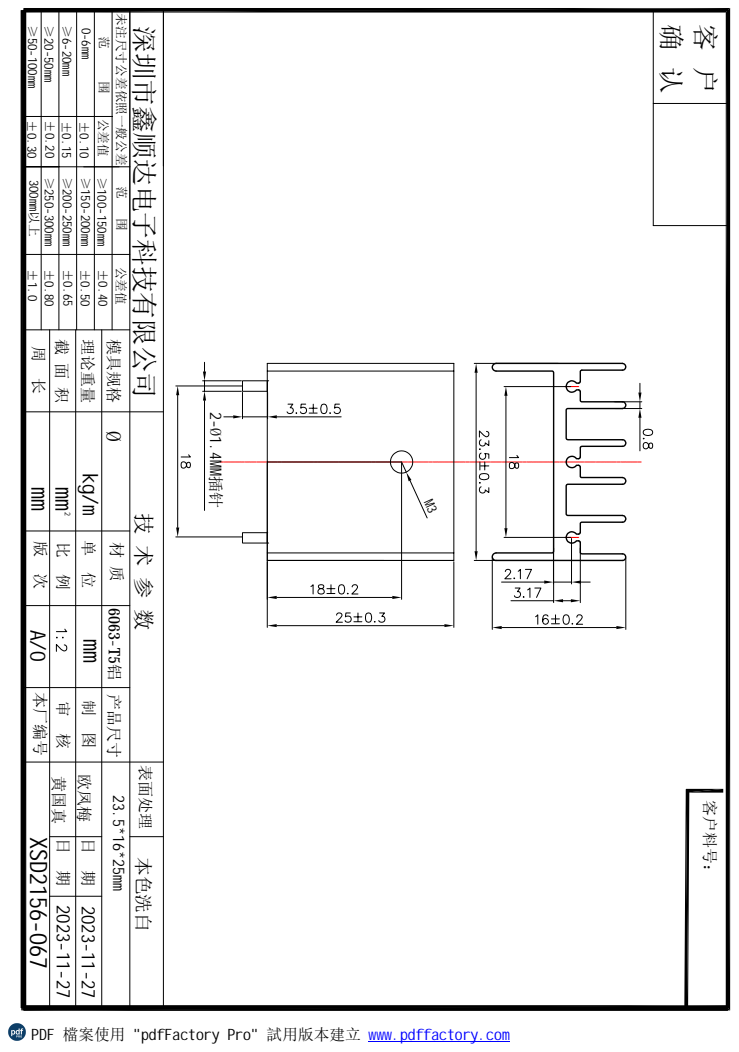
[picture p159: page 1]
6063-T5铝 模具规格; 本厂编号 周 长; 理论重量; XSD2156-067; 产品尺寸; 表面处理; 客户料号：; 未注尺寸公差依照一般公差; 范 围 公差值; 300mm以上 ±1.0; kg/m 2023-11-27 欧凤梅; 本色洗白; 2-Ø1.4MM插针; 深圳市鑫顺达电子科技有限公司; 2023-11-27 黄国真

PDF 檔案使用 "pdfFactory Pro" 試用版本建立 www.pdffactory.com
