lolz0r/Williams-WPC-Power-Driver-Board-A-12697-3/variants/jlcpcb-100/research/jlc-placement-libraries/TE_640445.pdf

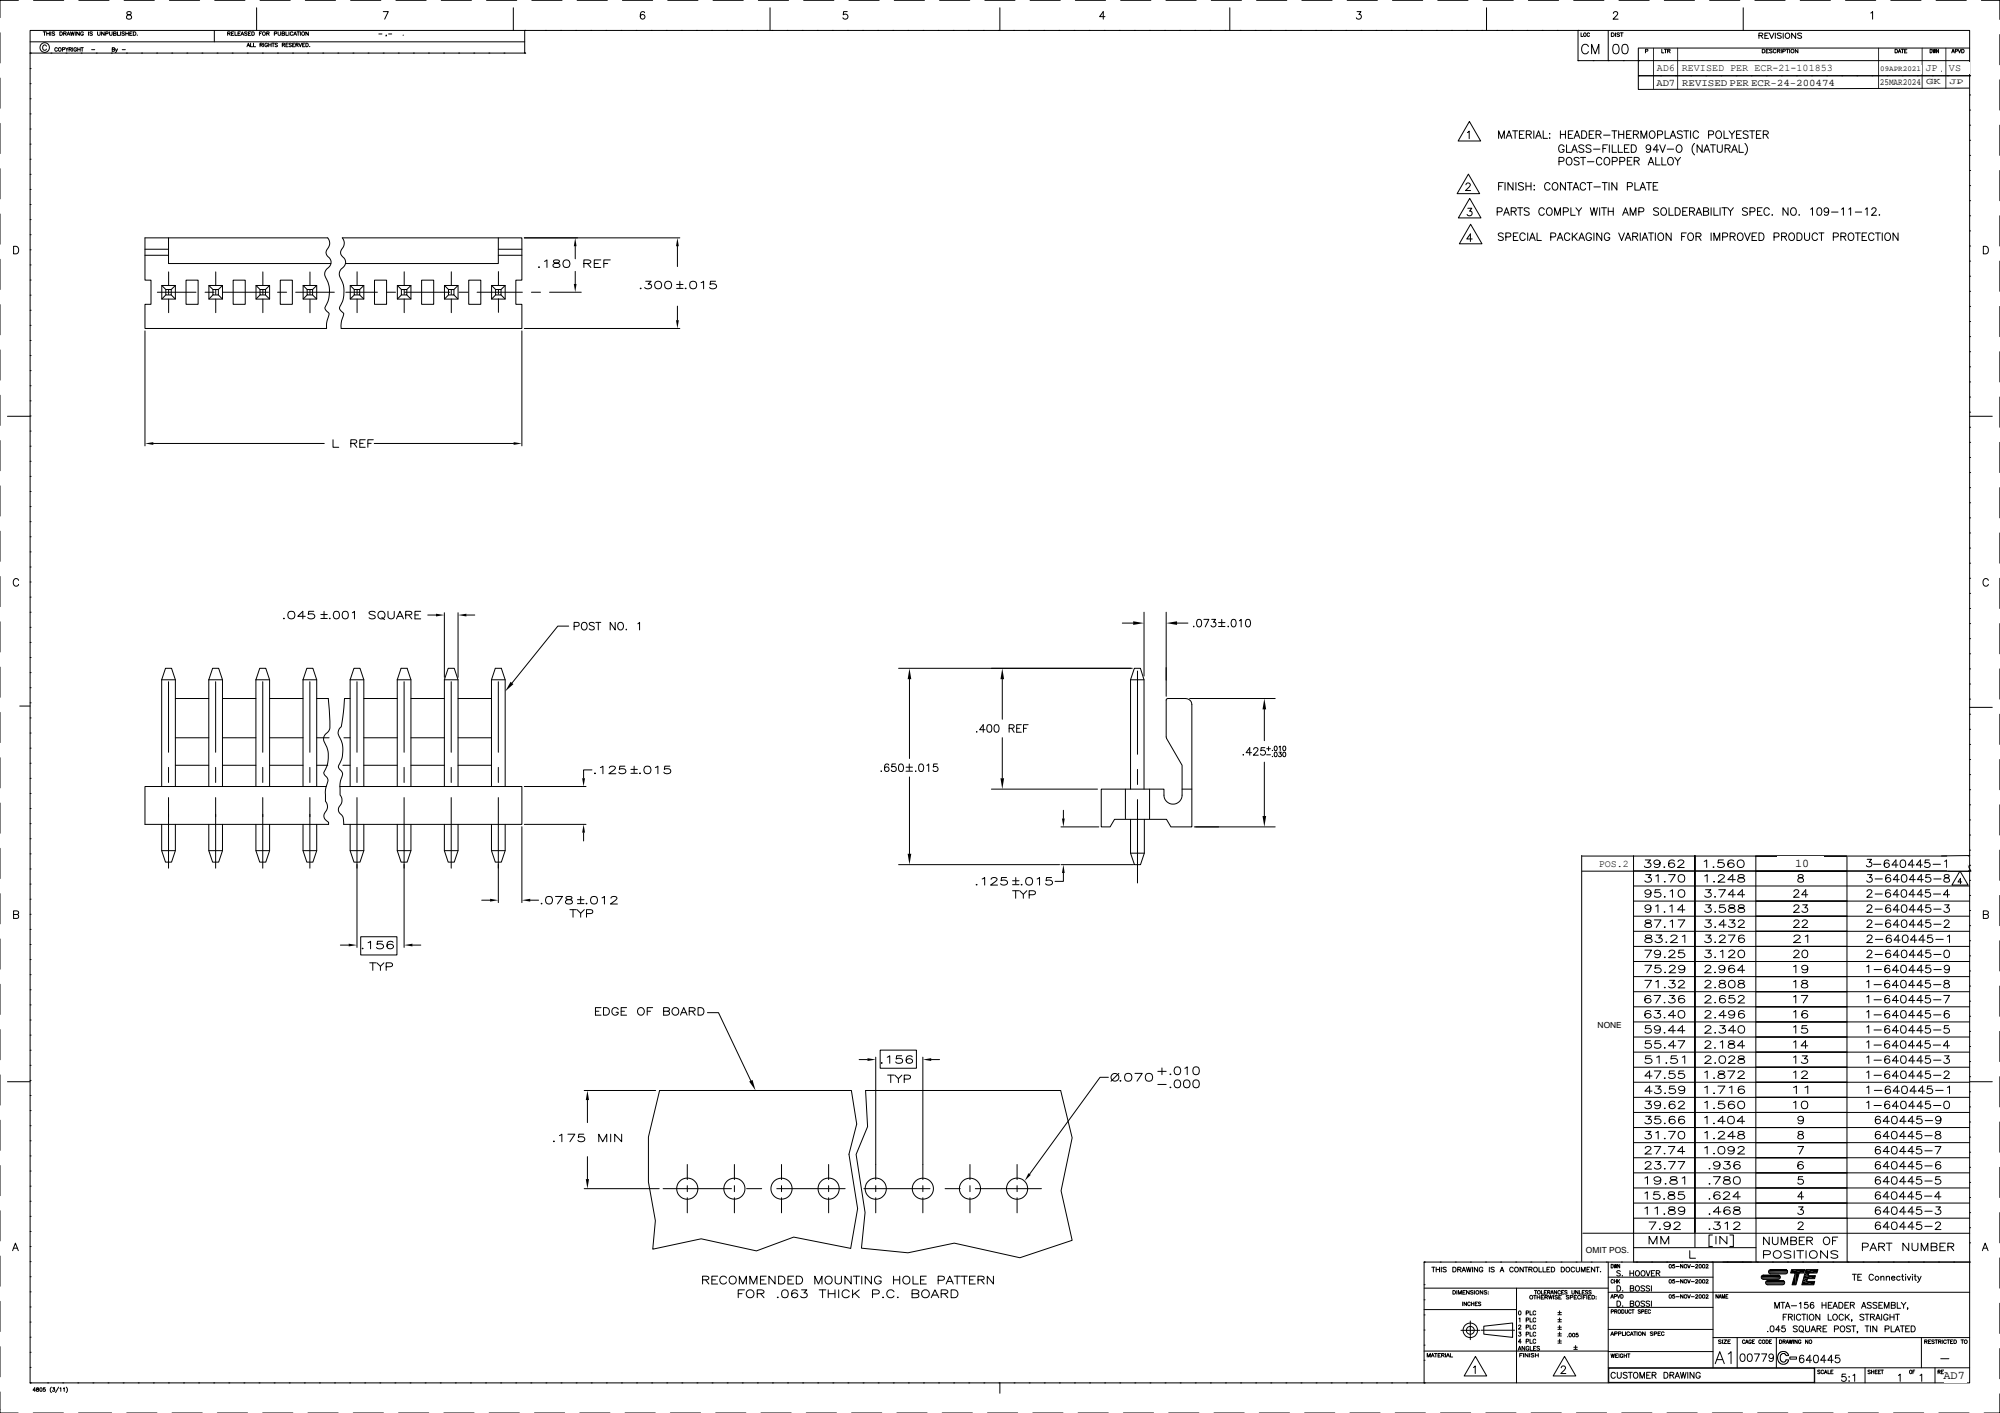
[picture p160: page 1]
REVISED PER ECR-24-200474; 25MAR2024

PRELIMINARY-NOT FOR PRODUCTION

NONE

OMIT POS.
