lolz0r/Williams-WPC-Power-Driver-Board-A-12697-3/output/release-candidate/assembly/inner-ground.pdf

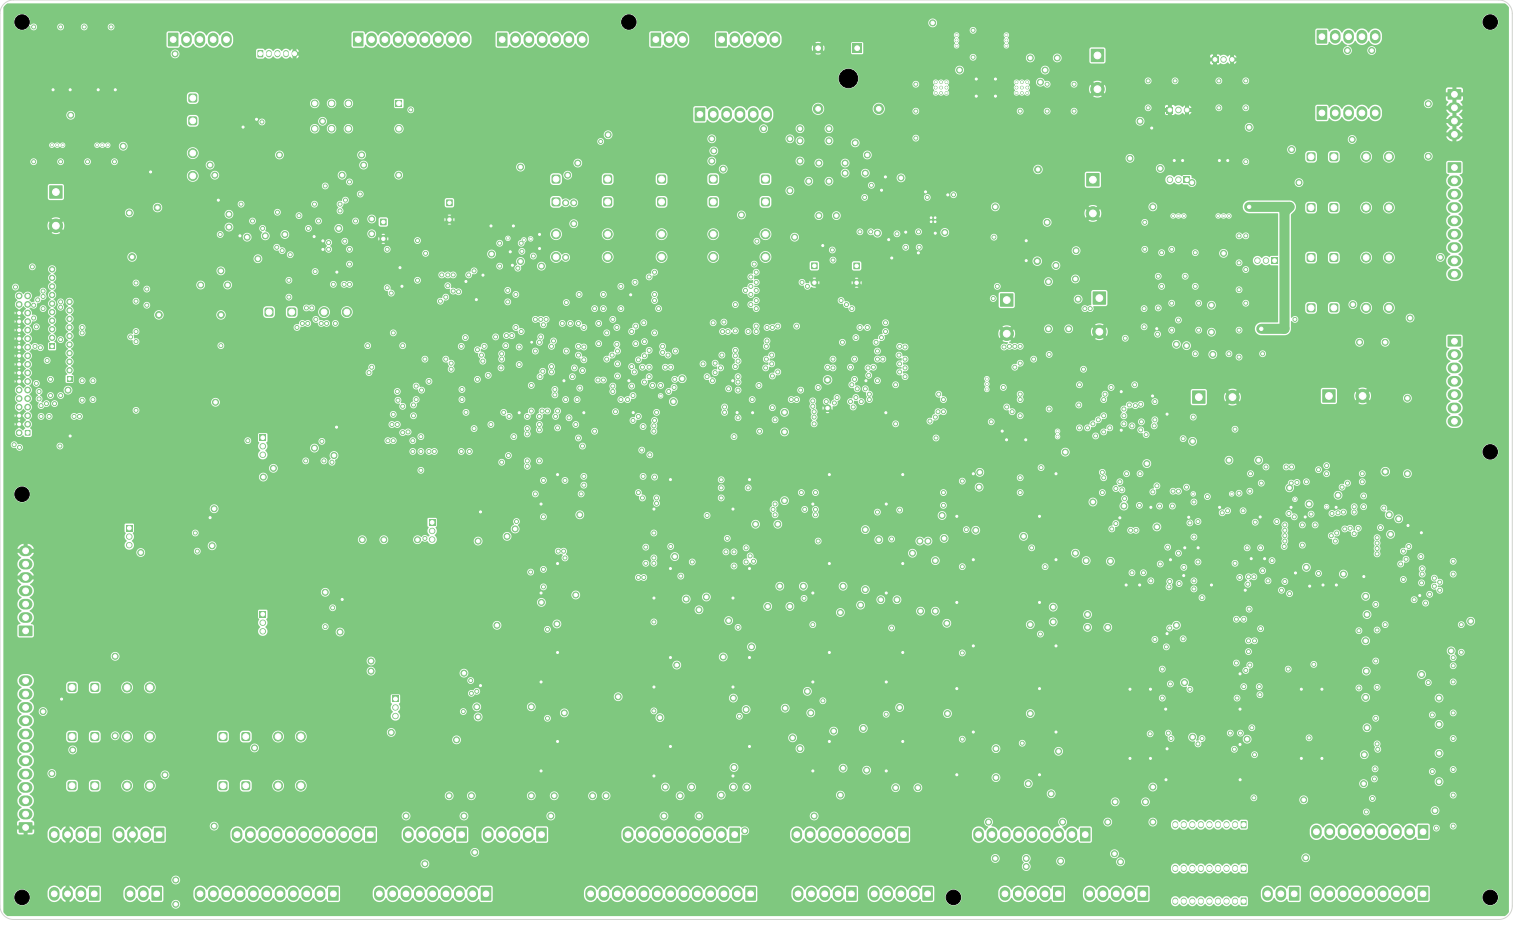
[picture p162: page 1]
