lolz0r/Williams-WPC-Power-Driver-Board-A-12697-3/output/release-candidate/assembly/inner-signal.pdf

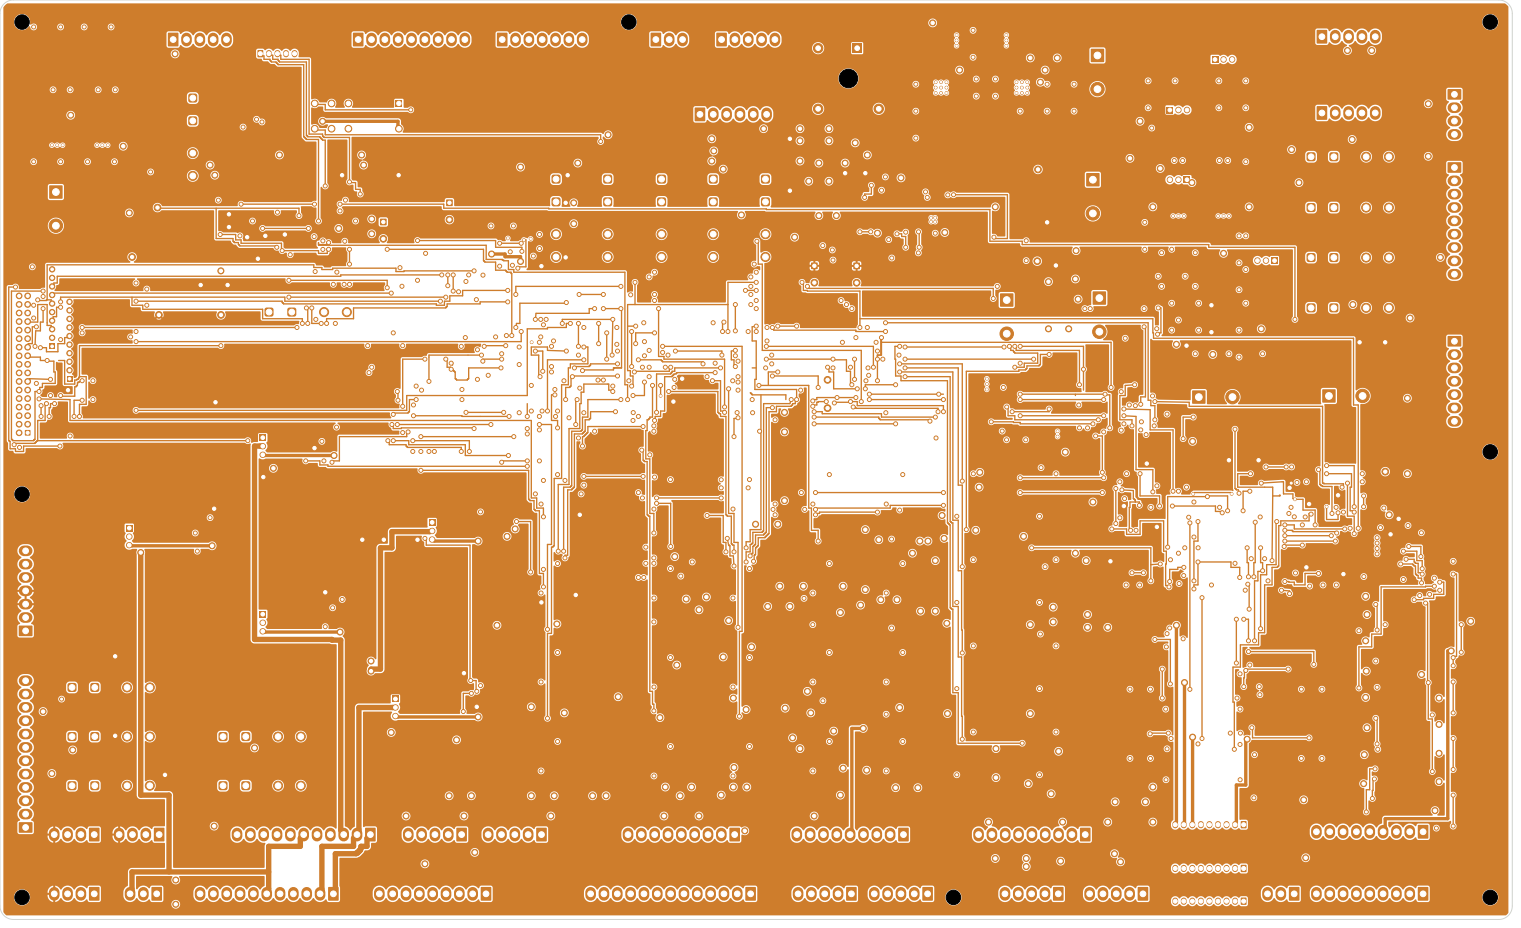
[picture p163: page 1]
