lolz0r/Williams-WPC-Power-Driver-Board-A-12697-3/output/release-candidate/assembly/top.pdf

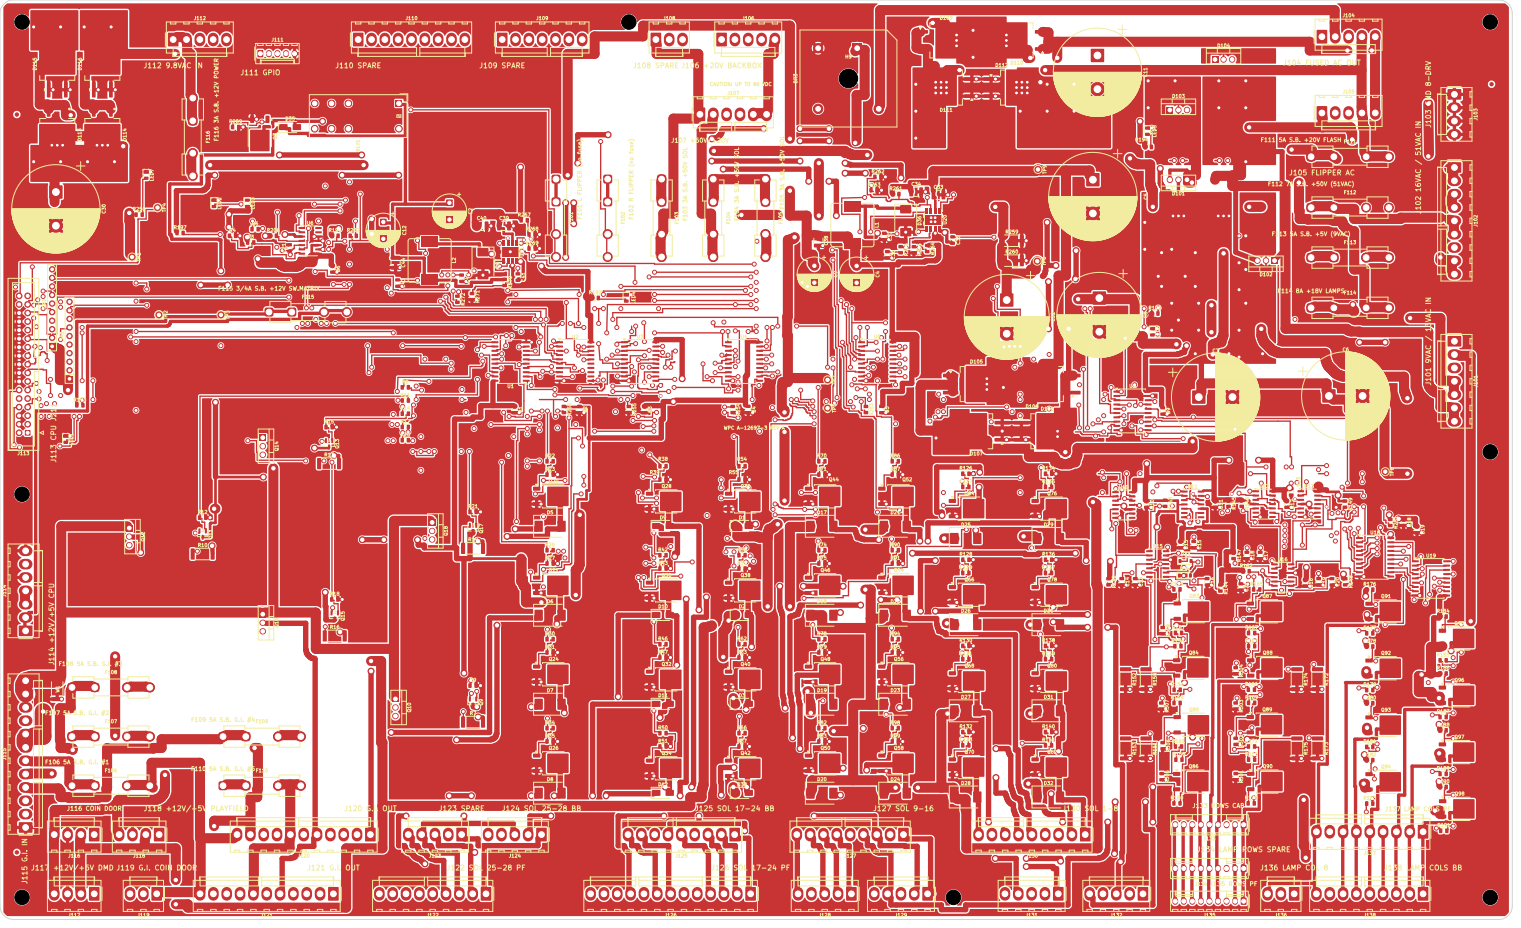
[picture p164: page 1]
