lolz0r/Williams-WPC-Power-Driver-Board-A-12697-3/output/verification/revision/vendor-buck/vendor_5v.cir

TPS54360 TI unencrypted transient model in actual U20 circuit
.include /Users/mc/Williams-WPC-Power-Driver-Board-A-12697-3-/.scratch/vendor-models/SLVMCT7/TPS54360_PSPICE_TRANS/TPS54360_TRANS.LIB
.include /Users/mc/Williams-WPC-Power-Driver-Board-A-12697-3-/tools/spice/models.lib
Vin vin 0 PWL(0 0 100u 8)
Rin vin vinf .02
Cin vinf 0 20u
XU boot comp en 0 sw rt vinf fb 0 TPS54360_TRANS
Ren1 vinf en 118k
Ren2 en 0 29.4k
Rrt rt 0 240k
Cboot boot sw 100n
Rfb1 vout fb 11.3k
Rfb2 fb 0 2.1k
Rc comp cc 33.2k
Cc cc 0 33n
Cp comp 0 470p
Dcatch 0 sw DB560C
L1 sw vout 10u
Cout1 vout c1 330u
Resr1 c1 0 .045
Cout2 vout c2 330u
Resr2 c2 0 .045
Cc3 vout 0 10u
Rload vout 0 1.7
.options reltol=.005 abstol=1u vntol=1m method=gear
.tran 100n 8m
.control
run
meas tran vout AVG v(vout) from=7m to=8m
meas tran peak MAX v(vout)
.endc
.end
